juanmrq95/ee149_104/ASLsensing/longFlex/save_sensordata/test 1.1/testAashykLetterF.txt

ÿr_side 0   m_tip: 0   m_b: 0   m_side: 0   i_tip: 0   i_side: 0   p_side: 0thumb: 4   index: 0   middle: 2   ring: 1   pinky: 2 X: 359.86  Y: 1.56  Z: 359.08
r_side 0   m_tip: 0   m_b: 0   m_side: 0   i_tip: 0   i_side: 0   p_side: 0thumb: 4   index: 0   middle: 2   ring: 2   pinky: 2 X: 359.80  Y: 2.21  Z: 356.90
r_side 0   m_tip: 0   m_b: 0   m_side: 0   i_tip: 0   i_side: 0   p_side: 0thumb: 4   index: 1   middle: 1   ring: 1   pinky: 2 X: 359.91  Y: 2.89  Z: 354.72
r_side 0   m_tip: 0   m_b: 0   m_side: 0   i_tip: 0   i_side: 0   p_side: 0thumb: 4   index: 0   middle: 2   ring: 2   pinky: 2 X: 359.77  Y: 3.84  Z: 352.84
r_side 0   m_tip: 0   m_b: 0   m_side: 0   i_tip: 0   i_side: 0   p_side: 0thumb: 5   index: 0   middle: 2   ring: 2   pinky: 2 X: 359.57  Y: 4.64  Z: 351.21
r_side 0   m_tip: 0   m_b: 0   m_side: 0   i_tip: 0   i_side: 0   p_side: 0thumb: 4   index: 1   middle: 2   ring: 1   pinky: 2 X: 359.48  Y: 5.23  Z: 349.58
r_side 0   m_tip: 0   m_b: 0   m_side: 0   i_tip: 0   i_side: 0   p_side: 0thumb: 4   index: 0   middle: 2   ring: 1   pinky: 2 X: 359.42  Y: 5.63  Z: 347.90
r_side 0   m_tip: 0   m_b: 0   m_side: 0   i_tip: 0   i_side: 0   p_side: 0thumb: 4   index: 0   middle: 2   ring: 1   pinky: 2 X: 359.13  Y: 6.56  Z: 346.26
r_side 0   m_tip: 0   m_b: 0   m_side: 0   i_tip: 0   i_side: 0   p_side: 0thumb: 5   index: 1   middle: 1   ring: 2   pinky: 2 X: 358.89  Y: 7.36  Z: 345.13
r_side 0   m_tip: 0   m_b: 0   m_side: 0   i_tip: 0   i_side: 0   p_side: 0thumb: 4   index: 0   middle: 2   ring: 1   pinky: 2 X: 358.83  Y: 7.89  Z: 343.63
r_side 0   m_tip: 0   m_b: 0   m_side: 0   i_tip: 0   i_side: 0   p_side: 0thumb: 5   index: 1   middle: 2   ring: 2   pinky: 2 X: 358.70  Y: 8.17  Z: 342.31
r_side 0   m_tip: 0   m_b: 0   m_side: 0   i_tip: 0   i_side: 0   p_side: 0thumb: 5   index: 1   middle: 2   ring: 1   pinky: 2 X: 358.71  Y: 8.30  Z: 341.29
r_side 0   m_tip: 0   m_b: 0   m_side: 0   i_tip: 0   i_side: 0   p_side: 0thumb: 4   index: 0   middle: 2   ring: 2   pinky: 2 X: 358.53  Y: 8.83  Z: 340.26
r_side 0   m_tip: 0   m_b: 0   m_side: 0   i_tip: 0   i_side: 0   p_side: 0thumb: 4   index: 0   middle: 2   ring: 1   pinky: 2 X: 358.38  Y: 9.08  Z: 339.26
r_side 0   m_tip: 0   m_b: 0   m_side: 0   i_tip: 0   i_side: 0   p_side: 0thumb: 4   index: 0   middle: 2   ring: 1   pinky: 1 X: 358.16  Y: 9.81  Z: 338.84
r_side 0   m_tip: 0   m_b: 0   m_side: 0   i_tip: 0   i_side: 0   p_side: 0thumb: 4   index: 1   middle: 2   ring: 1   pinky: 2 X: 357.87  Y: 10.62  Z: 338.17
r_side 0   m_tip: 0   m_b: 0   m_side: 0   i_tip: 0   i_side: 0   p_side: 0thumb: 4   index: 1   middle: 2   ring: 2   pinky: 2 X: 357.73  Y: 10.57  Z: 337.49
r_side 0   m_tip: 0   m_b: 0   m_side: 0   i_tip: 0   i_side: 0   p_side: 0thumb: 4   index: 0   middle: 2   ring: 1   pinky: 2 X: 357.51  Y: 10.94  Z: 337.09
r_side 0   m_tip: 0   m_b: 0   m_side: 0   i_tip: 0   i_side: 0   p_side: 0thumb: 5   index: 0   middle: 2   ring: 2   pinky: 2 X: 357.28  Y: 11.17  Z: 336.52
r_side 0   m_tip: 0   m_b: 0   m_side: 0   i_tip: 0   i_side: 0   p_side: 0thumb: 4   index: 0   middle: 2   ring: 2   pinky: 2 X: 357.27  Y: 11.25  Z: 335.93
r_side 0   m_tip: 0   m_b: 0   m_side: 0   i_tip: 0   i_side: 0   p_side: 0thumb: 4   index: 1   middle: 2   ring: 2   pinky: 2 X: 356.90  Y: 11.51  Z: 328.52
r_side 0   m_tip: 0   m_b: 0   m_side: 0   i_tip: 0   i_side: 0   p_side: 0thumb: 5   index: 1   middle: 2   ring: 2   pinky: 2 X: 355.02  Y: 19.53  Z: 329.30
r_side 0   m_tip: 0   m_b: 0   m_side: 0   i_tip: 0   i_side: 0   p_side: 0thumb: 4   index: 11   middle: 2   ring: 3   pinky: 2 X: 349.70  Y: 37.47  Z: 325.18
r_side 0   m_tip: 0   m_b: 0   m_side: 0   i_tip: 0   i_side: 0   p_side: 0thumb: 4   index: 15   middle: 3   ring: 3   pinky: 2 X: 342.33  Y: 48.81  Z: 319.32
r_side 0   m_tip: 0   m_b: 0   m_side: 0   i_tip: 0   i_side: 0   p_side: 0thumb: 5   index: 17   middle: 5   ring: 3   pinky: 2 X: 330.57  Y: 53.66  Z: 309.83
r_side 0   m_tip: 0   m_b: 0   m_side: 0   i_tip: 0   i_side: 0   p_side: 0thumb: 9   index: 17   middle: 6   ring: 3   pinky: 2 X: 324.71  Y: 56.98  Z: 305.13
r_side 0   m_tip: 0   m_b: 0   m_side: 0   i_tip: 0   i_side: 0   p_side: 0thumb: 12   index: 17   middle: 5   ring: 3   pinky: 1 X: 307.50  Y: 58.89  Z: 292.51
r_side 0   m_tip: 0   m_b: 0   m_side: 0   i_tip: 0   i_side: 0   p_side: 0thumb: 13   index: 17   middle: 3   ring: 2   pinky: 2 X: 304.84  Y: 59.09  Z: 291.02
r_side 0   m_tip: 0   m_b: 0   m_side: 0   i_tip: 0   i_side: 0   p_side: 0thumb: 13   index: 17   middle: 3   ring: 2   pinky: 1 X: 300.77  Y: 59.29  Z: 287.74
r_side 0   m_tip: 0   m_b: 0   m_side: 0   i_tip: 0   i_side: 0   p_side: 0thumb: 13   index: 17   middle: 3   ring: 2   pinky: 1 X: 296.96  Y: 59.40  Z: 285.31
r_side 0   m_tip: 0   m_b: 0   m_side: 0   i_tip: 0   i_side: 0   p_side: 0thumb: 13   index: 16   middle: 3   ring: 2   pinky: 1 X: 294.84  Y: 59.29  Z: 284.20
r_side 0   m_tip: 0   m_b: 0   m_side: 0   i_tip: 0   i_side: 0   p_side: 0thumb: 13   index: 16   middle: 3   ring: 2   pinky: 1 X: 297.70  Y: 60.33  Z: 287.13
r_side 0   m_tip: 0   m_b: 0   m_side: 0   i_tip: 0   i_side: 0   p_side: 0thumb: 13   index: 16   middle: 3   ring: 2   pinky: 1 X: 296.87  Y: 60.51  Z: 286.03
r_side 0   m_tip: 0   m_b: 0   m_side: 0   i_tip: 0   i_side: 0   p_side: 0thumb: 14   index: 16   middle: 2   ring: 2   pinky: 1 X: 298.05  Y: 60.01  Z: 287.22
r_side 0   m_tip: 0   m_b: 0   m_side: 0   i_tip: 0   i_side: 0   p_side: 0thumb: 13   index: 16   middle: 2   ring: 2   pinky: 1 X: 299.49  Y: 59.68  Z: 289.05
r_side 0   m_tip: 0   m_b: 0   m_side: 0   i_tip: 0   i_side: 0   p_side: 0thumb: 13   index: 16   middle: 3   ring: 2   pinky: 1 X: 300.21  Y: 59.00  Z: 289.37
r_side 0   m_tip: 0   m_b: 0   m_side: 0   i_tip: 0   i_side: 0   p_side: 0thumb: 13   index: 17   middle: 2   ring: 2   pinky: 1 X: 299.08  Y: 58.88  Z: 288.23
r_side 0   m_tip: 0   m_b: 0   m_side: 0   i_tip: 0   i_side: 0   p_side: 0thumb: 12   index: 15   middle: 2   ring: 2   pinky: 1 X: 298.16  Y: 58.42  Z: 287.07
r_side 0   m_tip: 0   m_b: 0   m_side: 0   i_tip: 1   i_side: 0   p_side: 0thumb: 12   index: 15   middle: 2   ring: 2   pinky: 1 X: 299.49  Y: 58.04  Z: 288.58
r_side 0   m_tip: 0   m_b: 0   m_side: 1   i_tip: 1   i_side: 0   p_side: 0thumb: 12   index: 15   middle: 2   ring: 3   pinky: 1 X: 300.17  Y: 56.76  Z: 289.16
r_side 0   m_tip: 0   m_b: 0   m_side: 1   i_tip: 1   i_side: 0   p_side: 0thumb: 12   index: 15   middle: 2   ring: 2   pinky: 1 X: 301.12  Y: 56.71  Z: 290.41
r_side 0   m_tip: 0   m_b: 0   m_side: 1   i_tip: 1   i_side: 0   p_side: 0thumb: 12   index: 15   middle: 2   ring: 3   pinky: 1 X: 300.59  Y: 56.21  Z: 289.94
r_side 0   m_tip: 0   m_b: 0   m_side: 1   i_tip: 1   i_side: 0   p_side: 0thumb: 12   index: 15   middle: 2   ring: 2   pinky: 1 X: 299.94  Y: 55.90  Z: 289.20
r_side 0   m_tip: 0   m_b: 0   m_side: 1   i_tip: 1   i_side: 0   p_side: 0thumb: 12   index: 15   middle: 2   ring: 2   pinky: 1 X: 299.15  Y: 55.63  Z: 288.76
r_side 0   m_tip: 0   m_b: 0   m_side: 1   i_tip: 1   i_side: 0   p_side: 0thumb: 12   index: 15   middle: 2   ring: 2   pinky: 1 X: 297.92  Y: 55.63  Z: 287.64
r_side 0   m_tip: 0   m_b: 0   m_side: 1   i_tip: 1   i_side: 0   p_side: 0thumb: 11   index: 15   middle: 2   ring: 2   pinky: 1 X: 298.07  Y: 54.77  Z: 287.32
r_side 0   m_tip: 0   m_b: 0   m_side: 1   i_tip: 1   i_side: 0   p_side: 0thumb: 12   index: 15   middle: 2   ring: 2   pinky: 1 X: 298.51  Y: 53.80  Z: 287.42
r_side 0   m_tip: 0   m_b: 0   m_side: 1   i_tip: 1   i_side: 0   p_side: 0thumb: 11   index: 15   middle: 2   ring: 2   pinky: 2 X: 298.68  Y: 53.05  Z: 287.82
r_side 0   m_tip: 0   m_b: 0   m_side: 1   i_tip: 1   i_side: 0   p_side: 0thumb: 12   index: 15   middle: 2   ring: 2   pinky: 1 X: 299.35  Y: 52.70  Z: 288.68
r_side 0   m_tip: 0   m_b: 0   m_side: 1   i_tip: 1   i_side: 0   p_side: 0thumb: 11   index: 15   middle: 2   ring: 2   pinky: 1 X: 298.26  Y: 52.58  Z: 287.90
r_side 0   m_tip: 0   m_b: 0   m_side: 1   i_tip: 1   i_side: 0   p_side: 0thumb: 12   index: 15   middle: 2   ring: 2   pinky: 1 X: 298.87  Y: 51.74  Z: 288.30
r_side 0   m_tip: 0   m_b: 0   m_side: 1   i_tip: 1   i_side: 0   p_side: 0thumb: 12   index: 15   middle: 2   ring: 2   pinky: 1 X: 298.92  Y: 51.02  Z: 288.29
r_side 0   m_tip: 0   m_b: 0   m_side: 1   i_tip: 1   i_side: 0   p_side: 0thumb: 11   index: 15   middle: 2   ring: 2   pinky: 1 X: 300.51  Y: 50.00  Z: 289.78
r_side 0   m_tip: 0   m_b: 0   m_side: 1   i_tip: 1   i_side: 0   p_side: 0thumb: 11   index: 14   middle: 2   ring: 2   pinky: 1 X: 299.64  Y: 49.93  Z: 289.33
r_side 0   m_tip: 0   m_b: 0   m_side: 1   i_tip: 1   i_side: 0   p_side: 0thumb: 11   index: 14   middle: 2   ring: 2   pinky: 2 X: 299.54  Y: 49.94  Z: 289.10
r_side 0   m_tip: 0   m_b: 0   m_side: 1   i_tip: 1   i_side: 0   p_side: 0thumb: 11   index: 14   middle: 2   ring: 2   pinky: 1 X: 299.70  Y: 49.47  Z: 289.38
r_side 0   m_tip: 0   m_b: 0   m_side: 1   i_tip: 1   i_side: 0   p_side: 0thumb: 12   index: 14   middle: 2   ring: 2   pinky: 1 X: 299.32  Y: 48.52  Z: 288.76
r_side 0   m_tip: 0   m_b: 0   m_side: 1   i_tip: 1   i_side: 0   p_side: 0thumb: 11   index: 14   middle: 2   ring: 2   pinky: 1 X: 300.05  Y: 47.78  Z: 289.49
r_side 0   m_tip: 0   m_b: 0   m_side: 1   i_tip: 1   i_side: 0   p_side: 0thumb: 11   index: 15   middle: 2   ring: 2   pinky: 1 X: 299.90  Y: 47.40  Z: 289.54
r_side 0   m_tip: 0   m_b: 0   m_side: 1   i_tip: 1   i_side: 0   p_side: 0thumb: 11   index: 15   middle: 2   ring: 2   pinky: 1 X: 298.75  Y: 47.26  Z: 288.29
r_side 0   m_tip: 0   m_b: 0   m_side: 1   i_tip: 1   i_side: 0   p_side: 0thumb: 11   index: 14   middle: 2   ring: 2   pinky: 1 X: 297.88  Y: 46.88  Z: 287.56
r_side 0   m_tip: 0   m_b: 0   m_side: 1   i_tip: 1   i_side: 0   p_side: 0thumb: 11   index: 12   middle: 2   ring: 2   pinky: 1 X: 297.51  Y: 46.70  Z: 287.17
r_side 0   m_tip: 0   m_b: 0   m_side: 1   i_tip: 1   i_side: 0   p_side: 0thumb: 11   index: 14   middle: 2   ring: 2   pinky: 1 X: 296.88  Y: 46.60  Z: 286.61
r_side 0   m_tip: 0   m_b: 0   m_side: 1   i_tip: 1   i_side: 0   p_side: 0thumb: 11   index: 14   middle: 2   ring: 2   pinky: 1 X: 295.59  Y: 46.58  Z: 285.90
r_side 0   m_tip: 0   m_b: 0   m_side: 1   i_tip: 1   i_side: 0   p_side: 0thumb: 11   index: 14   middle: 2   ring: 2   pinky: 1 X: 296.79  Y: 46.54  Z: 286.98
r_side 0   m_tip: 0   m_b: 0   m_side: 1   i_tip: 1   i_side: 0   p_side: 0thumb: 11   index: 14   middle: 2   ring: 2   pinky: 1 X: 297.42  Y: 46.25  Z: 287.56
r_side 0   m_tip: 0   m_b: 0   m_side: 1   i_tip: 1   i_side: 0   p_side: 0thumb: 11   index: 14   middle: 2   ring: 2   pinky: 1 X: 297.86  Y: 45.92  Z: 287.97
r_side 0   m_tip: 0   m_b: 0   m_side: 1   i_tip: 1   i_side: 0   p_side: 0thumb: 11   index: 14   middle: 2   ring: 2   pinky: 1 X: 298.05  Y: 45.55  Z: 288.15
r_side 0   m_tip: 0   m_b: 0   m_side: 1   i_tip: 1   i_side: 0   p_side: 0thumb: 11   index: 14   middle: 2   ring: 2   pinky: 1 X: 298.62  Y: 44.94  Z: 288.62
