juanmrq95/ee149_104/ASLsensing/longFlex/save_sensordata/test 1.1/testAashykLetterG.txt

ôr_side 0   m_tip: 0   m_b: 0   m_side: 0   i_tip: 0   i_side: 0   p_side: 0thumb: 5   index: 1   middle: 2   ring: 2   pinky: 2 X: 359.86  Y: 1.04  Z: 359.47
r_side 0   m_tip: 0   m_b: 0   m_side: 0   i_tip: 0   i_side: 0   p_side: 0thumb: 4   index: 1   middle: 3   ring: 2   pinky: 2 X: 359.98  Y: 2.26  Z: 356.93
r_side 0   m_tip: 0   m_b: 0   m_side: 0   i_tip: 0   i_side: 0   p_side: 0thumb: 6   index: 1   middle: 2   ring: 2   pinky: 2 X: 359.90  Y: 3.79  Z: 354.77
r_side 0   m_tip: 0   m_b: 0   m_side: 0   i_tip: 0   i_side: 0   p_side: 0thumb: 5   index: 1   middle: 2   ring: 2   pinky: 2 X: 359.68  Y: 5.32  Z: 352.94
r_side 0   m_tip: 0   m_b: 0   m_side: 0   i_tip: 0   i_side: 0   p_side: 0thumb: 5   index: 1   middle: 2   ring: 2   pinky: 2 X: 359.40  Y: 6.60  Z: 351.04
r_side 0   m_tip: 0   m_b: 0   m_side: 0   i_tip: 0   i_side: 0   p_side: 0thumb: 5   index: 1   middle: 3   ring: 2   pinky: 2 X: 359.09  Y: 7.69  Z: 349.23
r_side 0   m_tip: 0   m_b: 0   m_side: 0   i_tip: 0   i_side: 0   p_side: 0thumb: 5   index: 1   middle: 2   ring: 2   pinky: 2 X: 358.81  Y: 9.04  Z: 347.66
r_side 0   m_tip: 0   m_b: 0   m_side: 0   i_tip: 0   i_side: 0   p_side: 0thumb: 5   index: 1   middle: 2   ring: 2   pinky: 2 X: 358.50  Y: 10.26  Z: 345.89
r_side 0   m_tip: 0   m_b: 0   m_side: 0   i_tip: 0   i_side: 0   p_side: 0thumb: 5   index: 1   middle: 2   ring: 2   pinky: 2 X: 358.17  Y: 11.07  Z: 344.23
r_side 0   m_tip: 0   m_b: 0   m_side: 0   i_tip: 0   i_side: 0   p_side: 0thumb: 5   index: 1   middle: 2   ring: 2   pinky: 2 X: 357.83  Y: 12.02  Z: 342.65
r_side 0   m_tip: 0   m_b: 0   m_side: 0   i_tip: 0   i_side: 0   p_side: 0thumb: 5   index: 1   middle: 3   ring: 2   pinky: 2 X: 357.34  Y: 12.48  Z: 341.30
r_side 0   m_tip: 0   m_b: 0   m_side: 0   i_tip: 0   i_side: 0   p_side: 0thumb: 4   index: 1   middle: 2   ring: 2   pinky: 2 X: 357.13  Y: 13.51  Z: 339.95
r_side 0   m_tip: 0   m_b: 0   m_side: 0   i_tip: 0   i_side: 0   p_side: 0thumb: 5   index: 1   middle: 2   ring: 2   pinky: 2 X: 356.93  Y: 13.75  Z: 338.81
r_side 0   m_tip: 0   m_b: 0   m_side: 0   i_tip: 0   i_side: 0   p_side: 0thumb: 5   index: 1   middle: 2   ring: 2   pinky: 2 X: 354.07  Y: 15.34  Z: 328.92
r_side 0   m_tip: 0   m_b: 0   m_side: 0   i_tip: 0   i_side: 0   p_side: 0thumb: 5   index: 1   middle: 3   ring: 3   pinky: 2 X: 340.19  Y: 18.18  Z: 311.25
r_side 0   m_tip: 0   m_b: 0   m_side: 0   i_tip: 0   i_side: 0   p_side: 0thumb: 4   index: 2   middle: 10   ring: 10   pinky: 3 X: 324.12  Y: 7.15  Z: 287.70
r_side 0   m_tip: 0   m_b: 0   m_side: 0   i_tip: 0   i_side: 0   p_side: 0thumb: 4   index: 2   middle: 16   ring: 19   pinky: 10 X: 326.61  Y: 352.52  Z: 270.03
r_side 0   m_tip: 0   m_b: 0   m_side: 0   i_tip: 0   i_side: 0   p_side: 0thumb: 4   index: 3   middle: 21   ring: 23   pinky: 20 X: 334.37  Y: 346.06  Z: 267.57
r_side 0   m_tip: 0   m_b: 0   m_side: 0   i_tip: 0   i_side: 0   p_side: 0thumb: 4   index: 9   middle: 20   ring: 22   pinky: 20 X: 336.39  Y: 333.75  Z: 259.16
r_side 0   m_tip: 1   m_b: 0   m_side: 0   i_tip: 0   i_side: 0   p_side: 0thumb: 5   index: 4   middle: 20   ring: 22   pinky: 20 X: 340.89  Y: 325.34  Z: 253.91
r_side 0   m_tip: 1   m_b: 0   m_side: 0   i_tip: 0   i_side: 0   p_side: 0thumb: 5   index: 3   middle: 20   ring: 22   pinky: 19 X: 352.90  Y: 323.82  Z: 236.03
r_side 0   m_tip: 1   m_b: 0   m_side: 0   i_tip: 0   i_side: 0   p_side: 0thumb: 5   index: 2   middle: 20   ring: 21   pinky: 19 X: 353.22  Y: 323.20  Z: 239.87
r_side 0   m_tip: 1   m_b: 0   m_side: 0   i_tip: 0   i_side: 0   p_side: 0thumb: 5   index: 2   middle: 19   ring: 21   pinky: 19 X: 351.07  Y: 327.64  Z: 246.00
r_side 0   m_tip: 1   m_b: 0   m_side: 0   i_tip: 0   i_side: 0   p_side: 0thumb: 5   index: 2   middle: 19   ring: 21   pinky: 18 X: 349.36  Y: 330.85  Z: 250.28
r_side 0   m_tip: 1   m_b: 0   m_side: 0   i_tip: 0   i_side: 0   p_side: 0thumb: 5   index: 2   middle: 19   ring: 21   pinky: 18 X: 351.55  Y: 330.85  Z: 248.05
r_side 0   m_tip: 1   m_b: 0   m_side: 0   i_tip: 0   i_side: 0   p_side: 0thumb: 4   index: 1   middle: 19   ring: 21   pinky: 18 X: 352.31  Y: 329.45  Z: 247.53
r_side 0   m_tip: 1   m_b: 0   m_side: 0   i_tip: 0   i_side: 0   p_side: 0thumb: 4   index: 1   middle: 19   ring: 21   pinky: 18 X: 353.84  Y: 329.83  Z: 244.71
r_side 0   m_tip: 1   m_b: 0   m_side: 0   i_tip: 0   i_side: 0   p_side: 0thumb: 4   index: 1   middle: 18   ring: 21   pinky: 18 X: 353.63  Y: 328.74  Z: 246.48
r_side 0   m_tip: 1   m_b: 0   m_side: 0   i_tip: 0   i_side: 0   p_side: 0thumb: 4   index: 1   middle: 19   ring: 20   pinky: 18 X: 353.61  Y: 329.88  Z: 245.12
r_side 0   m_tip: 1   m_b: 0   m_side: 0   i_tip: 0   i_side: 0   p_side: 0thumb: 5   index: 0   middle: 18   ring: 20   pinky: 18 X: 353.72  Y: 329.08  Z: 246.32
r_side 0   m_tip: 1   m_b: 0   m_side: 0   i_tip: 0   i_side: 0   p_side: 0thumb: 4   index: 1   middle: 18   ring: 20   pinky: 18 X: 353.32  Y: 329.97  Z: 246.20
r_side 0   m_tip: 1   m_b: 0   m_side: 0   i_tip: 0   i_side: 0   p_side: 0thumb: 4   index: 1   middle: 18   ring: 20   pinky: 18 X: 353.13  Y: 328.50  Z: 247.85
r_side 0   m_tip: 1   m_b: 0   m_side: 0   i_tip: 0   i_side: 0   p_side: 0thumb: 4   index: 1   middle: 18   ring: 19   pinky: 18 X: 353.42  Y: 329.00  Z: 247.76
r_side 0   m_tip: 1   m_b: 0   m_side: 0   i_tip: 0   i_side: 0   p_side: 0thumb: 4   index: 1   middle: 18   ring: 20   pinky: 18 X: 353.89  Y: 328.97  Z: 247.76
r_side 0   m_tip: 1   m_b: 0   m_side: 0   i_tip: 0   i_side: 0   p_side: 0thumb: 4   index: 1   middle: 18   ring: 20   pinky: 18 X: 353.51  Y: 329.65  Z: 247.14
r_side 0   m_tip: 1   m_b: 0   m_side: 0   i_tip: 0   i_side: 0   p_side: 0thumb: 4   index: 1   middle: 18   ring: 20   pinky: 18 X: 353.29  Y: 328.72  Z: 248.12
r_side 0   m_tip: 1   m_b: 0   m_side: 0   i_tip: 0   i_side: 0   p_side: 0thumb: 4   index: 1   middle: 18   ring: 19   pinky: 18 X: 353.93  Y: 327.08  Z: 247.85
r_side 0   m_tip: 1   m_b: 0   m_side: 0   i_tip: 0   i_side: 0   p_side: 0thumb: 4   index: 1   middle: 18   ring: 20   pinky: 18 X: 353.44  Y: 326.59  Z: 249.26
r_side 0   m_tip: 1   m_b: 0   m_side: 0   i_tip: 0   i_side: 0   p_side: 0thumb: 4   index: 1   middle: 18   ring: 20   pinky: 18 X: 352.77  Y: 326.28  Z: 249.98
r_side 0   m_tip: 1   m_b: 0   m_side: 0   i_tip: 0   i_side: 0   p_side: 0thumb: 4   index: 1   middle: 18   ring: 20   pinky: 18 X: 352.56  Y: 326.93  Z: 249.52
r_side 0   m_tip: 1   m_b: 0   m_side: 0   i_tip: 0   i_side: 0   p_side: 0thumb: 3   index: 1   middle: 18   ring: 20   pinky: 18 X: 352.37  Y: 327.42  Z: 249.82
r_side 0   m_tip: 1   m_b: 0   m_side: 0   i_tip: 0   i_side: 0   p_side: 0thumb: 3   index: 1   middle: 18   ring: 20   pinky: 18 X: 352.23  Y: 327.50  Z: 250.27
r_side 0   m_tip: 1   m_b: 0   m_side: 0   i_tip: 0   i_side: 0   p_side: 0thumb: 3   index: 1   middle: 18   ring: 19   pinky: 18 X: 351.75  Y: 327.09  Z: 251.46
r_side 0   m_tip: 1   m_b: 0   m_side: 0   i_tip: 0   i_side: 0   p_side: 0thumb: 4   index: 1   middle: 18   ring: 20   pinky: 18 X: 351.92  Y: 327.97  Z: 250.81
r_side 0   m_tip: 1   m_b: 0   m_side: 0   i_tip: 0   i_side: 0   p_side: 0thumb: 3   index: 1   middle: 18   ring: 19   pinky: 17 X: 351.40  Y: 328.25  Z: 251.43
r_side 0   m_tip: 1   m_b: 0   m_side: 0   i_tip: 0   i_side: 0   p_side: 0thumb: 4   index: 1   middle: 18   ring: 20   pinky: 17 X: 351.45  Y: 327.87  Z: 251.77
r_side 0   m_tip: 1   m_b: 0   m_side: 0   i_tip: 0   i_side: 0   p_side: 0thumb: 4   index: 1   middle: 18   ring: 19   pinky: 17 X: 351.03  Y: 330.11  Z: 250.76
r_side 0   m_tip: 1   m_b: 0   m_side: 0   i_tip: 0   i_side: 0   p_side: 0thumb: 4   index: 1   middle: 18   ring: 19   pinky: 17 X: 351.12  Y: 325.59  Z: 252.97
r_side 0   m_tip: 1   m_b: 0   m_side: 0   i_tip: 0   i_side: 0   p_side: 0thumb: 3   index: 1   middle: 17   ring: 19   pinky: 17 X: 350.68  Y: 327.83  Z: 251.43
r_side 0   m_tip: 1   m_b: 0   m_side: 0   i_tip: 0   i_side: 0   p_side: 0thumb: 3   index: 1   middle: 18   ring: 19   pinky: 17 X: 350.75  Y: 326.18  Z: 252.53
r_side 0   m_tip: 1   m_b: 0   m_side: 0   i_tip: 0   i_side: 0   p_side: 0thumb: 3   index: 1   middle: 18   ring: 19   pinky: 18 X: 350.50  Y: 328.37  Z: 251.83
r_side 0   m_tip: 1   m_b: 0   m_side: 0   i_tip: 0   i_side: 0   p_side: 0thumb: 3   index: 1   middle: 18   ring: 19   pinky: 17 X: 350.89  Y: 327.90  Z: 252.03
r_side 0   m_tip: 1   m_b: 0   m_side: 0   i_tip: 0   i_side: 0   p_side: 0thumb: 4   index: 1   middle: 18   ring: 19   pinky: 17 X: 351.32  Y: 328.90  Z: 251.54
r_side 0   m_tip: 1   m_b: 0   m_side: 0   i_tip: 0   i_side: 0   p_side: 0thumb: 4   index: 2   middle: 18   ring: 19   pinky: 18 X: 350.45  Y: 329.97  Z: 251.80
r_side 0   m_tip: 1   m_b: 0   m_side: 0   i_tip: 0   i_side: 0   p_side: 0thumb: 3   index: 1   middle: 18   ring: 19   pinky: 17 X: 349.84  Y: 329.50  Z: 252.70
r_side 0   m_tip: 1   m_b: 0   m_side: 0   i_tip: 0   i_side: 0   p_side: 0thumb: 3   index: 1   middle: 18   ring: 19   pinky: 17 X: 349.80  Y: 329.93  Z: 252.40
r_side 0   m_tip: 1   m_b: 0   m_side: 0   i_tip: 0   i_side: 0   p_side: 0thumb: 3   index: 1   middle: 17   ring: 19   pinky: 17 X: 350.59  Y: 331.42  Z: 251.13
r_side 0   m_tip: 1   m_b: 0   m_side: 0   i_tip: 0   i_side: 0   p_side: 0thumb: 3   index: 1   middle: 18   ring: 19   pinky: 17 X: 350.34  Y: 331.67  Z: 251.18
r_side 0   m_tip: 1   m_b: 0   m_side: 0   i_tip: 0   i_side: 0   p_side: 0thumb: 3   index: 1   middle: 17   ring: 19   pinky: 17 X: 350.53  Y: 331.07  Z: 251.28
r_side 0   m_tip: 1   m_b: 0   m_side: 0   i_tip: 0   i_side: 0   p_side: 0thumb: 3   index: 1   middle: 17   ring: 19   pinky: 17 X: 349.86  Y: 331.18  Z: 251.82
r_side 0   m_tip: 1   m_b: 0   m_side: 0   i_tip: 0   i_side: 0   p_side: 0thumb: 3   index: 1   middle: 17   ring: 19   pinky: 17 X: 350.06  Y: 331.67  Z: 252.02
r_side 0   m_tip: 1   m_b: 0   m_side: 0   i_tip: 0   i_side: 0   p_side: 0thumb: 3   index: 1   middle: 17   ring: 19   pinky: 17 X: 350.19  Y: 331.96  Z: 252.10
