juanmrq95/ee149_104/ASLsensing/longFlex/save_sensordata/test 1.1/testAashykLetterH.txt

r_side 0   m_tip: 0   m_b: 0   m_side: 0   i_tip: 0   i_side: 0   p_side: 0thumb: 5   index: 1   middle: 2   ring: 2   pinky: 1 X: 359.61  Y: 0.91  Z: 359.87
r_side 0   m_tip: 0   m_b: 0   m_side: 0   i_tip: 0   i_side: 0   p_side: 0thumb: 5   index: 0   middle: 2   ring: 2   pinky: 1 X: 359.52  Y: 2.20  Z: 357.54
r_side 0   m_tip: 0   m_b: 0   m_side: 0   i_tip: 0   i_side: 0   p_side: 0thumb: 5   index: 0   middle: 2   ring: 2   pinky: 1 X: 359.45  Y: 3.42  Z: 355.15
r_side 0   m_tip: 0   m_b: 0   m_side: 0   i_tip: 0   i_side: 0   p_side: 0thumb: 5   index: 0   middle: 2   ring: 2   pinky: 1 X: 359.31  Y: 4.42  Z: 353.01
r_side 0   m_tip: 0   m_b: 0   m_side: 0   i_tip: 0   i_side: 0   p_side: 0thumb: 5   index: 0   middle: 2   ring: 2   pinky: 1 X: 359.24  Y: 5.20  Z: 350.74
r_side 0   m_tip: 0   m_b: 0   m_side: 0   i_tip: 0   i_side: 0   p_side: 0thumb: 5   index: 0   middle: 2   ring: 2   pinky: 1 X: 359.08  Y: 5.83  Z: 348.63
r_side 0   m_tip: 0   m_b: 0   m_side: 0   i_tip: 0   i_side: 0   p_side: 0thumb: 5   index: 0   middle: 1   ring: 2   pinky: 1 X: 358.90  Y: 6.77  Z: 346.83
r_side 0   m_tip: 0   m_b: 0   m_side: 0   i_tip: 0   i_side: 0   p_side: 0thumb: 5   index: 0   middle: 2   ring: 2   pinky: 2 X: 358.75  Y: 7.52  Z: 345.24
r_side 0   m_tip: 0   m_b: 0   m_side: 0   i_tip: 0   i_side: 0   p_side: 0thumb: 5   index: 0   middle: 2   ring: 2   pinky: 1 X: 358.59  Y: 8.00  Z: 343.64
r_side 0   m_tip: 0   m_b: 0   m_side: 0   i_tip: 0   i_side: 0   p_side: 0thumb: 5   index: 0   middle: 1   ring: 2   pinky: 1 X: 358.32  Y: 8.89  Z: 342.03
r_side 0   m_tip: 0   m_b: 0   m_side: 0   i_tip: 0   i_side: 0   p_side: 0thumb: 5   index: 0   middle: 2   ring: 2   pinky: 1 X: 358.12  Y: 9.58  Z: 340.49
r_side 0   m_tip: 0   m_b: 0   m_side: 0   i_tip: 0   i_side: 0   p_side: 0thumb: 5   index: 0   middle: 2   ring: 2   pinky: 1 X: 357.85  Y: 10.39  Z: 339.44
r_side 0   m_tip: 0   m_b: 0   m_side: 0   i_tip: 0   i_side: 0   p_side: 0thumb: 5   index: 0   middle: 2   ring: 2   pinky: 1 X: 357.70  Y: 10.68  Z: 338.24
r_side 0   m_tip: 0   m_b: 0   m_side: 0   i_tip: 0   i_side: 0   p_side: 0thumb: 5   index: 0   middle: 2   ring: 2   pinky: 1 X: 357.42  Y: 11.09  Z: 336.91
r_side 0   m_tip: 0   m_b: 0   m_side: 0   i_tip: 0   i_side: 0   p_side: 0thumb: 5   index: 0   middle: 2   ring: 2   pinky: 1 X: 357.15  Y: 11.62  Z: 335.82
r_side 0   m_tip: 0   m_b: 0   m_side: 0   i_tip: 0   i_side: 0   p_side: 0thumb: 5   index: 1   middle: 2   ring: 2   pinky: 1 X: 356.95  Y: 12.16  Z: 335.06
r_side 0   m_tip: 0   m_b: 0   m_side: 0   i_tip: 0   i_side: 0   p_side: 0thumb: 6   index: 0   middle: 2   ring: 3   pinky: 1 X: 356.69  Y: 12.51  Z: 334.23
r_side 0   m_tip: 0   m_b: 0   m_side: 0   i_tip: 0   i_side: 0   p_side: 0thumb: 5   index: 0   middle: 2   ring: 2   pinky: 1 X: 356.33  Y: 12.72  Z: 333.30
r_side 0   m_tip: 0   m_b: 0   m_side: 0   i_tip: 0   i_side: 0   p_side: 0thumb: 5   index: 0   middle: 2   ring: 2   pinky: 1 X: 353.48  Y: 12.53  Z: 327.00
r_side 0   m_tip: 0   m_b: 0   m_side: 0   i_tip: 0   i_side: 0   p_side: 0thumb: 5   index: 0   middle: 2   ring: 2   pinky: 2 X: 351.48  Y: 16.66  Z: 324.09
r_side 0   m_tip: 0   m_b: 0   m_side: 0   i_tip: 0   i_side: 0   p_side: 0thumb: 5   index: 0   middle: 2   ring: 2   pinky: 2 X: 337.60  Y: 8.10  Z: 293.87
r_side 0   m_tip: 0   m_b: 0   m_side: 0   i_tip: 0   i_side: 0   p_side: 0thumb: 4   index: 0   middle: 2   ring: 19   pinky: 13 X: 330.20  Y: 358.47  Z: 283.63
r_side 0   m_tip: 0   m_b: 0   m_side: 0   i_tip: 0   i_side: 0   p_side: 0thumb: 6   index: 1   middle: 2   ring: 21   pinky: 17 X: 326.41  Y: 350.17  Z: 278.54
r_side 0   m_tip: 0   m_b: 0   m_side: 0   i_tip: 0   i_side: 0   p_side: 0thumb: 5   index: 1   middle: 2   ring: 20   pinky: 17 X: 331.76  Y: 335.70  Z: 258.45
r_side 1   m_tip: 0   m_b: 0   m_side: 0   i_tip: 0   i_side: 0   p_side: 0thumb: 11   index: 0   middle: 2   ring: 20   pinky: 17 X: 339.12  Y: 324.61  Z: 245.85
r_side 1   m_tip: 0   m_b: 0   m_side: 0   i_tip: 0   i_side: 0   p_side: 0thumb: 12   index: 0   middle: 2   ring: 20   pinky: 17 X: 351.06  Y: 316.14  Z: 234.50
r_side 1   m_tip: 0   m_b: 0   m_side: 0   i_tip: 0   i_side: 0   p_side: 0thumb: 13   index: 0   middle: 2   ring: 20   pinky: 16 X: 354.17  Y: 311.24  Z: 233.86
r_side 1   m_tip: 0   m_b: 0   m_side: 0   i_tip: 0   i_side: 0   p_side: 0thumb: 13   index: 0   middle: 2   ring: 19   pinky: 16 X: 357.57  Y: 309.67  Z: 229.68
r_side 1   m_tip: 0   m_b: 0   m_side: 0   i_tip: 0   i_side: 0   p_side: 0thumb: 12   index: 0   middle: 2   ring: 20   pinky: 16 X: 0.75  Y: 307.02  Z: 227.85
r_side 1   m_tip: 0   m_b: 0   m_side: 0   i_tip: 0   i_side: 0   p_side: 0thumb: 13   index: 0   middle: 2   ring: 19   pinky: 16 X: 3.27  Y: 304.75  Z: 224.75
r_side 1   m_tip: 0   m_b: 0   m_side: 0   i_tip: 0   i_side: 0   p_side: 0thumb: 13   index: 0   middle: 2   ring: 19   pinky: 16 X: 3.76  Y: 303.31  Z: 226.28
r_side 1   m_tip: 0   m_b: 0   m_side: 0   i_tip: 0   i_side: 0   p_side: 0thumb: 13   index: 0   middle: 2   ring: 19   pinky: 16 X: 4.95  Y: 302.52  Z: 227.68
r_side 1   m_tip: 0   m_b: 0   m_side: 0   i_tip: 0   i_side: 0   p_side: 0thumb: 13   index: 0   middle: 2   ring: 19   pinky: 15 X: 9.36  Y: 303.10  Z: 224.10
r_side 1   m_tip: 0   m_b: 0   m_side: 0   i_tip: 0   i_side: 0   p_side: 0thumb: 13   index: 0   middle: 2   ring: 18   pinky: 15 X: 9.58  Y: 302.12  Z: 226.31
r_side 1   m_tip: 0   m_b: 0   m_side: 0   i_tip: 0   i_side: 0   p_side: 0thumb: 13   index: 0   middle: 1   ring: 18   pinky: 15 X: 7.73  Y: 303.27  Z: 230.31
r_side 1   m_tip: 0   m_b: 0   m_side: 0   i_tip: 0   i_side: 0   p_side: 0thumb: 13   index: 0   middle: 2   ring: 18   pinky: 15 X: 8.31  Y: 303.31  Z: 230.46
r_side 1   m_tip: 0   m_b: 0   m_side: 0   i_tip: 0   i_side: 0   p_side: 0thumb: 13   index: 0   middle: 2   ring: 18   pinky: 15 X: 8.67  Y: 303.21  Z: 231.11
r_side 1   m_tip: 0   m_b: 0   m_side: 0   i_tip: 0   i_side: 0   p_side: 0thumb: 13   index: 0   middle: 2   ring: 18   pinky: 15 X: 8.46  Y: 303.59  Z: 231.74
r_side 1   m_tip: 0   m_b: 0   m_side: 0   i_tip: 0   i_side: 0   p_side: 0thumb: 13   index: 0   middle: 2   ring: 18   pinky: 15 X: 8.98  Y: 302.91  Z: 232.03
r_side 1   m_tip: 0   m_b: 0   m_side: 0   i_tip: 0   i_side: 0   p_side: 0thumb: 12   index: 0   middle: 2   ring: 18   pinky: 15 X: 8.52  Y: 303.66  Z: 232.65
r_side 1   m_tip: 0   m_b: 0   m_side: 0   i_tip: 0   i_side: 0   p_side: 0thumb: 13   index: 0   middle: 1   ring: 18   pinky: 15 X: 7.68  Y: 304.45  Z: 234.66
r_side 1   m_tip: 0   m_b: 0   m_side: 0   i_tip: 0   i_side: 0   p_side: 0thumb: 13   index: 0   middle: 2   ring: 18   pinky: 15 X: 8.40  Y: 304.49  Z: 234.31
r_side 1   m_tip: 0   m_b: 0   m_side: 0   i_tip: 0   i_side: 0   p_side: 0thumb: 13   index: 0   middle: 2   ring: 18   pinky: 15 X: 9.61  Y: 303.95  Z: 233.01
r_side 1   m_tip: 0   m_b: 0   m_side: 0   i_tip: 0   i_side: 0   p_side: 0thumb: 13   index: 0   middle: 2   ring: 19   pinky: 15 X: 10.67  Y: 303.90  Z: 232.21
r_side 1   m_tip: 0   m_b: 0   m_side: 0   i_tip: 0   i_side: 0   p_side: 0thumb: 13   index: 0   middle: 1   ring: 18   pinky: 15 X: 12.61  Y: 302.40  Z: 230.62
r_side 1   m_tip: 0   m_b: 0   m_side: 0   i_tip: 0   i_side: 0   p_side: 0thumb: 13   index: 0   middle: 1   ring: 18   pinky: 15 X: 13.66  Y: 302.94  Z: 229.32
r_side 1   m_tip: 0   m_b: 0   m_side: 0   i_tip: 0   i_side: 0   p_side: 0thumb: 12   index: 0   middle: 1   ring: 18   pinky: 15 X: 12.77  Y: 303.30  Z: 230.86
r_side 1   m_tip: 0   m_b: 0   m_side: 0   i_tip: 0   i_side: 0   p_side: 0thumb: 12   index: 0   middle: 1   ring: 18   pinky: 15 X: 12.94  Y: 303.14  Z: 231.32
r_side 1   m_tip: 0   m_b: 0   m_side: 0   i_tip: 0   i_side: 0   p_side: 0thumb: 13   index: 0   middle: 1   ring: 18   pinky: 15 X: 13.95  Y: 302.54  Z: 230.57
r_side 1   m_tip: 0   m_b: 0   m_side: 0   i_tip: 0   i_side: 0   p_side: 0thumb: 13   index: 0   middle: 2   ring: 17   pinky: 15 X: 17.71  Y: 301.47  Z: 227.56
r_side 1   m_tip: 0   m_b: 0   m_side: 0   i_tip: 0   i_side: 0   p_side: 0thumb: 13   index: 0   middle: 1   ring: 18   pinky: 15 X: 17.03  Y: 301.64  Z: 228.42
r_side 1   m_tip: 0   m_b: 0   m_side: 0   i_tip: 0   i_side: 0   p_side: 0thumb: 13   index: 0   middle: 1   ring: 18   pinky: 15 X: 16.25  Y: 302.06  Z: 229.40
r_side 1   m_tip: 0   m_b: 0   m_side: 0   i_tip: 0   i_side: 0   p_side: 0thumb: 13   index: 0   middle: 1   ring: 17   pinky: 15 X: 15.05  Y: 301.81  Z: 231.51
r_side 1   m_tip: 0   m_b: 0   m_side: 0   i_tip: 0   i_side: 0   p_side: 0thumb: 13   index: 0   middle: 2   ring: 18   pinky: 15 X: 15.76  Y: 301.42  Z: 231.24
r_side 1   m_tip: 0   m_b: 0   m_side: 0   i_tip: 0   i_side: 0   p_side: 0thumb: 12   index: 0   middle: 2   ring: 17   pinky: 15 X: 15.30  Y: 300.93  Z: 231.61
r_side 1   m_tip: 0   m_b: 0   m_side: 0   i_tip: 0   i_side: 0   p_side: 0thumb: 13   index: 0   middle: 1   ring: 17   pinky: 15 X: 15.30  Y: 301.40  Z: 231.43
r_side 1   m_tip: 0   m_b: 0   m_side: 0   i_tip: 0   i_side: 0   p_side: 0thumb: 12   index: 0   middle: 1   ring: 17   pinky: 14 X: 15.60  Y: 301.23  Z: 230.61
r_side 1   m_tip: 0   m_b: 0   m_side: 0   i_tip: 0   i_side: 0   p_side: 0thumb: 13   index: 0   middle: 1   ring: 17   pinky: 15 X: 14.36  Y: 301.95  Z: 231.98
r_side 1   m_tip: 0   m_b: 0   m_side: 0   i_tip: 0   i_side: 0   p_side: 0thumb: 12   index: 0   middle: 1   ring: 18   pinky: 14 X: 13.80  Y: 301.75  Z: 232.52
r_side 1   m_tip: 0   m_b: 0   m_side: 0   i_tip: 0   i_side: 0   p_side: 0thumb: 12   index: 0   middle: 1   ring: 17   pinky: 14 X: 14.27  Y: 300.83  Z: 232.10
r_side 1   m_tip: 0   m_b: 0   m_side: 0   i_tip: 0   i_side: 0   p_side: 0thumb: 12   index: 0   middle: 1   ring: 17   pinky: 14 X: 15.16  Y: 300.70  Z: 230.65
r_side 1   m_tip: 0   m_b: 0   m_side: 0   i_tip: 0   i_side: 0   p_side: 0thumb: 12   index: 0   middle: 1   ring: 17   pinky: 14 X: 14.61  Y: 300.47  Z: 231.02
r_side 1   m_tip: 0   m_b: 0   m_side: 0   i_tip: 0   i_side: 0   p_side: 0thumb: 12   index: 0   middle: 1   ring: 17   pinky: 15 X: 14.10  Y: 300.50  Z: 231.90
r_side 1   m_tip: 0   m_b: 0   m_side: 0   i_tip: 0   i_side: 0   p_side: 0thumb: 14   index: 0   middle: 2   ring: 17   pinky: 14 X: 13.44  Y: 300.11  Z: 232.69
r_side 1   m_tip: 0   m_b: 0   m_side: 0   i_tip: 0   i_side: 0   p_side: 0thumb: 12   index: 0   middle: 1   ring: 17   pinky: 14 X: 13.67  Y: 300.11  Z: 232.56
r_side 1   m_tip: 0   m_b: 0   m_side: 0   i_tip: 0   i_side: 0   p_side: 0thumb: 12   index: 0   middle: 2   ring: 17   pinky: 14 X: 13.13  Y: 299.86  Z: 233.42
r_side 1   m_tip: 0   m_b: 0   m_side: 0   i_tip: 0   i_side: 0   p_side: 0thumb: 12   index: 0   middle: 1   ring: 17   pinky: 14 X: 12.34  Y: 299.62  Z: 234.62
r_side 1   m_tip: 0   m_b: 0   m_side: 0   i_tip: 0   i_side: 0   p_side: 0thumb: 12   index: 0   middle: 1   ring: 17   pinky: 14 X: 12.23  Y: 299.42  Z: 234.83
r_side 1   m_tip: 0   m_b: 0   m_side: 0   i_tip: 0   i_side: 0   p_side: 0thumb: 13   index: 0   middle: 2   ring: 17   pinky: 15 X: 13.71  Y: 298.89  Z: 232.70
