juanmrq95/ee149_104/ASLsensing/longFlex/save_sensordata/test 1.1/testAashykLetterI.txt

 r_side 0   m_tip: 0   m_b: 0   m_side: 0   i_tip: 0   i_side: 0   p_side: 0thumb: 5   index: 1   middle: 2   ring: 2   pinky: 1 X: 359.87  Y: 358.57  Z: 359.74
r_side 0   m_tip: 0   m_b: 0   m_side: 0   i_tip: 0   i_side: 0   p_side: 0thumb: 5   index: 1   middle: 2   ring: 2   pinky: 1 X: 359.97  Y: 359.65  Z: 357.01
r_side 0   m_tip: 0   m_b: 0   m_side: 0   i_tip: 0   i_side: 0   p_side: 0thumb: 4   index: 0   middle: 2   ring: 2   pinky: 1 X: 359.83  Y: 0.85  Z: 354.82
r_side 0   m_tip: 0   m_b: 0   m_side: 0   i_tip: 0   i_side: 0   p_side: 0thumb: 5   index: 1   middle: 2   ring: 2   pinky: 1 X: 359.64  Y: 2.47  Z: 352.99
r_side 0   m_tip: 0   m_b: 0   m_side: 0   i_tip: 0   i_side: 0   p_side: 0thumb: 5   index: 1   middle: 2   ring: 2   pinky: 1 X: 359.37  Y: 3.76  Z: 350.93
r_side 0   m_tip: 0   m_b: 0   m_side: 0   i_tip: 0   i_side: 0   p_side: 0thumb: 4   index: 0   middle: 2   ring: 2   pinky: 1 X: 359.06  Y: 5.63  Z: 349.08
r_side 0   m_tip: 0   m_b: 0   m_side: 0   i_tip: 0   i_side: 0   p_side: 0thumb: 5   index: 1   middle: 2   ring: 2   pinky: 1 X: 358.68  Y: 6.72  Z: 347.60
r_side 0   m_tip: 0   m_b: 0   m_side: 0   i_tip: 0   i_side: 0   p_side: 0thumb: 5   index: 1   middle: 3   ring: 2   pinky: 1 X: 358.38  Y: 7.40  Z: 346.06
r_side 0   m_tip: 0   m_b: 0   m_side: 0   i_tip: 0   i_side: 0   p_side: 0thumb: 4   index: 1   middle: 2   ring: 2   pinky: 1 X: 358.29  Y: 7.53  Z: 344.35
r_side 0   m_tip: 0   m_b: 0   m_side: 0   i_tip: 0   i_side: 0   p_side: 0thumb: 5   index: 1   middle: 2   ring: 2   pinky: 1 X: 358.11  Y: 8.05  Z: 343.13
r_side 0   m_tip: 0   m_b: 0   m_side: 0   i_tip: 0   i_side: 0   p_side: 0thumb: 4   index: 1   middle: 2   ring: 2   pinky: 1 X: 357.81  Y: 8.55  Z: 341.35
r_side 0   m_tip: 0   m_b: 0   m_side: 0   i_tip: 0   i_side: 0   p_side: 0thumb: 5   index: 1   middle: 2   ring: 2   pinky: 1 X: 355.61  Y: 16.27  Z: 336.12
r_side 0   m_tip: 0   m_b: 0   m_side: 0   i_tip: 0   i_side: 0   p_side: 0thumb: 5   index: 5   middle: 3   ring: 8   pinky: 1 X: 347.47  Y: 34.33  Z: 329.03
r_side 0   m_tip: 0   m_b: 0   m_side: 0   i_tip: 0   i_side: 0   p_side: 0thumb: 5   index: 9   middle: 6   ring: 15   pinky: 1 X: 335.51  Y: 55.84  Z: 325.27
r_side 0   m_tip: 0   m_b: 0   m_side: 0   i_tip: 0   i_side: 1   p_side: 0thumb: 13   index: 14   middle: 12   ring: 16   pinky: 0 X: 308.25  Y: 60.52  Z: 304.12
r_side 0   m_tip: 0   m_b: 0   m_side: 0   i_tip: 0   i_side: 1   p_side: 0thumb: 13   index: 15   middle: 14   ring: 16   pinky: 0 X: 296.77  Y: 62.09  Z: 295.22
r_side 0   m_tip: 0   m_b: 0   m_side: 0   i_tip: 0   i_side: 1   p_side: 0thumb: 13   index: 16   middle: 15   ring: 16   pinky: 0 X: 301.46  Y: 60.48  Z: 297.87
r_side 0   m_tip: 0   m_b: 0   m_side: 0   i_tip: 0   i_side: 1   p_side: 0thumb: 13   index: 16   middle: 17   ring: 17   pinky: 1 X: 300.56  Y: 59.78  Z: 294.59
r_side 0   m_tip: 0   m_b: 0   m_side: 0   i_tip: 0   i_side: 1   p_side: 0thumb: 15   index: 18   middle: 18   ring: 17   pinky: 2 X: 299.14  Y: 61.80  Z: 292.79
r_side 0   m_tip: 0   m_b: 0   m_side: 0   i_tip: 0   i_side: 1   p_side: 0thumb: 15   index: 18   middle: 18   ring: 17   pinky: 2 X: 295.13  Y: 59.69  Z: 289.00
r_side 0   m_tip: 0   m_b: 0   m_side: 0   i_tip: 0   i_side: 1   p_side: 0thumb: 14   index: 18   middle: 17   ring: 17   pinky: 5 X: 294.79  Y: 60.66  Z: 287.51
r_side 0   m_tip: 0   m_b: 0   m_side: 0   i_tip: 0   i_side: 1   p_side: 0thumb: 14   index: 17   middle: 17   ring: 16   pinky: 2 X: 290.49  Y: 58.35  Z: 283.76
r_side 0   m_tip: 0   m_b: 0   m_side: 0   i_tip: 0   i_side: 1   p_side: 0thumb: 14   index: 17   middle: 17   ring: 16   pinky: 1 X: 282.49  Y: 56.06  Z: 276.75
r_side 0   m_tip: 0   m_b: 0   m_side: 0   i_tip: 0   i_side: 1   p_side: 0thumb: 14   index: 17   middle: 17   ring: 16   pinky: 1 X: 281.38  Y: 56.33  Z: 275.47
r_side 0   m_tip: 0   m_b: 0   m_side: 0   i_tip: 0   i_side: 1   p_side: 0thumb: 14   index: 17   middle: 16   ring: 16   pinky: 1 X: 278.08  Y: 56.39  Z: 272.84
r_side 0   m_tip: 0   m_b: 0   m_side: 0   i_tip: 0   i_side: 1   p_side: 0thumb: 14   index: 17   middle: 16   ring: 16   pinky: 1 X: 275.50  Y: 56.05  Z: 270.83
r_side 0   m_tip: 0   m_b: 0   m_side: 0   i_tip: 0   i_side: 1   p_side: 0thumb: 14   index: 17   middle: 16   ring: 16   pinky: 1 X: 276.15  Y: 56.69  Z: 271.89
r_side 0   m_tip: 0   m_b: 0   m_side: 0   i_tip: 0   i_side: 1   p_side: 0thumb: 14   index: 17   middle: 16   ring: 16   pinky: 0 X: 272.22  Y: 56.73  Z: 268.51
r_side 0   m_tip: 0   m_b: 0   m_side: 0   i_tip: 0   i_side: 1   p_side: 0thumb: 14   index: 17   middle: 16   ring: 16   pinky: 0 X: 273.82  Y: 55.85  Z: 269.80
r_side 0   m_tip: 0   m_b: 0   m_side: 0   i_tip: 0   i_side: 1   p_side: 0thumb: 14   index: 16   middle: 16   ring: 15   pinky: 0 X: 273.04  Y: 57.01  Z: 268.50
r_side 0   m_tip: 0   m_b: 0   m_side: 0   i_tip: 0   i_side: 1   p_side: 0thumb: 14   index: 17   middle: 16   ring: 16   pinky: 0 X: 273.60  Y: 56.60  Z: 267.58
r_side 0   m_tip: 0   m_b: 0   m_side: 0   i_tip: 0   i_side: 1   p_side: 0thumb: 14   index: 16   middle: 16   ring: 15   pinky: 0 X: 273.71  Y: 58.24  Z: 266.44
r_side 0   m_tip: 0   m_b: 0   m_side: 0   i_tip: 0   i_side: 1   p_side: 0thumb: 14   index: 17   middle: 15   ring: 15   pinky: 1 X: 272.60  Y: 57.73  Z: 264.86
r_side 0   m_tip: 0   m_b: 0   m_side: 0   i_tip: 0   i_side: 1   p_side: 0thumb: 14   index: 17   middle: 15   ring: 15   pinky: 1 X: 269.40  Y: 55.70  Z: 262.81
r_side 0   m_tip: 0   m_b: 0   m_side: 0   i_tip: 0   i_side: 1   p_side: 0thumb: 14   index: 17   middle: 16   ring: 15   pinky: 0 X: 269.95  Y: 54.78  Z: 263.46
r_side 0   m_tip: 0   m_b: 0   m_side: 0   i_tip: 0   i_side: 1   p_side: 0thumb: 14   index: 17   middle: 16   ring: 15   pinky: 0 X: 269.41  Y: 55.10  Z: 263.12
r_side 0   m_tip: 0   m_b: 0   m_side: 0   i_tip: 0   i_side: 1   p_side: 0thumb: 14   index: 17   middle: 15   ring: 16   pinky: 1 X: 271.31  Y: 54.36  Z: 263.59
r_side 0   m_tip: 0   m_b: 0   m_side: 0   i_tip: 0   i_side: 1   p_side: 0thumb: 14   index: 16   middle: 15   ring: 15   pinky: 1 X: 270.47  Y: 53.84  Z: 262.47
r_side 0   m_tip: 0   m_b: 0   m_side: 0   i_tip: 0   i_side: 1   p_side: 0thumb: 14   index: 17   middle: 15   ring: 15   pinky: 1 X: 271.52  Y: 52.44  Z: 263.88
r_side 0   m_tip: 0   m_b: 0   m_side: 0   i_tip: 0   i_side: 1   p_side: 0thumb: 14   index: 17   middle: 15   ring: 15   pinky: 1 X: 273.24  Y: 49.90  Z: 264.94
r_side 0   m_tip: 0   m_b: 0   m_side: 0   i_tip: 0   i_side: 1   p_side: 0thumb: 14   index: 17   middle: 15   ring: 15   pinky: 0 X: 274.06  Y: 49.06  Z: 265.23
r_side 0   m_tip: 0   m_b: 0   m_side: 0   i_tip: 0   i_side: 1   p_side: 0thumb: 14   index: 16   middle: 15   ring: 15   pinky: 0 X: 274.81  Y: 48.63  Z: 265.46
r_side 0   m_tip: 0   m_b: 0   m_side: 0   i_tip: 0   i_side: 1   p_side: 0thumb: 14   index: 17   middle: 15   ring: 15   pinky: 0 X: 274.48  Y: 48.06  Z: 265.20
r_side 0   m_tip: 0   m_b: 0   m_side: 0   i_tip: 0   i_side: 1   p_side: 0thumb: 14   index: 16   middle: 15   ring: 14   pinky: 0 X: 274.62  Y: 47.34  Z: 265.15
r_side 0   m_tip: 0   m_b: 0   m_side: 0   i_tip: 0   i_side: 1   p_side: 0thumb: 14   index: 16   middle: 15   ring: 15   pinky: 0 X: 275.21  Y: 47.68  Z: 265.44
r_side 0   m_tip: 0   m_b: 0   m_side: 0   i_tip: 0   i_side: 1   p_side: 0thumb: 13   index: 16   middle: 15   ring: 15   pinky: 0 X: 275.13  Y: 47.22  Z: 265.49
r_side 0   m_tip: 0   m_b: 0   m_side: 0   i_tip: 0   i_side: 1   p_side: 0thumb: 14   index: 16   middle: 15   ring: 14   pinky: 0 X: 275.40  Y: 47.29  Z: 265.76
r_side 0   m_tip: 0   m_b: 0   m_side: 0   i_tip: 0   i_side: 1   p_side: 0thumb: 14   index: 16   middle: 15   ring: 15   pinky: 0 X: 275.79  Y: 46.80  Z: 265.88
r_side 0   m_tip: 0   m_b: 0   m_side: 0   i_tip: 0   i_side: 1   p_side: 0thumb: 14   index: 16   middle: 15   ring: 14   pinky: 0 X: 276.84  Y: 47.04  Z: 266.01
r_side 0   m_tip: 0   m_b: 0   m_side: 0   i_tip: 0   i_side: 1   p_side: 0thumb: 14   index: 16   middle: 15   ring: 14   pinky: 0 X: 276.25  Y: 46.58  Z: 265.84
r_side 0   m_tip: 0   m_b: 0   m_side: 0   i_tip: 0   i_side: 1   p_side: 0thumb: 14   index: 16   middle: 15   ring: 14   pinky: 0 X: 276.50  Y: 46.44  Z: 266.38
r_side 0   m_tip: 0   m_b: 0   m_side: 0   i_tip: 0   i_side: 1   p_side: 0thumb: 14   index: 16   middle: 15   ring: 14   pinky: 0 X: 276.33  Y: 46.10  Z: 266.02
r_side 0   m_tip: 0   m_b: 0   m_side: 0   i_tip: 0   i_side: 1   p_side: 0thumb: 14   index: 16   middle: 15   ring: 14   pinky: 0 X: 276.03  Y: 46.22  Z: 265.67
r_side 0   m_tip: 0   m_b: 0   m_side: 0   i_tip: 0   i_side: 1   p_side: 0thumb: 13   index: 16   middle: 15   ring: 14   pinky: 0 X: 276.41  Y: 46.06  Z: 265.94
r_side 0   m_tip: 0   m_b: 0   m_side: 0   i_tip: 0   i_side: 1   p_side: 0thumb: 14   index: 16   middle: 14   ring: 14   pinky: 0 X: 277.08  Y: 44.83  Z: 266.56
r_side 0   m_tip: 0   m_b: 0   m_side: 0   i_tip: 0   i_side: 1   p_side: 0thumb: 13   index: 16   middle: 15   ring: 14   pinky: 0 X: 276.82  Y: 44.23  Z: 267.00
r_side 0   m_tip: 0   m_b: 0   m_side: 0   i_tip: 0   i_side: 1   p_side: 0thumb: 13   index: 16   middle: 15   ring: 14   pinky: 0 X: 277.17  Y: 43.95  Z: 266.78
r_side 0   m_tip: 0   m_b: 0   m_side: 0   i_tip: 0   i_side: 1   p_side: 0thumb: 14   index: 16   middle: 14   ring: 14   pinky: 0 X: 277.70  Y: 42.95  Z: 267.58
r_side 0   m_tip: 0   m_b: 0   m_side: 0   i_tip: 0   i_side: 1   p_side: 0thumb: 14   index: 16   middle: 15   ring: 14   pinky: 0 X: 279.62  Y: 42.04  Z: 269.39
r_side 0   m_tip: 0   m_b: 0   m_side: 0   i_tip: 0   i_side: 1   p_side: 0thumb: 14   index: 16   middle: 15   ring: 14   pinky: 0 X: 279.54  Y: 40.60  Z: 269.19
