juanmrq95/ee149_104/ASLsensing/longFlex/save_sensordata/test 1.1/testAashykLetterK.txt

´r_side 0   m_tip: 0   m_b: 0   m_side: 0   i_tip: 0   i_side: 0   p_side: 0thumb: 7   index: 0   middle: 2   ring: 2   pinky: 1 X: 0.52  Y: 1.56  Z: 359.75
r_side 0   m_tip: 0   m_b: 0   m_side: 0   i_tip: 0   i_side: 0   p_side: 0thumb: 5   index: 0   middle: 2   ring: 2   pinky: 1 X: 0.51  Y: 2.62  Z: 357.81
r_side 0   m_tip: 0   m_b: 0   m_side: 0   i_tip: 0   i_side: 0   p_side: 0thumb: 7   index: 0   middle: 2   ring: 2   pinky: 1 X: 0.46  Y: 3.53  Z: 355.84
r_side 0   m_tip: 0   m_b: 0   m_side: 0   i_tip: 0   i_side: 0   p_side: 0thumb: 7   index: 0   middle: 2   ring: 2   pinky: 1 X: 0.34  Y: 4.62  Z: 354.00
r_side 0   m_tip: 0   m_b: 0   m_side: 0   i_tip: 0   i_side: 0   p_side: 0thumb: 6   index: 0   middle: 2   ring: 2   pinky: 1 X: 0.17  Y: 5.64  Z: 352.40
r_side 0   m_tip: 0   m_b: 0   m_side: 0   i_tip: 0   i_side: 0   p_side: 0thumb: 7   index: 0   middle: 2   ring: 2   pinky: 1 X: 0.26  Y: 6.88  Z: 350.46
r_side 0   m_tip: 0   m_b: 0   m_side: 0   i_tip: 0   i_side: 0   p_side: 0thumb: 7   index: 0   middle: 2   ring: 2   pinky: 1 X: 0.23  Y: 7.88  Z: 348.85
r_side 0   m_tip: 0   m_b: 0   m_side: 0   i_tip: 0   i_side: 0   p_side: 0thumb: 7   index: 0   middle: 2   ring: 2   pinky: 1 X: 0.16  Y: 8.82  Z: 347.55
r_side 0   m_tip: 0   m_b: 0   m_side: 0   i_tip: 0   i_side: 0   p_side: 0thumb: 6   index: 0   middle: 2   ring: 2   pinky: 1 X: 0.05  Y: 9.50  Z: 346.20
r_side 0   m_tip: 0   m_b: 0   m_side: 0   i_tip: 0   i_side: 0   p_side: 0thumb: 7   index: 0   middle: 2   ring: 2   pinky: 0 X: 359.52  Y: 12.76  Z: 339.95
r_side 0   m_tip: 0   m_b: 0   m_side: 0   i_tip: 0   i_side: 0   p_side: 0thumb: 7   index: 0   middle: 2   ring: 2   pinky: 1 X: 355.49  Y: 20.88  Z: 337.42
r_side 0   m_tip: 0   m_b: 0   m_side: 0   i_tip: 0   i_side: 0   p_side: 0thumb: 8   index: 0   middle: 4   ring: 9   pinky: 2 X: 347.63  Y: 31.74  Z: 333.30
r_side 0   m_tip: 0   m_b: 0   m_side: 0   i_tip: 0   i_side: 0   p_side: 0thumb: 6   index: 0   middle: 7   ring: 14   pinky: 8 X: 341.03  Y: 35.92  Z: 329.47
r_side 0   m_tip: 0   m_b: 0   m_side: 0   i_tip: 0   i_side: 0   p_side: 0thumb: 7   index: 0   middle: 12   ring: 17   pinky: 12 X: 335.41  Y: 39.57  Z: 325.27
r_side 0   m_tip: 0   m_b: 0   m_side: 1   i_tip: 1   i_side: 0   p_side: 0thumb: 6   index: 0   middle: 12   ring: 15   pinky: 9 X: 326.13  Y: 49.80  Z: 317.80
r_side 0   m_tip: 0   m_b: 0   m_side: 1   i_tip: 0   i_side: 0   p_side: 0thumb: 6   index: 0   middle: 12   ring: 14   pinky: 8 X: 326.36  Y: 49.95  Z: 318.47
r_side 0   m_tip: 0   m_b: 0   m_side: 1   i_tip: 1   i_side: 0   p_side: 0thumb: 6   index: 0   middle: 14   ring: 14   pinky: 12 X: 321.48  Y: 53.16  Z: 314.37
r_side 0   m_tip: 0   m_b: 0   m_side: 1   i_tip: 1   i_side: 0   p_side: 0thumb: 6   index: 0   middle: 14   ring: 16   pinky: 17 X: 319.31  Y: 57.65  Z: 315.14
r_side 0   m_tip: 0   m_b: 0   m_side: 1   i_tip: 1   i_side: 0   p_side: 0thumb: 6   index: 0   middle: 16   ring: 19   pinky: 19 X: 317.18  Y: 55.20  Z: 312.15
r_side 0   m_tip: 0   m_b: 0   m_side: 1   i_tip: 0   i_side: 0   p_side: 0thumb: 6   index: 0   middle: 19   ring: 19   pinky: 18 X: 313.07  Y: 56.50  Z: 309.77
r_side 0   m_tip: 0   m_b: 0   m_side: 1   i_tip: 1   i_side: 0   p_side: 0thumb: 6   index: 0   middle: 16   ring: 18   pinky: 18 X: 312.95  Y: 54.82  Z: 307.91
r_side 0   m_tip: 0   m_b: 0   m_side: 1   i_tip: 1   i_side: 0   p_side: 0thumb: 6   index: 1   middle: 12   ring: 18   pinky: 18 X: 310.36  Y: 56.59  Z: 305.95
r_side 0   m_tip: 0   m_b: 0   m_side: 1   i_tip: 1   i_side: 0   p_side: 0thumb: 6   index: 0   middle: 10   ring: 17   pinky: 17 X: 307.64  Y: 57.97  Z: 303.22
r_side 0   m_tip: 0   m_b: 0   m_side: 1   i_tip: 1   i_side: 0   p_side: 0thumb: 6   index: 0   middle: 8   ring: 17   pinky: 17 X: 309.66  Y: 56.63  Z: 304.54
r_side 0   m_tip: 0   m_b: 0   m_side: 1   i_tip: 1   i_side: 0   p_side: 0thumb: 6   index: 0   middle: 7   ring: 17   pinky: 17 X: 309.35  Y: 55.81  Z: 303.88
r_side 0   m_tip: 0   m_b: 0   m_side: 1   i_tip: 1   i_side: 0   p_side: 0thumb: 5   index: 0   middle: 7   ring: 17   pinky: 17 X: 306.71  Y: 55.31  Z: 302.07
r_side 0   m_tip: 0   m_b: 0   m_side: 0   i_tip: 0   i_side: 0   p_side: 0thumb: 8   index: 0   middle: 6   ring: 17   pinky: 17 X: 308.47  Y: 54.13  Z: 303.62
r_side 0   m_tip: 0   m_b: 1   m_side: 1   i_tip: 1   i_side: 0   p_side: 0thumb: 9   index: 0   middle: 6   ring: 17   pinky: 17 X: 311.06  Y: 53.11  Z: 305.85
r_side 0   m_tip: 0   m_b: 0   m_side: 1   i_tip: 1   i_side: 0   p_side: 0thumb: 9   index: 0   middle: 6   ring: 17   pinky: 17 X: 312.89  Y: 52.28  Z: 306.44
r_side 0   m_tip: 0   m_b: 1   m_side: 1   i_tip: 1   i_side: 0   p_side: 0thumb: 9   index: 0   middle: 6   ring: 17   pinky: 17 X: 312.00  Y: 52.57  Z: 305.94
r_side 0   m_tip: 0   m_b: 0   m_side: 1   i_tip: 1   i_side: 0   p_side: 0thumb: 9   index: 0   middle: 6   ring: 17   pinky: 17 X: 311.88  Y: 51.59  Z: 305.07
r_side 0   m_tip: 0   m_b: 1   m_side: 1   i_tip: 1   i_side: 0   p_side: 0thumb: 9   index: 0   middle: 6   ring: 16   pinky: 17 X: 311.83  Y: 51.32  Z: 304.80
r_side 0   m_tip: 0   m_b: 0   m_side: 1   i_tip: 1   i_side: 0   p_side: 0thumb: 9   index: 0   middle: 5   ring: 16   pinky: 17 X: 310.64  Y: 51.50  Z: 303.82
r_side 0   m_tip: 0   m_b: 0   m_side: 1   i_tip: 1   i_side: 0   p_side: 0thumb: 9   index: 0   middle: 6   ring: 16   pinky: 17 X: 311.71  Y: 50.99  Z: 305.18
r_side 0   m_tip: 0   m_b: 0   m_side: 1   i_tip: 1   i_side: 0   p_side: 0thumb: 9   index: 0   middle: 6   ring: 16   pinky: 17 X: 311.29  Y: 50.30  Z: 304.24
r_side 0   m_tip: 0   m_b: 0   m_side: 1   i_tip: 1   i_side: 0   p_side: 0thumb: 9   index: 0   middle: 6   ring: 16   pinky: 17 X: 311.59  Y: 50.26  Z: 305.08
r_side 0   m_tip: 0   m_b: 0   m_side: 1   i_tip: 1   i_side: 0   p_side: 0thumb: 9   index: 0   middle: 6   ring: 16   pinky: 17 X: 311.47  Y: 49.20  Z: 305.07
r_side 0   m_tip: 0   m_b: 0   m_side: 1   i_tip: 1   i_side: 0   p_side: 0thumb: 9   index: 0   middle: 6   ring: 16   pinky: 17 X: 311.85  Y: 48.53  Z: 305.40
r_side 0   m_tip: 0   m_b: 0   m_side: 1   i_tip: 1   i_side: 0   p_side: 0thumb: 9   index: 0   middle: 5   ring: 16   pinky: 17 X: 311.98  Y: 47.20  Z: 305.65
r_side 0   m_tip: 0   m_b: 0   m_side: 1   i_tip: 1   i_side: 0   p_side: 0thumb: 9   index: 0   middle: 6   ring: 16   pinky: 17 X: 311.45  Y: 46.82  Z: 304.95
r_side 0   m_tip: 0   m_b: 0   m_side: 1   i_tip: 1   i_side: 0   p_side: 0thumb: 9   index: 0   middle: 6   ring: 16   pinky: 16 X: 311.30  Y: 46.19  Z: 304.49
r_side 0   m_tip: 0   m_b: 0   m_side: 1   i_tip: 1   i_side: 0   p_side: 0thumb: 9   index: 0   middle: 6   ring: 16   pinky: 16 X: 312.98  Y: 45.11  Z: 305.73
r_side 0   m_tip: 0   m_b: 0   m_side: 1   i_tip: 1   i_side: 0   p_side: 0thumb: 9   index: 0   middle: 5   ring: 16   pinky: 16 X: 312.30  Y: 44.72  Z: 304.90
r_side 0   m_tip: 0   m_b: 0   m_side: 1   i_tip: 1   i_side: 0   p_side: 0thumb: 9   index: 0   middle: 6   ring: 16   pinky: 16 X: 311.60  Y: 44.21  Z: 304.15
r_side 0   m_tip: 0   m_b: 0   m_side: 1   i_tip: 1   i_side: 0   p_side: 0thumb: 9   index: 0   middle: 5   ring: 16   pinky: 16 X: 311.91  Y: 44.36  Z: 304.19
r_side 0   m_tip: 0   m_b: 0   m_side: 1   i_tip: 1   i_side: 0   p_side: 0thumb: 9   index: 0   middle: 5   ring: 16   pinky: 16 X: 312.31  Y: 44.33  Z: 304.59
r_side 0   m_tip: 0   m_b: 1   m_side: 1   i_tip: 1   i_side: 0   p_side: 0thumb: 9   index: 0   middle: 5   ring: 15   pinky: 16 X: 312.39  Y: 43.88  Z: 304.51
r_side 0   m_tip: 0   m_b: 0   m_side: 1   i_tip: 1   i_side: 0   p_side: 0thumb: 9   index: 0   middle: 5   ring: 16   pinky: 16 X: 311.85  Y: 43.55  Z: 303.87
r_side 0   m_tip: 0   m_b: 0   m_side: 1   i_tip: 1   i_side: 0   p_side: 0thumb: 9   index: 0   middle: 5   ring: 16   pinky: 16 X: 312.23  Y: 43.69  Z: 303.89
r_side 0   m_tip: 0   m_b: 0   m_side: 1   i_tip: 1   i_side: 0   p_side: 0thumb: 10   index: 0   middle: 5   ring: 16   pinky: 16 X: 312.57  Y: 42.80  Z: 304.56
r_side 0   m_tip: 0   m_b: 0   m_side: 1   i_tip: 1   i_side: 0   p_side: 0thumb: 9   index: 0   middle: 6   ring: 16   pinky: 16 X: 311.81  Y: 42.50  Z: 303.77
r_side 0   m_tip: 0   m_b: 0   m_side: 1   i_tip: 1   i_side: 0   p_side: 0thumb: 9   index: 0   middle: 5   ring: 16   pinky: 16 X: 311.05  Y: 42.43  Z: 303.36
r_side 0   m_tip: 0   m_b: 0   m_side: 1   i_tip: 1   i_side: 0   p_side: 0thumb: 9   index: 0   middle: 6   ring: 15   pinky: 16 X: 309.64  Y: 42.42  Z: 302.69
r_side 0   m_tip: 0   m_b: 0   m_side: 1   i_tip: 1   i_side: 0   p_side: 0thumb: 9   index: 0   middle: 5   ring: 16   pinky: 16 X: 309.29  Y: 41.77  Z: 302.00
r_side 0   m_tip: 0   m_b: 0   m_side: 1   i_tip: 1   i_side: 0   p_side: 0thumb: 9   index: 0   middle: 6   ring: 15   pinky: 16 X: 309.50  Y: 41.23  Z: 302.02
r_side 0   m_tip: 0   m_b: 0   m_side: 1   i_tip: 1   i_side: 0   p_side: 0thumb: 9   index: 0   middle: 5   ring: 16   pinky: 16 X: 307.03  Y: 39.53  Z: 298.67
r_side 0   m_tip: 0   m_b: 0   m_side: 1   i_tip: 1   i_side: 0   p_side: 0thumb: 10   index: 0   middle: 5   ring: 16   pinky: 16 X: 307.47  Y: 39.31  Z: 300.03
r_side 0   m_tip: 0   m_b: 1   m_side: 1   i_tip: 1   i_side: 0   p_side: 0thumb: 9   index: 0   middle: 5   ring: 16   pinky: 16 X: 307.64  Y: 36.00  Z: 298.34
r_side 0   m_tip: 0   m_b: 0   m_side: 1   i_tip: 1   i_side: 0   p_side: 0thumb: 10   index: 0   middle: 5   ring: 15   pinky: 16 X: 307.38  Y: 35.45  Z: 298.57
r_side 0   m_tip: 0   m_b: 0   m_side: 0   i_tip: 0   i_side: 0   p_side: 0thumb: 11   index: 0   middle: 5   ring: 15   pinky: 16 X: 310.07  Y: 33.37  Z: 302.75
r_side 0   m_tip: 0   m_b: 0   m_side: 0   i_tip: 0   i_side: 0   p_side: 0thumb: 10   index: 0   middle: 5   ring: 15   pinky: 14 X: 311.16  Y: 32.99  Z: 306.65
