juanmrq95/ee149_104/ASLsensing/longFlex/save_sensordata/test 1.1/testAashykLetterL.txt

r_side 0   m_tip: 0   m_b: 0   m_side: 0   i_tip: 0   i_side: 0   p_side: 0thumb: 5   index: 1   middle: 2   ring: 2   pinky: 1 X: 0.79  Y: 0.52  Z: 0.53
r_side 0   m_tip: 0   m_b: 0   m_side: 0   i_tip: 0   i_side: 0   p_side: 0thumb: 5   index: 1   middle: 2   ring: 2   pinky: 1 X: 0.68  Y: 1.51  Z: 357.72
r_side 0   m_tip: 0   m_b: 0   m_side: 0   i_tip: 0   i_side: 0   p_side: 0thumb: 5   index: 1   middle: 2   ring: 2   pinky: 1 X: 0.63  Y: 2.88  Z: 355.24
r_side 0   m_tip: 0   m_b: 0   m_side: 0   i_tip: 0   i_side: 0   p_side: 0thumb: 5   index: 0   middle: 2   ring: 1   pinky: 1 X: 0.68  Y: 3.57  Z: 352.79
r_side 0   m_tip: 0   m_b: 0   m_side: 0   i_tip: 0   i_side: 0   p_side: 0thumb: 5   index: 1   middle: 2   ring: 1   pinky: 1 X: 0.65  Y: 4.41  Z: 350.60
r_side 0   m_tip: 0   m_b: 0   m_side: 0   i_tip: 0   i_side: 0   p_side: 0thumb: 5   index: 1   middle: 2   ring: 2   pinky: 1 X: 0.31  Y: 5.44  Z: 348.23
r_side 0   m_tip: 0   m_b: 0   m_side: 0   i_tip: 0   i_side: 0   p_side: 0thumb: 5   index: 1   middle: 2   ring: 2   pinky: 1 X: 0.14  Y: 6.27  Z: 346.11
r_side 0   m_tip: 0   m_b: 0   m_side: 0   i_tip: 0   i_side: 0   p_side: 0thumb: 5   index: 1   middle: 2   ring: 1   pinky: 1 X: 359.96  Y: 6.97  Z: 344.31
r_side 0   m_tip: 0   m_b: 0   m_side: 0   i_tip: 0   i_side: 0   p_side: 0thumb: 5   index: 1   middle: 2   ring: 1   pinky: 1 X: 359.85  Y: 7.64  Z: 342.80
r_side 0   m_tip: 0   m_b: 0   m_side: 0   i_tip: 0   i_side: 0   p_side: 0thumb: 5   index: 1   middle: 2   ring: 2   pinky: 1 X: 359.60  Y: 8.17  Z: 341.13
r_side 0   m_tip: 0   m_b: 0   m_side: 0   i_tip: 0   i_side: 0   p_side: 0thumb: 5   index: 2   middle: 2   ring: 2   pinky: 1 X: 358.96  Y: 8.06  Z: 339.39
r_side 0   m_tip: 0   m_b: 0   m_side: 0   i_tip: 0   i_side: 0   p_side: 0thumb: 5   index: 1   middle: 2   ring: 2   pinky: 1 X: 353.79  Y: 18.77  Z: 340.59
r_side 0   m_tip: 0   m_b: 0   m_side: 0   i_tip: 0   i_side: 0   p_side: 0thumb: 5   index: 1   middle: 10   ring: 13   pinky: 2 X: 346.16  Y: 31.28  Z: 336.61
r_side 0   m_tip: 0   m_b: 0   m_side: 0   i_tip: 0   i_side: 0   p_side: 0thumb: 5   index: 1   middle: 21   ring: 22   pinky: 18 X: 339.14  Y: 40.89  Z: 336.51
r_side 0   m_tip: 0   m_b: 0   m_side: 0   i_tip: 0   i_side: 0   p_side: 0thumb: 5   index: 7   middle: 22   ring: 24   pinky: 20 X: 331.40  Y: 50.76  Z: 335.02
r_side 0   m_tip: 1   m_b: 0   m_side: 0   i_tip: 0   i_side: 0   p_side: 0thumb: 4   index: 9   middle: 20   ring: 22   pinky: 20 X: 319.25  Y: 53.24  Z: 321.77
r_side 0   m_tip: 0   m_b: 0   m_side: 0   i_tip: 0   i_side: 0   p_side: 0thumb: 4   index: 4   middle: 20   ring: 21   pinky: 19 X: 305.85  Y: 54.37  Z: 312.66
r_side 0   m_tip: 0   m_b: 0   m_side: 0   i_tip: 0   i_side: 0   p_side: 0thumb: 4   index: 4   middle: 19   ring: 21   pinky: 19 X: 301.48  Y: 55.15  Z: 312.35
r_side 0   m_tip: 0   m_b: 0   m_side: 0   i_tip: 0   i_side: 0   p_side: 0thumb: 4   index: 3   middle: 20   ring: 21   pinky: 18 X: 299.85  Y: 54.50  Z: 309.86
r_side 0   m_tip: 0   m_b: 0   m_side: 0   i_tip: 0   i_side: 0   p_side: 0thumb: 4   index: 3   middle: 19   ring: 20   pinky: 18 X: 303.14  Y: 58.23  Z: 310.65
r_side 0   m_tip: 0   m_b: 0   m_side: 0   i_tip: 0   i_side: 0   p_side: 0thumb: 4   index: 3   middle: 19   ring: 20   pinky: 18 X: 302.18  Y: 56.03  Z: 306.99
r_side 0   m_tip: 0   m_b: 0   m_side: 0   i_tip: 0   i_side: 0   p_side: 0thumb: 3   index: 4   middle: 19   ring: 20   pinky: 17 X: 301.52  Y: 55.77  Z: 306.18
r_side 0   m_tip: 0   m_b: 0   m_side: 0   i_tip: 0   i_side: 0   p_side: 0thumb: 3   index: 2   middle: 19   ring: 20   pinky: 18 X: 302.83  Y: 55.48  Z: 306.52
r_side 0   m_tip: 0   m_b: 0   m_side: 0   i_tip: 0   i_side: 0   p_side: 0thumb: 3   index: 2   middle: 19   ring: 20   pinky: 17 X: 303.08  Y: 55.30  Z: 306.00
r_side 0   m_tip: 0   m_b: 0   m_side: 0   i_tip: 0   i_side: 0   p_side: 0thumb: 3   index: 2   middle: 19   ring: 20   pinky: 17 X: 301.65  Y: 54.13  Z: 304.11
r_side 0   m_tip: 0   m_b: 0   m_side: 0   i_tip: 0   i_side: 0   p_side: 0thumb: 3   index: 2   middle: 19   ring: 20   pinky: 17 X: 300.85  Y: 54.82  Z: 303.93
r_side 0   m_tip: 0   m_b: 0   m_side: 0   i_tip: 0   i_side: 0   p_side: 0thumb: 3   index: 2   middle: 19   ring: 19   pinky: 17 X: 296.73  Y: 54.61  Z: 300.09
r_side 0   m_tip: 0   m_b: 0   m_side: 0   i_tip: 0   i_side: 0   p_side: 0thumb: 3   index: 2   middle: 19   ring: 20   pinky: 17 X: 298.65  Y: 52.59  Z: 300.93
r_side 0   m_tip: 0   m_b: 0   m_side: 0   i_tip: 0   i_side: 0   p_side: 0thumb: 3   index: 1   middle: 19   ring: 19   pinky: 17 X: 299.34  Y: 51.01  Z: 301.30
r_side 0   m_tip: 0   m_b: 0   m_side: 0   i_tip: 0   i_side: 0   p_side: 0thumb: 3   index: 2   middle: 19   ring: 19   pinky: 17 X: 300.09  Y: 51.38  Z: 301.80
r_side 0   m_tip: 0   m_b: 0   m_side: 0   i_tip: 0   i_side: 0   p_side: 0thumb: 3   index: 1   middle: 18   ring: 19   pinky: 17 X: 299.21  Y: 50.48  Z: 300.28
r_side 0   m_tip: 0   m_b: 0   m_side: 0   i_tip: 0   i_side: 0   p_side: 0thumb: 3   index: 1   middle: 18   ring: 19   pinky: 17 X: 299.45  Y: 49.43  Z: 300.28
r_side 0   m_tip: 0   m_b: 0   m_side: 0   i_tip: 0   i_side: 0   p_side: 0thumb: 3   index: 1   middle: 18   ring: 19   pinky: 17 X: 300.52  Y: 48.42  Z: 300.75
r_side 0   m_tip: 0   m_b: 0   m_side: 0   i_tip: 0   i_side: 0   p_side: 0thumb: 2   index: 1   middle: 18   ring: 19   pinky: 17 X: 299.38  Y: 47.32  Z: 299.46
r_side 0   m_tip: 0   m_b: 0   m_side: 0   i_tip: 0   i_side: 0   p_side: 0thumb: 3   index: 1   middle: 18   ring: 19   pinky: 17 X: 297.30  Y: 45.62  Z: 297.20
r_side 0   m_tip: 0   m_b: 0   m_side: 0   i_tip: 0   i_side: 0   p_side: 0thumb: 2   index: 1   middle: 18   ring: 19   pinky: 17 X: 298.02  Y: 44.33  Z: 297.70
r_side 0   m_tip: 0   m_b: 0   m_side: 0   i_tip: 0   i_side: 0   p_side: 0thumb: 3   index: 1   middle: 18   ring: 19   pinky: 17 X: 298.30  Y: 43.76  Z: 297.88
r_side 0   m_tip: 0   m_b: 0   m_side: 0   i_tip: 0   i_side: 0   p_side: 0thumb: 3   index: 1   middle: 18   ring: 19   pinky: 17 X: 297.19  Y: 43.28  Z: 296.70
r_side 0   m_tip: 0   m_b: 0   m_side: 0   i_tip: 0   i_side: 0   p_side: 0thumb: 3   index: 2   middle: 18   ring: 19   pinky: 17 X: 297.25  Y: 42.86  Z: 296.98
r_side 0   m_tip: 0   m_b: 0   m_side: 0   i_tip: 0   i_side: 0   p_side: 0thumb: 2   index: 1   middle: 18   ring: 19   pinky: 17 X: 296.81  Y: 42.11  Z: 296.48
r_side 0   m_tip: 0   m_b: 0   m_side: 0   i_tip: 0   i_side: 0   p_side: 0thumb: 2   index: 1   middle: 18   ring: 19   pinky: 17 X: 295.18  Y: 41.51  Z: 295.33
r_side 0   m_tip: 0   m_b: 0   m_side: 0   i_tip: 0   i_side: 0   p_side: 0thumb: 3   index: 1   middle: 18   ring: 19   pinky: 17 X: 296.33  Y: 40.73  Z: 295.98
r_side 0   m_tip: 1   m_b: 0   m_side: 0   i_tip: 0   i_side: 0   p_side: 0thumb: 2   index: 1   middle: 18   ring: 19   pinky: 17 X: 297.46  Y: 39.66  Z: 296.53
r_side 0   m_tip: 0   m_b: 0   m_side: 0   i_tip: 0   i_side: 0   p_side: 0thumb: 2   index: 1   middle: 18   ring: 19   pinky: 17 X: 295.15  Y: 41.07  Z: 295.03
r_side 0   m_tip: 1   m_b: 0   m_side: 0   i_tip: 0   i_side: 0   p_side: 0thumb: 3   index: 1   middle: 18   ring: 19   pinky: 16 X: 296.75  Y: 40.95  Z: 296.63
r_side 0   m_tip: 1   m_b: 0   m_side: 0   i_tip: 0   i_side: 0   p_side: 0thumb: 2   index: 1   middle: 18   ring: 18   pinky: 16 X: 294.87  Y: 39.36  Z: 294.84
r_side 0   m_tip: 1   m_b: 0   m_side: 0   i_tip: 0   i_side: 0   p_side: 0thumb: 2   index: 1   middle: 18   ring: 19   pinky: 16 X: 294.24  Y: 39.08  Z: 294.90
r_side 0   m_tip: 1   m_b: 0   m_side: 0   i_tip: 0   i_side: 0   p_side: 0thumb: 2   index: 1   middle: 18   ring: 19   pinky: 16 X: 293.25  Y: 39.67  Z: 294.96
r_side 0   m_tip: 0   m_b: 0   m_side: 0   i_tip: 0   i_side: 0   p_side: 0thumb: 3   index: 1   middle: 18   ring: 19   pinky: 16 X: 295.20  Y: 39.49  Z: 296.33
r_side 0   m_tip: 0   m_b: 0   m_side: 0   i_tip: 0   i_side: 0   p_side: 0thumb: 2   index: 1   middle: 18   ring: 18   pinky: 16 X: 295.26  Y: 36.58  Z: 296.15
r_side 0   m_tip: 0   m_b: 0   m_side: 0   i_tip: 0   i_side: 0   p_side: 0thumb: 2   index: 1   middle: 18   ring: 18   pinky: 16 X: 294.08  Y: 36.31  Z: 295.21
r_side 0   m_tip: 0   m_b: 0   m_side: 0   i_tip: 0   i_side: 0   p_side: 0thumb: 2   index: 1   middle: 18   ring: 18   pinky: 16 X: 293.23  Y: 36.42  Z: 294.83
r_side 0   m_tip: 0   m_b: 0   m_side: 0   i_tip: 0   i_side: 0   p_side: 0thumb: 2   index: 1   middle: 18   ring: 18   pinky: 16 X: 293.65  Y: 35.54  Z: 295.14
r_side 0   m_tip: 0   m_b: 0   m_side: 0   i_tip: 0   i_side: 0   p_side: 0thumb: 2   index: 1   middle: 18   ring: 18   pinky: 16 X: 294.45  Y: 34.61  Z: 295.86
r_side 0   m_tip: 0   m_b: 0   m_side: 0   i_tip: 0   i_side: 0   p_side: 0thumb: 2   index: 1   middle: 18   ring: 18   pinky: 16 X: 294.51  Y: 33.77  Z: 295.87
r_side 0   m_tip: 0   m_b: 0   m_side: 0   i_tip: 0   i_side: 0   p_side: 0thumb: 2   index: 1   middle: 17   ring: 19   pinky: 16 X: 292.60  Y: 33.07  Z: 294.46
r_side 0   m_tip: 0   m_b: 0   m_side: 0   i_tip: 0   i_side: 0   p_side: 0thumb: 3   index: 0   middle: 17   ring: 18   pinky: 16 X: 291.83  Y: 33.52  Z: 294.14
r_side 0   m_tip: 0   m_b: 0   m_side: 0   i_tip: 0   i_side: 0   p_side: 0thumb: 2   index: 1   middle: 18   ring: 18   pinky: 16 X: 291.43  Y: 32.60  Z: 293.73
