juanmrq95/ee149_104/ASLsensing/longFlex/save_sensordata/test 1.1/testAashykLetterM.txt

_r_side 0   m_tip: 0   m_b: 0   m_side: 0   i_tip: 0   i_side: 0   p_side: 0thumb: 5   index: 1   middle: 2   ring: 2   pinky: 1 X: 358.96  Y: 0.92  Z: 1.30
r_side 0   m_tip: 0   m_b: 0   m_side: 0   i_tip: 0   i_side: 0   p_side: 0thumb: 6   index: 0   middle: 2   ring: 2   pinky: 1 X: 358.92  Y: 1.58  Z: 358.79
r_side 0   m_tip: 0   m_b: 0   m_side: 0   i_tip: 0   i_side: 0   p_side: 0thumb: 7   index: 1   middle: 2   ring: 2   pinky: 1 X: 358.92  Y: 2.36  Z: 356.43
r_side 0   m_tip: 0   m_b: 0   m_side: 0   i_tip: 0   i_side: 0   p_side: 0thumb: 7   index: 1   middle: 2   ring: 2   pinky: 1 X: 358.84  Y: 2.95  Z: 354.21
r_side 0   m_tip: 0   m_b: 0   m_side: 0   i_tip: 0   i_side: 0   p_side: 0thumb: 6   index: 0   middle: 2   ring: 2   pinky: 1 X: 358.61  Y: 3.92  Z: 352.42
r_side 0   m_tip: 0   m_b: 0   m_side: 0   i_tip: 0   i_side: 0   p_side: 0thumb: 6   index: 0   middle: 2   ring: 2   pinky: 2 X: 358.46  Y: 4.40  Z: 350.61
r_side 0   m_tip: 0   m_b: 0   m_side: 0   i_tip: 0   i_side: 0   p_side: 0thumb: 6   index: 0   middle: 2   ring: 2   pinky: 1 X: 358.37  Y: 5.03  Z: 348.86
r_side 0   m_tip: 0   m_b: 0   m_side: 0   i_tip: 0   i_side: 0   p_side: 0thumb: 7   index: 1   middle: 2   ring: 2   pinky: 1 X: 358.13  Y: 5.83  Z: 347.43
r_side 0   m_tip: 0   m_b: 0   m_side: 0   i_tip: 0   i_side: 0   p_side: 0thumb: 6   index: 0   middle: 2   ring: 2   pinky: 1 X: 358.13  Y: 6.20  Z: 346.11
r_side 0   m_tip: 0   m_b: 0   m_side: 0   i_tip: 0   i_side: 0   p_side: 0thumb: 7   index: 0   middle: 2   ring: 2   pinky: 1 X: 358.13  Y: 6.61  Z: 344.63
r_side 0   m_tip: 0   m_b: 0   m_side: 0   i_tip: 0   i_side: 0   p_side: 0thumb: 6   index: 0   middle: 2   ring: 2   pinky: 1 X: 358.21  Y: 7.05  Z: 343.43
r_side 0   m_tip: 0   m_b: 0   m_side: 0   i_tip: 0   i_side: 0   p_side: 0thumb: 6   index: 0   middle: 2   ring: 2   pinky: 0 X: 358.06  Y: 7.47  Z: 342.20
r_side 0   m_tip: 0   m_b: 0   m_side: 0   i_tip: 0   i_side: 0   p_side: 0thumb: 6   index: 0   middle: 2   ring: 2   pinky: 1 X: 357.89  Y: 8.02  Z: 341.12
r_side 0   m_tip: 0   m_b: 0   m_side: 0   i_tip: 0   i_side: 0   p_side: 0thumb: 7   index: 0   middle: 2   ring: 2   pinky: 1 X: 357.66  Y: 8.24  Z: 340.20
r_side 0   m_tip: 0   m_b: 0   m_side: 0   i_tip: 0   i_side: 0   p_side: 0thumb: 6   index: 0   middle: 2   ring: 2   pinky: 2 X: 357.60  Y: 8.40  Z: 339.25
r_side 0   m_tip: 0   m_b: 0   m_side: 0   i_tip: 0   i_side: 0   p_side: 0thumb: 6   index: 0   middle: 2   ring: 2   pinky: 1 X: 357.56  Y: 8.39  Z: 338.30
r_side 0   m_tip: 0   m_b: 0   m_side: 0   i_tip: 0   i_side: 0   p_side: 0thumb: 6   index: 0   middle: 2   ring: 2   pinky: 1 X: 357.61  Y: 8.64  Z: 337.01
r_side 0   m_tip: 0   m_b: 0   m_side: 0   i_tip: 0   i_side: 0   p_side: 0thumb: 6   index: 0   middle: 2   ring: 2   pinky: 1 X: 357.47  Y: 11.92  Z: 334.19
r_side 0   m_tip: 0   m_b: 0   m_side: 0   i_tip: 0   i_side: 0   p_side: 0thumb: 6   index: 1   middle: 2   ring: 2   pinky: 1 X: 352.07  Y: 21.47  Z: 330.58
r_side 0   m_tip: 0   m_b: 0   m_side: 0   i_tip: 0   i_side: 0   p_side: 0thumb: 7   index: 1   middle: 3   ring: 2   pinky: 2 X: 342.26  Y: 35.78  Z: 321.11
r_side 0   m_tip: 0   m_b: 0   m_side: 0   i_tip: 0   i_side: 0   p_side: 0thumb: 11   index: 2   middle: 3   ring: 2   pinky: 3 X: 340.56  Y: 43.80  Z: 322.59
r_side 0   m_tip: 0   m_b: 0   m_side: 0   i_tip: 0   i_side: 0   p_side: 1thumb: 15   index: 1   middle: 3   ring: 2   pinky: 11 X: 338.81  Y: 51.76  Z: 326.54
r_side 0   m_tip: 0   m_b: 0   m_side: 0   i_tip: 0   i_side: 0   p_side: 1thumb: 16   index: 2   middle: 3   ring: 12   pinky: 14 X: 328.49  Y: 61.33  Z: 319.67
r_side 0   m_tip: 0   m_b: 0   m_side: 0   i_tip: 0   i_side: 0   p_side: 1thumb: 17   index: 16   middle: 17   ring: 20   pinky: 17 X: 314.32  Y: 64.27  Z: 307.84
r_side 0   m_tip: 0   m_b: 0   m_side: 0   i_tip: 0   i_side: 0   p_side: 1thumb: 16   index: 17   middle: 18   ring: 21   pinky: 17 X: 305.15  Y: 66.01  Z: 300.18
r_side 0   m_tip: 0   m_b: 0   m_side: 0   i_tip: 0   i_side: 0   p_side: 1thumb: 17   index: 17   middle: 18   ring: 20   pinky: 16 X: 300.44  Y: 65.44  Z: 297.27
r_side 0   m_tip: 0   m_b: 0   m_side: 0   i_tip: 0   i_side: 0   p_side: 1thumb: 16   index: 17   middle: 17   ring: 20   pinky: 16 X: 279.44  Y: 65.57  Z: 282.77
r_side 0   m_tip: 0   m_b: 0   m_side: 0   i_tip: 0   i_side: 0   p_side: 1thumb: 16   index: 17   middle: 18   ring: 20   pinky: 16 X: 283.11  Y: 66.56  Z: 286.07
r_side 0   m_tip: 0   m_b: 0   m_side: 0   i_tip: 0   i_side: 0   p_side: 1thumb: 16   index: 16   middle: 17   ring: 19   pinky: 15 X: 287.32  Y: 66.15  Z: 288.75
r_side 0   m_tip: 0   m_b: 0   m_side: 0   i_tip: 0   i_side: 0   p_side: 1thumb: 17   index: 16   middle: 17   ring: 19   pinky: 15 X: 290.55  Y: 65.83  Z: 290.88
r_side 0   m_tip: 0   m_b: 0   m_side: 0   i_tip: 0   i_side: 0   p_side: 1thumb: 18   index: 16   middle: 17   ring: 19   pinky: 15 X: 293.79  Y: 64.86  Z: 293.48
r_side 0   m_tip: 0   m_b: 0   m_side: 0   i_tip: 0   i_side: 0   p_side: 1thumb: 18   index: 17   middle: 17   ring: 19   pinky: 15 X: 293.42  Y: 64.51  Z: 292.55
r_side 0   m_tip: 0   m_b: 0   m_side: 0   i_tip: 0   i_side: 0   p_side: 1thumb: 16   index: 16   middle: 16   ring: 19   pinky: 15 X: 292.78  Y: 64.58  Z: 292.10
r_side 0   m_tip: 0   m_b: 0   m_side: 0   i_tip: 0   i_side: 0   p_side: 1thumb: 16   index: 16   middle: 16   ring: 19   pinky: 15 X: 291.16  Y: 63.69  Z: 290.33
r_side 0   m_tip: 0   m_b: 0   m_side: 0   i_tip: 0   i_side: 0   p_side: 1thumb: 16   index: 16   middle: 16   ring: 18   pinky: 15 X: 293.99  Y: 62.23  Z: 292.47
r_side 0   m_tip: 0   m_b: 0   m_side: 0   i_tip: 0   i_side: 0   p_side: 1thumb: 16   index: 16   middle: 16   ring: 19   pinky: 15 X: 293.47  Y: 61.49  Z: 291.71
r_side 0   m_tip: 0   m_b: 0   m_side: 0   i_tip: 0   i_side: 0   p_side: 1thumb: 16   index: 16   middle: 16   ring: 18   pinky: 14 X: 293.30  Y: 60.51  Z: 291.83
r_side 0   m_tip: 0   m_b: 0   m_side: 0   i_tip: 0   i_side: 0   p_side: 1thumb: 16   index: 16   middle: 16   ring: 18   pinky: 14 X: 294.86  Y: 60.20  Z: 293.50
r_side 0   m_tip: 0   m_b: 0   m_side: 0   i_tip: 0   i_side: 0   p_side: 1thumb: 16   index: 16   middle: 16   ring: 18   pinky: 14 X: 294.97  Y: 59.30  Z: 293.59
r_side 0   m_tip: 0   m_b: 0   m_side: 0   i_tip: 0   i_side: 0   p_side: 1thumb: 16   index: 16   middle: 16   ring: 18   pinky: 14 X: 295.15  Y: 58.51  Z: 293.75
r_side 0   m_tip: 0   m_b: 0   m_side: 0   i_tip: 0   i_side: 0   p_side: 1thumb: 16   index: 15   middle: 16   ring: 18   pinky: 15 X: 295.49  Y: 57.05  Z: 294.00
r_side 0   m_tip: 0   m_b: 0   m_side: 0   i_tip: 0   i_side: 0   p_side: 1thumb: 15   index: 16   middle: 16   ring: 18   pinky: 15 X: 294.95  Y: 56.25  Z: 294.09
r_side 0   m_tip: 0   m_b: 0   m_side: 0   i_tip: 0   i_side: 0   p_side: 1thumb: 15   index: 16   middle: 16   ring: 18   pinky: 15 X: 294.60  Y: 55.91  Z: 293.66
r_side 0   m_tip: 0   m_b: 0   m_side: 0   i_tip: 0   i_side: 0   p_side: 1thumb: 16   index: 16   middle: 16   ring: 18   pinky: 15 X: 292.70  Y: 55.39  Z: 291.86
r_side 0   m_tip: 0   m_b: 0   m_side: 0   i_tip: 0   i_side: 0   p_side: 1thumb: 15   index: 16   middle: 16   ring: 18   pinky: 15 X: 293.08  Y: 54.84  Z: 291.99
r_side 0   m_tip: 0   m_b: 0   m_side: 0   i_tip: 0   i_side: 0   p_side: 1thumb: 15   index: 15   middle: 16   ring: 18   pinky: 15 X: 293.27  Y: 54.33  Z: 292.00
r_side 0   m_tip: 0   m_b: 0   m_side: 0   i_tip: 0   i_side: 0   p_side: 1thumb: 15   index: 15   middle: 16   ring: 18   pinky: 15 X: 294.29  Y: 53.34  Z: 292.73
r_side 0   m_tip: 0   m_b: 0   m_side: 0   i_tip: 0   i_side: 0   p_side: 1thumb: 15   index: 15   middle: 16   ring: 18   pinky: 15 X: 293.25  Y: 52.73  Z: 291.81
r_side 0   m_tip: 0   m_b: 0   m_side: 0   i_tip: 0   i_side: 0   p_side: 1thumb: 15   index: 15   middle: 16   ring: 18   pinky: 15 X: 292.43  Y: 51.99  Z: 291.18
r_side 0   m_tip: 0   m_b: 0   m_side: 0   i_tip: 0   i_side: 0   p_side: 1thumb: 16   index: 16   middle: 16   ring: 18   pinky: 15 X: 292.17  Y: 51.77  Z: 290.92
r_side 0   m_tip: 0   m_b: 0   m_side: 0   i_tip: 0   i_side: 0   p_side: 1thumb: 15   index: 15   middle: 16   ring: 18   pinky: 15 X: 291.39  Y: 51.48  Z: 290.42
r_side 0   m_tip: 0   m_b: 0   m_side: 0   i_tip: 0   i_side: 0   p_side: 1thumb: 15   index: 15   middle: 15   ring: 18   pinky: 15 X: 291.76  Y: 50.86  Z: 290.80
r_side 0   m_tip: 0   m_b: 0   m_side: 0   i_tip: 0   i_side: 0   p_side: 1thumb: 15   index: 15   middle: 16   ring: 18   pinky: 15 X: 292.12  Y: 50.32  Z: 290.93
r_side 0   m_tip: 0   m_b: 0   m_side: 0   i_tip: 0   i_side: 0   p_side: 1thumb: 15   index: 15   middle: 15   ring: 17   pinky: 15 X: 292.00  Y: 49.75  Z: 290.63
r_side 0   m_tip: 0   m_b: 0   m_side: 0   i_tip: 0   i_side: 0   p_side: 1thumb: 16   index: 15   middle: 15   ring: 18   pinky: 15 X: 291.56  Y: 48.97  Z: 290.31
r_side 0   m_tip: 0   m_b: 0   m_side: 0   i_tip: 0   i_side: 0   p_side: 1thumb: 14   index: 15   middle: 15   ring: 17   pinky: 15 X: 291.82  Y: 48.27  Z: 290.42
r_side 0   m_tip: 0   m_b: 0   m_side: 0   i_tip: 0   i_side: 0   p_side: 1thumb: 15   index: 16   middle: 15   ring: 17   pinky: 15 X: 290.83  Y: 47.92  Z: 289.03
r_side 0   m_tip: 0   m_b: 0   m_side: 0   i_tip: 0   i_side: 0   p_side: 1thumb: 15   index: 15   middle: 15   ring: 17   pinky: 15 X: 290.27  Y: 47.25  Z: 288.72
r_side 0   m_tip: 0   m_b: 0   m_side: 0   i_tip: 0   i_side: 0   p_side: 1thumb: 15   index: 15   middle: 15   ring: 17   pinky: 15 X: 289.86  Y: 46.60  Z: 288.30
r_side 0   m_tip: 0   m_b: 0   m_side: 0   i_tip: 0   i_side: 0   p_side: 1thumb: 15   index: 15   middle: 15   ring: 17   pinky: 15 X: 290.27  Y: 46.22  Z: 288.87
r_side 0   m_tip: 0   m_b: 0   m_side: 0   i_tip: 0   i_side: 0   p_side: 1thumb: 15   index: 15   middle: 15   ring: 17   pinky: 15 X: 290.45  Y: 45.23  Z: 289.17
