juanmrq95/ee149_104/ASLsensing/longFlex/save_sensordata/test 1.1/testAashykLetterN.txt

5ÿr_side 0   m_tip: 0   m_b: 0   m_side: 0   i_tip: 0   i_side: 0   p_side: 0thumb: 5   index: 0   middle: 2   ring: 2   pinky: 1 X: 0.79  Y: 0.91  Z: 359.88
r_side 0   m_tip: 0   m_b: 0   m_side: 0   i_tip: 0   i_side: 0   p_side: 0thumb: 5   index: 0   middle: 2   ring: 2   pinky: 1 X: 0.76  Y: 1.59  Z: 357.85
r_side 0   m_tip: 0   m_b: 0   m_side: 0   i_tip: 0   i_side: 0   p_side: 0thumb: 4   index: 0   middle: 2   ring: 1   pinky: 1 X: 0.67  Y: 3.24  Z: 356.02
r_side 0   m_tip: 0   m_b: 0   m_side: 0   i_tip: 0   i_side: 0   p_side: 0thumb: 5   index: 2   middle: 2   ring: 2   pinky: 1 X: 0.45  Y: 4.31  Z: 354.34
r_side 0   m_tip: 0   m_b: 0   m_side: 0   i_tip: 0   i_side: 0   p_side: 0thumb: 4   index: 0   middle: 2   ring: 2   pinky: 1 X: 0.59  Y: 4.89  Z: 352.50
r_side 0   m_tip: 0   m_b: 0   m_side: 0   i_tip: 0   i_side: 0   p_side: 0thumb: 4   index: 0   middle: 1   ring: 2   pinky: 1 X: 0.50  Y: 5.70  Z: 350.78
r_side 0   m_tip: 0   m_b: 0   m_side: 0   i_tip: 0   i_side: 0   p_side: 0thumb: 5   index: 0   middle: 3   ring: 1   pinky: 1 X: 0.42  Y: 6.77  Z: 349.05
r_side 0   m_tip: 0   m_b: 0   m_side: 0   i_tip: 0   i_side: 0   p_side: 0thumb: 4   index: 0   middle: 2   ring: 2   pinky: 1 X: 0.36  Y: 7.57  Z: 347.72
r_side 0   m_tip: 0   m_b: 0   m_side: 0   i_tip: 0   i_side: 0   p_side: 0thumb: 5   index: 0   middle: 2   ring: 2   pinky: 0 X: 0.42  Y: 8.08  Z: 346.45
r_side 0   m_tip: 0   m_b: 0   m_side: 0   i_tip: 0   i_side: 0   p_side: 0thumb: 5   index: 0   middle: 2   ring: 1   pinky: 1 X: 0.30  Y: 9.07  Z: 345.44
r_side 0   m_tip: 0   m_b: 0   m_side: 0   i_tip: 0   i_side: 0   p_side: 0thumb: 4   index: 0   middle: 2   ring: 2   pinky: 1 X: 0.27  Y: 9.42  Z: 344.27
r_side 0   m_tip: 0   m_b: 0   m_side: 0   i_tip: 0   i_side: 0   p_side: 0thumb: 5   index: 0   middle: 2   ring: 2   pinky: 1 X: 0.13  Y: 8.90  Z: 341.43
r_side 0   m_tip: 0   m_b: 0   m_side: 0   i_tip: 0   i_side: 0   p_side: 0thumb: 5   index: 0   middle: 2   ring: 2   pinky: 1 X: 355.17  Y: 23.34  Z: 340.96
r_side 0   m_tip: 0   m_b: 0   m_side: 0   i_tip: 0   i_side: 0   p_side: 0thumb: 5   index: 1   middle: 2   ring: 2   pinky: 1 X: 352.37  Y: 31.99  Z: 341.73
r_side 0   m_tip: 0   m_b: 0   m_side: 0   i_tip: 0   i_side: 0   p_side: 0thumb: 5   index: 1   middle: 2   ring: 3   pinky: 2 X: 350.65  Y: 40.71  Z: 346.23
r_side 0   m_tip: 0   m_b: 0   m_side: 0   i_tip: 0   i_side: 0   p_side: 0thumb: 10   index: 1   middle: 2   ring: 7   pinky: 10 X: 347.94  Y: 49.04  Z: 345.13
r_side 1   m_tip: 0   m_b: 0   m_side: 0   i_tip: 0   i_side: 0   p_side: 0thumb: 15   index: 1   middle: 3   ring: 15   pinky: 16 X: 342.62  Y: 54.29  Z: 339.28
r_side 1   m_tip: 0   m_b: 0   m_side: 0   i_tip: 0   i_side: 0   p_side: 0thumb: 16   index: 7   middle: 14   ring: 18   pinky: 16 X: 340.81  Y: 57.94  Z: 336.55
r_side 1   m_tip: 0   m_b: 0   m_side: 0   i_tip: 0   i_side: 0   p_side: 0thumb: 16   index: 17   middle: 20   ring: 20   pinky: 19 X: 335.72  Y: 66.57  Z: 331.83
r_side 1   m_tip: 0   m_b: 0   m_side: 0   i_tip: 0   i_side: 0   p_side: 0thumb: 17   index: 19   middle: 19   ring: 20   pinky: 20 X: 306.07  Y: 69.04  Z: 302.55
r_side 1   m_tip: 0   m_b: 0   m_side: 0   i_tip: 0   i_side: 0   p_side: 0thumb: 16   index: 18   middle: 19   ring: 20   pinky: 19 X: 279.29  Y: 67.34  Z: 277.38
r_side 1   m_tip: 0   m_b: 0   m_side: 0   i_tip: 0   i_side: 0   p_side: 0thumb: 16   index: 18   middle: 19   ring: 20   pinky: 18 X: 280.93  Y: 65.77  Z: 279.57
r_side 1   m_tip: 0   m_b: 0   m_side: 0   i_tip: 0   i_side: 0   p_side: 0thumb: 15   index: 18   middle: 18   ring: 19   pinky: 18 X: 279.52  Y: 65.09  Z: 277.80
r_side 1   m_tip: 0   m_b: 0   m_side: 0   i_tip: 0   i_side: 0   p_side: 0thumb: 15   index: 17   middle: 18   ring: 19   pinky: 18 X: 283.88  Y: 65.85  Z: 280.75
r_side 1   m_tip: 0   m_b: 0   m_side: 0   i_tip: 0   i_side: 0   p_side: 0thumb: 15   index: 17   middle: 18   ring: 19   pinky: 18 X: 283.31  Y: 67.79  Z: 279.66
r_side 1   m_tip: 0   m_b: 0   m_side: 0   i_tip: 0   i_side: 0   p_side: 0thumb: 15   index: 17   middle: 18   ring: 19   pinky: 18 X: 284.13  Y: 67.54  Z: 279.77
r_side 1   m_tip: 0   m_b: 0   m_side: 0   i_tip: 0   i_side: 0   p_side: 0thumb: 15   index: 17   middle: 18   ring: 19   pinky: 18 X: 282.59  Y: 68.37  Z: 278.52
r_side 1   m_tip: 0   m_b: 0   m_side: 0   i_tip: 0   i_side: 0   p_side: 0thumb: 14   index: 17   middle: 17   ring: 19   pinky: 18 X: 286.22  Y: 67.79  Z: 281.87
r_side 1   m_tip: 0   m_b: 0   m_side: 0   i_tip: 0   i_side: 0   p_side: 0thumb: 14   index: 17   middle: 17   ring: 19   pinky: 18 X: 286.86  Y: 67.65  Z: 282.54
r_side 1   m_tip: 0   m_b: 0   m_side: 0   i_tip: 0   i_side: 0   p_side: 0thumb: 14   index: 17   middle: 17   ring: 19   pinky: 18 X: 288.35  Y: 67.69  Z: 283.85
r_side 1   m_tip: 0   m_b: 0   m_side: 0   i_tip: 0   i_side: 0   p_side: 0thumb: 14   index: 17   middle: 17   ring: 19   pinky: 17 X: 289.32  Y: 67.08  Z: 284.41
r_side 1   m_tip: 0   m_b: 0   m_side: 0   i_tip: 0   i_side: 0   p_side: 0thumb: 14   index: 17   middle: 17   ring: 19   pinky: 17 X: 287.75  Y: 67.57  Z: 283.38
r_side 1   m_tip: 0   m_b: 0   m_side: 0   i_tip: 0   i_side: 0   p_side: 0thumb: 14   index: 17   middle: 17   ring: 19   pinky: 17 X: 286.12  Y: 67.64  Z: 282.09
r_side 1   m_tip: 0   m_b: 0   m_side: 0   i_tip: 0   i_side: 0   p_side: 0thumb: 14   index: 16   middle: 17   ring: 18   pinky: 17 X: 287.20  Y: 67.40  Z: 283.07
r_side 1   m_tip: 0   m_b: 0   m_side: 0   i_tip: 0   i_side: 0   p_side: 0thumb: 14   index: 16   middle: 17   ring: 18   pinky: 17 X: 285.78  Y: 66.56  Z: 281.50
r_side 1   m_tip: 0   m_b: 0   m_side: 0   i_tip: 0   i_side: 0   p_side: 0thumb: 14   index: 16   middle: 17   ring: 19   pinky: 17 X: 285.49  Y: 65.58  Z: 280.82
r_side 1   m_tip: 0   m_b: 0   m_side: 0   i_tip: 0   i_side: 0   p_side: 0thumb: 14   index: 16   middle: 17   ring: 18   pinky: 17 X: 285.13  Y: 64.80  Z: 280.21
r_side 1   m_tip: 0   m_b: 0   m_side: 0   i_tip: 0   i_side: 0   p_side: 0thumb: 14   index: 16   middle: 17   ring: 18   pinky: 17 X: 284.84  Y: 64.45  Z: 279.66
r_side 1   m_tip: 0   m_b: 0   m_side: 0   i_tip: 0   i_side: 0   p_side: 0thumb: 14   index: 16   middle: 17   ring: 18   pinky: 17 X: 284.76  Y: 63.31  Z: 279.49
r_side 1   m_tip: 0   m_b: 0   m_side: 0   i_tip: 0   i_side: 0   p_side: 0thumb: 14   index: 16   middle: 17   ring: 18   pinky: 17 X: 285.56  Y: 62.24  Z: 280.51
r_side 1   m_tip: 0   m_b: 0   m_side: 0   i_tip: 0   i_side: 0   p_side: 0thumb: 14   index: 16   middle: 17   ring: 18   pinky: 17 X: 285.75  Y: 61.27  Z: 280.64
r_side 1   m_tip: 0   m_b: 0   m_side: 0   i_tip: 0   i_side: 0   p_side: 0thumb: 14   index: 16   middle: 17   ring: 18   pinky: 17 X: 285.79  Y: 60.90  Z: 280.69
r_side 1   m_tip: 0   m_b: 0   m_side: 0   i_tip: 0   i_side: 0   p_side: 0thumb: 15   index: 16   middle: 17   ring: 18   pinky: 17 X: 285.68  Y: 60.37  Z: 280.61
r_side 1   m_tip: 0   m_b: 0   m_side: 0   i_tip: 0   i_side: 0   p_side: 0thumb: 14   index: 16   middle: 17   ring: 18   pinky: 17 X: 285.71  Y: 59.90  Z: 280.30
r_side 1   m_tip: 0   m_b: 0   m_side: 0   i_tip: 0   i_side: 0   p_side: 0thumb: 14   index: 16   middle: 17   ring: 18   pinky: 17 X: 286.34  Y: 59.16  Z: 280.77
r_side 1   m_tip: 0   m_b: 0   m_side: 0   i_tip: 0   i_side: 0   p_side: 0thumb: 14   index: 16   middle: 16   ring: 18   pinky: 17 X: 286.13  Y: 58.55  Z: 280.38
r_side 1   m_tip: 0   m_b: 0   m_side: 0   i_tip: 0   i_side: 0   p_side: 0thumb: 13   index: 16   middle: 17   ring: 18   pinky: 17 X: 287.76  Y: 58.21  Z: 281.75
r_side 1   m_tip: 0   m_b: 0   m_side: 0   i_tip: 0   i_side: 0   p_side: 0thumb: 14   index: 16   middle: 17   ring: 18   pinky: 17 X: 287.33  Y: 57.95  Z: 281.62
r_side 1   m_tip: 0   m_b: 0   m_side: 0   i_tip: 0   i_side: 0   p_side: 0thumb: 13   index: 16   middle: 16   ring: 18   pinky: 17 X: 287.19  Y: 57.39  Z: 281.35
r_side 1   m_tip: 0   m_b: 0   m_side: 0   i_tip: 0   i_side: 0   p_side: 0thumb: 13   index: 16   middle: 16   ring: 18   pinky: 17 X: 288.02  Y: 56.79  Z: 282.17
r_side 1   m_tip: 0   m_b: 0   m_side: 0   i_tip: 0   i_side: 0   p_side: 0thumb: 13   index: 16   middle: 16   ring: 18   pinky: 17 X: 287.98  Y: 56.25  Z: 282.03
r_side 1   m_tip: 0   m_b: 0   m_side: 0   i_tip: 0   i_side: 0   p_side: 0thumb: 13   index: 16   middle: 17   ring: 18   pinky: 17 X: 287.45  Y: 55.64  Z: 281.24
r_side 1   m_tip: 0   m_b: 0   m_side: 0   i_tip: 0   i_side: 0   p_side: 0thumb: 13   index: 16   middle: 16   ring: 18   pinky: 17 X: 287.41  Y: 54.27  Z: 281.32
r_side 1   m_tip: 0   m_b: 0   m_side: 0   i_tip: 0   i_side: 0   p_side: 0thumb: 14   index: 16   middle: 16   ring: 18   pinky: 17 X: 287.58  Y: 53.20  Z: 281.61
r_side 1   m_tip: 0   m_b: 0   m_side: 0   i_tip: 0   i_side: 0   p_side: 0thumb: 13   index: 16   middle: 16   ring: 18   pinky: 17 X: 288.57  Y: 52.50  Z: 282.68
r_side 1   m_tip: 0   m_b: 0   m_side: 0   i_tip: 0   i_side: 0   p_side: 0thumb: 13   index: 16   middle: 16   ring: 17   pinky: 17 X: 287.87  Y: 51.78  Z: 282.32
r_side 1   m_tip: 0   m_b: 0   m_side: 0   i_tip: 0   i_side: 0   p_side: 0thumb: 13   index: 16   middle: 16   ring: 18   pinky: 17 X: 287.78  Y: 52.04  Z: 282.34
r_side 1   m_tip: 0   m_b: 0   m_side: 0   i_tip: 0   i_side: 0   p_side: 0thumb: 13   index: 16   middle: 16   ring: 18   pinky: 17 X: 287.49  Y: 51.68  Z: 282.28
r_side 1   m_tip: 0   m_b: 0   m_side: 0   i_tip: 0   i_side: 0   p_side: 0thumb: 14   index: 15   middle: 16   ring: 17   pinky: 17 X: 287.41  Y: 51.06  Z: 281.83
r_side 1   m_tip: 0   m_b: 0   m_side: 0   i_tip: 0   i_side: 0   p_side: 0thumb: 13   index: 15   middle: 16   ring: 18   pinky: 17 X: 286.96  Y: 50.23  Z: 281.60
