juanmrq95/ee149_104/ASLsensing/longFlex/save_sensordata/test 1.1/testAashykLetterO.txt

r_side 0   m_tip: 0   m_b: 0   m_side: 0   i_tip: 0   i_side: 0   p_side: 0thumb: 5   index: 0   middle: 2   ring: 2   pinky: 1 X: 358.37  Y: 354.73  Z: 4.13
r_side 0   m_tip: 0   m_b: 0   m_side: 0   i_tip: 0   i_side: 0   p_side: 0thumb: 5   index: 0   middle: 2   ring: 2   pinky: 1 X: 358.22  Y: 356.32  Z: 1.32
r_side 0   m_tip: 0   m_b: 0   m_side: 0   i_tip: 0   i_side: 0   p_side: 0thumb: 6   index: 0   middle: 2   ring: 2   pinky: 1 X: 358.17  Y: 356.91  Z: 358.93
r_side 0   m_tip: 0   m_b: 0   m_side: 0   i_tip: 0   i_side: 0   p_side: 0thumb: 5   index: 0   middle: 2   ring: 2   pinky: 1 X: 358.15  Y: 357.43  Z: 356.18
r_side 0   m_tip: 0   m_b: 0   m_side: 0   i_tip: 0   i_side: 0   p_side: 0thumb: 5   index: 0   middle: 2   ring: 2   pinky: 1 X: 358.03  Y: 358.26  Z: 353.85
r_side 0   m_tip: 0   m_b: 0   m_side: 0   i_tip: 0   i_side: 0   p_side: 0thumb: 5   index: 0   middle: 2   ring: 1   pinky: 1 X: 357.98  Y: 358.96  Z: 351.74
r_side 0   m_tip: 0   m_b: 0   m_side: 0   i_tip: 0   i_side: 0   p_side: 0thumb: 5   index: 0   middle: 2   ring: 2   pinky: 1 X: 357.82  Y: 359.73  Z: 349.49
r_side 0   m_tip: 0   m_b: 0   m_side: 0   i_tip: 0   i_side: 0   p_side: 0thumb: 6   index: 0   middle: 2   ring: 2   pinky: 1 X: 357.63  Y: 0.59  Z: 347.62
r_side 0   m_tip: 0   m_b: 0   m_side: 0   i_tip: 0   i_side: 0   p_side: 0thumb: 6   index: 0   middle: 2   ring: 1   pinky: 1 X: 357.41  Y: 1.55  Z: 345.77
r_side 0   m_tip: 0   m_b: 0   m_side: 0   i_tip: 0   i_side: 0   p_side: 0thumb: 5   index: 0   middle: 2   ring: 1   pinky: 1 X: 357.17  Y: 2.06  Z: 344.24
r_side 0   m_tip: 0   m_b: 0   m_side: 0   i_tip: 0   i_side: 0   p_side: 0thumb: 4   index: 0   middle: 2   ring: 2   pinky: 1 X: 357.03  Y: 2.58  Z: 342.57
r_side 0   m_tip: 0   m_b: 0   m_side: 0   i_tip: 0   i_side: 0   p_side: 0thumb: 5   index: 0   middle: 2   ring: 2   pinky: 1 X: 356.74  Y: 3.26  Z: 341.23
r_side 0   m_tip: 0   m_b: 0   m_side: 0   i_tip: 0   i_side: 0   p_side: 0thumb: 6   index: 0   middle: 2   ring: 2   pinky: 1 X: 356.54  Y: 3.65  Z: 339.77
r_side 0   m_tip: 0   m_b: 0   m_side: 0   i_tip: 0   i_side: 0   p_side: 0thumb: 5   index: 0   middle: 2   ring: 2   pinky: 1 X: 356.64  Y: 4.43  Z: 338.68
r_side 0   m_tip: 0   m_b: 0   m_side: 0   i_tip: 0   i_side: 0   p_side: 0thumb: 5   index: 0   middle: 2   ring: 2   pinky: 1 X: 356.55  Y: 6.35  Z: 334.67
r_side 0   m_tip: 0   m_b: 0   m_side: 0   i_tip: 0   i_side: 0   p_side: 0thumb: 5   index: 1   middle: 2   ring: 2   pinky: 1 X: 353.89  Y: 12.54  Z: 332.03
r_side 0   m_tip: 0   m_b: 0   m_side: 0   i_tip: 0   i_side: 0   p_side: 0thumb: 6   index: 7   middle: 5   ring: 8   pinky: 1 X: 345.54  Y: 29.14  Z: 324.59
r_side 0   m_tip: 0   m_b: 0   m_side: 0   i_tip: 0   i_side: 0   p_side: 0thumb: 7   index: 11   middle: 10   ring: 12   pinky: 2 X: 335.37  Y: 42.04  Z: 317.01
r_side 0   m_tip: 0   m_b: 0   m_side: 0   i_tip: 0   i_side: 0   p_side: 0thumb: 10   index: 14   middle: 13   ring: 14   pinky: 3 X: 332.21  Y: 48.13  Z: 313.82
r_side 0   m_tip: 0   m_b: 0   m_side: 0   i_tip: 0   i_side: 0   p_side: 0thumb: 12   index: 15   middle: 12   ring: 12   pinky: 2 X: 327.06  Y: 51.29  Z: 310.14
r_side 0   m_tip: 0   m_b: 0   m_side: 0   i_tip: 1   i_side: 0   p_side: 0thumb: 13   index: 14   middle: 11   ring: 12   pinky: 3 X: 325.11  Y: 50.45  Z: 308.52
r_side 0   m_tip: 0   m_b: 0   m_side: 0   i_tip: 1   i_side: 0   p_side: 0thumb: 13   index: 14   middle: 10   ring: 12   pinky: 2 X: 323.51  Y: 50.28  Z: 307.55
r_side 0   m_tip: 0   m_b: 0   m_side: 0   i_tip: 1   i_side: 0   p_side: 0thumb: 12   index: 14   middle: 11   ring: 12   pinky: 3 X: 325.61  Y: 47.95  Z: 309.39
r_side 0   m_tip: 0   m_b: 0   m_side: 0   i_tip: 1   i_side: 0   p_side: 0thumb: 11   index: 14   middle: 13   ring: 15   pinky: 4 X: 324.87  Y: 46.98  Z: 309.72
r_side 0   m_tip: 0   m_b: 0   m_side: 0   i_tip: 1   i_side: 0   p_side: 0thumb: 11   index: 14   middle: 15   ring: 17   pinky: 5 X: 322.87  Y: 47.00  Z: 308.45
r_side 0   m_tip: 0   m_b: 0   m_side: 0   i_tip: 1   i_side: 0   p_side: 0thumb: 11   index: 13   middle: 15   ring: 16   pinky: 5 X: 319.01  Y: 48.52  Z: 305.40
r_side 0   m_tip: 0   m_b: 0   m_side: 0   i_tip: 1   i_side: 0   p_side: 0thumb: 11   index: 13   middle: 14   ring: 16   pinky: 8 X: 317.82  Y: 47.78  Z: 304.12
r_side 0   m_tip: 0   m_b: 0   m_side: 0   i_tip: 1   i_side: 0   p_side: 0thumb: 11   index: 13   middle: 14   ring: 16   pinky: 8 X: 314.57  Y: 48.06  Z: 301.43
r_side 0   m_tip: 0   m_b: 0   m_side: 0   i_tip: 1   i_side: 0   p_side: 0thumb: 11   index: 13   middle: 14   ring: 16   pinky: 8 X: 313.44  Y: 48.57  Z: 300.91
r_side 0   m_tip: 0   m_b: 0   m_side: 1   i_tip: 1   i_side: 0   p_side: 0thumb: 11   index: 13   middle: 14   ring: 15   pinky: 8 X: 308.93  Y: 50.25  Z: 296.65
r_side 0   m_tip: 0   m_b: 0   m_side: 0   i_tip: 1   i_side: 0   p_side: 0thumb: 12   index: 13   middle: 14   ring: 15   pinky: 8 X: 304.20  Y: 51.37  Z: 292.80
r_side 0   m_tip: 0   m_b: 0   m_side: 0   i_tip: 1   i_side: 0   p_side: 0thumb: 12   index: 13   middle: 14   ring: 15   pinky: 8 X: 303.46  Y: 50.97  Z: 292.54
r_side 0   m_tip: 0   m_b: 0   m_side: 0   i_tip: 1   i_side: 0   p_side: 0thumb: 12   index: 12   middle: 13   ring: 15   pinky: 7 X: 303.40  Y: 51.24  Z: 293.17
r_side 0   m_tip: 0   m_b: 0   m_side: 0   i_tip: 1   i_side: 0   p_side: 0thumb: 12   index: 12   middle: 13   ring: 15   pinky: 8 X: 302.51  Y: 50.42  Z: 291.94
r_side 0   m_tip: 0   m_b: 0   m_side: 0   i_tip: 1   i_side: 0   p_side: 0thumb: 12   index: 12   middle: 13   ring: 15   pinky: 8 X: 302.06  Y: 50.18  Z: 291.79
r_side 0   m_tip: 0   m_b: 0   m_side: 0   i_tip: 1   i_side: 0   p_side: 0thumb: 12   index: 12   middle: 13   ring: 15   pinky: 8 X: 301.53  Y: 49.73  Z: 291.63
r_side 0   m_tip: 0   m_b: 0   m_side: 0   i_tip: 1   i_side: 0   p_side: 0thumb: 12   index: 12   middle: 13   ring: 15   pinky: 8 X: 301.33  Y: 48.95  Z: 291.64
r_side 0   m_tip: 0   m_b: 0   m_side: 0   i_tip: 1   i_side: 0   p_side: 0thumb: 12   index: 12   middle: 13   ring: 14   pinky: 8 X: 300.84  Y: 47.75  Z: 290.91
r_side 0   m_tip: 0   m_b: 0   m_side: 0   i_tip: 1   i_side: 0   p_side: 0thumb: 12   index: 12   middle: 13   ring: 15   pinky: 7 X: 300.09  Y: 46.92  Z: 290.49
r_side 0   m_tip: 0   m_b: 0   m_side: 0   i_tip: 1   i_side: 0   p_side: 0thumb: 12   index: 12   middle: 13   ring: 15   pinky: 7 X: 299.58  Y: 46.12  Z: 290.12
r_side 0   m_tip: 0   m_b: 0   m_side: 0   i_tip: 1   i_side: 0   p_side: 0thumb: 12   index: 12   middle: 13   ring: 14   pinky: 7 X: 299.13  Y: 45.67  Z: 289.96
r_side 0   m_tip: 0   m_b: 0   m_side: 0   i_tip: 1   i_side: 0   p_side: 0thumb: 11   index: 12   middle: 13   ring: 14   pinky: 7 X: 298.77  Y: 44.82  Z: 289.80
r_side 0   m_tip: 0   m_b: 0   m_side: 1   i_tip: 1   i_side: 0   p_side: 0thumb: 12   index: 12   middle: 12   ring: 15   pinky: 7 X: 298.87  Y: 43.89  Z: 289.95
r_side 0   m_tip: 0   m_b: 0   m_side: 1   i_tip: 1   i_side: 0   p_side: 0thumb: 12   index: 12   middle: 13   ring: 15   pinky: 7 X: 298.65  Y: 42.94  Z: 289.87
r_side 0   m_tip: 0   m_b: 0   m_side: 1   i_tip: 1   i_side: 0   p_side: 0thumb: 12   index: 12   middle: 13   ring: 14   pinky: 7 X: 298.85  Y: 42.19  Z: 290.18
r_side 0   m_tip: 0   m_b: 0   m_side: 1   i_tip: 1   i_side: 0   p_side: 0thumb: 12   index: 12   middle: 13   ring: 14   pinky: 7 X: 298.61  Y: 41.30  Z: 289.89
r_side 0   m_tip: 0   m_b: 0   m_side: 1   i_tip: 1   i_side: 0   p_side: 0thumb: 12   index: 12   middle: 13   ring: 14   pinky: 7 X: 298.56  Y: 40.61  Z: 289.73
r_side 0   m_tip: 0   m_b: 0   m_side: 1   i_tip: 1   i_side: 0   p_side: 0thumb: 11   index: 12   middle: 13   ring: 14   pinky: 7 X: 298.47  Y: 39.94  Z: 289.58
r_side 0   m_tip: 0   m_b: 0   m_side: 1   i_tip: 1   i_side: 0   p_side: 0thumb: 11   index: 12   middle: 13   ring: 14   pinky: 7 X: 298.60  Y: 39.28  Z: 289.73
r_side 0   m_tip: 0   m_b: 0   m_side: 1   i_tip: 1   i_side: 0   p_side: 0thumb: 11   index: 12   middle: 13   ring: 14   pinky: 7 X: 298.22  Y: 38.78  Z: 289.41
r_side 0   m_tip: 0   m_b: 0   m_side: 1   i_tip: 1   i_side: 0   p_side: 0thumb: 11   index: 12   middle: 13   ring: 14   pinky: 7 X: 297.89  Y: 38.46  Z: 289.36
r_side 0   m_tip: 0   m_b: 0   m_side: 1   i_tip: 1   i_side: 0   p_side: 0thumb: 11   index: 12   middle: 13   ring: 14   pinky: 7 X: 297.83  Y: 37.42  Z: 289.01
r_side 0   m_tip: 0   m_b: 0   m_side: 1   i_tip: 1   i_side: 0   p_side: 0thumb: 11   index: 12   middle: 13   ring: 14   pinky: 7 X: 297.67  Y: 37.06  Z: 289.21
r_side 0   m_tip: 0   m_b: 0   m_side: 1   i_tip: 1   i_side: 0   p_side: 0thumb: 12   index: 12   middle: 13   ring: 14   pinky: 7 X: 297.15  Y: 36.64  Z: 289.07
r_side 0   m_tip: 0   m_b: 0   m_side: 1   i_tip: 1   i_side: 0   p_side: 0thumb: 11   index: 12   middle: 13   ring: 14   pinky: 7 X: 297.30  Y: 36.08  Z: 289.27
r_side 0   m_tip: 0   m_b: 0   m_side: 1   i_tip: 1   i_side: 0   p_side: 0thumb: 11   index: 12   middle: 13   ring: 14   pinky: 7 X: 297.13  Y: 35.49  Z: 289.28
r_side 0   m_tip: 0   m_b: 0   m_side: 1   i_tip: 1   i_side: 0   p_side: 0thumb: 11   index: 12   middle: 13   ring: 14   pinky: 7 X: 297.12  Y: 34.82  Z: 289.17
r_side 0   m_tip: 0   m_b: 0   m_side: 1   i_tip: 1   i_side: 0   p_side: 0thumb: 11   index: 12   middle: 13   ring: 14   pinky: 7 X: 297.16  Y: 33.76  Z: 289.04
r_side 0   m_tip: 0   m_b: 0   m_side: 0   i_tip: 1   i_side: 0   p_side: 0thumb: 11   index: 12   middle: 12   ring: 14   pinky: 7 X: 297.15  Y: 32.69  Z: 288.79
r_side 0   m_tip: 0   m_b: 0   m_side: 0   i_tip: 1   i_side: 0   p_side: 0thumb: 11   index: 11   middle: 12   ring: 14   pinky: 7 X: 297.56  Y: 32.18  Z: 289.48
