juanmrq95/ee149_104/ASLsensing/longFlex/save_sensordata/test 1.1/testAashykLetterP.txt

ûr_side 0   m_tip: 0   m_b: 0   m_side: 0   i_tip: 0   i_side: 0   p_side: 0thumb: 7   index: 0   middle: 2   ring: 2   pinky: 1 X: 0.65  Y: 0.65  Z: 359.74
r_side 0   m_tip: 0   m_b: 0   m_side: 0   i_tip: 0   i_side: 0   p_side: 0thumb: 7   index: 0   middle: 2   ring: 1   pinky: 1 X: 0.55  Y: 2.01  Z: 357.64
r_side 0   m_tip: 0   m_b: 0   m_side: 0   i_tip: 0   i_side: 0   p_side: 0thumb: 7   index: 0   middle: 2   ring: 2   pinky: 1 X: 0.50  Y: 2.96  Z: 355.39
r_side 0   m_tip: 0   m_b: 0   m_side: 0   i_tip: 0   i_side: 0   p_side: 0thumb: 7   index: 0   middle: 2   ring: 1   pinky: 1 X: 0.33  Y: 4.02  Z: 353.53
r_side 0   m_tip: 0   m_b: 0   m_side: 0   i_tip: 0   i_side: 0   p_side: 0thumb: 7   index: 0   middle: 2   ring: 2   pinky: 1 X: 0.31  Y: 4.66  Z: 351.70
r_side 0   m_tip: 0   m_b: 0   m_side: 0   i_tip: 0   i_side: 0   p_side: 0thumb: 7   index: 0   middle: 2   ring: 2   pinky: 1 X: 0.18  Y: 5.22  Z: 350.06
r_side 0   m_tip: 0   m_b: 0   m_side: 0   i_tip: 0   i_side: 0   p_side: 0thumb: 7   index: 0   middle: 2   ring: 1   pinky: 1 X: 0.10  Y: 5.90  Z: 348.29
r_side 0   m_tip: 0   m_b: 0   m_side: 0   i_tip: 0   i_side: 0   p_side: 0thumb: 7   index: 0   middle: 2   ring: 2   pinky: 1 X: 357.46  Y: 10.12  Z: 339.59
r_side 0   m_tip: 0   m_b: 0   m_side: 0   i_tip: 0   i_side: 0   p_side: 0thumb: 7   index: 0   middle: 2   ring: 12   pinky: 4 X: 354.44  Y: 12.18  Z: 342.25
r_side 0   m_tip: 0   m_b: 0   m_side: 0   i_tip: 0   i_side: 0   p_side: 0thumb: 6   index: 0   middle: 3   ring: 20   pinky: 18 X: 357.02  Y: 13.68  Z: 343.95
r_side 0   m_tip: 0   m_b: 0   m_side: 0   i_tip: 0   i_side: 0   p_side: 0thumb: 7   index: 0   middle: 2   ring: 19   pinky: 17 X: 358.00  Y: 3.86  Z: 348.91
r_side 0   m_tip: 0   m_b: 0   m_side: 0   i_tip: 0   i_side: 0   p_side: 0thumb: 6   index: 0   middle: 15   ring: 19   pinky: 15 X: 355.44  Y: 6.78  Z: 345.39
r_side 0   m_tip: 0   m_b: 0   m_side: 0   i_tip: 0   i_side: 0   p_side: 0thumb: 6   index: 0   middle: 13   ring: 18   pinky: 15 X: 349.48  Y: 8.03  Z: 341.57
r_side 0   m_tip: 0   m_b: 0   m_side: 0   i_tip: 0   i_side: 0   p_side: 0thumb: 9   index: 0   middle: 12   ring: 18   pinky: 15 X: 348.08  Y: 9.14  Z: 341.62
r_side 0   m_tip: 0   m_b: 0   m_side: 0   i_tip: 0   i_side: 0   p_side: 0thumb: 10   index: 0   middle: 13   ring: 18   pinky: 14 X: 345.49  Y: 8.92  Z: 339.39
r_side 0   m_tip: 0   m_b: 0   m_side: 0   i_tip: 0   i_side: 0   p_side: 0thumb: 11   index: 0   middle: 12   ring: 17   pinky: 13 X: 345.37  Y: 10.17  Z: 337.26
r_side 0   m_tip: 0   m_b: 0   m_side: 0   i_tip: 0   i_side: 0   p_side: 0thumb: 12   index: 0   middle: 14   ring: 17   pinky: 14 X: 346.93  Y: 10.48  Z: 340.77
r_side 0   m_tip: 0   m_b: 0   m_side: 1   i_tip: 1   i_side: 0   p_side: 0thumb: 15   index: 0   middle: 15   ring: 17   pinky: 14 X: 345.52  Y: 10.17  Z: 341.21
r_side 0   m_tip: 0   m_b: 0   m_side: 1   i_tip: 1   i_side: 0   p_side: 0thumb: 14   index: 0   middle: 15   ring: 17   pinky: 14 X: 345.57  Y: 5.84  Z: 340.85
r_side 0   m_tip: 0   m_b: 0   m_side: 1   i_tip: 1   i_side: 0   p_side: 0thumb: 11   index: 0   middle: 15   ring: 18   pinky: 14 X: 345.17  Y: 7.81  Z: 339.95
r_side 0   m_tip: 0   m_b: 0   m_side: 1   i_tip: 1   i_side: 0   p_side: 0thumb: 11   index: 0   middle: 15   ring: 17   pinky: 14 X: 345.34  Y: 7.31  Z: 339.98
r_side 0   m_tip: 0   m_b: 0   m_side: 1   i_tip: 1   i_side: 0   p_side: 0thumb: 10   index: 0   middle: 15   ring: 17   pinky: 14 X: 345.14  Y: 7.77  Z: 339.49
r_side 0   m_tip: 0   m_b: 0   m_side: 1   i_tip: 1   i_side: 0   p_side: 0thumb: 10   index: 0   middle: 15   ring: 17   pinky: 14 X: 345.37  Y: 7.48  Z: 339.33
r_side 0   m_tip: 0   m_b: 0   m_side: 1   i_tip: 1   i_side: 0   p_side: 0thumb: 10   index: 0   middle: 15   ring: 17   pinky: 14 X: 345.33  Y: 7.19  Z: 338.47
r_side 0   m_tip: 0   m_b: 0   m_side: 1   i_tip: 1   i_side: 0   p_side: 0thumb: 10   index: 0   middle: 14   ring: 17   pinky: 14 X: 345.02  Y: 7.83  Z: 337.66
r_side 0   m_tip: 0   m_b: 1   m_side: 1   i_tip: 1   i_side: 0   p_side: 0thumb: 10   index: 0   middle: 9   ring: 17   pinky: 14 X: 345.28  Y: 8.05  Z: 338.18
r_side 0   m_tip: 0   m_b: 1   m_side: 1   i_tip: 1   i_side: 0   p_side: 0thumb: 9   index: 0   middle: 8   ring: 17   pinky: 14 X: 344.86  Y: 10.72  Z: 337.66
r_side 0   m_tip: 0   m_b: 1   m_side: 1   i_tip: 1   i_side: 0   p_side: 0thumb: 9   index: 0   middle: 7   ring: 17   pinky: 14 X: 344.81  Y: 9.95  Z: 338.17
r_side 0   m_tip: 0   m_b: 1   m_side: 1   i_tip: 1   i_side: 0   p_side: 0thumb: 9   index: 0   middle: 8   ring: 16   pinky: 14 X: 345.20  Y: 8.73  Z: 337.72
r_side 0   m_tip: 0   m_b: 1   m_side: 1   i_tip: 1   i_side: 0   p_side: 0thumb: 9   index: 0   middle: 7   ring: 16   pinky: 14 X: 343.81  Y: 12.01  Z: 336.42
r_side 0   m_tip: 0   m_b: 1   m_side: 1   i_tip: 1   i_side: 0   p_side: 0thumb: 9   index: 0   middle: 7   ring: 16   pinky: 14 X: 345.03  Y: 10.11  Z: 337.07
r_side 0   m_tip: 0   m_b: 1   m_side: 1   i_tip: 1   i_side: 0   p_side: 0thumb: 9   index: 0   middle: 7   ring: 16   pinky: 14 X: 345.11  Y: 12.03  Z: 336.96
r_side 0   m_tip: 0   m_b: 1   m_side: 1   i_tip: 1   i_side: 0   p_side: 0thumb: 9   index: 0   middle: 7   ring: 16   pinky: 14 X: 345.77  Y: 8.90  Z: 337.79
r_side 0   m_tip: 0   m_b: 1   m_side: 1   i_tip: 1   i_side: 0   p_side: 0thumb: 9   index: 0   middle: 7   ring: 16   pinky: 14 X: 345.12  Y: 10.12  Z: 337.03
r_side 0   m_tip: 0   m_b: 1   m_side: 1   i_tip: 1   i_side: 0   p_side: 0thumb: 9   index: 0   middle: 7   ring: 16   pinky: 14 X: 345.71  Y: 9.34  Z: 337.75
r_side 0   m_tip: 0   m_b: 1   m_side: 1   i_tip: 1   i_side: 0   p_side: 0thumb: 8   index: 0   middle: 7   ring: 16   pinky: 14 X: 346.03  Y: 9.06  Z: 337.99
r_side 0   m_tip: 0   m_b: 1   m_side: 1   i_tip: 1   i_side: 0   p_side: 0thumb: 9   index: 0   middle: 7   ring: 16   pinky: 14 X: 345.37  Y: 9.48  Z: 336.90
r_side 0   m_tip: 0   m_b: 1   m_side: 1   i_tip: 1   i_side: 0   p_side: 0thumb: 9   index: 0   middle: 7   ring: 16   pinky: 14 X: 345.16  Y: 10.15  Z: 336.56
r_side 0   m_tip: 0   m_b: 1   m_side: 1   i_tip: 1   i_side: 0   p_side: 0thumb: 9   index: 0   middle: 7   ring: 16   pinky: 14 X: 345.95  Y: 9.15  Z: 337.87
r_side 0   m_tip: 0   m_b: 1   m_side: 1   i_tip: 1   i_side: 0   p_side: 0thumb: 9   index: 0   middle: 7   ring: 16   pinky: 14 X: 344.92  Y: 10.27  Z: 336.69
r_side 0   m_tip: 0   m_b: 1   m_side: 1   i_tip: 1   i_side: 0   p_side: 0thumb: 9   index: 0   middle: 7   ring: 16   pinky: 14 X: 344.92  Y: 10.34  Z: 336.22
r_side 0   m_tip: 0   m_b: 1   m_side: 1   i_tip: 1   i_side: 0   p_side: 0thumb: 9   index: 0   middle: 7   ring: 16   pinky: 13 X: 345.66  Y: 9.42  Z: 337.11
r_side 0   m_tip: 0   m_b: 1   m_side: 1   i_tip: 1   i_side: 0   p_side: 0thumb: 9   index: 0   middle: 7   ring: 16   pinky: 14 X: 345.55  Y: 9.66  Z: 337.65
r_side 0   m_tip: 0   m_b: 1   m_side: 1   i_tip: 1   i_side: 0   p_side: 0thumb: 9   index: 0   middle: 7   ring: 16   pinky: 14 X: 344.94  Y: 10.20  Z: 336.39
r_side 0   m_tip: 0   m_b: 1   m_side: 1   i_tip: 1   i_side: 0   p_side: 0thumb: 8   index: 0   middle: 7   ring: 16   pinky: 14 X: 345.38  Y: 8.46  Z: 336.75
r_side 0   m_tip: 0   m_b: 1   m_side: 1   i_tip: 1   i_side: 0   p_side: 0thumb: 8   index: 0   middle: 7   ring: 16   pinky: 14 X: 345.52  Y: 8.65  Z: 337.22
r_side 0   m_tip: 0   m_b: 1   m_side: 1   i_tip: 1   i_side: 0   p_side: 0thumb: 8   index: 0   middle: 7   ring: 16   pinky: 14 X: 345.17  Y: 10.16  Z: 336.93
r_side 0   m_tip: 0   m_b: 1   m_side: 1   i_tip: 1   i_side: 0   p_side: 0thumb: 8   index: 0   middle: 7   ring: 16   pinky: 14 X: 345.38  Y: 10.12  Z: 337.01
r_side 0   m_tip: 0   m_b: 1   m_side: 1   i_tip: 1   i_side: 0   p_side: 0thumb: 8   index: 0   middle: 7   ring: 16   pinky: 14 X: 345.30  Y: 9.60  Z: 336.91
r_side 0   m_tip: 0   m_b: 1   m_side: 1   i_tip: 1   i_side: 0   p_side: 0thumb: 8   index: 0   middle: 7   ring: 16   pinky: 14 X: 345.42  Y: 9.74  Z: 336.98
r_side 0   m_tip: 0   m_b: 1   m_side: 1   i_tip: 1   i_side: 0   p_side: 0thumb: 8   index: 0   middle: 7   ring: 16   pinky: 14 X: 345.37  Y: 10.39  Z: 336.82
r_side 0   m_tip: 0   m_b: 1   m_side: 1   i_tip: 1   i_side: 0   p_side: 0thumb: 8   index: 0   middle: 7   ring: 16   pinky: 14 X: 345.53  Y: 10.21  Z: 336.84
r_side 0   m_tip: 0   m_b: 1   m_side: 1   i_tip: 1   i_side: 0   p_side: 0thumb: 8   index: 0   middle: 7   ring: 16   pinky: 14 X: 345.63  Y: 9.77  Z: 336.81
r_side 0   m_tip: 0   m_b: 1   m_side: 1   i_tip: 1   i_side: 0   p_side: 0thumb: 8   index: 0   middle: 7   ring: 16   pinky: 14 X: 345.39  Y: 8.67  Z: 337.22
r_side 0   m_tip: 0   m_b: 1   m_side: 1   i_tip: 1   i_side: 0   p_side: 0thumb: 8   index: 0   middle: 7   ring: 16   pinky: 14 X: 345.94  Y: 7.02  Z: 336.93
r_side 0   m_tip: 0   m_b: 1   m_side: 1   i_tip: 1   i_side: 0   p_side: 0thumb: 8   index: 0   middle: 7   ring: 16   pinky: 14 X: 346.23  Y: 5.49  Z: 336.57
r_side 0   m_tip: 0   m_b: 1   m_side: 1   i_tip: 1   i_side: 0   p_side: 0thumb: 9   index: 0   middle: 7   ring: 16   pinky: 14 X: 346.00  Y: 6.48  Z: 336.51
r_side 0   m_tip: 0   m_b: 1   m_side: 1   i_tip: 1   i_side: 0   p_side: 0thumb: 8   index: 0   middle: 7   ring: 16   pinky: 14 X: 345.82  Y: 6.95  Z: 336.94
r_side 0   m_tip: 0   m_b: 1   m_side: 1   i_tip: 1   i_side: 0   p_side: 0thumb: 8   index: 0   middle: 7   ring: 16   pinky: 14 X: 346.13  Y: 6.60  Z: 337.70
r_side 0   m_tip: 0   m_b: 1   m_side: 1   i_tip: 1   i_side: 0   p_side: 0thumb: 8   index: 0   middle: 7   ring: 16   pinky: 14 X: 345.87  Y: 7.78  Z: 337.92
r_side 0   m_tip: 0   m_b: 1   m_side: 1   i_tip: 1   i_side: 0   p_side: 0thumb: 8   index: 0   middle: 7   ring: 16   pinky: 14 X: 345.89  Y: 7.78  Z: 338.03
r_side 0   m_tip: 0   m_b: 1   m_side: 1   i_tip: 1   i_side: 0   p_side: 0thumb: 8   index: 0   middle: 7   ring: 15   pinky: 13 X: 345.49  Y: 7.74  Z: 337.51
r_side 0   m_tip: 0   m_b: 1   m_side: 1   i_tip: 1   i_side: 0   p_side: 0thumb: 8   index: 0   middle: 7   ring: 15   pinky: 13 X: 345.91  Y: 6.68  Z: 337.45
r_side 0   m_tip: 0   m_b: 1   m_side: 1   i_tip: 1   i_side: 0   p_side: 0thumb: 8   index: 0   middle: 7   ring: 16   pinky: 13 X: 346.42  Y: 5.32  Z: 337.50
r_side 0   m_tip: 0   m_b: 1   m_side: 1   i_tip: 1   i_side: 0   p_side: 0thumb: 8   index: 0   middle: 7   ring: 15   pinky: 13 X: 346.76  Y: 4.12  Z: 338.30
r_side 0   m_tip: 0   m_b: 1   m_side: 1   i_tip: 1   i_side: 0   p_side: 0thumb: 8   index: 0   middle: 7   ring: 15   pinky: 13 X: 346.49  Y: 4.05  Z: 339.11
r_side 0   m_tip: 0   m_b: 1   m_side: 1   i_tip: 1   i_side: 0   p_side: 0thumb: 8   index: 0   middle: 7   ring: 15   pinky: 13 X: 346.90  Y: 3.69  Z: 339.29
r_side 0   m_tip: 0   m_b: 1   m_side: 1   i_tip: 1   i_side: 0   p_side: 0thumb: 8   index: 0   middle: 7   ring: 15   pinky: 13 X: 346.46  Y: 3.23  Z: 339.70
r_side 0   m_tip: 0   m_b: 1   m_side: 1   i_tip: 1   i_side: 0   p_side: 0thumb: 8   index: 0   middle: 7   ring: 16   pinky: 14 X: 346.13  Y: 2.92  Z: 339.27
r_side 0   m_tip: 0   m_b: 1   m_side: 1   i_tip: 1   i_side: 0   p_side: 0thumb: 8   index: 0   middle: 7   ring: 15   pinky: 14 X: 346.37  Y: 3.50  Z: 339.72
