juanmrq95/ee149_104/ASLsensing/longFlex/save_sensordata/test 1.1/testAashykLetterQ.txt

r_side 0   m_tip: 0   m_b: 0   m_side: 0   i_tip: 0   i_side: 0   p_side: 0thumb: 3   index: 1   middle: 2   ring: 2   pinky: 2 X: 359.74  Y: 0.00  Z: 0.13
r_side 0   m_tip: 0   m_b: 0   m_side: 0   i_tip: 0   i_side: 0   p_side: 0thumb: 3   index: 0   middle: 3   ring: 2   pinky: 2 X: 359.69  Y: 1.03  Z: 357.97
r_side 0   m_tip: 0   m_b: 0   m_side: 0   i_tip: 0   i_side: 0   p_side: 0thumb: 3   index: 0   middle: 3   ring: 2   pinky: 2 X: 359.62  Y: 2.52  Z: 355.83
r_side 0   m_tip: 0   m_b: 0   m_side: 0   i_tip: 0   i_side: 0   p_side: 0thumb: 3   index: 0   middle: 2   ring: 2   pinky: 2 X: 359.49  Y: 3.46  Z: 353.88
r_side 0   m_tip: 0   m_b: 0   m_side: 0   i_tip: 0   i_side: 0   p_side: 0thumb: 3   index: 0   middle: 2   ring: 2   pinky: 2 X: 359.29  Y: 4.55  Z: 352.02
r_side 0   m_tip: 0   m_b: 0   m_side: 0   i_tip: 0   i_side: 0   p_side: 0thumb: 3   index: 0   middle: 3   ring: 2   pinky: 2 X: 359.16  Y: 5.26  Z: 349.86
r_side 0   m_tip: 0   m_b: 0   m_side: 0   i_tip: 0   i_side: 0   p_side: 0thumb: 3   index: 0   middle: 2   ring: 2   pinky: 2 X: 359.01  Y: 6.23  Z: 347.87
r_side 0   m_tip: 0   m_b: 0   m_side: 0   i_tip: 0   i_side: 0   p_side: 0thumb: 3   index: 0   middle: 3   ring: 2   pinky: 2 X: 358.77  Y: 7.37  Z: 346.41
r_side 0   m_tip: 0   m_b: 0   m_side: 0   i_tip: 0   i_side: 0   p_side: 0thumb: 5   index: 0   middle: 2   ring: 2   pinky: 2 X: 358.61  Y: 8.15  Z: 344.89
r_side 0   m_tip: 0   m_b: 0   m_side: 0   i_tip: 0   i_side: 0   p_side: 0thumb: 2   index: 0   middle: 2   ring: 2   pinky: 2 X: 358.76  Y: 8.95  Z: 340.35
r_side 0   m_tip: 0   m_b: 0   m_side: 0   i_tip: 0   i_side: 0   p_side: 0thumb: 3   index: 0   middle: 2   ring: 2   pinky: 2 X: 358.33  Y: 11.00  Z: 339.72
r_side 0   m_tip: 0   m_b: 0   m_side: 0   i_tip: 0   i_side: 0   p_side: 0thumb: 3   index: 0   middle: 3   ring: 2   pinky: 2 X: 355.98  Y: 10.39  Z: 331.30
r_side 0   m_tip: 0   m_b: 0   m_side: 0   i_tip: 0   i_side: 0   p_side: 0thumb: 3   index: 0   middle: 9   ring: 12   pinky: 3 X: 352.13  Y: 17.41  Z: 337.98
r_side 0   m_tip: 0   m_b: 0   m_side: 0   i_tip: 0   i_side: 0   p_side: 0thumb: 3   index: 1   middle: 22   ring: 24   pinky: 20 X: 351.25  Y: 15.17  Z: 336.71
r_side 0   m_tip: 0   m_b: 0   m_side: 0   i_tip: 0   i_side: 0   p_side: 0thumb: 3   index: 19   middle: 22   ring: 24   pinky: 21 X: 347.34  Y: 9.83  Z: 336.66
r_side 0   m_tip: 0   m_b: 0   m_side: 0   i_tip: 0   i_side: 0   p_side: 0thumb: 4   index: 13   middle: 21   ring: 23   pinky: 21 X: 345.87  Y: 355.01  Z: 340.09
r_side 0   m_tip: 0   m_b: 0   m_side: 0   i_tip: 0   i_side: 0   p_side: 0thumb: 4   index: 3   middle: 20   ring: 23   pinky: 20 X: 348.96  Y: 347.93  Z: 345.95
r_side 0   m_tip: 0   m_b: 0   m_side: 0   i_tip: 0   i_side: 0   p_side: 0thumb: 4   index: 3   middle: 20   ring: 23   pinky: 20 X: 355.54  Y: 340.32  Z: 347.96
r_side 0   m_tip: 0   m_b: 0   m_side: 0   i_tip: 0   i_side: 0   p_side: 0thumb: 4   index: 3   middle: 20   ring: 22   pinky: 20 X: 360.00  Y: 339.18  Z: 346.70
r_side 0   m_tip: 0   m_b: 0   m_side: 0   i_tip: 0   i_side: 0   p_side: 0thumb: 4   index: 3   middle: 20   ring: 22   pinky: 20 X: 0.97  Y: 337.61  Z: 344.46
r_side 0   m_tip: 0   m_b: 0   m_side: 0   i_tip: 0   i_side: 0   p_side: 0thumb: 4   index: 3   middle: 19   ring: 22   pinky: 20 X: 2.25  Y: 337.94  Z: 344.18
r_side 0   m_tip: 0   m_b: 0   m_side: 0   i_tip: 0   i_side: 0   p_side: 0thumb: 4   index: 3   middle: 19   ring: 22   pinky: 20 X: 2.43  Y: 338.19  Z: 344.29
r_side 0   m_tip: 0   m_b: 0   m_side: 0   i_tip: 0   i_side: 0   p_side: 0thumb: 4   index: 2   middle: 19   ring: 22   pinky: 19 X: 2.62  Y: 338.21  Z: 344.53
r_side 0   m_tip: 0   m_b: 0   m_side: 0   i_tip: 0   i_side: 0   p_side: 0thumb: 4   index: 3   middle: 19   ring: 22   pinky: 19 X: 3.12  Y: 338.13  Z: 343.98
r_side 0   m_tip: 0   m_b: 0   m_side: 0   i_tip: 0   i_side: 0   p_side: 0thumb: 4   index: 3   middle: 19   ring: 21   pinky: 19 X: 3.13  Y: 338.11  Z: 343.23
r_side 0   m_tip: 0   m_b: 0   m_side: 0   i_tip: 0   i_side: 0   p_side: 0thumb: 4   index: 3   middle: 19   ring: 21   pinky: 19 X: 3.54  Y: 339.52  Z: 342.92
r_side 0   m_tip: 0   m_b: 0   m_side: 0   i_tip: 0   i_side: 0   p_side: 0thumb: 4   index: 2   middle: 19   ring: 21   pinky: 19 X: 3.78  Y: 339.37  Z: 341.93
r_side 0   m_tip: 0   m_b: 0   m_side: 0   i_tip: 0   i_side: 0   p_side: 0thumb: 4   index: 3   middle: 19   ring: 21   pinky: 19 X: 4.09  Y: 340.47  Z: 341.24
r_side 0   m_tip: 0   m_b: 0   m_side: 0   i_tip: 0   i_side: 0   p_side: 0thumb: 4   index: 2   middle: 19   ring: 21   pinky: 19 X: 4.65  Y: 341.22  Z: 340.58
r_side 0   m_tip: 0   m_b: 0   m_side: 0   i_tip: 0   i_side: 0   p_side: 0thumb: 4   index: 2   middle: 19   ring: 21   pinky: 19 X: 5.13  Y: 341.61  Z: 340.84
r_side 0   m_tip: 0   m_b: 0   m_side: 0   i_tip: 0   i_side: 0   p_side: 0thumb: 4   index: 2   middle: 19   ring: 21   pinky: 19 X: 5.57  Y: 342.82  Z: 341.51
r_side 0   m_tip: 0   m_b: 0   m_side: 0   i_tip: 0   i_side: 0   p_side: 0thumb: 4   index: 2   middle: 19   ring: 21   pinky: 19 X: 6.04  Y: 343.02  Z: 341.43
r_side 0   m_tip: 0   m_b: 0   m_side: 0   i_tip: 0   i_side: 0   p_side: 0thumb: 4   index: 2   middle: 19   ring: 21   pinky: 19 X: 6.28  Y: 343.30  Z: 340.55
r_side 0   m_tip: 0   m_b: 0   m_side: 0   i_tip: 0   i_side: 0   p_side: 0thumb: 4   index: 2   middle: 19   ring: 21   pinky: 19 X: 6.59  Y: 343.03  Z: 340.61
r_side 0   m_tip: 0   m_b: 0   m_side: 0   i_tip: 0   i_side: 0   p_side: 0thumb: 3   index: 2   middle: 19   ring: 21   pinky: 19 X: 6.46  Y: 343.49  Z: 340.44
r_side 0   m_tip: 0   m_b: 0   m_side: 0   i_tip: 0   i_side: 0   p_side: 0thumb: 4   index: 2   middle: 19   ring: 21   pinky: 19 X: 6.64  Y: 343.86  Z: 340.55
r_side 0   m_tip: 0   m_b: 0   m_side: 0   i_tip: 0   i_side: 0   p_side: 0thumb: 4   index: 2   middle: 18   ring: 21   pinky: 19 X: 6.76  Y: 344.02  Z: 340.55
r_side 0   m_tip: 0   m_b: 0   m_side: 0   i_tip: 0   i_side: 0   p_side: 0thumb: 4   index: 2   middle: 18   ring: 20   pinky: 19 X: 7.19  Y: 343.73  Z: 340.81
r_side 0   m_tip: 0   m_b: 0   m_side: 0   i_tip: 0   i_side: 0   p_side: 0thumb: 4   index: 2   middle: 18   ring: 20   pinky: 19 X: 7.65  Y: 343.74  Z: 341.00
r_side 0   m_tip: 0   m_b: 0   m_side: 0   i_tip: 0   i_side: 0   p_side: 0thumb: 4   index: 2   middle: 18   ring: 20   pinky: 18 X: 8.11  Y: 344.15  Z: 341.73
r_side 0   m_tip: 0   m_b: 0   m_side: 0   i_tip: 0   i_side: 0   p_side: 0thumb: 3   index: 2   middle: 18   ring: 20   pinky: 19 X: 8.35  Y: 344.00  Z: 341.54
r_side 0   m_tip: 0   m_b: 0   m_side: 0   i_tip: 0   i_side: 0   p_side: 0thumb: 4   index: 2   middle: 18   ring: 21   pinky: 19 X: 8.26  Y: 344.19  Z: 341.34
r_side 0   m_tip: 0   m_b: 0   m_side: 0   i_tip: 0   i_side: 0   p_side: 0thumb: 3   index: 2   middle: 18   ring: 20   pinky: 18 X: 8.59  Y: 344.03  Z: 340.79
r_side 0   m_tip: 0   m_b: 0   m_side: 0   i_tip: 0   i_side: 0   p_side: 0thumb: 4   index: 2   middle: 18   ring: 20   pinky: 18 X: 9.28  Y: 344.30  Z: 339.92
r_side 0   m_tip: 0   m_b: 0   m_side: 0   i_tip: 0   i_side: 0   p_side: 0thumb: 4   index: 2   middle: 18   ring: 20   pinky: 18 X: 10.11  Y: 344.50  Z: 339.60
r_side 0   m_tip: 0   m_b: 0   m_side: 0   i_tip: 0   i_side: 0   p_side: 0thumb: 4   index: 2   middle: 18   ring: 20   pinky: 19 X: 10.29  Y: 344.65  Z: 339.75
r_side 0   m_tip: 0   m_b: 0   m_side: 0   i_tip: 0   i_side: 0   p_side: 0thumb: 4   index: 2   middle: 18   ring: 20   pinky: 18 X: 10.45  Y: 344.93  Z: 339.70
r_side 0   m_tip: 0   m_b: 0   m_side: 0   i_tip: 0   i_side: 0   p_side: 0thumb: 4   index: 2   middle: 18   ring: 20   pinky: 18 X: 11.03  Y: 344.55  Z: 339.99
r_side 0   m_tip: 0   m_b: 0   m_side: 0   i_tip: 0   i_side: 0   p_side: 0thumb: 4   index: 2   middle: 18   ring: 20   pinky: 18 X: 11.76  Y: 344.30  Z: 340.09
r_side 0   m_tip: 0   m_b: 0   m_side: 0   i_tip: 0   i_side: 0   p_side: 0thumb: 3   index: 2   middle: 18   ring: 20   pinky: 18 X: 11.96  Y: 344.35  Z: 340.40
r_side 0   m_tip: 0   m_b: 0   m_side: 0   i_tip: 0   i_side: 0   p_side: 0thumb: 3   index: 2   middle: 18   ring: 20   pinky: 18 X: 12.27  Y: 344.37  Z: 341.08
r_side 0   m_tip: 0   m_b: 0   m_side: 0   i_tip: 0   i_side: 0   p_side: 0thumb: 3   index: 2   middle: 18   ring: 20   pinky: 18 X: 12.78  Y: 344.12  Z: 340.96
r_side 0   m_tip: 0   m_b: 0   m_side: 0   i_tip: 0   i_side: 0   p_side: 0thumb: 4   index: 2   middle: 18   ring: 20   pinky: 18 X: 13.41  Y: 343.77  Z: 341.42
r_side 0   m_tip: 0   m_b: 0   m_side: 0   i_tip: 0   i_side: 0   p_side: 0thumb: 4   index: 2   middle: 18   ring: 20   pinky: 18 X: 13.58  Y: 343.63  Z: 341.54
r_side 0   m_tip: 0   m_b: 0   m_side: 0   i_tip: 0   i_side: 0   p_side: 0thumb: 4   index: 2   middle: 18   ring: 20   pinky: 18 X: 13.30  Y: 344.15  Z: 341.18
r_side 0   m_tip: 0   m_b: 0   m_side: 0   i_tip: 0   i_side: 0   p_side: 0thumb: 4   index: 2   middle: 18   ring: 20   pinky: 18 X: 13.29  Y: 344.59  Z: 341.32
r_side 0   m_tip: 0   m_b: 0   m_side: 0   i_tip: 0   i_side: 0   p_side: 0thumb: 4   index: 2   middle: 18   ring: 20   pinky: 18 X: 13.15  Y: 344.88  Z: 341.74
r_side 0   m_tip: 0   m_b: 0   m_side: 0   i_tip: 0   i_side: 0   p_side: 0thumb: 4   index: 2   middle: 18   ring: 20   pinky: 18 X: 13.37  Y: 345.21  Z: 342.08
r_side 0   m_tip: 0   m_b: 0   m_side: 0   i_tip: 0   i_side: 0   p_side: 0thumb: 4   index: 2   middle: 18   ring: 20   pinky: 18 X: 13.51  Y: 345.47  Z: 342.30
r_side 0   m_tip: 0   m_b: 0   m_side: 0   i_tip: 0   i_side: 0   p_side: 0thumb: 3   index: 2   middle: 18   ring: 20   pinky: 18 X: 13.88  Y: 345.34  Z: 342.09
r_side 0   m_tip: 0   m_b: 0   m_side: 0   i_tip: 0   i_side: 0   p_side: 0thumb: 4   index: 2   middle: 18   ring: 19   pinky: 18 X: 13.89  Y: 345.39  Z: 342.39
