juanmrq95/ee149_104/ASLsensing/longFlex/save_sensordata/test 1.1/testAashykLetterR.txt

1r_side 0   m_tip: 0   m_b: 0   m_side: 0   i_tip: 0   i_side: 0   p_side: 0thumb: 6   index: 0   middle: 2   ring: 2   pinky: 2 X: 358.73  Y: 3.65  Z: 1.14
r_side 0   m_tip: 0   m_b: 0   m_side: 0   i_tip: 0   i_side: 0   p_side: 0thumb: 6   index: 0   middle: 2   ring: 2   pinky: 2 X: 358.79  Y: 4.54  Z: 358.61
r_side 0   m_tip: 0   m_b: 0   m_side: 0   i_tip: 0   i_side: 0   p_side: 0thumb: 6   index: 0   middle: 2   ring: 2   pinky: 3 X: 358.85  Y: 5.29  Z: 355.98
r_side 0   m_tip: 0   m_b: 0   m_side: 0   i_tip: 0   i_side: 0   p_side: 0thumb: 6   index: 0   middle: 2   ring: 2   pinky: 2 X: 358.89  Y: 5.94  Z: 353.57
r_side 0   m_tip: 0   m_b: 0   m_side: 0   i_tip: 0   i_side: 0   p_side: 0thumb: 6   index: 0   middle: 2   ring: 2   pinky: 2 X: 358.72  Y: 6.65  Z: 351.91
r_side 0   m_tip: 0   m_b: 0   m_side: 0   i_tip: 0   i_side: 0   p_side: 0thumb: 6   index: 0   middle: 2   ring: 2   pinky: 2 X: 358.79  Y: 7.12  Z: 349.76
r_side 0   m_tip: 0   m_b: 0   m_side: 0   i_tip: 0   i_side: 0   p_side: 0thumb: 6   index: 0   middle: 2   ring: 2   pinky: 2 X: 358.73  Y: 7.81  Z: 347.96
r_side 0   m_tip: 0   m_b: 0   m_side: 0   i_tip: 0   i_side: 0   p_side: 0thumb: 6   index: 0   middle: 2   ring: 2   pinky: 2 X: 358.60  Y: 8.08  Z: 345.92
r_side 0   m_tip: 0   m_b: 0   m_side: 0   i_tip: 0   i_side: 0   p_side: 0thumb: 6   index: 0   middle: 2   ring: 2   pinky: 2 X: 358.43  Y: 8.54  Z: 344.31
r_side 0   m_tip: 0   m_b: 0   m_side: 0   i_tip: 0   i_side: 0   p_side: 0thumb: 6   index: 0   middle: 2   ring: 2   pinky: 2 X: 358.37  Y: 8.95  Z: 342.73
r_side 0   m_tip: 0   m_b: 0   m_side: 0   i_tip: 0   i_side: 0   p_side: 0thumb: 6   index: 0   middle: 2   ring: 2   pinky: 2 X: 358.28  Y: 9.03  Z: 341.23
r_side 0   m_tip: 0   m_b: 0   m_side: 0   i_tip: 0   i_side: 0   p_side: 0thumb: 5   index: 0   middle: 2   ring: 2   pinky: 1 X: 358.29  Y: 8.99  Z: 339.89
r_side 0   m_tip: 0   m_b: 0   m_side: 0   i_tip: 0   i_side: 0   p_side: 0thumb: 6   index: 0   middle: 2   ring: 2   pinky: 2 X: 358.19  Y: 9.45  Z: 338.74
r_side 0   m_tip: 0   m_b: 0   m_side: 0   i_tip: 0   i_side: 0   p_side: 0thumb: 6   index: 0   middle: 2   ring: 2   pinky: 2 X: 358.12  Y: 9.44  Z: 337.74
r_side 0   m_tip: 0   m_b: 0   m_side: 0   i_tip: 0   i_side: 0   p_side: 0thumb: 6   index: 0   middle: 2   ring: 2   pinky: 2 X: 358.43  Y: 8.37  Z: 336.27
r_side 0   m_tip: 0   m_b: 0   m_side: 0   i_tip: 0   i_side: 0   p_side: 0thumb: 6   index: 0   middle: 2   ring: 2   pinky: 3 X: 356.54  Y: 13.18  Z: 330.45
r_side 0   m_tip: 0   m_b: 0   m_side: 0   i_tip: 0   i_side: 0   p_side: 0thumb: 6   index: 0   middle: 3   ring: 5   pinky: 2 X: 351.63  Y: 26.08  Z: 329.34
r_side 0   m_tip: 0   m_b: 0   m_side: 0   i_tip: 0   i_side: 0   p_side: 0thumb: 6   index: 0   middle: 8   ring: 19   pinky: 10 X: 341.24  Y: 37.45  Z: 324.75
r_side 0   m_tip: 0   m_b: 0   m_side: 0   i_tip: 0   i_side: 0   p_side: 0thumb: 6   index: 1   middle: 8   ring: 20   pinky: 15 X: 332.97  Y: 48.88  Z: 321.10
r_side 0   m_tip: 0   m_b: 0   m_side: 0   i_tip: 0   i_side: 0   p_side: 0thumb: 17   index: 0   middle: 4   ring: 19   pinky: 15 X: 329.45  Y: 50.32  Z: 316.72
r_side 0   m_tip: 0   m_b: 0   m_side: 0   i_tip: 0   i_side: 0   p_side: 0thumb: 18   index: 0   middle: 3   ring: 20   pinky: 17 X: 328.49  Y: 49.00  Z: 322.83
r_side 0   m_tip: 0   m_b: 0   m_side: 0   i_tip: 0   i_side: 0   p_side: 0thumb: 21   index: 0   middle: 3   ring: 20   pinky: 16 X: 323.21  Y: 51.15  Z: 316.80
r_side 0   m_tip: 0   m_b: 0   m_side: 0   i_tip: 0   i_side: 0   p_side: 0thumb: 21   index: 0   middle: 3   ring: 20   pinky: 16 X: 319.76  Y: 55.27  Z: 313.06
r_side 0   m_tip: 0   m_b: 0   m_side: 0   i_tip: 0   i_side: 0   p_side: 0thumb: 20   index: 0   middle: 3   ring: 20   pinky: 15 X: 318.69  Y: 57.05  Z: 310.40
r_side 0   m_tip: 0   m_b: 0   m_side: 0   i_tip: 0   i_side: 0   p_side: 0thumb: 20   index: 0   middle: 3   ring: 19   pinky: 15 X: 318.13  Y: 58.87  Z: 309.46
r_side 0   m_tip: 0   m_b: 0   m_side: 0   i_tip: 0   i_side: 0   p_side: 0thumb: 20   index: 0   middle: 3   ring: 19   pinky: 15 X: 312.49  Y: 61.33  Z: 304.17
r_side 0   m_tip: 0   m_b: 0   m_side: 0   i_tip: 0   i_side: 0   p_side: 0thumb: 20   index: 0   middle: 3   ring: 19   pinky: 15 X: 316.68  Y: 60.37  Z: 308.84
r_side 0   m_tip: 0   m_b: 0   m_side: 0   i_tip: 0   i_side: 0   p_side: 0thumb: 20   index: 0   middle: 3   ring: 19   pinky: 15 X: 314.45  Y: 58.95  Z: 305.21
r_side 0   m_tip: 0   m_b: 0   m_side: 0   i_tip: 0   i_side: 0   p_side: 0thumb: 20   index: 0   middle: 3   ring: 19   pinky: 15 X: 312.20  Y: 59.68  Z: 304.31
r_side 0   m_tip: 0   m_b: 0   m_side: 0   i_tip: 0   i_side: 0   p_side: 0thumb: 20   index: 0   middle: 3   ring: 19   pinky: 15 X: 315.61  Y: 58.03  Z: 308.51
r_side 0   m_tip: 0   m_b: 0   m_side: 0   i_tip: 0   i_side: 0   p_side: 0thumb: 19   index: 0   middle: 3   ring: 19   pinky: 15 X: 312.91  Y: 57.94  Z: 305.80
r_side 0   m_tip: 0   m_b: 0   m_side: 0   i_tip: 0   i_side: 0   p_side: 0thumb: 19   index: 0   middle: 3   ring: 18   pinky: 15 X: 312.61  Y: 57.24  Z: 305.71
r_side 0   m_tip: 0   m_b: 0   m_side: 0   i_tip: 0   i_side: 0   p_side: 0thumb: 18   index: 0   middle: 3   ring: 18   pinky: 15 X: 312.46  Y: 56.33  Z: 305.90
r_side 0   m_tip: 0   m_b: 0   m_side: 0   i_tip: 0   i_side: 0   p_side: 0thumb: 18   index: 0   middle: 3   ring: 17   pinky: 15 X: 312.63  Y: 54.88  Z: 306.06
r_side 0   m_tip: 0   m_b: 0   m_side: 0   i_tip: 0   i_side: 0   p_side: 0thumb: 18   index: 0   middle: 3   ring: 18   pinky: 14 X: 311.70  Y: 53.86  Z: 305.14
r_side 0   m_tip: 0   m_b: 0   m_side: 0   i_tip: 0   i_side: 0   p_side: 0thumb: 17   index: 0   middle: 3   ring: 18   pinky: 14 X: 310.93  Y: 53.46  Z: 304.99
r_side 0   m_tip: 0   m_b: 0   m_side: 0   i_tip: 0   i_side: 0   p_side: 0thumb: 16   index: 0   middle: 3   ring: 18   pinky: 14 X: 311.79  Y: 52.72  Z: 305.75
r_side 0   m_tip: 0   m_b: 0   m_side: 0   i_tip: 0   i_side: 0   p_side: 0thumb: 16   index: 0   middle: 3   ring: 18   pinky: 14 X: 311.67  Y: 51.84  Z: 305.98
r_side 0   m_tip: 0   m_b: 0   m_side: 0   i_tip: 0   i_side: 0   p_side: 0thumb: 17   index: 0   middle: 3   ring: 18   pinky: 14 X: 310.92  Y: 51.31  Z: 305.42
r_side 0   m_tip: 0   m_b: 0   m_side: 0   i_tip: 0   i_side: 0   p_side: 0thumb: 16   index: 0   middle: 3   ring: 18   pinky: 14 X: 310.10  Y: 51.31  Z: 304.97
r_side 0   m_tip: 0   m_b: 0   m_side: 0   i_tip: 0   i_side: 0   p_side: 0thumb: 15   index: 0   middle: 3   ring: 17   pinky: 14 X: 311.75  Y: 50.32  Z: 307.32
r_side 0   m_tip: 0   m_b: 0   m_side: 0   i_tip: 0   i_side: 0   p_side: 0thumb: 15   index: 0   middle: 3   ring: 17   pinky: 14 X: 310.59  Y: 49.41  Z: 305.81
r_side 0   m_tip: 0   m_b: 0   m_side: 0   i_tip: 0   i_side: 0   p_side: 0thumb: 15   index: 0   middle: 3   ring: 17   pinky: 14 X: 310.68  Y: 49.13  Z: 306.42
r_side 0   m_tip: 0   m_b: 0   m_side: 0   i_tip: 0   i_side: 0   p_side: 0thumb: 15   index: 0   middle: 3   ring: 17   pinky: 14 X: 310.18  Y: 48.31  Z: 305.73
r_side 0   m_tip: 0   m_b: 0   m_side: 0   i_tip: 0   i_side: 0   p_side: 0thumb: 15   index: 0   middle: 3   ring: 17   pinky: 14 X: 309.01  Y: 48.40  Z: 304.62
r_side 0   m_tip: 0   m_b: 0   m_side: 0   i_tip: 0   i_side: 0   p_side: 0thumb: 15   index: 0   middle: 3   ring: 17   pinky: 14 X: 308.24  Y: 47.93  Z: 304.55
r_side 0   m_tip: 0   m_b: 0   m_side: 0   i_tip: 0   i_side: 0   p_side: 0thumb: 14   index: 0   middle: 3   ring: 17   pinky: 14 X: 307.94  Y: 47.34  Z: 303.99
r_side 0   m_tip: 0   m_b: 0   m_side: 0   i_tip: 0   i_side: 0   p_side: 0thumb: 14   index: 0   middle: 3   ring: 17   pinky: 14 X: 307.04  Y: 46.99  Z: 303.31
r_side 0   m_tip: 0   m_b: 0   m_side: 0   i_tip: 0   i_side: 0   p_side: 0thumb: 14   index: 0   middle: 3   ring: 17   pinky: 14 X: 307.26  Y: 46.34  Z: 303.80
r_side 0   m_tip: 0   m_b: 0   m_side: 0   i_tip: 0   i_side: 0   p_side: 0thumb: 14   index: 0   middle: 3   ring: 17   pinky: 14 X: 305.84  Y: 45.48  Z: 302.28
r_side 0   m_tip: 0   m_b: 0   m_side: 0   i_tip: 0   i_side: 0   p_side: 0thumb: 14   index: 0   middle: 2   ring: 17   pinky: 14 X: 304.85  Y: 45.80  Z: 301.69
r_side 0   m_tip: 0   m_b: 0   m_side: 0   i_tip: 0   i_side: 0   p_side: 0thumb: 14   index: 0   middle: 3   ring: 17   pinky: 14 X: 304.36  Y: 45.84  Z: 301.82
r_side 0   m_tip: 0   m_b: 0   m_side: 0   i_tip: 0   i_side: 0   p_side: 0thumb: 14   index: 0   middle: 3   ring: 17   pinky: 14 X: 305.28  Y: 44.68  Z: 302.88
r_side 0   m_tip: 0   m_b: 0   m_side: 0   i_tip: 0   i_side: 0   p_side: 0thumb: 14   index: 0   middle: 3   ring: 17   pinky: 13 X: 304.32  Y: 43.61  Z: 301.32
r_side 0   m_tip: 0   m_b: 0   m_side: 0   i_tip: 0   i_side: 0   p_side: 0thumb: 14   index: 0   middle: 3   ring: 17   pinky: 14 X: 303.70  Y: 42.90  Z: 300.73
r_side 0   m_tip: 0   m_b: 0   m_side: 0   i_tip: 0   i_side: 0   p_side: 0thumb: 14   index: 0   middle: 3   ring: 17   pinky: 13 X: 303.29  Y: 42.17  Z: 300.59
r_side 0   m_tip: 0   m_b: 0   m_side: 0   i_tip: 0   i_side: 0   p_side: 0thumb: 14   index: 0   middle: 3   ring: 17   pinky: 13 X: 302.85  Y: 42.02  Z: 300.43
r_side 0   m_tip: 0   m_b: 0   m_side: 0   i_tip: 0   i_side: 0   p_side: 0thumb: 14   index: 0   middle: 3   ring: 17   pinky: 14 X: 302.42  Y: 41.41  Z: 300.15
r_side 0   m_tip: 0   m_b: 0   m_side: 0   i_tip: 0   i_side: 0   p_side: 0thumb: 14   index: 0   middle: 3   ring: 17   pinky: 13 X: 302.56  Y: 40.83  Z: 300.50
