juanmrq95/ee149_104/ASLsensing/longFlex/save_sensordata/test 1.1/testAashykLetterS.txt

ér_side 0   m_tip: 0   m_b: 0   m_side: 0   i_tip: 0   i_side: 0   p_side: 0thumb: 7   index: 0   middle: 1   ring: 1   pinky: 1 X: 360.00  Y: 359.74  Z: 0.26
r_side 0   m_tip: 0   m_b: 0   m_side: 0   i_tip: 0   i_side: 0   p_side: 0thumb: 7   index: 0   middle: 2   ring: 1   pinky: 1 X: 359.98  Y: 1.11  Z: 358.02
r_side 0   m_tip: 0   m_b: 0   m_side: 0   i_tip: 0   i_side: 0   p_side: 0thumb: 7   index: 0   middle: 1   ring: 1   pinky: 1 X: 360.00  Y: 2.20  Z: 355.92
r_side 0   m_tip: 0   m_b: 0   m_side: 0   i_tip: 0   i_side: 0   p_side: 0thumb: 7   index: 0   middle: 1   ring: 1   pinky: 1 X: 359.90  Y: 3.16  Z: 353.71
r_side 0   m_tip: 0   m_b: 0   m_side: 0   i_tip: 0   i_side: 0   p_side: 0thumb: 8   index: 0   middle: 2   ring: 1   pinky: 1 X: 359.73  Y: 4.32  Z: 351.73
r_side 0   m_tip: 0   m_b: 0   m_side: 0   i_tip: 0   i_side: 0   p_side: 0thumb: 7   index: 0   middle: 1   ring: 1   pinky: 1 X: 359.48  Y: 6.22  Z: 350.11
r_side 0   m_tip: 0   m_b: 0   m_side: 0   i_tip: 0   i_side: 0   p_side: 0thumb: 7   index: 0   middle: 2   ring: 1   pinky: 1 X: 359.34  Y: 7.12  Z: 348.55
r_side 0   m_tip: 0   m_b: 0   m_side: 0   i_tip: 0   i_side: 0   p_side: 0thumb: 7   index: 0   middle: 1   ring: 1   pinky: 1 X: 359.15  Y: 7.92  Z: 347.10
r_side 0   m_tip: 0   m_b: 0   m_side: 0   i_tip: 0   i_side: 0   p_side: 0thumb: 7   index: 0   middle: 2   ring: 1   pinky: 1 X: 358.94  Y: 8.78  Z: 345.62
r_side 0   m_tip: 0   m_b: 0   m_side: 0   i_tip: 0   i_side: 0   p_side: 0thumb: 7   index: 0   middle: 2   ring: 1   pinky: 1 X: 358.82  Y: 9.44  Z: 344.36
r_side 0   m_tip: 0   m_b: 0   m_side: 0   i_tip: 0   i_side: 0   p_side: 0thumb: 7   index: 0   middle: 2   ring: 1   pinky: 1 X: 357.49  Y: 11.39  Z: 340.49
r_side 0   m_tip: 0   m_b: 0   m_side: 0   i_tip: 0   i_side: 0   p_side: 0thumb: 7   index: 4   middle: 6   ring: 8   pinky: 1 X: 349.78  Y: 32.46  Z: 336.48
r_side 0   m_tip: 0   m_b: 0   m_side: 0   i_tip: 0   i_side: 0   p_side: 0thumb: 7   index: 20   middle: 19   ring: 20   pinky: 16 X: 339.14  Y: 42.88  Z: 325.75
r_side 0   m_tip: 0   m_b: 0   m_side: 0   i_tip: 0   i_side: 0   p_side: 0thumb: 7   index: 23   middle: 22   ring: 23   pinky: 20 X: 331.53  Y: 48.49  Z: 318.71
r_side 0   m_tip: 0   m_b: 0   m_side: 0   i_tip: 1   i_side: 0   p_side: 0thumb: 12   index: 23   middle: 22   ring: 23   pinky: 20 X: 322.62  Y: 56.90  Z: 314.17
r_side 0   m_tip: 0   m_b: 0   m_side: 0   i_tip: 1   i_side: 0   p_side: 0thumb: 22   index: 22   middle: 22   ring: 22   pinky: 20 X: 318.83  Y: 68.12  Z: 311.46
r_side 0   m_tip: 0   m_b: 0   m_side: 1   i_tip: 1   i_side: 0   p_side: 0thumb: 24   index: 23   middle: 21   ring: 22   pinky: 20 X: 298.99  Y: 74.72  Z: 292.09
r_side 0   m_tip: 0   m_b: 0   m_side: 1   i_tip: 1   i_side: 0   p_side: 0thumb: 24   index: 22   middle: 21   ring: 22   pinky: 20 X: 265.46  Y: 76.07  Z: 261.00
r_side 0   m_tip: 0   m_b: 0   m_side: 1   i_tip: 1   i_side: 0   p_side: 0thumb: 23   index: 22   middle: 21   ring: 22   pinky: 20 X: 265.92  Y: 73.88  Z: 260.51
r_side 0   m_tip: 0   m_b: 0   m_side: 1   i_tip: 1   i_side: 0   p_side: 0thumb: 23   index: 22   middle: 21   ring: 21   pinky: 19 X: 266.19  Y: 74.17  Z: 260.98
r_side 0   m_tip: 0   m_b: 0   m_side: 1   i_tip: 1   i_side: 0   p_side: 0thumb: 23   index: 22   middle: 21   ring: 21   pinky: 19 X: 274.01  Y: 72.61  Z: 268.07
r_side 0   m_tip: 0   m_b: 0   m_side: 1   i_tip: 1   i_side: 0   p_side: 0thumb: 22   index: 22   middle: 21   ring: 21   pinky: 19 X: 278.78  Y: 71.78  Z: 272.08
r_side 0   m_tip: 0   m_b: 0   m_side: 1   i_tip: 1   i_side: 0   p_side: 0thumb: 22   index: 21   middle: 21   ring: 21   pinky: 19 X: 278.31  Y: 71.72  Z: 271.64
r_side 0   m_tip: 0   m_b: 0   m_side: 1   i_tip: 1   i_side: 0   p_side: 0thumb: 22   index: 21   middle: 21   ring: 21   pinky: 19 X: 278.64  Y: 71.27  Z: 271.79
r_side 0   m_tip: 0   m_b: 0   m_side: 1   i_tip: 1   i_side: 0   p_side: 0thumb: 22   index: 22   middle: 20   ring: 21   pinky: 19 X: 278.78  Y: 70.25  Z: 272.00
r_side 0   m_tip: 0   m_b: 0   m_side: 1   i_tip: 1   i_side: 0   p_side: 0thumb: 22   index: 22   middle: 20   ring: 21   pinky: 19 X: 279.60  Y: 69.51  Z: 272.39
r_side 0   m_tip: 0   m_b: 0   m_side: 1   i_tip: 1   i_side: 0   p_side: 0thumb: 22   index: 21   middle: 20   ring: 21   pinky: 19 X: 278.01  Y: 68.95  Z: 271.01
r_side 0   m_tip: 0   m_b: 0   m_side: 1   i_tip: 1   i_side: 0   p_side: 0thumb: 21   index: 21   middle: 20   ring: 21   pinky: 19 X: 277.72  Y: 67.58  Z: 271.08
r_side 0   m_tip: 0   m_b: 0   m_side: 1   i_tip: 1   i_side: 0   p_side: 0thumb: 22   index: 21   middle: 20   ring: 20   pinky: 19 X: 278.55  Y: 66.69  Z: 271.61
r_side 0   m_tip: 0   m_b: 0   m_side: 1   i_tip: 1   i_side: 0   p_side: 0thumb: 21   index: 21   middle: 20   ring: 20   pinky: 19 X: 279.18  Y: 65.83  Z: 272.42
r_side 0   m_tip: 0   m_b: 0   m_side: 1   i_tip: 1   i_side: 0   p_side: 0thumb: 21   index: 21   middle: 20   ring: 20   pinky: 19 X: 279.18  Y: 65.18  Z: 272.48
r_side 0   m_tip: 0   m_b: 0   m_side: 1   i_tip: 1   i_side: 0   p_side: 0thumb: 21   index: 21   middle: 20   ring: 20   pinky: 19 X: 279.58  Y: 64.11  Z: 273.02
r_side 0   m_tip: 0   m_b: 0   m_side: 1   i_tip: 1   i_side: 0   p_side: 0thumb: 21   index: 21   middle: 20   ring: 20   pinky: 19 X: 279.54  Y: 63.32  Z: 272.75
r_side 0   m_tip: 0   m_b: 0   m_side: 1   i_tip: 1   i_side: 0   p_side: 0thumb: 21   index: 21   middle: 20   ring: 20   pinky: 18 X: 280.21  Y: 62.84  Z: 273.58
r_side 0   m_tip: 0   m_b: 0   m_side: 1   i_tip: 1   i_side: 0   p_side: 0thumb: 21   index: 21   middle: 20   ring: 20   pinky: 19 X: 280.81  Y: 62.06  Z: 274.01
r_side 0   m_tip: 0   m_b: 0   m_side: 1   i_tip: 1   i_side: 0   p_side: 0thumb: 21   index: 21   middle: 20   ring: 20   pinky: 18 X: 281.32  Y: 61.47  Z: 274.76
r_side 0   m_tip: 0   m_b: 0   m_side: 1   i_tip: 1   i_side: 0   p_side: 0thumb: 22   index: 21   middle: 20   ring: 20   pinky: 18 X: 281.88  Y: 60.68  Z: 274.97
r_side 0   m_tip: 0   m_b: 0   m_side: 1   i_tip: 1   i_side: 0   p_side: 0thumb: 21   index: 21   middle: 20   ring: 20   pinky: 18 X: 281.75  Y: 59.78  Z: 274.88
r_side 0   m_tip: 0   m_b: 0   m_side: 1   i_tip: 1   i_side: 0   p_side: 0thumb: 21   index: 21   middle: 20   ring: 20   pinky: 18 X: 283.13  Y: 59.24  Z: 276.28
r_side 0   m_tip: 0   m_b: 0   m_side: 1   i_tip: 1   i_side: 0   p_side: 0thumb: 21   index: 21   middle: 20   ring: 20   pinky: 18 X: 283.10  Y: 59.03  Z: 276.41
r_side 0   m_tip: 0   m_b: 0   m_side: 1   i_tip: 1   i_side: 0   p_side: 0thumb: 21   index: 21   middle: 20   ring: 20   pinky: 18 X: 283.41  Y: 58.50  Z: 276.82
r_side 0   m_tip: 0   m_b: 0   m_side: 1   i_tip: 1   i_side: 0   p_side: 0thumb: 21   index: 20   middle: 20   ring: 20   pinky: 18 X: 283.80  Y: 57.69  Z: 276.79
r_side 0   m_tip: 0   m_b: 0   m_side: 1   i_tip: 1   i_side: 0   p_side: 0thumb: 21   index: 21   middle: 20   ring: 20   pinky: 18 X: 283.65  Y: 57.80  Z: 276.56
r_side 0   m_tip: 0   m_b: 0   m_side: 1   i_tip: 1   i_side: 0   p_side: 0thumb: 21   index: 21   middle: 20   ring: 20   pinky: 18 X: 284.13  Y: 57.16  Z: 276.96
r_side 0   m_tip: 0   m_b: 0   m_side: 1   i_tip: 1   i_side: 0   p_side: 0thumb: 20   index: 21   middle: 20   ring: 20   pinky: 18 X: 284.18  Y: 56.76  Z: 277.20
r_side 0   m_tip: 0   m_b: 0   m_side: 1   i_tip: 1   i_side: 0   p_side: 0thumb: 21   index: 20   middle: 20   ring: 20   pinky: 18 X: 284.37  Y: 56.13  Z: 277.25
r_side 0   m_tip: 0   m_b: 0   m_side: 1   i_tip: 1   i_side: 0   p_side: 0thumb: 21   index: 20   middle: 20   ring: 20   pinky: 18 X: 285.95  Y: 55.34  Z: 278.85
r_side 0   m_tip: 0   m_b: 0   m_side: 1   i_tip: 1   i_side: 0   p_side: 0thumb: 21   index: 20   middle: 20   ring: 20   pinky: 18 X: 285.63  Y: 54.32  Z: 278.37
r_side 0   m_tip: 0   m_b: 0   m_side: 1   i_tip: 1   i_side: 0   p_side: 0thumb: 20   index: 20   middle: 19   ring: 20   pinky: 18 X: 285.58  Y: 54.08  Z: 278.61
r_side 0   m_tip: 0   m_b: 0   m_side: 1   i_tip: 1   i_side: 0   p_side: 0thumb: 20   index: 20   middle: 20   ring: 20   pinky: 18 X: 285.16  Y: 53.83  Z: 278.55
r_side 0   m_tip: 0   m_b: 0   m_side: 1   i_tip: 1   i_side: 0   p_side: 0thumb: 20   index: 20   middle: 20   ring: 20   pinky: 18 X: 285.33  Y: 53.00  Z: 278.82
r_side 0   m_tip: 0   m_b: 0   m_side: 1   i_tip: 1   i_side: 0   p_side: 0thumb: 20   index: 20   middle: 20   ring: 20   pinky: 18 X: 286.06  Y: 52.20  Z: 279.22
r_side 0   m_tip: 0   m_b: 0   m_side: 1   i_tip: 1   i_side: 0   p_side: 0thumb: 20   index: 20   middle: 19   ring: 20   pinky: 18 X: 286.22  Y: 51.54  Z: 279.48
r_side 0   m_tip: 0   m_b: 0   m_side: 1   i_tip: 1   i_side: 0   p_side: 0thumb: 20   index: 20   middle: 19   ring: 20   pinky: 18 X: 285.80  Y: 50.98  Z: 279.08
r_side 0   m_tip: 0   m_b: 0   m_side: 1   i_tip: 1   i_side: 0   p_side: 0thumb: 20   index: 20   middle: 19   ring: 20   pinky: 18 X: 285.53  Y: 50.46  Z: 278.84
r_side 0   m_tip: 0   m_b: 0   m_side: 1   i_tip: 1   i_side: 0   p_side: 0thumb: 20   index: 20   middle: 19   ring: 20   pinky: 18 X: 286.82  Y: 49.45  Z: 280.76
r_side 0   m_tip: 0   m_b: 0   m_side: 1   i_tip: 1   i_side: 0   p_side: 0thumb: 20   index: 20   middle: 19   ring: 19   pinky: 18 X: 298.76  Y: 46.73  Z: 293.11
r_side 0   m_tip: 0   m_b: 0   m_side: 0   i_tip: 0   i_side: 0   p_side: 0thumb: 19   index: 20   middle: 19   ring: 19   pinky: 17 X: 308.19  Y: 40.75  Z: 303.23
r_side 0   m_tip: 0   m_b: 0   m_side: 0   i_tip: 0   i_side: 0   p_side: 0thumb: 17   index: 19   middle: 18   ring: 18   pinky: 16 X: 309.63  Y: 37.03  Z: 303.75
r_side 0   m_tip: 0   m_b: 0   m_side: 0   i_tip: 0   i_side: 0   p_side: 0thumb: 16   index: 19   middle: 17   ring: 18   pinky: 16 X: 309.67  Y: 33.13  Z: 302.89
r_side 0   m_tip: 0   m_b: 0   m_side: 0   i_tip: 0   i_side: 0   p_side: 0thumb: 15   index: 18   middle: 17   ring: 16   pinky: 15 X: 309.60  Y: 31.76  Z: 302.31
