juanmrq95/ee149_104/ASLsensing/longFlex/save_sensordata/test 1.1/testAashykLetterT.txt

:r_side 0   m_tip: 0   m_b: 0   m_side: 0   i_tip: 0   i_side: 0   p_side: 0thumb: 8   index: 1   middle: 2   ring: 1   pinky: 2 X: 4.05  Y: 311.62  Z: 1.44
r_side 0   m_tip: 0   m_b: 0   m_side: 0   i_tip: 0   i_side: 0   p_side: 0thumb: 8   index: 1   middle: 2   ring: 1   pinky: 1 X: 3.32  Y: 318.48  Z: 359.89
r_side 0   m_tip: 0   m_b: 0   m_side: 0   i_tip: 0   i_side: 0   p_side: 0thumb: 7   index: 1   middle: 2   ring: 2   pinky: 2 X: 3.51  Y: 323.69  Z: 357.61
r_side 0   m_tip: 0   m_b: 0   m_side: 0   i_tip: 0   i_side: 0   p_side: 0thumb: 7   index: 1   middle: 2   ring: 1   pinky: 2 X: 2.92  Y: 329.18  Z: 355.26
r_side 0   m_tip: 0   m_b: 0   m_side: 0   i_tip: 0   i_side: 0   p_side: 0thumb: 7   index: 0   middle: 2   ring: 1   pinky: 1 X: 1.72  Y: 335.64  Z: 353.78
r_side 0   m_tip: 0   m_b: 0   m_side: 0   i_tip: 0   i_side: 0   p_side: 0thumb: 7   index: 0   middle: 2   ring: 2   pinky: 1 X: 0.72  Y: 340.95  Z: 351.83
r_side 0   m_tip: 0   m_b: 0   m_side: 0   i_tip: 0   i_side: 0   p_side: 0thumb: 7   index: 1   middle: 2   ring: 1   pinky: 2 X: 359.30  Y: 347.72  Z: 350.47
r_side 0   m_tip: 0   m_b: 0   m_side: 0   i_tip: 0   i_side: 0   p_side: 0thumb: 6   index: 0   middle: 2   ring: 2   pinky: 2 X: 358.06  Y: 354.18  Z: 349.15
r_side 0   m_tip: 0   m_b: 0   m_side: 0   i_tip: 0   i_side: 0   p_side: 0thumb: 6   index: 0   middle: 2   ring: 1   pinky: 2 X: 356.85  Y: 359.18  Z: 347.46
r_side 0   m_tip: 0   m_b: 0   m_side: 0   i_tip: 0   i_side: 0   p_side: 0thumb: 7   index: 0   middle: 2   ring: 1   pinky: 1 X: 355.43  Y: 4.03  Z: 345.24
r_side 0   m_tip: 0   m_b: 0   m_side: 0   i_tip: 0   i_side: 0   p_side: 0thumb: 7   index: 0   middle: 2   ring: 1   pinky: 2 X: 354.51  Y: 6.53  Z: 344.02
r_side 0   m_tip: 0   m_b: 0   m_side: 0   i_tip: 0   i_side: 0   p_side: 0thumb: 6   index: 0   middle: 2   ring: 1   pinky: 1 X: 353.34  Y: 10.06  Z: 342.62
r_side 0   m_tip: 0   m_b: 0   m_side: 0   i_tip: 0   i_side: 0   p_side: 0thumb: 6   index: 0   middle: 2   ring: 1   pinky: 1 X: 352.56  Y: 13.12  Z: 341.06
r_side 0   m_tip: 0   m_b: 0   m_side: 0   i_tip: 0   i_side: 0   p_side: 0thumb: 7   index: 0   middle: 2   ring: 1   pinky: 1 X: 351.74  Y: 15.64  Z: 339.73
r_side 0   m_tip: 0   m_b: 0   m_side: 0   i_tip: 0   i_side: 0   p_side: 0thumb: 7   index: 0   middle: 2   ring: 1   pinky: 1 X: 350.54  Y: 19.82  Z: 338.14
r_side 0   m_tip: 0   m_b: 0   m_side: 0   i_tip: 0   i_side: 0   p_side: 0thumb: 6   index: 0   middle: 2   ring: 1   pinky: 1 X: 349.73  Y: 22.04  Z: 336.64
r_side 0   m_tip: 0   m_b: 0   m_side: 0   i_tip: 0   i_side: 0   p_side: 0thumb: 6   index: 0   middle: 2   ring: 1   pinky: 1 X: 348.28  Y: 26.50  Z: 333.40
r_side 0   m_tip: 0   m_b: 0   m_side: 0   i_tip: 0   i_side: 0   p_side: 0thumb: 7   index: 0   middle: 2   ring: 1   pinky: 1 X: 345.34  Y: 30.41  Z: 329.66
r_side 0   m_tip: 0   m_b: 0   m_side: 0   i_tip: 0   i_side: 0   p_side: 0thumb: 6   index: 1   middle: 3   ring: 5   pinky: 2 X: 339.44  Y: 46.78  Z: 328.16
r_side 0   m_tip: 0   m_b: 0   m_side: 0   i_tip: 0   i_side: 0   p_side: 0thumb: 7   index: 3   middle: 13   ring: 17   pinky: 8 X: 315.50  Y: 58.25  Z: 307.29
r_side 0   m_tip: 0   m_b: 0   m_side: 0   i_tip: 0   i_side: 0   p_side: 0thumb: 14   index: 13   middle: 16   ring: 18   pinky: 14 X: 300.66  Y: 61.38  Z: 291.78
r_side 0   m_tip: 0   m_b: 0   m_side: 1   i_tip: 1   i_side: 0   p_side: 0thumb: 13   index: 19   middle: 20   ring: 20   pinky: 18 X: 268.00  Y: 60.12  Z: 263.16
r_side 0   m_tip: 0   m_b: 1   m_side: 1   i_tip: 1   i_side: 0   p_side: 0thumb: 13   index: 20   middle: 19   ring: 19   pinky: 19 X: 248.70  Y: 55.75  Z: 246.84
r_side 0   m_tip: 0   m_b: 1   m_side: 1   i_tip: 1   i_side: 0   p_side: 0thumb: 13   index: 19   middle: 18   ring: 19   pinky: 19 X: 239.67  Y: 51.38  Z: 238.79
r_side 0   m_tip: 0   m_b: 1   m_side: 1   i_tip: 1   i_side: 0   p_side: 0thumb: 12   index: 19   middle: 18   ring: 18   pinky: 18 X: 238.99  Y: 51.05  Z: 238.98
r_side 0   m_tip: 0   m_b: 1   m_side: 1   i_tip: 1   i_side: 0   p_side: 0thumb: 12   index: 19   middle: 18   ring: 18   pinky: 18 X: 237.41  Y: 48.39  Z: 237.31
r_side 0   m_tip: 0   m_b: 1   m_side: 1   i_tip: 1   i_side: 0   p_side: 0thumb: 11   index: 19   middle: 18   ring: 19   pinky: 19 X: 240.64  Y: 50.31  Z: 239.14
r_side 0   m_tip: 0   m_b: 1   m_side: 1   i_tip: 1   i_side: 0   p_side: 0thumb: 11   index: 19   middle: 17   ring: 18   pinky: 19 X: 241.59  Y: 52.25  Z: 238.83
r_side 0   m_tip: 0   m_b: 1   m_side: 1   i_tip: 1   i_side: 0   p_side: 0thumb: 11   index: 19   middle: 17   ring: 18   pinky: 19 X: 240.58  Y: 53.05  Z: 237.99
r_side 0   m_tip: 0   m_b: 1   m_side: 1   i_tip: 1   i_side: 0   p_side: 0thumb: 11   index: 19   middle: 17   ring: 18   pinky: 19 X: 239.95  Y: 53.49  Z: 237.48
r_side 0   m_tip: 0   m_b: 1   m_side: 1   i_tip: 1   i_side: 0   p_side: 0thumb: 11   index: 19   middle: 17   ring: 18   pinky: 18 X: 240.48  Y: 53.37  Z: 238.11
r_side 0   m_tip: 0   m_b: 1   m_side: 1   i_tip: 1   i_side: 0   p_side: 0thumb: 11   index: 19   middle: 17   ring: 18   pinky: 18 X: 241.10  Y: 52.76  Z: 238.65
r_side 0   m_tip: 0   m_b: 1   m_side: 1   i_tip: 1   i_side: 0   p_side: 0thumb: 11   index: 19   middle: 17   ring: 18   pinky: 18 X: 241.08  Y: 52.42  Z: 238.82
r_side 0   m_tip: 0   m_b: 1   m_side: 1   i_tip: 1   i_side: 0   p_side: 0thumb: 11   index: 19   middle: 17   ring: 18   pinky: 18 X: 242.85  Y: 52.06  Z: 240.45
r_side 0   m_tip: 0   m_b: 1   m_side: 1   i_tip: 1   i_side: 0   p_side: 0thumb: 11   index: 19   middle: 17   ring: 18   pinky: 18 X: 245.06  Y: 51.99  Z: 242.39
r_side 0   m_tip: 0   m_b: 1   m_side: 1   i_tip: 1   i_side: 0   p_side: 0thumb: 10   index: 18   middle: 17   ring: 17   pinky: 18 X: 246.28  Y: 51.55  Z: 243.70
r_side 0   m_tip: 0   m_b: 1   m_side: 1   i_tip: 1   i_side: 0   p_side: 0thumb: 11   index: 18   middle: 17   ring: 17   pinky: 18 X: 247.04  Y: 51.15  Z: 244.77
r_side 0   m_tip: 0   m_b: 1   m_side: 1   i_tip: 1   i_side: 0   p_side: 0thumb: 10   index: 18   middle: 17   ring: 17   pinky: 18 X: 248.36  Y: 50.46  Z: 245.98
r_side 0   m_tip: 0   m_b: 1   m_side: 1   i_tip: 1   i_side: 0   p_side: 0thumb: 10   index: 18   middle: 17   ring: 17   pinky: 18 X: 249.85  Y: 49.79  Z: 247.63
r_side 0   m_tip: 0   m_b: 1   m_side: 1   i_tip: 1   i_side: 0   p_side: 0thumb: 10   index: 18   middle: 17   ring: 17   pinky: 18 X: 250.94  Y: 49.76  Z: 248.73
r_side 0   m_tip: 0   m_b: 1   m_side: 1   i_tip: 1   i_side: 0   p_side: 0thumb: 10   index: 18   middle: 17   ring: 17   pinky: 18 X: 251.86  Y: 49.70  Z: 249.69
r_side 0   m_tip: 0   m_b: 1   m_side: 1   i_tip: 1   i_side: 0   p_side: 0thumb: 10   index: 19   middle: 17   ring: 17   pinky: 18 X: 253.10  Y: 49.39  Z: 250.84
r_side 0   m_tip: 0   m_b: 1   m_side: 1   i_tip: 1   i_side: 0   p_side: 0thumb: 11   index: 18   middle: 17   ring: 17   pinky: 18 X: 254.13  Y: 49.22  Z: 252.09
r_side 0   m_tip: 0   m_b: 1   m_side: 1   i_tip: 1   i_side: 0   p_side: 0thumb: 10   index: 18   middle: 17   ring: 17   pinky: 18 X: 255.38  Y: 48.80  Z: 253.20
r_side 0   m_tip: 0   m_b: 1   m_side: 1   i_tip: 0   i_side: 0   p_side: 0thumb: 10   index: 18   middle: 16   ring: 17   pinky: 18 X: 256.74  Y: 48.78  Z: 254.48
r_side 0   m_tip: 0   m_b: 1   m_side: 1   i_tip: 0   i_side: 0   p_side: 0thumb: 10   index: 18   middle: 17   ring: 17   pinky: 18 X: 258.56  Y: 48.35  Z: 256.02
r_side 0   m_tip: 0   m_b: 1   m_side: 1   i_tip: 1   i_side: 0   p_side: 0thumb: 10   index: 18   middle: 16   ring: 17   pinky: 18 X: 259.60  Y: 47.72  Z: 256.98
r_side 0   m_tip: 0   m_b: 1   m_side: 1   i_tip: 1   i_side: 0   p_side: 0thumb: 10   index: 18   middle: 16   ring: 17   pinky: 18 X: 260.16  Y: 47.90  Z: 257.88
r_side 0   m_tip: 0   m_b: 1   m_side: 1   i_tip: 1   i_side: 0   p_side: 0thumb: 10   index: 18   middle: 16   ring: 17   pinky: 18 X: 261.29  Y: 47.31  Z: 259.03
r_side 0   m_tip: 0   m_b: 1   m_side: 1   i_tip: 1   i_side: 0   p_side: 0thumb: 10   index: 18   middle: 16   ring: 17   pinky: 18 X: 262.08  Y: 46.62  Z: 259.80
r_side 0   m_tip: 0   m_b: 1   m_side: 1   i_tip: 1   i_side: 0   p_side: 0thumb: 10   index: 18   middle: 16   ring: 17   pinky: 17 X: 263.23  Y: 46.44  Z: 261.33
r_side 0   m_tip: 0   m_b: 0   m_side: 1   i_tip: 1   i_side: 0   p_side: 0thumb: 10   index: 18   middle: 16   ring: 17   pinky: 18 X: 264.42  Y: 45.67  Z: 262.77
r_side 0   m_tip: 0   m_b: 1   m_side: 1   i_tip: 1   i_side: 0   p_side: 0thumb: 10   index: 18   middle: 16   ring: 17   pinky: 18 X: 265.13  Y: 44.73  Z: 263.36
r_side 0   m_tip: 0   m_b: 1   m_side: 1   i_tip: 1   i_side: 0   p_side: 0thumb: 10   index: 18   middle: 16   ring: 16   pinky: 17 X: 264.93  Y: 44.13  Z: 263.62
r_side 0   m_tip: 0   m_b: 0   m_side: 1   i_tip: 1   i_side: 0   p_side: 0thumb: 10   index: 18   middle: 17   ring: 16   pinky: 17 X: 266.00  Y: 43.23  Z: 264.70
r_side 0   m_tip: 0   m_b: 0   m_side: 1   i_tip: 1   i_side: 0   p_side: 0thumb: 10   index: 18   middle: 16   ring: 16   pinky: 17 X: 267.02  Y: 43.40  Z: 265.50
r_side 0   m_tip: 0   m_b: 1   m_side: 1   i_tip: 1   i_side: 0   p_side: 0thumb: 10   index: 18   middle: 16   ring: 16   pinky: 17 X: 267.54  Y: 43.07  Z: 265.24
r_side 0   m_tip: 0   m_b: 1   m_side: 1   i_tip: 1   i_side: 0   p_side: 0thumb: 10   index: 18   middle: 16   ring: 16   pinky: 17 X: 268.88  Y: 42.52  Z: 266.39
r_side 0   m_tip: 0   m_b: 1   m_side: 1   i_tip: 1   i_side: 0   p_side: 0thumb: 10   index: 18   middle: 16   ring: 16   pinky: 17 X: 269.37  Y: 42.12  Z: 266.53
r_side 0   m_tip: 0   m_b: 1   m_side: 1   i_tip: 1   i_side: 0   p_side: 0thumb: 10   index: 18   middle: 16   ring: 16   pinky: 17 X: 269.53  Y: 41.32  Z: 266.25
r_side 0   m_tip: 0   m_b: 1   m_side: 1   i_tip: 1   i_side: 0   p_side: 0thumb: 10   index: 18   middle: 16   ring: 16   pinky: 17 X: 269.49  Y: 40.87  Z: 266.46
r_side 0   m_tip: 0   m_b: 1   m_side: 1   i_tip: 1   i_side: 0   p_side: 0thumb: 10   index: 18   middle: 16   ring: 16   pinky: 17 X: 270.14  Y: 40.10  Z: 266.86
r_side 0   m_tip: 0   m_b: 1   m_side: 1   i_tip: 1   i_side: 0   p_side: 0thumb: 10   index: 18   middle: 16   ring: 16   pinky: 17 X: 270.31  Y: 39.60  Z: 267.11
r_side 0   m_tip: 0   m_b: 1   m_side: 1   i_tip: 1   i_side: 0   p_side: 0thumb: 10   index: 17   middle: 16   ring: 16   pinky: 17 X: 271.32  Y: 38.30  Z: 267.86
r_side 0   m_tip: 0   m_b: 0   m_side: 1   i_tip: 1   i_side: 0   p_side: 0thumb: 10   index: 17   middle: 16   ring: 16   pinky: 17 X: 271.54  Y: 37.46  Z: 268.31
r_side 0   m_tip: 0   m_b: 0   m_side: 1   i_tip: 1   i_side: 0   p_side: 0thumb: 9   index: 17   middle: 16   ring: 16   pinky: 17 X: 271.76  Y: 37.11  Z: 268.47
