juanmrq95/ee149_104/ASLsensing/longFlex/save_sensordata/test 1.1/testAashykLetterU.txt

ÿr_side 0   m_tip: 0   m_b: 0   m_side: 0   i_tip: 0   i_side: 0   p_side: 0thumb: 7   index: 0   middle: 1   ring: 1   pinky: 1 X: 0.13  Y: 358.31  Z: 360.00
r_side 0   m_tip: 0   m_b: 0   m_side: 0   i_tip: 0   i_side: 0   p_side: 0thumb: 7   index: 0   middle: 1   ring: 1   pinky: 1 X: 359.89  Y: 0.21  Z: 358.12
r_side 0   m_tip: 0   m_b: 0   m_side: 0   i_tip: 0   i_side: 0   p_side: 0thumb: 7   index: 0   middle: 1   ring: 2   pinky: 1 X: 359.80  Y: 1.77  Z: 356.18
r_side 0   m_tip: 0   m_b: 0   m_side: 0   i_tip: 0   i_side: 0   p_side: 0thumb: 7   index: 0   middle: 1   ring: 1   pinky: 1 X: 359.67  Y: 3.72  Z: 354.51
r_side 0   m_tip: 0   m_b: 0   m_side: 0   i_tip: 0   i_side: 0   p_side: 0thumb: 7   index: 0   middle: 1   ring: 1   pinky: 1 X: 359.42  Y: 5.23  Z: 352.75
r_side 0   m_tip: 0   m_b: 0   m_side: 0   i_tip: 0   i_side: 0   p_side: 0thumb: 8   index: 0   middle: 1   ring: 2   pinky: 1 X: 359.27  Y: 6.81  Z: 351.19
r_side 0   m_tip: 0   m_b: 0   m_side: 0   i_tip: 0   i_side: 0   p_side: 0thumb: 7   index: 0   middle: 1   ring: 1   pinky: 1 X: 359.02  Y: 7.80  Z: 349.61
r_side 0   m_tip: 0   m_b: 0   m_side: 0   i_tip: 0   i_side: 0   p_side: 0thumb: 7   index: 0   middle: 1   ring: 1   pinky: 1 X: 358.82  Y: 8.97  Z: 348.11
r_side 0   m_tip: 0   m_b: 0   m_side: 0   i_tip: 0   i_side: 0   p_side: 0thumb: 7   index: 0   middle: 1   ring: 1   pinky: 1 X: 358.55  Y: 10.07  Z: 346.89
r_side 0   m_tip: 0   m_b: 0   m_side: 0   i_tip: 0   i_side: 0   p_side: 0thumb: 7   index: 0   middle: 1   ring: 1   pinky: 1 X: 358.41  Y: 11.04  Z: 345.81
r_side 0   m_tip: 0   m_b: 0   m_side: 0   i_tip: 0   i_side: 0   p_side: 0thumb: 7   index: 0   middle: 1   ring: 1   pinky: 1 X: 358.21  Y: 12.15  Z: 344.52
r_side 0   m_tip: 0   m_b: 0   m_side: 0   i_tip: 0   i_side: 0   p_side: 0thumb: 7   index: 0   middle: 1   ring: 1   pinky: 1 X: 357.83  Y: 13.34  Z: 343.65
r_side 0   m_tip: 0   m_b: 0   m_side: 0   i_tip: 0   i_side: 0   p_side: 0thumb: 7   index: 0   middle: 1   ring: 2   pinky: 1 X: 357.62  Y: 13.97  Z: 342.52
r_side 0   m_tip: 0   m_b: 0   m_side: 0   i_tip: 0   i_side: 0   p_side: 0thumb: 7   index: 0   middle: 1   ring: 1   pinky: 1 X: 355.07  Y: 16.21  Z: 334.29
r_side 0   m_tip: 0   m_b: 0   m_side: 0   i_tip: 0   i_side: 0   p_side: 0thumb: 7   index: 3   middle: 7   ring: 11   pinky: 2 X: 345.95  Y: 34.39  Z: 330.74
r_side 0   m_tip: 0   m_b: 0   m_side: 0   i_tip: 0   i_side: 0   p_side: 0thumb: 7   index: 4   middle: 9   ring: 20   pinky: 16 X: 347.82  Y: 47.15  Z: 342.50
r_side 0   m_tip: 0   m_b: 0   m_side: 0   i_tip: 0   i_side: 0   p_side: 0thumb: 13   index: 2   middle: 3   ring: 21   pinky: 16 X: 342.65  Y: 47.67  Z: 341.03
r_side 0   m_tip: 0   m_b: 0   m_side: 0   i_tip: 0   i_side: 0   p_side: 0thumb: 12   index: 1   middle: 3   ring: 20   pinky: 15 X: 344.18  Y: 47.97  Z: 344.13
r_side 0   m_tip: 0   m_b: 0   m_side: 0   i_tip: 0   i_side: 0   p_side: 0thumb: 13   index: 1   middle: 2   ring: 20   pinky: 16 X: 345.43  Y: 49.88  Z: 346.95
r_side 0   m_tip: 0   m_b: 1   m_side: 0   i_tip: 0   i_side: 0   p_side: 0thumb: 13   index: 1   middle: 2   ring: 19   pinky: 16 X: 338.84  Y: 55.84  Z: 340.28
r_side 0   m_tip: 0   m_b: 1   m_side: 0   i_tip: 0   i_side: 0   p_side: 0thumb: 13   index: 0   middle: 2   ring: 19   pinky: 15 X: 337.63  Y: 59.79  Z: 337.83
r_side 0   m_tip: 0   m_b: 1   m_side: 0   i_tip: 0   i_side: 0   p_side: 0thumb: 13   index: 0   middle: 2   ring: 19   pinky: 15 X: 329.32  Y: 64.29  Z: 329.93
r_side 0   m_tip: 0   m_b: 1   m_side: 0   i_tip: 0   i_side: 0   p_side: 0thumb: 13   index: 0   middle: 2   ring: 19   pinky: 15 X: 323.51  Y: 65.66  Z: 323.06
r_side 0   m_tip: 0   m_b: 1   m_side: 0   i_tip: 0   i_side: 0   p_side: 0thumb: 13   index: 0   middle: 2   ring: 18   pinky: 14 X: 326.92  Y: 65.14  Z: 323.56
r_side 0   m_tip: 0   m_b: 1   m_side: 0   i_tip: 0   i_side: 0   p_side: 0thumb: 13   index: 0   middle: 2   ring: 18   pinky: 14 X: 325.30  Y: 66.42  Z: 321.65
r_side 0   m_tip: 0   m_b: 1   m_side: 0   i_tip: 0   i_side: 0   p_side: 0thumb: 13   index: 0   middle: 2   ring: 18   pinky: 14 X: 322.97  Y: 67.20  Z: 319.02
r_side 0   m_tip: 0   m_b: 1   m_side: 0   i_tip: 0   i_side: 0   p_side: 0thumb: 13   index: 0   middle: 2   ring: 18   pinky: 14 X: 318.69  Y: 67.60  Z: 314.84
r_side 0   m_tip: 0   m_b: 1   m_side: 0   i_tip: 0   i_side: 0   p_side: 0thumb: 13   index: 0   middle: 2   ring: 18   pinky: 14 X: 316.06  Y: 68.46  Z: 311.82
r_side 0   m_tip: 0   m_b: 1   m_side: 0   i_tip: 0   i_side: 0   p_side: 0thumb: 13   index: 0   middle: 2   ring: 18   pinky: 14 X: 318.15  Y: 66.76  Z: 313.45
r_side 0   m_tip: 0   m_b: 1   m_side: 0   i_tip: 0   i_side: 0   p_side: 0thumb: 13   index: 0   middle: 2   ring: 18   pinky: 14 X: 313.87  Y: 66.38  Z: 308.58
r_side 0   m_tip: 0   m_b: 1   m_side: 0   i_tip: 0   i_side: 0   p_side: 0thumb: 13   index: 0   middle: 2   ring: 18   pinky: 14 X: 312.97  Y: 66.84  Z: 308.35
r_side 0   m_tip: 0   m_b: 1   m_side: 0   i_tip: 0   i_side: 0   p_side: 0thumb: 13   index: 0   middle: 2   ring: 18   pinky: 14 X: 313.64  Y: 66.83  Z: 309.17
r_side 0   m_tip: 0   m_b: 1   m_side: 0   i_tip: 0   i_side: 0   p_side: 0thumb: 13   index: 0   middle: 2   ring: 17   pinky: 14 X: 314.61  Y: 66.40  Z: 310.12
r_side 0   m_tip: 0   m_b: 1   m_side: 0   i_tip: 0   i_side: 0   p_side: 0thumb: 13   index: 0   middle: 2   ring: 18   pinky: 14 X: 314.65  Y: 64.51  Z: 309.63
r_side 0   m_tip: 0   m_b: 1   m_side: 0   i_tip: 0   i_side: 0   p_side: 0thumb: 13   index: 0   middle: 2   ring: 17   pinky: 14 X: 315.58  Y: 62.58  Z: 309.99
r_side 0   m_tip: 0   m_b: 1   m_side: 0   i_tip: 0   i_side: 0   p_side: 0thumb: 13   index: 0   middle: 2   ring: 17   pinky: 14 X: 315.66  Y: 61.82  Z: 309.82
r_side 0   m_tip: 0   m_b: 1   m_side: 0   i_tip: 0   i_side: 0   p_side: 0thumb: 13   index: 0   middle: 2   ring: 17   pinky: 14 X: 314.80  Y: 62.14  Z: 308.91
r_side 0   m_tip: 0   m_b: 1   m_side: 0   i_tip: 0   i_side: 0   p_side: 0thumb: 13   index: 0   middle: 2   ring: 17   pinky: 13 X: 313.72  Y: 61.25  Z: 307.69
r_side 0   m_tip: 0   m_b: 1   m_side: 0   i_tip: 0   i_side: 0   p_side: 0thumb: 13   index: 0   middle: 2   ring: 17   pinky: 14 X: 314.08  Y: 60.00  Z: 308.13
r_side 0   m_tip: 0   m_b: 1   m_side: 0   i_tip: 0   i_side: 0   p_side: 0thumb: 13   index: 0   middle: 2   ring: 17   pinky: 13 X: 311.96  Y: 59.50  Z: 305.61
r_side 0   m_tip: 0   m_b: 1   m_side: 0   i_tip: 0   i_side: 0   p_side: 0thumb: 13   index: 0   middle: 2   ring: 17   pinky: 13 X: 310.96  Y: 59.01  Z: 304.87
r_side 0   m_tip: 0   m_b: 1   m_side: 0   i_tip: 0   i_side: 0   p_side: 0thumb: 13   index: 0   middle: 2   ring: 17   pinky: 13 X: 312.13  Y: 57.71  Z: 305.44
r_side 0   m_tip: 0   m_b: 1   m_side: 0   i_tip: 0   i_side: 0   p_side: 0thumb: 13   index: 0   middle: 2   ring: 17   pinky: 13 X: 309.64  Y: 57.30  Z: 303.01
r_side 0   m_tip: 0   m_b: 1   m_side: 0   i_tip: 0   i_side: 0   p_side: 0thumb: 12   index: 0   middle: 2   ring: 17   pinky: 13 X: 308.17  Y: 56.87  Z: 301.74
r_side 0   m_tip: 0   m_b: 1   m_side: 0   i_tip: 0   i_side: 0   p_side: 0thumb: 12   index: 0   middle: 2   ring: 17   pinky: 13 X: 306.05  Y: 56.31  Z: 299.52
r_side 0   m_tip: 0   m_b: 1   m_side: 0   i_tip: 0   i_side: 0   p_side: 0thumb: 12   index: 0   middle: 2   ring: 17   pinky: 12 X: 304.54  Y: 56.71  Z: 297.72
r_side 0   m_tip: 0   m_b: 1   m_side: 0   i_tip: 0   i_side: 0   p_side: 0thumb: 12   index: 0   middle: 2   ring: 16   pinky: 13 X: 305.20  Y: 55.61  Z: 298.36
r_side 0   m_tip: 0   m_b: 1   m_side: 0   i_tip: 0   i_side: 0   p_side: 0thumb: 12   index: 0   middle: 2   ring: 17   pinky: 13 X: 304.90  Y: 54.94  Z: 298.32
r_side 0   m_tip: 0   m_b: 1   m_side: 0   i_tip: 0   i_side: 0   p_side: 0thumb: 12   index: 0   middle: 2   ring: 16   pinky: 13 X: 304.95  Y: 54.21  Z: 298.54
r_side 0   m_tip: 0   m_b: 1   m_side: 0   i_tip: 0   i_side: 0   p_side: 0thumb: 12   index: 0   middle: 2   ring: 16   pinky: 13 X: 305.45  Y: 53.78  Z: 299.44
r_side 0   m_tip: 0   m_b: 1   m_side: 0   i_tip: 0   i_side: 0   p_side: 0thumb: 12   index: 0   middle: 2   ring: 16   pinky: 13 X: 304.72  Y: 53.22  Z: 298.86
r_side 0   m_tip: 0   m_b: 1   m_side: 0   i_tip: 0   i_side: 0   p_side: 0thumb: 11   index: 0   middle: 2   ring: 16   pinky: 13 X: 302.65  Y: 52.54  Z: 296.55
r_side 0   m_tip: 0   m_b: 1   m_side: 0   i_tip: 0   i_side: 0   p_side: 0thumb: 12   index: 0   middle: 2   ring: 16   pinky: 13 X: 303.04  Y: 52.42  Z: 296.71
r_side 0   m_tip: 0   m_b: 1   m_side: 0   i_tip: 0   i_side: 0   p_side: 0thumb: 11   index: 0   middle: 2   ring: 16   pinky: 13 X: 301.79  Y: 51.74  Z: 295.89
r_side 0   m_tip: 0   m_b: 1   m_side: 0   i_tip: 0   i_side: 0   p_side: 0thumb: 12   index: 0   middle: 2   ring: 16   pinky: 13 X: 301.83  Y: 51.49  Z: 295.92
r_side 0   m_tip: 0   m_b: 1   m_side: 0   i_tip: 0   i_side: 0   p_side: 0thumb: 11   index: 0   middle: 2   ring: 16   pinky: 13 X: 301.51  Y: 50.74  Z: 296.31
r_side 0   m_tip: 0   m_b: 1   m_side: 0   i_tip: 0   i_side: 0   p_side: 0thumb: 12   index: 0   middle: 2   ring: 16   pinky: 12 X: 301.59  Y: 49.60  Z: 296.58
r_side 0   m_tip: 0   m_b: 1   m_side: 0   i_tip: 0   i_side: 0   p_side: 0thumb: 11   index: 0   middle: 2   ring: 16   pinky: 12 X: 300.56  Y: 49.84  Z: 295.64
r_side 0   m_tip: 0   m_b: 1   m_side: 0   i_tip: 0   i_side: 0   p_side: 0thumb: 11   index: 0   middle: 2   ring: 16   pinky: 13 X: 300.76  Y: 49.69  Z: 296.20
r_side 0   m_tip: 0   m_b: 1   m_side: 0   i_tip: 0   i_side: 0   p_side: 0thumb: 11   index: 0   middle: 2   ring: 16   pinky: 12 X: 300.74  Y: 48.98  Z: 296.00
r_side 0   m_tip: 0   m_b: 1   m_side: 0   i_tip: 0   i_side: 0   p_side: 0thumb: 12   index: 0   middle: 2   ring: 16   pinky: 12 X: 302.05  Y: 48.50  Z: 298.42
r_side 0   m_tip: 0   m_b: 1   m_side: 0   i_tip: 0   i_side: 0   p_side: 0thumb: 11   index: 0   middle: 2   ring: 16   pinky: 12 X: 302.12  Y: 47.53  Z: 298.51
r_side 0   m_tip: 0   m_b: 1   m_side: 0   i_tip: 0   i_side: 0   p_side: 0thumb: 12   index: 0   middle: 2   ring: 16   pinky: 13 X: 302.09  Y: 46.24  Z: 298.57
