juanmrq95/ee149_104/ASLsensing/longFlex/save_sensordata/test 1.1/testAashykLetterV.txt

r_side 0   m_tip: 0   m_b: 0   m_side: 0   i_tip: 0   i_side: 0   p_side: 0thumb: 5   index: 0   middle: 2   ring: 2   pinky: 1 X: 357.14  Y: 5.47  Z: 0.52
r_side 0   m_tip: 0   m_b: 0   m_side: 0   i_tip: 0   i_side: 0   p_side: 0thumb: 5   index: 0   middle: 1   ring: 2   pinky: 1 X: 357.02  Y: 6.64  Z: 358.17
r_side 0   m_tip: 0   m_b: 0   m_side: 0   i_tip: 0   i_side: 0   p_side: 0thumb: 6   index: 0   middle: 1   ring: 1   pinky: 1 X: 356.97  Y: 7.79  Z: 356.07
r_side 0   m_tip: 0   m_b: 0   m_side: 0   i_tip: 0   i_side: 0   p_side: 0thumb: 5   index: 0   middle: 1   ring: 1   pinky: 1 X: 356.68  Y: 9.19  Z: 354.07
r_side 0   m_tip: 0   m_b: 0   m_side: 0   i_tip: 0   i_side: 0   p_side: 0thumb: 5   index: 0   middle: 1   ring: 2   pinky: 1 X: 356.44  Y: 9.61  Z: 352.29
r_side 0   m_tip: 0   m_b: 0   m_side: 0   i_tip: 0   i_side: 0   p_side: 0thumb: 6   index: 0   middle: 1   ring: 1   pinky: 1 X: 356.33  Y: 10.05  Z: 350.71
r_side 0   m_tip: 0   m_b: 0   m_side: 0   i_tip: 0   i_side: 0   p_side: 0thumb: 5   index: 0   middle: 1   ring: 2   pinky: 1 X: 356.12  Y: 10.82  Z: 348.76
r_side 0   m_tip: 0   m_b: 0   m_side: 0   i_tip: 0   i_side: 0   p_side: 0thumb: 6   index: 0   middle: 1   ring: 1   pinky: 1 X: 355.77  Y: 11.60  Z: 347.02
r_side 0   m_tip: 0   m_b: 0   m_side: 0   i_tip: 0   i_side: 0   p_side: 0thumb: 6   index: 0   middle: 1   ring: 2   pinky: 1 X: 355.42  Y: 12.24  Z: 345.47
r_side 0   m_tip: 0   m_b: 0   m_side: 0   i_tip: 0   i_side: 0   p_side: 0thumb: 5   index: 0   middle: 1   ring: 2   pinky: 1 X: 355.24  Y: 12.48  Z: 343.73
r_side 0   m_tip: 0   m_b: 0   m_side: 0   i_tip: 0   i_side: 0   p_side: 0thumb: 6   index: 0   middle: 1   ring: 1   pinky: 1 X: 353.74  Y: 11.22  Z: 336.40
r_side 0   m_tip: 0   m_b: 0   m_side: 0   i_tip: 0   i_side: 0   p_side: 0thumb: 5   index: 0   middle: 2   ring: 7   pinky: 2 X: 349.61  Y: 24.71  Z: 338.35
r_side 0   m_tip: 0   m_b: 0   m_side: 0   i_tip: 0   i_side: 0   p_side: 0thumb: 6   index: 1   middle: 10   ring: 20   pinky: 15 X: 339.31  Y: 41.88  Z: 333.18
r_side 0   m_tip: 0   m_b: 0   m_side: 0   i_tip: 0   i_side: 0   p_side: 0thumb: 15   index: 1   middle: 5   ring: 20   pinky: 17 X: 338.77  Y: 47.05  Z: 335.27
r_side 0   m_tip: 0   m_b: 0   m_side: 0   i_tip: 0   i_side: 0   p_side: 0thumb: 17   index: 0   middle: 3   ring: 20   pinky: 16 X: 339.35  Y: 51.14  Z: 335.94
r_side 0   m_tip: 0   m_b: 0   m_side: 0   i_tip: 0   i_side: 0   p_side: 0thumb: 18   index: 0   middle: 2   ring: 20   pinky: 16 X: 332.35  Y: 54.18  Z: 329.25
r_side 0   m_tip: 0   m_b: 0   m_side: 0   i_tip: 0   i_side: 0   p_side: 0thumb: 18   index: 0   middle: 2   ring: 20   pinky: 16 X: 330.12  Y: 53.49  Z: 325.54
r_side 0   m_tip: 0   m_b: 0   m_side: 0   i_tip: 0   i_side: 0   p_side: 0thumb: 18   index: 0   middle: 2   ring: 19   pinky: 16 X: 328.33  Y: 56.99  Z: 323.32
r_side 0   m_tip: 0   m_b: 0   m_side: 0   i_tip: 0   i_side: 0   p_side: 0thumb: 18   index: 0   middle: 2   ring: 19   pinky: 15 X: 330.42  Y: 56.37  Z: 325.28
r_side 0   m_tip: 0   m_b: 0   m_side: 0   i_tip: 0   i_side: 0   p_side: 0thumb: 17   index: 0   middle: 2   ring: 19   pinky: 15 X: 326.94  Y: 55.12  Z: 320.59
r_side 0   m_tip: 0   m_b: 0   m_side: 0   i_tip: 0   i_side: 0   p_side: 0thumb: 17   index: 0   middle: 2   ring: 19   pinky: 15 X: 324.30  Y: 56.61  Z: 317.79
r_side 0   m_tip: 0   m_b: 0   m_side: 0   i_tip: 0   i_side: 0   p_side: 0thumb: 17   index: 1   middle: 2   ring: 19   pinky: 15 X: 325.24  Y: 57.26  Z: 318.96
r_side 0   m_tip: 0   m_b: 0   m_side: 0   i_tip: 0   i_side: 0   p_side: 0thumb: 17   index: 0   middle: 2   ring: 19   pinky: 15 X: 325.51  Y: 54.90  Z: 319.06
r_side 0   m_tip: 0   m_b: 0   m_side: 0   i_tip: 0   i_side: 0   p_side: 0thumb: 17   index: 0   middle: 2   ring: 19   pinky: 15 X: 324.45  Y: 54.88  Z: 318.08
r_side 0   m_tip: 0   m_b: 0   m_side: 0   i_tip: 0   i_side: 0   p_side: 0thumb: 16   index: 0   middle: 2   ring: 19   pinky: 14 X: 322.18  Y: 55.07  Z: 316.12
r_side 0   m_tip: 0   m_b: 0   m_side: 0   i_tip: 0   i_side: 0   p_side: 0thumb: 16   index: 0   middle: 2   ring: 18   pinky: 14 X: 321.24  Y: 54.67  Z: 314.78
r_side 0   m_tip: 0   m_b: 0   m_side: 0   i_tip: 0   i_side: 0   p_side: 0thumb: 17   index: 0   middle: 2   ring: 19   pinky: 14 X: 321.23  Y: 55.24  Z: 315.70
r_side 0   m_tip: 0   m_b: 0   m_side: 0   i_tip: 0   i_side: 0   p_side: 0thumb: 16   index: 0   middle: 2   ring: 18   pinky: 14 X: 322.72  Y: 54.15  Z: 318.01
r_side 0   m_tip: 0   m_b: 0   m_side: 0   i_tip: 0   i_side: 0   p_side: 0thumb: 16   index: 0   middle: 2   ring: 18   pinky: 14 X: 320.02  Y: 53.22  Z: 315.37
r_side 0   m_tip: 0   m_b: 0   m_side: 0   i_tip: 0   i_side: 0   p_side: 0thumb: 16   index: 0   middle: 2   ring: 18   pinky: 14 X: 317.95  Y: 52.75  Z: 312.97
r_side 0   m_tip: 0   m_b: 0   m_side: 0   i_tip: 0   i_side: 0   p_side: 0thumb: 16   index: 0   middle: 2   ring: 18   pinky: 14 X: 316.50  Y: 53.36  Z: 311.71
r_side 0   m_tip: 0   m_b: 0   m_side: 0   i_tip: 0   i_side: 0   p_side: 0thumb: 16   index: 0   middle: 2   ring: 18   pinky: 14 X: 315.86  Y: 52.81  Z: 311.93
r_side 0   m_tip: 0   m_b: 0   m_side: 0   i_tip: 0   i_side: 0   p_side: 0thumb: 16   index: 0   middle: 2   ring: 18   pinky: 14 X: 315.82  Y: 52.10  Z: 311.97
r_side 0   m_tip: 0   m_b: 0   m_side: 0   i_tip: 0   i_side: 0   p_side: 0thumb: 16   index: 0   middle: 2   ring: 18   pinky: 14 X: 315.11  Y: 51.08  Z: 311.21
r_side 0   m_tip: 0   m_b: 0   m_side: 0   i_tip: 0   i_side: 0   p_side: 0thumb: 16   index: 0   middle: 2   ring: 18   pinky: 14 X: 314.82  Y: 51.15  Z: 310.67
r_side 0   m_tip: 0   m_b: 0   m_side: 0   i_tip: 0   i_side: 0   p_side: 0thumb: 16   index: 0   middle: 2   ring: 17   pinky: 14 X: 314.61  Y: 49.90  Z: 310.35
r_side 0   m_tip: 0   m_b: 0   m_side: 0   i_tip: 0   i_side: 0   p_side: 0thumb: 16   index: 0   middle: 2   ring: 17   pinky: 14 X: 312.15  Y: 49.93  Z: 307.86
r_side 0   m_tip: 0   m_b: 0   m_side: 0   i_tip: 0   i_side: 0   p_side: 0thumb: 16   index: 0   middle: 2   ring: 17   pinky: 13 X: 310.97  Y: 49.69  Z: 306.29
r_side 0   m_tip: 0   m_b: 0   m_side: 0   i_tip: 0   i_side: 0   p_side: 0thumb: 15   index: 0   middle: 2   ring: 17   pinky: 14 X: 311.64  Y: 49.26  Z: 307.26
r_side 0   m_tip: 0   m_b: 0   m_side: 0   i_tip: 0   i_side: 0   p_side: 0thumb: 15   index: 0   middle: 2   ring: 17   pinky: 13 X: 310.84  Y: 48.44  Z: 306.67
r_side 0   m_tip: 0   m_b: 0   m_side: 0   i_tip: 0   i_side: 0   p_side: 0thumb: 15   index: 0   middle: 2   ring: 17   pinky: 14 X: 309.44  Y: 48.69  Z: 305.14
r_side 0   m_tip: 0   m_b: 0   m_side: 0   i_tip: 0   i_side: 0   p_side: 0thumb: 15   index: 0   middle: 2   ring: 17   pinky: 13 X: 308.57  Y: 49.60  Z: 304.84
r_side 0   m_tip: 0   m_b: 0   m_side: 0   i_tip: 0   i_side: 0   p_side: 0thumb: 15   index: 0   middle: 2   ring: 17   pinky: 13 X: 308.80  Y: 48.32  Z: 305.38
r_side 0   m_tip: 0   m_b: 0   m_side: 0   i_tip: 0   i_side: 0   p_side: 0thumb: 15   index: 0   middle: 2   ring: 17   pinky: 13 X: 309.26  Y: 47.62  Z: 306.06
r_side 0   m_tip: 0   m_b: 0   m_side: 0   i_tip: 0   i_side: 0   p_side: 0thumb: 15   index: 0   middle: 1   ring: 17   pinky: 13 X: 309.34  Y: 46.43  Z: 306.19
r_side 0   m_tip: 0   m_b: 0   m_side: 0   i_tip: 0   i_side: 0   p_side: 0thumb: 15   index: 0   middle: 2   ring: 17   pinky: 13 X: 308.47  Y: 46.57  Z: 305.27
r_side 0   m_tip: 0   m_b: 0   m_side: 0   i_tip: 0   i_side: 0   p_side: 0thumb: 15   index: 0   middle: 2   ring: 17   pinky: 13 X: 308.19  Y: 46.06  Z: 305.04
r_side 0   m_tip: 0   m_b: 0   m_side: 0   i_tip: 0   i_side: 0   p_side: 0thumb: 15   index: 0   middle: 2   ring: 17   pinky: 13 X: 306.81  Y: 46.43  Z: 303.12
r_side 0   m_tip: 0   m_b: 0   m_side: 0   i_tip: 0   i_side: 0   p_side: 0thumb: 15   index: 0   middle: 2   ring: 17   pinky: 13 X: 305.21  Y: 46.26  Z: 301.72
r_side 0   m_tip: 0   m_b: 0   m_side: 0   i_tip: 0   i_side: 0   p_side: 0thumb: 15   index: 0   middle: 2   ring: 17   pinky: 13 X: 306.08  Y: 46.65  Z: 303.47
r_side 0   m_tip: 0   m_b: 0   m_side: 0   i_tip: 0   i_side: 0   p_side: 0thumb: 15   index: 0   middle: 2   ring: 17   pinky: 13 X: 308.93  Y: 45.06  Z: 307.09
r_side 0   m_tip: 0   m_b: 0   m_side: 0   i_tip: 0   i_side: 0   p_side: 0thumb: 15   index: 0   middle: 2   ring: 17   pinky: 13 X: 308.90  Y: 42.10  Z: 306.08
r_side 0   m_tip: 0   m_b: 0   m_side: 0   i_tip: 0   i_side: 0   p_side: 0thumb: 15   index: 0   middle: 2   ring: 17   pinky: 13 X: 309.64  Y: 40.55  Z: 305.79
r_side 0   m_tip: 0   m_b: 0   m_side: 0   i_tip: 0   i_side: 0   p_side: 0thumb: 15   index: 0   middle: 2   ring: 17   pinky: 13 X: 309.14  Y: 41.48  Z: 304.85
r_side 0   m_tip: 0   m_b: 0   m_side: 0   i_tip: 0   i_side: 0   p_side: 0thumb: 15   index: 0   middle: 2   ring: 17   pinky: 13 X: 311.10  Y: 39.14  Z: 306.33
r_side 0   m_tip: 0   m_b: 0   m_side: 0   i_tip: 0   i_side: 0   p_side: 0thumb: 15   index: 0   middle: 2   ring: 17   pinky: 13 X: 308.49  Y: 38.26  Z: 304.08
