juanmrq95/ee149_104/ASLsensing/longFlex/save_sensordata/test 1.1/testAashykLetterW.txt

ør_side 0   m_tip: 0   m_b: 0   m_side: 0   i_tip: 0   i_side: 0   p_side: 0thumb: 5   index: 0   middle: 2   ring: 2   pinky: 1 X: 1.18  Y: 359.75  Z: 358.82
r_side 0   m_tip: 0   m_b: 0   m_side: 0   i_tip: 0   i_side: 0   p_side: 0thumb: 7   index: 0   middle: 2   ring: 2   pinky: 2 X: 1.09  Y: 1.65  Z: 356.93
r_side 0   m_tip: 0   m_b: 0   m_side: 0   i_tip: 0   i_side: 0   p_side: 0thumb: 6   index: 0   middle: 2   ring: 2   pinky: 1 X: 0.90  Y: 3.15  Z: 355.15
r_side 0   m_tip: 0   m_b: 0   m_side: 0   i_tip: 0   i_side: 0   p_side: 0thumb: 6   index: 0   middle: 1   ring: 2   pinky: 1 X: 0.59  Y: 4.97  Z: 353.78
r_side 0   m_tip: 0   m_b: 0   m_side: 0   i_tip: 0   i_side: 0   p_side: 0thumb: 6   index: 0   middle: 2   ring: 2   pinky: 1 X: 0.36  Y: 6.08  Z: 351.98
r_side 0   m_tip: 0   m_b: 0   m_side: 0   i_tip: 0   i_side: 0   p_side: 0thumb: 7   index: 0   middle: 1   ring: 2   pinky: 1 X: 0.04  Y: 6.86  Z: 350.44
r_side 0   m_tip: 0   m_b: 0   m_side: 0   i_tip: 0   i_side: 0   p_side: 0thumb: 6   index: 0   middle: 1   ring: 2   pinky: 1 X: 359.86  Y: 7.84  Z: 348.93
r_side 0   m_tip: 0   m_b: 0   m_side: 0   i_tip: 0   i_side: 0   p_side: 0thumb: 6   index: 0   middle: 1   ring: 2   pinky: 1 X: 359.69  Y: 8.56  Z: 347.64
r_side 0   m_tip: 0   m_b: 0   m_side: 0   i_tip: 0   i_side: 0   p_side: 0thumb: 6   index: 0   middle: 2   ring: 2   pinky: 1 X: 355.51  Y: 23.83  Z: 330.44
r_side 0   m_tip: 0   m_b: 0   m_side: 0   i_tip: 0   i_side: 0   p_side: 0thumb: 7   index: 0   middle: 2   ring: 6   pinky: 16 X: 349.72  Y: 53.23  Z: 330.55
r_side 0   m_tip: 0   m_b: 0   m_side: 0   i_tip: 0   i_side: 0   p_side: 0thumb: 14   index: 0   middle: 1   ring: 5   pinky: 17 X: 349.50  Y: 57.70  Z: 331.43
r_side 0   m_tip: 0   m_b: 0   m_side: 0   i_tip: 0   i_side: 0   p_side: 0thumb: 19   index: 0   middle: 1   ring: 2   pinky: 17 X: 355.62  Y: 63.08  Z: 341.10
r_side 0   m_tip: 0   m_b: 0   m_side: 0   i_tip: 0   i_side: 0   p_side: 0thumb: 19   index: 0   middle: 2   ring: 2   pinky: 17 X: 349.78  Y: 71.55  Z: 338.74
r_side 0   m_tip: 0   m_b: 0   m_side: 0   i_tip: 0   i_side: 0   p_side: 0thumb: 19   index: 0   middle: 1   ring: 2   pinky: 17 X: 354.75  Y: 73.18  Z: 344.39
r_side 0   m_tip: 0   m_b: 0   m_side: 0   i_tip: 0   i_side: 0   p_side: 0thumb: 19   index: 0   middle: 1   ring: 2   pinky: 17 X: 352.31  Y: 73.64  Z: 342.36
r_side 0   m_tip: 0   m_b: 0   m_side: 0   i_tip: 0   i_side: 0   p_side: 0thumb: 18   index: 0   middle: 1   ring: 1   pinky: 16 X: 345.94  Y: 73.39  Z: 336.16
r_side 0   m_tip: 0   m_b: 0   m_side: 0   i_tip: 0   i_side: 0   p_side: 0thumb: 19   index: 0   middle: 2   ring: 1   pinky: 16 X: 347.52  Y: 71.91  Z: 337.66
r_side 0   m_tip: 0   m_b: 0   m_side: 0   i_tip: 0   i_side: 0   p_side: 0thumb: 19   index: 0   middle: 1   ring: 2   pinky: 16 X: 343.59  Y: 72.04  Z: 334.06
r_side 0   m_tip: 0   m_b: 0   m_side: 0   i_tip: 0   i_side: 0   p_side: 0thumb: 19   index: 0   middle: 1   ring: 1   pinky: 15 X: 343.27  Y: 72.48  Z: 334.31
r_side 0   m_tip: 0   m_b: 0   m_side: 0   i_tip: 0   i_side: 0   p_side: 0thumb: 19   index: 0   middle: 1   ring: 1   pinky: 15 X: 341.72  Y: 71.82  Z: 332.39
r_side 0   m_tip: 0   m_b: 0   m_side: 0   i_tip: 0   i_side: 0   p_side: 0thumb: 19   index: 0   middle: 1   ring: 2   pinky: 15 X: 341.71  Y: 73.65  Z: 333.78
r_side 0   m_tip: 0   m_b: 0   m_side: 0   i_tip: 0   i_side: 0   p_side: 0thumb: 18   index: 0   middle: 1   ring: 1   pinky: 15 X: 331.54  Y: 76.05  Z: 323.59
r_side 0   m_tip: 0   m_b: 0   m_side: 0   i_tip: 0   i_side: 0   p_side: 0thumb: 18   index: 0   middle: 1   ring: 1   pinky: 15 X: 330.85  Y: 75.52  Z: 322.60
r_side 0   m_tip: 0   m_b: 0   m_side: 0   i_tip: 0   i_side: 0   p_side: 0thumb: 18   index: 0   middle: 1   ring: 1   pinky: 15 X: 326.46  Y: 77.05  Z: 319.35
r_side 0   m_tip: 0   m_b: 0   m_side: 0   i_tip: 0   i_side: 0   p_side: 0thumb: 18   index: 0   middle: 1   ring: 1   pinky: 14 X: 331.29  Y: 74.76  Z: 324.07
r_side 0   m_tip: 0   m_b: 0   m_side: 0   i_tip: 0   i_side: 0   p_side: 0thumb: 18   index: 0   middle: 1   ring: 1   pinky: 14 X: 329.27  Y: 74.09  Z: 321.88
r_side 0   m_tip: 0   m_b: 0   m_side: 0   i_tip: 0   i_side: 0   p_side: 0thumb: 17   index: 0   middle: 1   ring: 1   pinky: 14 X: 322.03  Y: 72.82  Z: 313.91
r_side 0   m_tip: 0   m_b: 0   m_side: 0   i_tip: 0   i_side: 0   p_side: 0thumb: 17   index: -1   middle: 1   ring: 1   pinky: 14 X: 321.83  Y: 72.92  Z: 314.05
r_side 0   m_tip: 0   m_b: 0   m_side: 0   i_tip: 0   i_side: 0   p_side: 0thumb: 17   index: 0   middle: 1   ring: 1   pinky: 14 X: 322.41  Y: 71.97  Z: 314.48
r_side 0   m_tip: 0   m_b: 0   m_side: 0   i_tip: 0   i_side: 0   p_side: 0thumb: 17   index: 0   middle: 1   ring: 1   pinky: 14 X: 321.67  Y: 70.80  Z: 313.02
r_side 0   m_tip: 0   m_b: 0   m_side: 0   i_tip: 0   i_side: 0   p_side: 0thumb: 17   index: 0   middle: 1   ring: 1   pinky: 14 X: 322.93  Y: 71.56  Z: 315.49
r_side 0   m_tip: 0   m_b: 0   m_side: 0   i_tip: 0   i_side: 0   p_side: 0thumb: 18   index: 0   middle: 1   ring: 1   pinky: 14 X: 321.73  Y: 69.65  Z: 315.41
r_side 0   m_tip: 0   m_b: 0   m_side: 0   i_tip: 0   i_side: 0   p_side: 0thumb: 17   index: 0   middle: 1   ring: 1   pinky: 14 X: 319.59  Y: 68.81  Z: 313.09
r_side 0   m_tip: 0   m_b: 0   m_side: 0   i_tip: 0   i_side: 0   p_side: 0thumb: 17   index: 0   middle: 1   ring: 1   pinky: 13 X: 319.18  Y: 68.60  Z: 313.48
r_side 0   m_tip: 0   m_b: 0   m_side: 0   i_tip: 0   i_side: 0   p_side: 0thumb: 16   index: 0   middle: 1   ring: 1   pinky: 14 X: 319.58  Y: 68.35  Z: 312.90
r_side 0   m_tip: 0   m_b: 0   m_side: 0   i_tip: 0   i_side: 0   p_side: 0thumb: 17   index: 0   middle: 1   ring: 1   pinky: 14 X: 319.46  Y: 68.20  Z: 312.14
r_side 0   m_tip: 0   m_b: 0   m_side: 0   i_tip: 0   i_side: 0   p_side: 0thumb: 17   index: 0   middle: 1   ring: 1   pinky: 14 X: 317.80  Y: 66.84  Z: 310.62
r_side 0   m_tip: 0   m_b: 0   m_side: 0   i_tip: 0   i_side: 0   p_side: 0thumb: 17   index: 0   middle: 1   ring: 1   pinky: 13 X: 314.28  Y: 66.02  Z: 306.85
r_side 0   m_tip: 0   m_b: 0   m_side: 0   i_tip: 0   i_side: 0   p_side: 0thumb: 17   index: 0   middle: 1   ring: 1   pinky: 13 X: 311.05  Y: 65.80  Z: 303.40
r_side 0   m_tip: 0   m_b: 0   m_side: 0   i_tip: 0   i_side: 0   p_side: 0thumb: 17   index: 0   middle: 1   ring: 1   pinky: 13 X: 313.30  Y: 65.35  Z: 306.17
r_side 0   m_tip: 0   m_b: 0   m_side: 0   i_tip: 0   i_side: 0   p_side: 0thumb: 17   index: 0   middle: 1   ring: 1   pinky: 13 X: 310.16  Y: 64.76  Z: 302.96
r_side 0   m_tip: 0   m_b: 0   m_side: 0   i_tip: 0   i_side: 0   p_side: 0thumb: 17   index: 0   middle: 2   ring: 1   pinky: 13 X: 307.15  Y: 65.32  Z: 299.66
r_side 0   m_tip: 0   m_b: 0   m_side: 0   i_tip: 0   i_side: 0   p_side: 0thumb: 17   index: 0   middle: 1   ring: 1   pinky: 13 X: 307.47  Y: 64.88  Z: 300.55
r_side 0   m_tip: 0   m_b: 0   m_side: 0   i_tip: 0   i_side: 0   p_side: 0thumb: 17   index: 0   middle: 1   ring: 1   pinky: 13 X: 307.70  Y: 63.42  Z: 300.60
r_side 0   m_tip: 0   m_b: 0   m_side: 0   i_tip: 0   i_side: 0   p_side: 0thumb: 17   index: 0   middle: 1   ring: 1   pinky: 13 X: 308.28  Y: 62.57  Z: 301.17
r_side 0   m_tip: 0   m_b: 0   m_side: 0   i_tip: 0   i_side: 0   p_side: 0thumb: 17   index: 0   middle: 1   ring: 1   pinky: 13 X: 306.44  Y: 62.37  Z: 299.68
r_side 0   m_tip: 0   m_b: 0   m_side: 0   i_tip: 0   i_side: 0   p_side: 0thumb: 18   index: 0   middle: 1   ring: 1   pinky: 13 X: 305.99  Y: 63.90  Z: 299.57
r_side 0   m_tip: 0   m_b: 0   m_side: 0   i_tip: 0   i_side: 0   p_side: 0thumb: 17   index: 0   middle: 1   ring: 1   pinky: 13 X: 305.04  Y: 64.98  Z: 299.03
r_side 0   m_tip: 0   m_b: 0   m_side: 0   i_tip: 0   i_side: 0   p_side: 0thumb: 17   index: 0   middle: 1   ring: 1   pinky: 13 X: 303.52  Y: 64.91  Z: 297.72
r_side 0   m_tip: 0   m_b: 0   m_side: 0   i_tip: 0   i_side: 0   p_side: 0thumb: 17   index: 0   middle: 1   ring: 1   pinky: 13 X: 304.00  Y: 63.84  Z: 298.33
r_side 0   m_tip: 0   m_b: 0   m_side: 0   i_tip: 0   i_side: 0   p_side: 0thumb: 17   index: 0   middle: 1   ring: 1   pinky: 13 X: 305.82  Y: 62.68  Z: 300.49
r_side 0   m_tip: 0   m_b: 0   m_side: 0   i_tip: 0   i_side: 0   p_side: 0thumb: 16   index: 0   middle: 1   ring: 1   pinky: 13 X: 304.83  Y: 61.81  Z: 299.35
r_side 0   m_tip: 0   m_b: 0   m_side: 0   i_tip: 0   i_side: 0   p_side: 0thumb: 17   index: 0   middle: 1   ring: 1   pinky: 13 X: 305.53  Y: 61.39  Z: 300.14
r_side 0   m_tip: 0   m_b: 0   m_side: 0   i_tip: 0   i_side: 0   p_side: 0thumb: 17   index: 0   middle: 1   ring: 1   pinky: 13 X: 306.04  Y: 60.10  Z: 300.61
r_side 0   m_tip: 0   m_b: 0   m_side: 0   i_tip: 0   i_side: 0   p_side: 0thumb: 18   index: 0   middle: 1   ring: 1   pinky: 13 X: 307.31  Y: 56.26  Z: 301.51
r_side 0   m_tip: 0   m_b: 0   m_side: 0   i_tip: 0   i_side: 0   p_side: 0thumb: 18   index: 0   middle: 1   ring: 1   pinky: 13 X: 314.93  Y: 50.28  Z: 308.72
r_side 0   m_tip: 0   m_b: 0   m_side: 0   i_tip: 0   i_side: 0   p_side: 0thumb: 17   index: 0   middle: 1   ring: 1   pinky: 13 X: 319.59  Y: 42.33  Z: 311.38
