juanmrq95/ee149_104/ASLsensing/longFlex/save_sensordata/test 1.1/testAashykLetterX.txt

ür_side 0   m_tip: 0   m_b: 0   m_side: 0   i_tip: 0   i_side: 0   p_side: 0thumb: 6   index: 1   middle: 2   ring: 3   pinky: 2 X: 1.04  Y: 359.73  Z: 1.57
r_side 0   m_tip: 0   m_b: 0   m_side: 0   i_tip: 0   i_side: 0   p_side: 0thumb: 5   index: 1   middle: 2   ring: 2   pinky: 2 X: 1.16  Y: 1.10  Z: 359.61
r_side 0   m_tip: 0   m_b: 0   m_side: 0   i_tip: 0   i_side: 0   p_side: 0thumb: 6   index: 1   middle: 2   ring: 2   pinky: 2 X: 1.25  Y: 2.27  Z: 357.66
r_side 0   m_tip: 0   m_b: 0   m_side: 0   i_tip: 0   i_side: 0   p_side: 0thumb: 5   index: 1   middle: 2   ring: 2   pinky: 2 X: 1.24  Y: 4.14  Z: 355.85
r_side 0   m_tip: 0   m_b: 0   m_side: 0   i_tip: 0   i_side: 0   p_side: 0thumb: 5   index: 1   middle: 2   ring: 2   pinky: 2 X: 1.18  Y: 5.38  Z: 354.05
r_side 0   m_tip: 0   m_b: 0   m_side: 0   i_tip: 0   i_side: 0   p_side: 0thumb: 6   index: 1   middle: 2   ring: 2   pinky: 2 X: 1.15  Y: 6.31  Z: 352.39
r_side 0   m_tip: 0   m_b: 0   m_side: 0   i_tip: 0   i_side: 0   p_side: 0thumb: 5   index: 1   middle: 2   ring: 2   pinky: 2 X: 1.08  Y: 7.64  Z: 350.84
r_side 0   m_tip: 0   m_b: 0   m_side: 0   i_tip: 0   i_side: 0   p_side: 0thumb: 5   index: 1   middle: 2   ring: 2   pinky: 2 X: 0.97  Y: 9.14  Z: 348.40
r_side 0   m_tip: 0   m_b: 0   m_side: 0   i_tip: 0   i_side: 0   p_side: 0thumb: 5   index: 1   middle: 2   ring: 2   pinky: 2 X: 1.20  Y: 8.25  Z: 346.69
r_side 0   m_tip: 0   m_b: 0   m_side: 0   i_tip: 0   i_side: 0   p_side: 0thumb: 5   index: 1   middle: 2   ring: 2   pinky: 2 X: 0.88  Y: 10.18  Z: 345.71
r_side 0   m_tip: 0   m_b: 0   m_side: 0   i_tip: 0   i_side: 0   p_side: 0thumb: 5   index: 1   middle: 2   ring: 2   pinky: 2 X: 1.02  Y: 9.76  Z: 343.56
r_side 0   m_tip: 0   m_b: 0   m_side: 0   i_tip: 0   i_side: 0   p_side: 0thumb: 5   index: 1   middle: 2   ring: 2   pinky: 2 X: 0.90  Y: 10.46  Z: 336.90
r_side 0   m_tip: 0   m_b: 0   m_side: 0   i_tip: 0   i_side: 0   p_side: 0thumb: 5   index: 2   middle: 3   ring: 3   pinky: 2 X: 355.36  Y: 22.81  Z: 335.66
r_side 0   m_tip: 0   m_b: 0   m_side: 0   i_tip: 0   i_side: 0   p_side: 0thumb: 5   index: 2   middle: 11   ring: 13   pinky: 4 X: 346.00  Y: 40.11  Z: 330.41
r_side 0   m_tip: 0   m_b: 0   m_side: 0   i_tip: 0   i_side: 0   p_side: 0thumb: 5   index: 2   middle: 20   ring: 21   pinky: 15 X: 338.50  Y: 46.60  Z: 325.47
r_side 0   m_tip: 1   m_b: 0   m_side: 0   i_tip: 0   i_side: 0   p_side: 0thumb: 5   index: 17   middle: 22   ring: 24   pinky: 20 X: 334.52  Y: 62.61  Z: 328.02
r_side 0   m_tip: 1   m_b: 0   m_side: 0   i_tip: 0   i_side: 0   p_side: 0thumb: 18   index: 18   middle: 21   ring: 23   pinky: 20 X: 323.17  Y: 65.41  Z: 317.99
r_side 0   m_tip: 1   m_b: 0   m_side: 0   i_tip: 0   i_side: 0   p_side: 0thumb: 21   index: 19   middle: 21   ring: 23   pinky: 20 X: 322.30  Y: 63.51  Z: 316.48
r_side 0   m_tip: 1   m_b: 0   m_side: 0   i_tip: 0   i_side: 0   p_side: 0thumb: 21   index: 21   middle: 21   ring: 22   pinky: 20 X: 323.56  Y: 60.27  Z: 316.80
r_side 0   m_tip: 1   m_b: 0   m_side: 0   i_tip: 0   i_side: 0   p_side: 0thumb: 20   index: 21   middle: 21   ring: 22   pinky: 19 X: 323.35  Y: 62.35  Z: 316.98
r_side 0   m_tip: 1   m_b: 0   m_side: 0   i_tip: 0   i_side: 0   p_side: 0thumb: 21   index: 20   middle: 21   ring: 22   pinky: 19 X: 322.97  Y: 64.04  Z: 315.53
r_side 0   m_tip: 1   m_b: 0   m_side: 0   i_tip: 0   i_side: 0   p_side: 0thumb: 21   index: 20   middle: 20   ring: 22   pinky: 19 X: 320.35  Y: 65.59  Z: 311.52
r_side 0   m_tip: 1   m_b: 0   m_side: 0   i_tip: 0   i_side: 0   p_side: 0thumb: 20   index: 20   middle: 20   ring: 22   pinky: 19 X: 325.86  Y: 64.47  Z: 316.19
r_side 0   m_tip: 1   m_b: 0   m_side: 0   i_tip: 0   i_side: 0   p_side: 0thumb: 20   index: 20   middle: 20   ring: 22   pinky: 19 X: 324.02  Y: 63.16  Z: 313.00
r_side 0   m_tip: 1   m_b: 0   m_side: 0   i_tip: 0   i_side: 0   p_side: 0thumb: 20   index: 19   middle: 20   ring: 22   pinky: 19 X: 329.58  Y: 65.19  Z: 319.23
r_side 0   m_tip: 1   m_b: 0   m_side: 0   i_tip: 0   i_side: 0   p_side: 0thumb: 20   index: 19   middle: 20   ring: 22   pinky: 19 X: 325.23  Y: 65.32  Z: 314.26
r_side 0   m_tip: 1   m_b: 0   m_side: 0   i_tip: 0   i_side: 0   p_side: 0thumb: 20   index: 19   middle: 20   ring: 21   pinky: 19 X: 326.09  Y: 64.50  Z: 315.04
r_side 0   m_tip: 1   m_b: 0   m_side: 0   i_tip: 0   i_side: 0   p_side: 0thumb: 20   index: 19   middle: 20   ring: 21   pinky: 19 X: 320.52  Y: 64.62  Z: 309.05
r_side 0   m_tip: 1   m_b: 0   m_side: 0   i_tip: 0   i_side: 0   p_side: 0thumb: 19   index: 19   middle: 20   ring: 21   pinky: 19 X: 319.45  Y: 64.93  Z: 308.18
r_side 0   m_tip: 1   m_b: 0   m_side: 0   i_tip: 0   i_side: 0   p_side: 0thumb: 19   index: 19   middle: 20   ring: 21   pinky: 19 X: 319.08  Y: 64.38  Z: 307.32
r_side 0   m_tip: 1   m_b: 0   m_side: 0   i_tip: 0   i_side: 0   p_side: 0thumb: 19   index: 19   middle: 20   ring: 21   pinky: 18 X: 320.47  Y: 64.05  Z: 308.67
r_side 0   m_tip: 1   m_b: 0   m_side: 0   i_tip: 0   i_side: 0   p_side: 0thumb: 19   index: 19   middle: 20   ring: 21   pinky: 18 X: 318.30  Y: 63.47  Z: 306.10
r_side 0   m_tip: 1   m_b: 0   m_side: 0   i_tip: 0   i_side: 0   p_side: 0thumb: 19   index: 19   middle: 20   ring: 21   pinky: 18 X: 317.87  Y: 63.14  Z: 305.38
r_side 0   m_tip: 1   m_b: 0   m_side: 0   i_tip: 0   i_side: 0   p_side: 0thumb: 19   index: 19   middle: 20   ring: 21   pinky: 18 X: 317.39  Y: 62.12  Z: 304.35
r_side 0   m_tip: 1   m_b: 0   m_side: 0   i_tip: 0   i_side: 0   p_side: 0thumb: 19   index: 19   middle: 20   ring: 21   pinky: 18 X: 315.66  Y: 62.27  Z: 302.46
r_side 0   m_tip: 1   m_b: 0   m_side: 0   i_tip: 0   i_side: 0   p_side: 0thumb: 19   index: 18   middle: 20   ring: 21   pinky: 18 X: 313.47  Y: 61.83  Z: 300.43
r_side 0   m_tip: 1   m_b: 0   m_side: 0   i_tip: 0   i_side: 0   p_side: 0thumb: 19   index: 19   middle: 20   ring: 21   pinky: 18 X: 315.22  Y: 61.32  Z: 302.03
r_side 0   m_tip: 1   m_b: 0   m_side: 0   i_tip: 0   i_side: 0   p_side: 0thumb: 19   index: 18   middle: 20   ring: 20   pinky: 18 X: 311.35  Y: 61.71  Z: 297.41
r_side 0   m_tip: 1   m_b: 0   m_side: 0   i_tip: 0   i_side: 0   p_side: 0thumb: 19   index: 18   middle: 20   ring: 21   pinky: 18 X: 312.56  Y: 62.39  Z: 299.56
r_side 0   m_tip: 1   m_b: 0   m_side: 0   i_tip: 0   i_side: 0   p_side: 0thumb: 19   index: 18   middle: 20   ring: 20   pinky: 17 X: 310.87  Y: 63.52  Z: 297.46
r_side 0   m_tip: 1   m_b: 0   m_side: 0   i_tip: 0   i_side: 0   p_side: 0thumb: 19   index: 18   middle: 20   ring: 21   pinky: 18 X: 311.16  Y: 63.68  Z: 297.60
r_side 0   m_tip: 1   m_b: 0   m_side: 0   i_tip: 0   i_side: 0   p_side: 0thumb: 19   index: 18   middle: 20   ring: 21   pinky: 18 X: 314.05  Y: 63.47  Z: 300.43
r_side 0   m_tip: 1   m_b: 0   m_side: 0   i_tip: 0   i_side: 0   p_side: 0thumb: 19   index: 18   middle: 20   ring: 20   pinky: 18 X: 313.26  Y: 62.27  Z: 299.64
r_side 0   m_tip: 1   m_b: 0   m_side: 0   i_tip: 0   i_side: 0   p_side: 0thumb: 19   index: 18   middle: 20   ring: 20   pinky: 18 X: 311.88  Y: 62.16  Z: 298.06
r_side 0   m_tip: 1   m_b: 0   m_side: 0   i_tip: 0   i_side: 0   p_side: 0thumb: 18   index: 18   middle: 19   ring: 20   pinky: 18 X: 311.56  Y: 61.79  Z: 297.71
r_side 0   m_tip: 1   m_b: 0   m_side: 0   i_tip: 0   i_side: 0   p_side: 0thumb: 18   index: 18   middle: 19   ring: 20   pinky: 18 X: 312.34  Y: 60.94  Z: 297.99
r_side 0   m_tip: 1   m_b: 0   m_side: 0   i_tip: 0   i_side: 0   p_side: 0thumb: 18   index: 18   middle: 19   ring: 20   pinky: 18 X: 312.14  Y: 59.61  Z: 297.42
r_side 0   m_tip: 1   m_b: 0   m_side: 0   i_tip: 0   i_side: 0   p_side: 0thumb: 18   index: 18   middle: 19   ring: 20   pinky: 18 X: 311.04  Y: 59.48  Z: 296.60
r_side 0   m_tip: 1   m_b: 0   m_side: 0   i_tip: 0   i_side: 0   p_side: 0thumb: 18   index: 18   middle: 19   ring: 20   pinky: 18 X: 314.98  Y: 58.08  Z: 300.40
r_side 0   m_tip: 1   m_b: 0   m_side: 0   i_tip: 0   i_side: 0   p_side: 0thumb: 18   index: 18   middle: 19   ring: 20   pinky: 18 X: 315.10  Y: 58.29  Z: 300.53
r_side 0   m_tip: 1   m_b: 0   m_side: 0   i_tip: 0   i_side: 0   p_side: 0thumb: 18   index: 18   middle: 19   ring: 20   pinky: 18 X: 316.97  Y: 57.96  Z: 302.50
r_side 0   m_tip: 1   m_b: 0   m_side: 0   i_tip: 0   i_side: 0   p_side: 0thumb: 18   index: 18   middle: 19   ring: 20   pinky: 18 X: 316.73  Y: 57.56  Z: 302.28
r_side 0   m_tip: 1   m_b: 0   m_side: 0   i_tip: 0   i_side: 0   p_side: 0thumb: 19   index: 18   middle: 19   ring: 20   pinky: 18 X: 315.85  Y: 57.49  Z: 301.44
