juanmrq95/ee149_104/ASLsensing/longFlex/save_sensordata/test 1.1/testAashykLetterY.txt

ºr_side 0   m_tip: 0   m_b: 0   m_side: 0   i_tip: 0   i_side: 0   p_side: 0thumb: 6   index: 1   middle: 2   ring: 1   pinky: 2 X: 359.72  Y: 358.83  Z: 1.71
r_side 0   m_tip: 0   m_b: 0   m_side: 0   i_tip: 0   i_side: 0   p_side: 0thumb: 5   index: 1   middle: 2   ring: 2   pinky: 2 X: 359.64  Y: 0.69  Z: 359.67
r_side 0   m_tip: 0   m_b: 0   m_side: 0   i_tip: 0   i_side: 0   p_side: 0thumb: 6   index: 1   middle: 2   ring: 2   pinky: 2 X: 359.43  Y: 2.59  Z: 357.79
r_side 0   m_tip: 0   m_b: 0   m_side: 0   i_tip: 0   i_side: 0   p_side: 0thumb: 5   index: 0   middle: 2   ring: 2   pinky: 2 X: 359.41  Y: 3.82  Z: 355.61
r_side 0   m_tip: 0   m_b: 0   m_side: 0   i_tip: 0   i_side: 0   p_side: 0thumb: 5   index: 1   middle: 2   ring: 2   pinky: 2 X: 359.24  Y: 5.05  Z: 353.76
r_side 0   m_tip: 0   m_b: 0   m_side: 0   i_tip: 0   i_side: 0   p_side: 0thumb: 5   index: 1   middle: 2   ring: 2   pinky: 2 X: 359.09  Y: 6.14  Z: 352.27
r_side 0   m_tip: 0   m_b: 0   m_side: 0   i_tip: 0   i_side: 0   p_side: 0thumb: 5   index: 1   middle: 2   ring: 2   pinky: 2 X: 359.06  Y: 7.65  Z: 350.67
r_side 0   m_tip: 0   m_b: 0   m_side: 0   i_tip: 0   i_side: 0   p_side: 0thumb: 5   index: 1   middle: 2   ring: 2   pinky: 2 X: 358.71  Y: 9.82  Z: 348.06
r_side 0   m_tip: 0   m_b: 0   m_side: 0   i_tip: 0   i_side: 0   p_side: 0thumb: 5   index: 1   middle: 2   ring: 2   pinky: 2 X: 357.52  Y: 16.78  Z: 343.66
r_side 0   m_tip: 0   m_b: 0   m_side: 0   i_tip: 0   i_side: 0   p_side: 0thumb: 5   index: 9   middle: 11   ring: 13   pinky: 2 X: 357.82  Y: 37.31  Z: 348.80
r_side 0   m_tip: 0   m_b: 0   m_side: 0   i_tip: 0   i_side: 0   p_side: 0thumb: 5   index: 23   middle: 22   ring: 23   pinky: 15 X: 0.39  Y: 47.12  Z: 347.34
r_side 0   m_tip: 0   m_b: 0   m_side: 0   i_tip: 0   i_side: 0   p_side: 0thumb: 5   index: 23   middle: 22   ring: 22   pinky: 11 X: 0.15  Y: 48.13  Z: 344.37
r_side 0   m_tip: 0   m_b: 0   m_side: 0   i_tip: 0   i_side: 0   p_side: 0thumb: 5   index: 22   middle: 21   ring: 21   pinky: 3 X: 357.92  Y: 45.35  Z: 339.68
r_side 0   m_tip: 0   m_b: 0   m_side: 0   i_tip: 0   i_side: 0   p_side: 0thumb: 5   index: 21   middle: 21   ring: 20   pinky: 3 X: 353.87  Y: 54.52  Z: 335.14
r_side 0   m_tip: 0   m_b: 0   m_side: 0   i_tip: 0   i_side: 0   p_side: 0thumb: 5   index: 21   middle: 20   ring: 20   pinky: 3 X: 343.80  Y: 58.53  Z: 325.15
r_side 0   m_tip: 0   m_b: 0   m_side: 0   i_tip: 0   i_side: 0   p_side: 0thumb: 5   index: 21   middle: 20   ring: 20   pinky: 3 X: 332.75  Y: 61.27  Z: 315.75
r_side 0   m_tip: 0   m_b: 0   m_side: 0   i_tip: 0   i_side: 0   p_side: 0thumb: 4   index: 20   middle: 20   ring: 20   pinky: 2 X: 321.07  Y: 60.95  Z: 304.87
r_side 0   m_tip: 0   m_b: 0   m_side: 0   i_tip: 0   i_side: 0   p_side: 0thumb: 4   index: 21   middle: 20   ring: 19   pinky: 2 X: 311.24  Y: 62.95  Z: 297.02
r_side 0   m_tip: 0   m_b: 0   m_side: 0   i_tip: 0   i_side: 0   p_side: 0thumb: 4   index: 20   middle: 20   ring: 19   pinky: 2 X: 311.46  Y: 63.22  Z: 296.07
r_side 0   m_tip: 0   m_b: 0   m_side: 0   i_tip: 0   i_side: 0   p_side: 0thumb: 4   index: 20   middle: 20   ring: 19   pinky: 2 X: 310.54  Y: 63.13  Z: 295.70
r_side 0   m_tip: 0   m_b: 0   m_side: 0   i_tip: 0   i_side: 0   p_side: 0thumb: 4   index: 20   middle: 20   ring: 19   pinky: 2 X: 308.61  Y: 63.00  Z: 294.41
r_side 0   m_tip: 0   m_b: 0   m_side: 0   i_tip: 0   i_side: 0   p_side: 0thumb: 4   index: 20   middle: 20   ring: 19   pinky: 2 X: 308.82  Y: 63.98  Z: 294.91
r_side 0   m_tip: 0   m_b: 0   m_side: 0   i_tip: 0   i_side: 0   p_side: 0thumb: 4   index: 20   middle: 20   ring: 18   pinky: 2 X: 308.87  Y: 64.61  Z: 293.09
r_side 0   m_tip: 0   m_b: 0   m_side: 0   i_tip: 0   i_side: 0   p_side: 0thumb: 4   index: 20   middle: 19   ring: 19   pinky: 2 X: 309.92  Y: 63.85  Z: 293.49
r_side 0   m_tip: 0   m_b: 0   m_side: 0   i_tip: 0   i_side: 0   p_side: 0thumb: 4   index: 20   middle: 19   ring: 18   pinky: 2 X: 306.29  Y: 64.64  Z: 290.17
r_side 0   m_tip: 0   m_b: 0   m_side: 0   i_tip: 0   i_side: 0   p_side: 0thumb: 4   index: 20   middle: 19   ring: 18   pinky: 2 X: 303.50  Y: 63.43  Z: 285.51
r_side 0   m_tip: 0   m_b: 0   m_side: 0   i_tip: 0   i_side: 0   p_side: 0thumb: 3   index: 20   middle: 19   ring: 18   pinky: 2 X: 305.61  Y: 64.72  Z: 287.52
r_side 0   m_tip: 0   m_b: 0   m_side: 0   i_tip: 0   i_side: 0   p_side: 0thumb: 4   index: 20   middle: 19   ring: 18   pinky: 2 X: 304.02  Y: 64.96  Z: 286.33
r_side 0   m_tip: 0   m_b: 0   m_side: 0   i_tip: 0   i_side: 0   p_side: 0thumb: 4   index: 20   middle: 19   ring: 18   pinky: 2 X: 306.46  Y: 64.47  Z: 288.07
r_side 0   m_tip: 0   m_b: 0   m_side: 0   i_tip: 0   i_side: 0   p_side: 0thumb: 4   index: 20   middle: 19   ring: 18   pinky: 2 X: 304.60  Y: 63.87  Z: 287.10
r_side 0   m_tip: 0   m_b: 0   m_side: 0   i_tip: 0   i_side: 0   p_side: 0thumb: 4   index: 20   middle: 19   ring: 18   pinky: 2 X: 304.01  Y: 62.20  Z: 286.02
r_side 0   m_tip: 0   m_b: 0   m_side: 0   i_tip: 0   i_side: 0   p_side: 0thumb: 4   index: 19   middle: 19   ring: 18   pinky: 2 X: 303.15  Y: 63.98  Z: 285.42
r_side 0   m_tip: 0   m_b: 0   m_side: 0   i_tip: 0   i_side: 0   p_side: 0thumb: 3   index: 19   middle: 19   ring: 18   pinky: 3 X: 299.61  Y: 64.05  Z: 282.11
r_side 0   m_tip: 0   m_b: 0   m_side: 0   i_tip: 0   i_side: 0   p_side: 0thumb: 4   index: 19   middle: 19   ring: 18   pinky: 2 X: 297.14  Y: 65.43  Z: 280.76
r_side 0   m_tip: 0   m_b: 0   m_side: 0   i_tip: 0   i_side: 0   p_side: 0thumb: 4   index: 19   middle: 19   ring: 18   pinky: 2 X: 296.12  Y: 65.81  Z: 280.08
r_side 0   m_tip: 0   m_b: 0   m_side: 0   i_tip: 0   i_side: 0   p_side: 0thumb: 4   index: 19   middle: 19   ring: 18   pinky: 2 X: 296.44  Y: 64.07  Z: 279.94
r_side 0   m_tip: 0   m_b: 0   m_side: 0   i_tip: 0   i_side: 0   p_side: 0thumb: 4   index: 20   middle: 19   ring: 18   pinky: 2 X: 294.55  Y: 63.07  Z: 278.25
r_side 0   m_tip: 0   m_b: 0   m_side: 0   i_tip: 0   i_side: 0   p_side: 0thumb: 4   index: 20   middle: 19   ring: 18   pinky: 3 X: 295.39  Y: 62.58  Z: 278.92
r_side 0   m_tip: 0   m_b: 0   m_side: 0   i_tip: 0   i_side: 0   p_side: 0thumb: 4   index: 19   middle: 18   ring: 18   pinky: 2 X: 294.08  Y: 62.11  Z: 277.89
r_side 0   m_tip: 0   m_b: 0   m_side: 0   i_tip: 0   i_side: 0   p_side: 0thumb: 4   index: 19   middle: 19   ring: 18   pinky: 2 X: 292.07  Y: 61.49  Z: 275.79
r_side 0   m_tip: 0   m_b: 0   m_side: 0   i_tip: 0   i_side: 0   p_side: 0thumb: 4   index: 19   middle: 19   ring: 18   pinky: 2 X: 291.21  Y: 60.90  Z: 274.81
r_side 0   m_tip: 0   m_b: 0   m_side: 0   i_tip: 0   i_side: 0   p_side: 0thumb: 3   index: 19   middle: 19   ring: 17   pinky: 2 X: 292.42  Y: 59.99  Z: 275.55
r_side 0   m_tip: 0   m_b: 0   m_side: 0   i_tip: 0   i_side: 0   p_side: 0thumb: 3   index: 19   middle: 19   ring: 18   pinky: 2 X: 294.60  Y: 59.12  Z: 276.82
r_side 0   m_tip: 0   m_b: 0   m_side: 0   i_tip: 0   i_side: 0   p_side: 0thumb: 4   index: 19   middle: 19   ring: 18   pinky: 2 X: 296.24  Y: 58.71  Z: 278.39
r_side 0   m_tip: 0   m_b: 0   m_side: 0   i_tip: 0   i_side: 0   p_side: 0thumb: 5   index: 20   middle: 19   ring: 18   pinky: 3 X: 295.12  Y: 57.52  Z: 277.75
r_side 0   m_tip: 0   m_b: 0   m_side: 0   i_tip: 0   i_side: 0   p_side: 0thumb: 4   index: 19   middle: 19   ring: 18   pinky: 2 X: 295.95  Y: 56.97  Z: 278.21
r_side 0   m_tip: 0   m_b: 0   m_side: 0   i_tip: 0   i_side: 0   p_side: 0thumb: 4   index: 19   middle: 19   ring: 18   pinky: 2 X: 297.19  Y: 57.28  Z: 279.29
r_side 0   m_tip: 0   m_b: 0   m_side: 0   i_tip: 0   i_side: 0   p_side: 0thumb: 4   index: 19   middle: 18   ring: 17   pinky: 2 X: 296.36  Y: 56.42  Z: 278.50
r_side 0   m_tip: 0   m_b: 0   m_side: 0   i_tip: 0   i_side: 0   p_side: 0thumb: 4   index: 19   middle: 18   ring: 18   pinky: 2 X: 296.86  Y: 56.37  Z: 278.86
r_side 0   m_tip: 0   m_b: 0   m_side: 0   i_tip: 0   i_side: 0   p_side: 0thumb: 4   index: 19   middle: 18   ring: 18   pinky: 2 X: 296.30  Y: 55.63  Z: 278.60
r_side 0   m_tip: 0   m_b: 0   m_side: 0   i_tip: 0   i_side: 0   p_side: 0thumb: 4   index: 19   middle: 18   ring: 17   pinky: 2 X: 296.04  Y: 55.79  Z: 278.68
r_side 0   m_tip: 0   m_b: 0   m_side: 0   i_tip: 0   i_side: 0   p_side: 0thumb: 4   index: 20   middle: 19   ring: 18   pinky: 2 X: 296.59  Y: 54.76  Z: 279.70
