juanmrq95/ee149_104/ASLsensing/longFlex/save_sensordata/test 1.1/testAashykLetterZ.txt

ór_side 0   m_tip: 0   m_b: 0   m_side: 0   i_tip: 0   i_side: 0   p_side: 0thumb: 6   index: -21   middle: 3   ring: 2   pinky: 1 X: 359.61  Y: 359.09  Z: 0.13
r_side 0   m_tip: 0   m_b: 0   m_side: 0   i_tip: 0   i_side: 0   p_side: 0thumb: 6   index: -22   middle: 3   ring: 2   pinky: 1 X: 359.61  Y: 0.94  Z: 358.27
r_side 0   m_tip: 0   m_b: 0   m_side: 0   i_tip: 0   i_side: 0   p_side: 0thumb: 6   index: -22   middle: 2   ring: 2   pinky: 1 X: 359.43  Y: 2.54  Z: 356.37
r_side 0   m_tip: 0   m_b: 0   m_side: 0   i_tip: 0   i_side: 0   p_side: 0thumb: 6   index: -22   middle: 3   ring: 2   pinky: 1 X: 359.32  Y: 3.94  Z: 354.60
r_side 0   m_tip: 0   m_b: 0   m_side: 0   i_tip: 0   i_side: 0   p_side: 0thumb: 8   index: -22   middle: 2   ring: 2   pinky: 1 X: 359.22  Y: 4.95  Z: 353.03
r_side 0   m_tip: 0   m_b: 0   m_side: 0   i_tip: 0   i_side: 0   p_side: 0thumb: 6   index: -22   middle: 2   ring: 2   pinky: 1 X: 358.95  Y: 6.33  Z: 351.73
r_side 0   m_tip: 0   m_b: 0   m_side: 0   i_tip: 0   i_side: 0   p_side: 0thumb: 6   index: -22   middle: 3   ring: 2   pinky: 1 X: 358.70  Y: 7.95  Z: 350.19
r_side 0   m_tip: 0   m_b: 0   m_side: 0   i_tip: 0   i_side: 0   p_side: 0thumb: 6   index: -22   middle: 2   ring: 2   pinky: 1 X: 358.46  Y: 8.38  Z: 348.58
r_side 0   m_tip: 0   m_b: 0   m_side: 0   i_tip: 0   i_side: 0   p_side: 0thumb: 6   index: -22   middle: 2   ring: 2   pinky: 2 X: 355.17  Y: 10.18  Z: 339.31
r_side 0   m_tip: 0   m_b: 0   m_side: 0   i_tip: 0   i_side: 0   p_side: 0thumb: 7   index: 1   middle: 6   ring: 7   pinky: 2 X: 344.10  Y: 24.31  Z: 331.16
r_side 0   m_tip: 0   m_b: 0   m_side: 0   i_tip: 0   i_side: 0   p_side: 0thumb: 7   index: 3   middle: 22   ring: 24   pinky: 19 X: 334.13  Y: 26.18  Z: 327.67
r_side 0   m_tip: 1   m_b: 0   m_side: 0   i_tip: 0   i_side: 0   p_side: 0thumb: 10   index: 7   middle: 21   ring: 23   pinky: 20 X: 319.86  Y: 25.10  Z: 316.06
r_side 0   m_tip: 1   m_b: 0   m_side: 0   i_tip: 0   i_side: 0   p_side: 0thumb: 13   index: 2   middle: 21   ring: 22   pinky: 19 X: 315.24  Y: 26.77  Z: 313.95
r_side 0   m_tip: 1   m_b: 0   m_side: 0   i_tip: 0   i_side: 0   p_side: 0thumb: 17   index: 1   middle: 20   ring: 22   pinky: 19 X: 313.69  Y: 22.44  Z: 313.90
r_side 0   m_tip: 1   m_b: 0   m_side: 0   i_tip: 0   i_side: 0   p_side: 0thumb: 18   index: 1   middle: 20   ring: 21   pinky: 19 X: 313.91  Y: 21.17  Z: 314.04
r_side 0   m_tip: 1   m_b: 0   m_side: 0   i_tip: 0   i_side: 0   p_side: 0thumb: 17   index: 1   middle: 20   ring: 21   pinky: 19 X: 312.73  Y: 22.08  Z: 312.84
r_side 0   m_tip: 1   m_b: 0   m_side: 0   i_tip: 0   i_side: 0   p_side: 0thumb: 17   index: 1   middle: 19   ring: 21   pinky: 19 X: 312.27  Y: 21.96  Z: 312.00
r_side 0   m_tip: 1   m_b: 0   m_side: 0   i_tip: 0   i_side: 0   p_side: 0thumb: 17   index: 1   middle: 19   ring: 21   pinky: 18 X: 310.25  Y: 22.84  Z: 310.73
r_side 0   m_tip: 1   m_b: 0   m_side: 0   i_tip: 0   i_side: 0   p_side: 0thumb: 17   index: 1   middle: 19   ring: 21   pinky: 18 X: 310.56  Y: 22.51  Z: 311.37
r_side 0   m_tip: 1   m_b: 0   m_side: 0   i_tip: 0   i_side: 0   p_side: 0thumb: 17   index: 1   middle: 19   ring: 21   pinky: 18 X: 309.81  Y: 22.53  Z: 310.72
r_side 0   m_tip: 1   m_b: 0   m_side: 0   i_tip: 0   i_side: 0   p_side: 0thumb: 17   index: 1   middle: 19   ring: 20   pinky: 18 X: 308.69  Y: 22.78  Z: 310.11
r_side 0   m_tip: 1   m_b: 0   m_side: 0   i_tip: 0   i_side: 0   p_side: 0thumb: 16   index: 1   middle: 19   ring: 20   pinky: 18 X: 310.33  Y: 21.83  Z: 311.92
r_side 0   m_tip: 1   m_b: 0   m_side: 0   i_tip: 0   i_side: 0   p_side: 0thumb: 16   index: 1   middle: 19   ring: 21   pinky: 18 X: 308.83  Y: 22.38  Z: 310.64
r_side 0   m_tip: 1   m_b: 0   m_side: 0   i_tip: 0   i_side: 0   p_side: 0thumb: 16   index: 1   middle: 19   ring: 20   pinky: 18 X: 308.98  Y: 21.96  Z: 311.16
r_side 0   m_tip: 1   m_b: 0   m_side: 0   i_tip: 0   i_side: 0   p_side: 0thumb: 16   index: 1   middle: 19   ring: 20   pinky: 18 X: 311.08  Y: 21.20  Z: 313.05
r_side 0   m_tip: 1   m_b: 0   m_side: 0   i_tip: 0   i_side: 0   p_side: 0thumb: 16   index: 1   middle: 19   ring: 20   pinky: 18 X: 309.97  Y: 21.58  Z: 312.38
r_side 0   m_tip: 1   m_b: 0   m_side: 0   i_tip: 0   i_side: 0   p_side: 0thumb: 16   index: 1   middle: 19   ring: 20   pinky: 18 X: 308.00  Y: 22.38  Z: 310.30
r_side 0   m_tip: 1   m_b: 0   m_side: 0   i_tip: 0   i_side: 0   p_side: 0thumb: 16   index: 1   middle: 18   ring: 20   pinky: 18 X: 308.98  Y: 21.67  Z: 311.53
r_side 0   m_tip: 1   m_b: 0   m_side: 0   i_tip: 0   i_side: 0   p_side: 0thumb: 16   index: 0   middle: 18   ring: 20   pinky: 18 X: 309.23  Y: 21.16  Z: 312.25
r_side 0   m_tip: 1   m_b: 0   m_side: 0   i_tip: 0   i_side: 0   p_side: 0thumb: 16   index: 1   middle: 18   ring: 20   pinky: 18 X: 308.01  Y: 21.59  Z: 311.48
r_side 0   m_tip: 1   m_b: 0   m_side: 0   i_tip: 0   i_side: 0   p_side: 0thumb: 16   index: 0   middle: 18   ring: 20   pinky: 18 X: 308.69  Y: 21.33  Z: 312.12
r_side 0   m_tip: 1   m_b: 0   m_side: 0   i_tip: 0   i_side: 0   p_side: 0thumb: 16   index: 0   middle: 18   ring: 20   pinky: 17 X: 308.68  Y: 21.25  Z: 312.22
r_side 0   m_tip: 1   m_b: 0   m_side: 0   i_tip: 0   i_side: 0   p_side: 0thumb: 15   index: 0   middle: 18   ring: 20   pinky: 18 X: 308.08  Y: 21.44  Z: 311.60
r_side 0   m_tip: 1   m_b: 0   m_side: 0   i_tip: 0   i_side: 0   p_side: 0thumb: 15   index: 0   middle: 18   ring: 19   pinky: 18 X: 306.87  Y: 21.55  Z: 310.56
r_side 0   m_tip: 1   m_b: 0   m_side: 0   i_tip: 0   i_side: 0   p_side: 0thumb: 15   index: 0   middle: 18   ring: 19   pinky: 17 X: 306.48  Y: 21.62  Z: 310.27
r_side 0   m_tip: 1   m_b: 0   m_side: 0   i_tip: 0   i_side: 0   p_side: 0thumb: 15   index: 0   middle: 18   ring: 19   pinky: 17 X: 306.87  Y: 21.21  Z: 310.75
r_side 0   m_tip: 1   m_b: 0   m_side: 0   i_tip: 0   i_side: 0   p_side: 0thumb: 15   index: 0   middle: 18   ring: 19   pinky: 17 X: 306.38  Y: 20.98  Z: 310.37
r_side 0   m_tip: 1   m_b: 0   m_side: 0   i_tip: 0   i_side: 0   p_side: 0thumb: 15   index: 1   middle: 18   ring: 19   pinky: 17 X: 305.80  Y: 20.91  Z: 310.06
r_side 0   m_tip: 1   m_b: 0   m_side: 0   i_tip: 0   i_side: 0   p_side: 0thumb: 15   index: 0   middle: 18   ring: 19   pinky: 17 X: 305.90  Y: 21.06  Z: 310.70
r_side 0   m_tip: 1   m_b: 0   m_side: 0   i_tip: 0   i_side: 0   p_side: 0thumb: 15   index: 0   middle: 18   ring: 19   pinky: 17 X: 305.74  Y: 20.91  Z: 311.06
r_side 0   m_tip: 1   m_b: 0   m_side: 0   i_tip: 0   i_side: 0   p_side: 0thumb: 15   index: 0   middle: 18   ring: 19   pinky: 17 X: 305.15  Y: 20.85  Z: 310.61
r_side 0   m_tip: 1   m_b: 0   m_side: 0   i_tip: 0   i_side: 0   p_side: 0thumb: 15   index: 0   middle: 18   ring: 19   pinky: 17 X: 305.33  Y: 20.83  Z: 311.24
r_side 0   m_tip: 1   m_b: 0   m_side: 0   i_tip: 0   i_side: 0   p_side: 0thumb: 15   index: 0   middle: 18   ring: 19   pinky: 17 X: 305.62  Y: 20.31  Z: 311.68
r_side 0   m_tip: 1   m_b: 0   m_side: 0   i_tip: 0   i_side: 0   p_side: 0thumb: 15   index: 0   middle: 18   ring: 19   pinky: 17 X: 306.04  Y: 19.55  Z: 311.78
r_side 0   m_tip: 1   m_b: 0   m_side: 0   i_tip: 0   i_side: 0   p_side: 0thumb: 15   index: 0   middle: 18   ring: 19   pinky: 17 X: 305.91  Y: 19.21  Z: 312.11
r_side 0   m_tip: 1   m_b: 0   m_side: 0   i_tip: 0   i_side: 0   p_side: 0thumb: 15   index: 0   middle: 18   ring: 19   pinky: 17 X: 305.70  Y: 18.95  Z: 311.95
r_side 0   m_tip: 1   m_b: 0   m_side: 0   i_tip: 0   i_side: 0   p_side: 0thumb: 15   index: 0   middle: 18   ring: 19   pinky: 17 X: 305.04  Y: 18.64  Z: 311.57
r_side 0   m_tip: 1   m_b: 0   m_side: 0   i_tip: 0   i_side: 0   p_side: 0thumb: 15   index: 0   middle: 18   ring: 19   pinky: 17 X: 304.31  Y: 18.93  Z: 311.23
r_side 0   m_tip: 1   m_b: 0   m_side: 0   i_tip: 0   i_side: 0   p_side: 0thumb: 14   index: 0   middle: 18   ring: 19   pinky: 17 X: 303.76  Y: 18.73  Z: 311.04
r_side 0   m_tip: 1   m_b: 0   m_side: 0   i_tip: 0   i_side: 0   p_side: 0thumb: 15   index: 0   middle: 18   ring: 19   pinky: 17 X: 303.53  Y: 18.68  Z: 310.95
r_side 0   m_tip: 1   m_b: 0   m_side: 0   i_tip: 0   i_side: 0   p_side: 0thumb: 15   index: 0   middle: 18   ring: 18   pinky: 17 X: 303.51  Y: 18.38  Z: 311.00
r_side 0   m_tip: 1   m_b: 0   m_side: 0   i_tip: 0   i_side: 0   p_side: 0thumb: 15   index: 0   middle: 18   ring: 19   pinky: 17 X: 303.71  Y: 17.92  Z: 311.00
r_side 0   m_tip: 1   m_b: 0   m_side: 0   i_tip: 0   i_side: 0   p_side: 0thumb: 15   index: 0   middle: 18   ring: 19   pinky: 17 X: 303.64  Y: 18.00  Z: 311.41
r_side 0   m_tip: 1   m_b: 0   m_side: 0   i_tip: 0   i_side: 0   p_side: 0thumb: 15   index: 0   middle: 18   ring: 19   pinky: 17 X: 303.39  Y: 17.72  Z: 311.28
