juanmrq95/ee149_104/ASLsensing/longFlex/save_sensordata/Test 2 Juan/testJuanLetterA.txt

r_side 0   m_tip: 0   m_b: 0   m_side: 0   i_tip: 0   i_side: 0   p_side: 0thumb: 2   index: 2   middle: 3   ring: 4   pinky: 1 X: 359.21  Y: 0.13  Z: 359.87
r_side 0   m_tip: 0   m_b: 0   m_side: 0   i_tip: 0   i_side: 0   p_side: 0thumb: 2   index: 2   middle: 3   ring: 4   pinky: 1 X: 359.30  Y: 2.66  Z: 357.60
r_side 0   m_tip: 0   m_b: 0   m_side: 0   i_tip: 0   i_side: 0   p_side: 0thumb: 3   index: 2   middle: 3   ring: 4   pinky: 1 X: 359.18  Y: 5.00  Z: 355.23
r_side 0   m_tip: 0   m_b: 0   m_side: 0   i_tip: 0   i_side: 0   p_side: 0thumb: 3   index: 2   middle: 3   ring: 4   pinky: 1 X: 358.97  Y: 7.56  Z: 352.98
r_side 0   m_tip: 0   m_b: 0   m_side: 0   i_tip: 0   i_side: 0   p_side: 0thumb: 3   index: 2   middle: 3   ring: 4   pinky: 1 X: 358.83  Y: 10.18  Z: 350.74
r_side 0   m_tip: 0   m_b: 0   m_side: 0   i_tip: 0   i_side: 0   p_side: 0thumb: 2   index: 2   middle: 3   ring: 4   pinky: 2 X: 358.56  Y: 13.07  Z: 348.42
r_side 0   m_tip: 0   m_b: 0   m_side: 0   i_tip: 0   i_side: 0   p_side: 0thumb: 3   index: 2   middle: 3   ring: 4   pinky: 30 X: 352.32  Y: 20.54  Z: 350.22
r_side 0   m_tip: 0   m_b: 0   m_side: 0   i_tip: 0   i_side: 0   p_side: 0thumb: 2   index: 2   middle: 3   ring: 4   pinky: 1 X: 343.67  Y: 27.38  Z: 342.10
r_side 0   m_tip: 0   m_b: 0   m_side: 0   i_tip: 0   i_side: 0   p_side: 0thumb: 2   index: 2   middle: 3   ring: 4   pinky: 2 X: 330.84  Y: 42.53  Z: 328.12
r_side 0   m_tip: 0   m_b: 0   m_side: 0   i_tip: 0   i_side: 0   p_side: 0thumb: 3   index: 9   middle: 13   ring: 14   pinky: 12 X: 315.91  Y: 48.39  Z: 314.56
r_side 0   m_tip: 0   m_b: 0   m_side: 0   i_tip: 0   i_side: 0   p_side: 0thumb: 5   index: 15   middle: 16   ring: 18   pinky: 16 X: 303.17  Y: 49.68  Z: 306.05
r_side 0   m_tip: 0   m_b: 0   m_side: 0   i_tip: 0   i_side: 0   p_side: 0thumb: 11   index: 17   middle: 17   ring: 19   pinky: 17 X: 292.96  Y: 51.49  Z: 298.77
r_side 0   m_tip: 0   m_b: 0   m_side: 0   i_tip: 0   i_side: 0   p_side: 0thumb: 13   index: 18   middle: 17   ring: 19   pinky: 17 X: 293.01  Y: 50.91  Z: 297.82
r_side 0   m_tip: 0   m_b: 0   m_side: 0   i_tip: 0   i_side: 0   p_side: 0thumb: 12   index: 17   middle: 17   ring: 18   pinky: 17 X: 291.33  Y: 50.85  Z: 295.22
r_side 0   m_tip: 0   m_b: 0   m_side: 0   i_tip: 0   i_side: 0   p_side: 0thumb: 12   index: 17   middle: 16   ring: 18   pinky: 17 X: 289.18  Y: 50.65  Z: 292.66
r_side 0   m_tip: 0   m_b: 0   m_side: 0   i_tip: 0   i_side: 0   p_side: 0thumb: 12   index: 17   middle: 16   ring: 18   pinky: 17 X: 287.58  Y: 50.29  Z: 290.20
r_side 0   m_tip: 0   m_b: 0   m_side: 0   i_tip: 0   i_side: 0   p_side: 0thumb: 12   index: 17   middle: 16   ring: 18   pinky: 16 X: 286.65  Y: 49.71  Z: 288.62
r_side 0   m_tip: 0   m_b: 0   m_side: 0   i_tip: 0   i_side: 0   p_side: 0thumb: 11   index: 17   middle: 16   ring: 18   pinky: 16 X: 286.51  Y: 49.20  Z: 287.54
r_side 0   m_tip: 0   m_b: 0   m_side: 0   i_tip: 0   i_side: 0   p_side: 0thumb: 12   index: 17   middle: 16   ring: 18   pinky: 16 X: 285.56  Y: 48.61  Z: 285.73
r_side 0   m_tip: 0   m_b: 0   m_side: 0   i_tip: 0   i_side: 0   p_side: 0thumb: 12   index: 17   middle: 16   ring: 18   pinky: 16 X: 285.09  Y: 48.30  Z: 284.78
r_side 0   m_tip: 0   m_b: 0   m_side: 0   i_tip: 0   i_side: 0   p_side: 0thumb: 12   index: 17   middle: 16   ring: 17   pinky: 16 X: 284.06  Y: 48.01  Z: 283.43
r_side 0   m_tip: 0   m_b: 0   m_side: 0   i_tip: 0   i_side: 0   p_side: 0thumb: 11   index: 17   middle: 16   ring: 17   pinky: 16 X: 283.54  Y: 47.54  Z: 282.71
r_side 0   m_tip: 0   m_b: 0   m_side: 0   i_tip: 0   i_side: 0   p_side: 0thumb: 11   index: 17   middle: 16   ring: 17   pinky: 16 X: 283.20  Y: 47.24  Z: 282.21
r_side 0   m_tip: 0   m_b: 0   m_side: 0   i_tip: 0   i_side: 0   p_side: 0thumb: 11   index: 16   middle: 16   ring: 17   pinky: 16 X: 282.27  Y: 46.47  Z: 281.18
r_side 0   m_tip: 0   m_b: 0   m_side: 0   i_tip: 0   i_side: 0   p_side: 0thumb: 11   index: 16   middle: 15   ring: 17   pinky: 16 X: 281.68  Y: 45.96  Z: 280.48
r_side 0   m_tip: 0   m_b: 0   m_side: 0   i_tip: 0   i_side: 0   p_side: 0thumb: 11   index: 16   middle: 15   ring: 17   pinky: 16 X: 281.56  Y: 45.44  Z: 279.60
r_side 0   m_tip: 0   m_b: 0   m_side: 0   i_tip: 0   i_side: 0   p_side: 0thumb: 11   index: 16   middle: 15   ring: 17   pinky: 16 X: 281.69  Y: 44.97  Z: 279.34
r_side 0   m_tip: 0   m_b: 0   m_side: 0   i_tip: 0   i_side: 0   p_side: 0thumb: 11   index: 17   middle: 15   ring: 15   pinky: 15 X: 281.35  Y: 44.27  Z: 279.10
r_side 0   m_tip: 0   m_b: 0   m_side: 0   i_tip: 0   i_side: 0   p_side: 0thumb: 11   index: 16   middle: 15   ring: 17   pinky: 16 X: 281.23  Y: 43.65  Z: 279.15
r_side 0   m_tip: 0   m_b: 0   m_side: 0   i_tip: 0   i_side: 0   p_side: 0thumb: 12   index: 17   middle: 15   ring: 17   pinky: 16 X: 281.06  Y: 43.05  Z: 279.06
r_side 0   m_tip: 0   m_b: 0   m_side: 0   i_tip: 0   i_side: 0   p_side: 0thumb: 12   index: 17   middle: 15   ring: 16   pinky: 16 X: 280.98  Y: 42.46  Z: 279.03
r_side 0   m_tip: 0   m_b: 0   m_side: 0   i_tip: 0   i_side: 0   p_side: 0thumb: 11   index: 16   middle: 15   ring: 17   pinky: 15 X: 281.32  Y: 41.68  Z: 279.41
r_side 0   m_tip: 0   m_b: 0   m_side: 0   i_tip: 0   i_side: 0   p_side: 0thumb: 11   index: 16   middle: 15   ring: 17   pinky: 15 X: 281.10  Y: 41.13  Z: 279.37
r_side 0   m_tip: 0   m_b: 0   m_side: 0   i_tip: 0   i_side: 0   p_side: 0thumb: 11   index: 16   middle: 15   ring: 17   pinky: 15 X: 281.91  Y: 40.32  Z: 279.77
r_side 0   m_tip: 0   m_b: 0   m_side: 0   i_tip: 0   i_side: 0   p_side: 0thumb: 11   index: 16   middle: 15   ring: 17   pinky: 15 X: 282.14  Y: 39.68  Z: 280.23
r_side 0   m_tip: 0   m_b: 0   m_side: 0   i_tip: 0   i_side: 0   p_side: 0thumb: 11   index: 16   middle: 15   ring: 17   pinky: 15 X: 281.96  Y: 39.09  Z: 280.38
r_side 0   m_tip: 0   m_b: 0   m_side: 0   i_tip: 0   i_side: 0   p_side: 0thumb: 11   index: 16   middle: 15   ring: 16   pinky: 15 X: 281.51  Y: 38.69  Z: 279.83
r_side 0   m_tip: 0   m_b: 0   m_side: 0   i_tip: 0   i_side: 0   p_side: 0thumb: 11   index: 16   middle: 15   ring: 16   pinky: 15 X: 281.26  Y: 38.25  Z: 279.48
r_side 0   m_tip: 0   m_b: 0   m_side: 0   i_tip: 0   i_side: 0   p_side: 0thumb: 11   index: 16   middle: 15   ring: 16   pinky: 15 X: 281.24  Y: 37.72  Z: 279.25
r_side 0   m_tip: 0   m_b: 0   m_side: 0   i_tip: 0   i_side: 0   p_side: 0thumb: 11   index: 16   middle: 15   ring: 16   pinky: 15 X: 281.66  Y: 37.06  Z: 279.49
r_side 0   m_tip: 0   m_b: 0   m_side: 0   i_tip: 0   i_side: 0   p_side: 0thumb: 11   index: 16   middle: 15   ring: 17   pinky: 15 X: 281.34  Y: 36.66  Z: 279.45
r_side 0   m_tip: 0   m_b: 0   m_side: 0   i_tip: 0   i_side: 0   p_side: 0thumb: 12   index: 16   middle: 15   ring: 16   pinky: 15 X: 281.30  Y: 36.05  Z: 279.16
r_side 0   m_tip: 0   m_b: 0   m_side: 0   i_tip: 0   i_side: 0   p_side: 0thumb: 11   index: 16   middle: 15   ring: 16   pinky: 15 X: 280.98  Y: 35.40  Z: 279.43
