juanmrq95/ee149_104/ASLsensing/longFlex/save_sensordata/Test 2 Juan/testJuanLetterB.txt

6r_side 0   m_tip: 0   m_b: 0   m_side: 0   i_tip: 0   i_side: 0   p_side: 0thumb: 2   index: -22   middle: 4   ring: 4   pinky: 2 X: 1.16  Y: 358.94  Z: 1.56
r_side 0   m_tip: 0   m_b: 0   m_side: 0   i_tip: 0   i_side: 0   p_side: 0thumb: 3   index: -22   middle: 4   ring: 4   pinky: 2 X: 1.03  Y: 1.33  Z: 359.00
r_side 0   m_tip: 0   m_b: 0   m_side: 0   i_tip: 0   i_side: 0   p_side: 0thumb: 3   index: -22   middle: 4   ring: 4   pinky: 2 X: 0.99  Y: 3.25  Z: 356.44
r_side 0   m_tip: 0   m_b: 0   m_side: 0   i_tip: 0   i_side: 0   p_side: 0thumb: 2   index: -22   middle: 4   ring: 4   pinky: 2 X: 0.91  Y: 5.04  Z: 353.91
r_side 0   m_tip: 0   m_b: 0   m_side: 0   i_tip: 0   i_side: 0   p_side: 0thumb: 2   index: -22   middle: 4   ring: 4   pinky: 2 X: 0.74  Y: 6.73  Z: 351.55
r_side 0   m_tip: 0   m_b: 0   m_side: 0   i_tip: 0   i_side: 0   p_side: 0thumb: 2   index: -22   middle: 4   ring: 4   pinky: 2 X: 0.38  Y: 8.59  Z: 349.65
r_side 0   m_tip: 0   m_b: 0   m_side: 0   i_tip: 0   i_side: 0   p_side: 0thumb: 3   index: -22   middle: 4   ring: 4   pinky: 2 X: 351.51  Y: 22.02  Z: 349.09
r_side 0   m_tip: 0   m_b: 0   m_side: 0   i_tip: 0   i_side: 0   p_side: 0thumb: 5   index: 3   middle: 4   ring: 4   pinky: 2 X: 344.52  Y: 31.59  Z: 351.23
r_side 0   m_tip: 0   m_b: 0   m_side: 0   i_tip: 0   i_side: 0   p_side: 0thumb: 17   index: 4   middle: 4   ring: 4   pinky: 2 X: 332.84  Y: 44.58  Z: 344.22
r_side 0   m_tip: 0   m_b: 0   m_side: 0   i_tip: 0   i_side: 0   p_side: 0thumb: 21   index: 3   middle: 4   ring: 4   pinky: 2 X: 311.62  Y: 56.56  Z: 324.88
r_side 0   m_tip: 0   m_b: 0   m_side: 0   i_tip: 0   i_side: 0   p_side: 0thumb: 23   index: 3   middle: 3   ring: 4   pinky: 2 X: 304.42  Y: 62.11  Z: 317.43
r_side 0   m_tip: 0   m_b: 0   m_side: 0   i_tip: 0   i_side: 0   p_side: 0thumb: 22   index: 3   middle: 3   ring: 3   pinky: 1 X: 302.42  Y: 63.57  Z: 314.64
r_side 0   m_tip: 0   m_b: 0   m_side: 0   i_tip: 0   i_side: 0   p_side: 0thumb: 22   index: 3   middle: 3   ring: 3   pinky: 2 X: 300.44  Y: 64.44  Z: 311.28
r_side 0   m_tip: 0   m_b: 0   m_side: 0   i_tip: 0   i_side: 0   p_side: 0thumb: 21   index: 3   middle: 3   ring: 3   pinky: 2 X: 299.21  Y: 63.97  Z: 308.45
r_side 0   m_tip: 0   m_b: 0   m_side: 0   i_tip: 0   i_side: 0   p_side: 0thumb: 21   index: 3   middle: 3   ring: 3   pinky: 1 X: 302.28  Y: 63.48  Z: 310.49
r_side 0   m_tip: 0   m_b: 0   m_side: 0   i_tip: 0   i_side: 0   p_side: 0thumb: 21   index: 3   middle: 3   ring: 3   pinky: 1 X: 301.13  Y: 63.62  Z: 308.45
r_side 0   m_tip: 0   m_b: 0   m_side: 0   i_tip: 0   i_side: 0   p_side: 0thumb: 21   index: 3   middle: 3   ring: 3   pinky: 1 X: 300.89  Y: 63.31  Z: 307.32
r_side 0   m_tip: 0   m_b: 0   m_side: 0   i_tip: 0   i_side: 0   p_side: 0thumb: 20   index: 3   middle: 3   ring: 4   pinky: 1 X: 300.02  Y: 62.98  Z: 305.55
r_side 0   m_tip: 0   m_b: 0   m_side: 0   i_tip: 0   i_side: 0   p_side: 0thumb: 21   index: 3   middle: 3   ring: 3   pinky: 1 X: 298.33  Y: 62.32  Z: 302.65
r_side 0   m_tip: 0   m_b: 0   m_side: 0   i_tip: 0   i_side: 0   p_side: 0thumb: 21   index: 2   middle: 3   ring: 3   pinky: 1 X: 296.59  Y: 61.94  Z: 300.41
r_side 0   m_tip: 0   m_b: 0   m_side: 0   i_tip: 0   i_side: 0   p_side: 0thumb: 20   index: 2   middle: 3   ring: 3   pinky: 1 X: 295.48  Y: 62.14  Z: 298.70
r_side 0   m_tip: 0   m_b: 0   m_side: 0   i_tip: 0   i_side: 0   p_side: 0thumb: 20   index: 2   middle: 3   ring: 3   pinky: 1 X: 292.58  Y: 61.91  Z: 295.50
r_side 0   m_tip: 0   m_b: 0   m_side: 0   i_tip: 0   i_side: 0   p_side: 0thumb: 20   index: 2   middle: 3   ring: 3   pinky: 1 X: 291.42  Y: 61.54  Z: 293.84
r_side 0   m_tip: 0   m_b: 0   m_side: 0   i_tip: 0   i_side: 0   p_side: 0thumb: 20   index: 3   middle: 3   ring: 3   pinky: 1 X: 291.00  Y: 61.42  Z: 292.86
r_side 0   m_tip: 0   m_b: 0   m_side: 0   i_tip: 0   i_side: 0   p_side: 0thumb: 19   index: 2   middle: 3   ring: 3   pinky: 1 X: 289.65  Y: 61.25  Z: 291.06
r_side 0   m_tip: 0   m_b: 0   m_side: 0   i_tip: 0   i_side: 0   p_side: 0thumb: 19   index: 2   middle: 3   ring: 3   pinky: 1 X: 289.41  Y: 60.81  Z: 290.56
r_side 0   m_tip: 0   m_b: 0   m_side: 0   i_tip: 0   i_side: 0   p_side: 0thumb: 19   index: 2   middle: 3   ring: 3   pinky: 1 X: 286.28  Y: 58.85  Z: 286.34
r_side 0   m_tip: 0   m_b: 0   m_side: 0   i_tip: 0   i_side: 0   p_side: 0thumb: 19   index: 2   middle: 3   ring: 3   pinky: 1 X: 286.48  Y: 58.26  Z: 286.45
r_side 0   m_tip: 0   m_b: 0   m_side: 0   i_tip: 0   i_side: 0   p_side: 0thumb: 19   index: 2   middle: 3   ring: 3   pinky: 1 X: 286.15  Y: 57.78  Z: 285.80
r_side 0   m_tip: 0   m_b: 0   m_side: 0   i_tip: 0   i_side: 0   p_side: 0thumb: 19   index: 2   middle: 3   ring: 3   pinky: 1 X: 286.82  Y: 57.50  Z: 286.21
r_side 0   m_tip: 0   m_b: 0   m_side: 0   i_tip: 0   i_side: 0   p_side: 0thumb: 19   index: 2   middle: 3   ring: 3   pinky: 1 X: 286.92  Y: 56.86  Z: 285.97
r_side 0   m_tip: 0   m_b: 0   m_side: 0   i_tip: 0   i_side: 0   p_side: 0thumb: 19   index: 2   middle: 3   ring: 2   pinky: 1 X: 287.03  Y: 56.40  Z: 285.92
r_side 0   m_tip: 0   m_b: 0   m_side: 0   i_tip: 0   i_side: 0   p_side: 0thumb: 19   index: 2   middle: 3   ring: 3   pinky: 1 X: 287.76  Y: 55.80  Z: 286.55
r_side 0   m_tip: 0   m_b: 0   m_side: 0   i_tip: 0   i_side: 0   p_side: 0thumb: 19   index: 2   middle: 3   ring: 3   pinky: 1 X: 288.06  Y: 55.23  Z: 286.68
r_side 0   m_tip: 0   m_b: 0   m_side: 0   i_tip: 0   i_side: 0   p_side: 0thumb: 19   index: 2   middle: 3   ring: 3   pinky: 1 X: 287.60  Y: 54.56  Z: 286.38
r_side 0   m_tip: 0   m_b: 0   m_side: 0   i_tip: 0   i_side: 0   p_side: 0thumb: 19   index: 2   middle: 3   ring: 3   pinky: 1 X: 287.68  Y: 53.97  Z: 286.37
r_side 0   m_tip: 0   m_b: 0   m_side: 0   i_tip: 0   i_side: 0   p_side: 0thumb: 18   index: 2   middle: 3   ring: 3   pinky: 1 X: 288.44  Y: 53.50  Z: 286.97
r_side 0   m_tip: 0   m_b: 0   m_side: 0   i_tip: 0   i_side: 0   p_side: 0thumb: 18   index: 2   middle: 3   ring: 3   pinky: 1 X: 288.17  Y: 53.67  Z: 287.20
r_side 0   m_tip: 0   m_b: 0   m_side: 0   i_tip: 0   i_side: 0   p_side: 0thumb: 18   index: 2   middle: 3   ring: 3   pinky: 1 X: 287.98  Y: 53.40  Z: 286.94
r_side 0   m_tip: 0   m_b: 0   m_side: 0   i_tip: 0   i_side: 0   p_side: 0thumb: 18   index: 2   middle: 3   ring: 2   pinky: 1 X: 287.28  Y: 52.70  Z: 286.11
r_side 0   m_tip: 0   m_b: 0   m_side: 0   i_tip: 0   i_side: 0   p_side: 0thumb: 18   index: 2   middle: 3   ring: 3   pinky: 1 X: 287.40  Y: 52.01  Z: 286.21
r_side 0   m_tip: 0   m_b: 0   m_side: 0   i_tip: 0   i_side: 0   p_side: 0thumb: 18   index: 2   middle: 3   ring: 3   pinky: 1 X: 287.37  Y: 51.78  Z: 286.05
r_side 0   m_tip: 0   m_b: 0   m_side: 0   i_tip: 0   i_side: 0   p_side: 0thumb: 18   index: 2   middle: 3   ring: 3   pinky: 1 X: 287.02  Y: 51.06  Z: 286.11
r_side 0   m_tip: 0   m_b: 0   m_side: 0   i_tip: 0   i_side: 0   p_side: 0thumb: 17   index: 2   middle: 3   ring: 3   pinky: 1 X: 286.60  Y: 50.87  Z: 286.21
