juanmrq95/ee149_104/ASLsensing/longFlex/save_sensordata/Test 2 Juan/testJuanLetterC.txt

òr_side 0   m_tip: 0   m_b: 0   m_side: 0   i_tip: 0   i_side: 0   p_side: 0thumb: 2   index: 3   middle: 4   ring: 4   pinky: 1 X: 359.62  Y: 359.08  Z: 358.69
r_side 0   m_tip: 0   m_b: 0   m_side: 0   i_tip: 0   i_side: 0   p_side: 0thumb: 2   index: 3   middle: 5   ring: 4   pinky: 1 X: 359.71  Y: 1.17  Z: 356.64
r_side 0   m_tip: 0   m_b: 0   m_side: 0   i_tip: 0   i_side: 0   p_side: 0thumb: 2   index: 1   middle: 4   ring: 4   pinky: 1 X: 359.57  Y: 3.08  Z: 354.72
r_side 0   m_tip: 0   m_b: 0   m_side: 0   i_tip: 0   i_side: 0   p_side: 0thumb: 2   index: 3   middle: 4   ring: 4   pinky: 1 X: 359.25  Y: 4.96  Z: 352.71
r_side 0   m_tip: 0   m_b: 0   m_side: 0   i_tip: 0   i_side: 0   p_side: 0thumb: 2   index: 3   middle: 4   ring: 4   pinky: 1 X: 358.82  Y: 6.63  Z: 352.38
r_side 0   m_tip: 0   m_b: 0   m_side: 0   i_tip: 0   i_side: 0   p_side: 0thumb: 3   index: 3   middle: 4   ring: 3   pinky: 1 X: 349.71  Y: 31.04  Z: 351.68
r_side 0   m_tip: 0   m_b: 0   m_side: 0   i_tip: 0   i_side: 0   p_side: 0thumb: 7   index: 8   middle: 11   ring: 11   pinky: 8 X: 341.45  Y: 45.37  Z: 344.85
r_side 0   m_tip: 0   m_b: 0   m_side: 0   i_tip: 0   i_side: 0   p_side: 0thumb: 14   index: 14   middle: 16   ring: 15   pinky: 14 X: 338.34  Y: 51.08  Z: 343.49
r_side 0   m_tip: 0   m_b: 0   m_side: 0   i_tip: 0   i_side: 0   p_side: 0thumb: 12   index: 15   middle: 16   ring: 15   pinky: 14 X: 335.83  Y: 53.54  Z: 341.00
r_side 0   m_tip: 0   m_b: 0   m_side: 0   i_tip: 0   i_side: 0   p_side: 0thumb: 13   index: 15   middle: 16   ring: 15   pinky: 13 X: 334.54  Y: 54.03  Z: 338.85
r_side 0   m_tip: 0   m_b: 0   m_side: 0   i_tip: 0   i_side: 0   p_side: 0thumb: 16   index: 15   middle: 16   ring: 15   pinky: 13 X: 333.13  Y: 54.66  Z: 335.93
r_side 0   m_tip: 0   m_b: 0   m_side: 0   i_tip: 0   i_side: 0   p_side: 0thumb: 16   index: 15   middle: 16   ring: 15   pinky: 13 X: 332.18  Y: 55.26  Z: 333.43
r_side 0   m_tip: 0   m_b: 0   m_side: 0   i_tip: 0   i_side: 0   p_side: 0thumb: 16   index: 15   middle: 16   ring: 15   pinky: 13 X: 331.06  Y: 55.77  Z: 331.29
r_side 0   m_tip: 0   m_b: 0   m_side: 0   i_tip: 0   i_side: 0   p_side: 0thumb: 15   index: 15   middle: 15   ring: 15   pinky: 13 X: 329.35  Y: 56.57  Z: 328.54
r_side 0   m_tip: 0   m_b: 0   m_side: 0   i_tip: 0   i_side: 0   p_side: 0thumb: 15   index: 15   middle: 15   ring: 14   pinky: 13 X: 327.75  Y: 57.25  Z: 326.27
r_side 0   m_tip: 0   m_b: 0   m_side: 0   i_tip: 0   i_side: 0   p_side: 0thumb: 16   index: 15   middle: 15   ring: 14   pinky: 13 X: 327.25  Y: 57.35  Z: 324.93
r_side 0   m_tip: 0   m_b: 0   m_side: 0   i_tip: 0   i_side: 0   p_side: 0thumb: 15   index: 15   middle: 15   ring: 14   pinky: 13 X: 326.23  Y: 57.71  Z: 323.00
r_side 0   m_tip: 0   m_b: 0   m_side: 0   i_tip: 0   i_side: 0   p_side: 0thumb: 15   index: 15   middle: 15   ring: 14   pinky: 13 X: 324.43  Y: 57.72  Z: 320.24
r_side 0   m_tip: 0   m_b: 0   m_side: 0   i_tip: 0   i_side: 0   p_side: 0thumb: 14   index: 14   middle: 15   ring: 14   pinky: 12 X: 322.73  Y: 57.82  Z: 317.67
r_side 0   m_tip: 0   m_b: 0   m_side: 0   i_tip: 0   i_side: 0   p_side: 0thumb: 15   index: 15   middle: 15   ring: 14   pinky: 13 X: 322.57  Y: 57.27  Z: 316.42
r_side 0   m_tip: 0   m_b: 0   m_side: 0   i_tip: 0   i_side: 0   p_side: 0thumb: 15   index: 15   middle: 15   ring: 14   pinky: 12 X: 321.58  Y: 56.90  Z: 314.21
r_side 0   m_tip: 0   m_b: 0   m_side: 0   i_tip: 0   i_side: 0   p_side: 0thumb: 15   index: 15   middle: 15   ring: 14   pinky: 12 X: 322.06  Y: 55.61  Z: 313.56
r_side 0   m_tip: 0   m_b: 0   m_side: 0   i_tip: 0   i_side: 0   p_side: 0thumb: 15   index: 14   middle: 15   ring: 14   pinky: 12 X: 320.91  Y: 55.91  Z: 312.03
r_side 0   m_tip: 0   m_b: 0   m_side: 0   i_tip: 0   i_side: 0   p_side: 0thumb: 15   index: 15   middle: 15   ring: 14   pinky: 12 X: 320.66  Y: 55.28  Z: 311.23
r_side 0   m_tip: 0   m_b: 0   m_side: 0   i_tip: 0   i_side: 0   p_side: 0thumb: 15   index: 15   middle: 15   ring: 14   pinky: 12 X: 319.76  Y: 55.38  Z: 310.30
r_side 0   m_tip: 0   m_b: 0   m_side: 0   i_tip: 0   i_side: 0   p_side: 0thumb: 15   index: 14   middle: 15   ring: 14   pinky: 12 X: 320.54  Y: 54.87  Z: 310.89
r_side 0   m_tip: 0   m_b: 0   m_side: 0   i_tip: 0   i_side: 0   p_side: 0thumb: 15   index: 14   middle: 15   ring: 14   pinky: 12 X: 320.23  Y: 54.52  Z: 310.75
r_side 0   m_tip: 0   m_b: 0   m_side: 0   i_tip: 0   i_side: 0   p_side: 0thumb: 15   index: 14   middle: 15   ring: 14   pinky: 12 X: 319.69  Y: 54.36  Z: 310.15
r_side 0   m_tip: 0   m_b: 0   m_side: 0   i_tip: 0   i_side: 0   p_side: 0thumb: 16   index: 14   middle: 15   ring: 14   pinky: 12 X: 318.99  Y: 54.53  Z: 309.57
r_side 0   m_tip: 0   m_b: 0   m_side: 0   i_tip: 0   i_side: 0   p_side: 0thumb: 16   index: 14   middle: 15   ring: 14   pinky: 12 X: 318.82  Y: 54.09  Z: 309.51
r_side 0   m_tip: 0   m_b: 0   m_side: 0   i_tip: 0   i_side: 0   p_side: 0thumb: 16   index: 14   middle: 15   ring: 14   pinky: 12 X: 317.69  Y: 54.22  Z: 308.63
r_side 0   m_tip: 0   m_b: 0   m_side: 0   i_tip: 0   i_side: 0   p_side: 0thumb: 15   index: 14   middle: 15   ring: 14   pinky: 12 X: 318.52  Y: 54.18  Z: 309.07
r_side 0   m_tip: 0   m_b: 0   m_side: 0   i_tip: 0   i_side: 0   p_side: 0thumb: 15   index: 15   middle: 15   ring: 14   pinky: 12 X: 316.99  Y: 54.32  Z: 307.69
r_side 0   m_tip: 0   m_b: 0   m_side: 0   i_tip: 0   i_side: 0   p_side: 0thumb: 15   index: 15   middle: 15   ring: 13   pinky: 12 X: 317.22  Y: 53.81  Z: 307.81
r_side 0   m_tip: 0   m_b: 0   m_side: 0   i_tip: 0   i_side: 0   p_side: 0thumb: 15   index: 14   middle: 14   ring: 13   pinky: 12 X: 316.60  Y: 53.50  Z: 307.14
r_side 0   m_tip: 0   m_b: 0   m_side: 0   i_tip: 0   i_side: 0   p_side: 0thumb: 15   index: 14   middle: 14   ring: 13   pinky: 12 X: 316.16  Y: 53.40  Z: 306.62
r_side 0   m_tip: 0   m_b: 0   m_side: 0   i_tip: 0   i_side: 0   p_side: 0thumb: 15   index: 14   middle: 15   ring: 13   pinky: 12 X: 316.94  Y: 52.99  Z: 307.14
r_side 0   m_tip: 0   m_b: 0   m_side: 0   i_tip: 0   i_side: 0   p_side: 0thumb: 15   index: 14   middle: 15   ring: 13   pinky: 11 X: 316.14  Y: 52.84  Z: 306.51
r_side 0   m_tip: 0   m_b: 0   m_side: 0   i_tip: 0   i_side: 0   p_side: 0thumb: 15   index: 14   middle: 15   ring: 13   pinky: 12 X: 317.20  Y: 52.44  Z: 307.39
r_side 0   m_tip: 0   m_b: 0   m_side: 0   i_tip: 0   i_side: 0   p_side: 0thumb: 15   index: 15   middle: 14   ring: 13   pinky: 12 X: 316.19  Y: 52.09  Z: 306.47
r_side 0   m_tip: 0   m_b: 0   m_side: 0   i_tip: 0   i_side: 0   p_side: 0thumb: 15   index: 14   middle: 15   ring: 14   pinky: 12 X: 318.99  Y: 51.31  Z: 308.75
r_side 0   m_tip: 0   m_b: 0   m_side: 0   i_tip: 0   i_side: 0   p_side: 0thumb: 15   index: 14   middle: 15   ring: 13   pinky: 12 X: 317.49  Y: 51.54  Z: 308.08
r_side 0   m_tip: 0   m_b: 0   m_side: 0   i_tip: 0   i_side: 0   p_side: 0thumb: 15   index: 14   middle: 14   ring: 13   pinky: 11 X: 319.14  Y: 50.34  Z: 309.20
