juanmrq95/ee149_104/ASLsensing/longFlex/save_sensordata/Test 2 Juan/testJuanLetterD.txt

 r_side 0   m_tip: 0   m_b: 0   m_side: 0   i_tip: 0   i_side: 0   p_side: 0thumb: 3   index: 2   middle: 4   ring: 3   pinky: 1 X: 359.87  Y: 359.87  Z: 0.00
r_side 0   m_tip: 0   m_b: 0   m_side: 0   i_tip: 0   i_side: 0   p_side: 0thumb: 2   index: 2   middle: 4   ring: 4   pinky: 1 X: 359.81  Y: 0.52  Z: 357.35
r_side 0   m_tip: 0   m_b: 0   m_side: 0   i_tip: 0   i_side: 0   p_side: 0thumb: 2   index: 2   middle: 4   ring: 3   pinky: 1 X: 359.78  Y: 1.42  Z: 354.88
r_side 0   m_tip: 0   m_b: 0   m_side: 0   i_tip: 0   i_side: 0   p_side: 0thumb: 2   index: 2   middle: 4   ring: 3   pinky: 1 X: 359.68  Y: 1.82  Z: 352.42
r_side 0   m_tip: 0   m_b: 0   m_side: 0   i_tip: 0   i_side: 0   p_side: 0thumb: 2   index: 3   middle: 4   ring: 3   pinky: 1 X: 359.58  Y: 2.59  Z: 350.26
r_side 0   m_tip: 0   m_b: 0   m_side: 0   i_tip: 0   i_side: 0   p_side: 0thumb: 2   index: 2   middle: 4   ring: 3   pinky: 1 X: 359.34  Y: 3.00  Z: 347.80
r_side 0   m_tip: 0   m_b: 0   m_side: 0   i_tip: 0   i_side: 0   p_side: 0thumb: 2   index: 2   middle: 4   ring: 3   pinky: 1 X: 345.61  Y: 17.32  Z: 329.00
r_side 0   m_tip: 0   m_b: 0   m_side: 0   i_tip: 0   i_side: 0   p_side: 0thumb: 3   index: 9   middle: 4   ring: 4   pinky: 2 X: 321.22  Y: 40.84  Z: 313.58
r_side 0   m_tip: 0   m_b: 0   m_side: 0   i_tip: 0   i_side: 0   p_side: 0thumb: 3   index: 10   middle: 12   ring: 15   pinky: 17 X: 305.58  Y: 47.69  Z: 299.52
r_side 0   m_tip: 1   m_b: 0   m_side: 0   i_tip: 0   i_side: 0   p_side: 0thumb: 4   index: 13   middle: 15   ring: 15   pinky: 15 X: 291.06  Y: 47.93  Z: 286.35
r_side 0   m_tip: 1   m_b: 0   m_side: 0   i_tip: 0   i_side: 0   p_side: 0thumb: 6   index: 5   middle: 15   ring: 15   pinky: 14 X: 289.07  Y: 47.76  Z: 286.43
r_side 0   m_tip: 1   m_b: 0   m_side: 0   i_tip: 0   i_side: 0   p_side: 0thumb: 7   index: 3   middle: 14   ring: 14   pinky: 13 X: 290.04  Y: 47.53  Z: 287.82
r_side 0   m_tip: 1   m_b: 0   m_side: 0   i_tip: 0   i_side: 0   p_side: 0thumb: 7   index: 3   middle: 13   ring: 14   pinky: 12 X: 290.05  Y: 47.08  Z: 288.30
r_side 0   m_tip: 1   m_b: 0   m_side: 0   i_tip: 0   i_side: 0   p_side: 0thumb: 7   index: 3   middle: 13   ring: 13   pinky: 11 X: 290.75  Y: 46.33  Z: 288.17
r_side 0   m_tip: 1   m_b: 0   m_side: 0   i_tip: 0   i_side: 0   p_side: 0thumb: 7   index: 3   middle: 13   ring: 13   pinky: 11 X: 290.43  Y: 45.34  Z: 287.04
r_side 0   m_tip: 1   m_b: 0   m_side: 0   i_tip: 0   i_side: 0   p_side: 0thumb: 7   index: 3   middle: 13   ring: 13   pinky: 11 X: 291.50  Y: 44.65  Z: 287.66
r_side 0   m_tip: 1   m_b: 0   m_side: 0   i_tip: 0   i_side: 0   p_side: 0thumb: 7   index: 2   middle: 13   ring: 13   pinky: 11 X: 292.69  Y: 43.98  Z: 288.61
r_side 0   m_tip: 1   m_b: 0   m_side: 0   i_tip: 0   i_side: 0   p_side: 0thumb: 7   index: 2   middle: 13   ring: 13   pinky: 11 X: 293.58  Y: 43.39  Z: 289.64
r_side 0   m_tip: 1   m_b: 0   m_side: 0   i_tip: 0   i_side: 0   p_side: 0thumb: 7   index: 2   middle: 13   ring: 13   pinky: 11 X: 293.72  Y: 42.55  Z: 289.69
r_side 0   m_tip: 1   m_b: 0   m_side: 0   i_tip: 0   i_side: 0   p_side: 0thumb: 7   index: 1   middle: 13   ring: 13   pinky: 11 X: 294.37  Y: 42.04  Z: 290.19
r_side 0   m_tip: 1   m_b: 0   m_side: 0   i_tip: 0   i_side: 0   p_side: 0thumb: 7   index: 2   middle: 13   ring: 12   pinky: 11 X: 294.89  Y: 41.37  Z: 290.69
r_side 0   m_tip: 1   m_b: 0   m_side: 0   i_tip: 0   i_side: 0   p_side: 0thumb: 7   index: 2   middle: 13   ring: 13   pinky: 11 X: 295.41  Y: 40.84  Z: 291.18
r_side 0   m_tip: 1   m_b: 0   m_side: 0   i_tip: 0   i_side: 0   p_side: 0thumb: 7   index: 2   middle: 13   ring: 13   pinky: 11 X: 295.79  Y: 40.38  Z: 291.31
r_side 0   m_tip: 1   m_b: 0   m_side: 0   i_tip: 0   i_side: 0   p_side: 0thumb: 7   index: 2   middle: 13   ring: 13   pinky: 11 X: 296.18  Y: 39.70  Z: 291.64
r_side 0   m_tip: 1   m_b: 0   m_side: 0   i_tip: 0   i_side: 0   p_side: 0thumb: 7   index: 2   middle: 13   ring: 13   pinky: 11 X: 296.94  Y: 38.91  Z: 292.34
r_side 0   m_tip: 1   m_b: 0   m_side: 0   i_tip: 0   i_side: 0   p_side: 0thumb: 7   index: 2   middle: 12   ring: 12   pinky: 11 X: 297.50  Y: 38.29  Z: 292.91
r_side 0   m_tip: 1   m_b: 0   m_side: 0   i_tip: 0   i_side: 0   p_side: 0thumb: 7   index: 2   middle: 12   ring: 12   pinky: 11 X: 298.12  Y: 37.57  Z: 293.70
r_side 0   m_tip: 1   m_b: 0   m_side: 0   i_tip: 0   i_side: 0   p_side: 0thumb: 7   index: 2   middle: 13   ring: 13   pinky: 11 X: 298.00  Y: 37.12  Z: 293.92
r_side 0   m_tip: 1   m_b: 0   m_side: 0   i_tip: 0   i_side: 0   p_side: 0thumb: 7   index: 2   middle: 13   ring: 12   pinky: 10 X: 297.96  Y: 36.63  Z: 294.09
r_side 0   m_tip: 1   m_b: 0   m_side: 0   i_tip: 0   i_side: 0   p_side: 0thumb: 7   index: 2   middle: 12   ring: 12   pinky: 10 X: 298.18  Y: 35.99  Z: 294.40
r_side 0   m_tip: 1   m_b: 0   m_side: 0   i_tip: 0   i_side: 0   p_side: 0thumb: 7   index: 2   middle: 12   ring: 12   pinky: 10 X: 298.45  Y: 35.35  Z: 294.92
r_side 0   m_tip: 1   m_b: 0   m_side: 0   i_tip: 0   i_side: 0   p_side: 0thumb: 7   index: 2   middle: 12   ring: 12   pinky: 10 X: 298.40  Y: 34.78  Z: 295.05
r_side 0   m_tip: 1   m_b: 0   m_side: 0   i_tip: 0   i_side: 0   p_side: 0thumb: 7   index: 2   middle: 12   ring: 12   pinky: 11 X: 298.46  Y: 34.17  Z: 295.21
r_side 0   m_tip: 1   m_b: 0   m_side: 0   i_tip: 0   i_side: 0   p_side: 0thumb: 7   index: 2   middle: 12   ring: 12   pinky: 11 X: 298.44  Y: 33.70  Z: 295.31
r_side 0   m_tip: 1   m_b: 0   m_side: 0   i_tip: 0   i_side: 0   p_side: 0thumb: 7   index: 2   middle: 12   ring: 12   pinky: 10 X: 298.70  Y: 33.05  Z: 295.35
r_side 0   m_tip: 1   m_b: 0   m_side: 0   i_tip: 0   i_side: 0   p_side: 0thumb: 7   index: 2   middle: 12   ring: 12   pinky: 10 X: 298.35  Y: 32.53  Z: 295.32
r_side 0   m_tip: 1   m_b: 0   m_side: 0   i_tip: 0   i_side: 0   p_side: 0thumb: 7   index: 2   middle: 12   ring: 12   pinky: 10 X: 298.33  Y: 31.97  Z: 295.39
r_side 0   m_tip: 1   m_b: 0   m_side: 0   i_tip: 0   i_side: 0   p_side: 0thumb: 7   index: 2   middle: 12   ring: 12   pinky: 10 X: 298.30  Y: 31.63  Z: 295.46
r_side 0   m_tip: 1   m_b: 0   m_side: 0   i_tip: 0   i_side: 0   p_side: 0thumb: 7   index: 2   middle: 12   ring: 12   pinky: 10 X: 298.20  Y: 31.17  Z: 295.65
r_side 0   m_tip: 1   m_b: 0   m_side: 0   i_tip: 0   i_side: 0   p_side: 0thumb: 8   index: 2   middle: 12   ring: 12   pinky: 10 X: 297.58  Y: 30.59  Z: 295.36
r_side 0   m_tip: 1   m_b: 0   m_side: 0   i_tip: 0   i_side: 0   p_side: 0thumb: 8   index: 2   middle: 12   ring: 12   pinky: 10 X: 297.33  Y: 30.04  Z: 295.21
r_side 0   m_tip: 1   m_b: 0   m_side: 0   i_tip: 0   i_side: 0   p_side: 0thumb: 8   index: 2   middle: 12   ring: 12   pinky: 10 X: 297.02  Y: 29.45  Z: 295.09
r_side 0   m_tip: 1   m_b: 0   m_side: 0   i_tip: 0   i_side: 0   p_side: 0thumb: 8   index: 1   middle: 12   ring: 12   pinky: 10 X: 296.60  Y: 29.08  Z: 294.91
r_side 0   m_tip: 1   m_b: 0   m_side: 0   i_tip: 0   i_side: 0   p_side: 0thumb: 8   index: 2   middle: 12   ring: 12   pinky: 10 X: 296.50  Y: 28.54  Z: 294.90
r_side 0   m_tip: 1   m_b: 0   m_side: 0   i_tip: 0   i_side: 0   p_side: 0thumb: 8   index: 1   middle: 12   ring: 12   pinky: 10 X: 296.09  Y: 28.02  Z: 294.81
r_side 0   m_tip: 1   m_b: 0   m_side: 0   i_tip: 0   i_side: 0   p_side: 0thumb: 6   index: 1   middle: 12   ring: 12   pinky: 10 X: 295.89  Y: 27.44  Z: 294.26
r_side 0   m_tip: 1   m_b: 0   m_side: 0   i_tip: 0   i_side: 0   p_side: 0thumb: 8   index: 2   middle: 12   ring: 12   pinky: 10 X: 295.23  Y: 26.83  Z: 293.50
