juanmrq95/ee149_104/ASLsensing/longFlex/save_sensordata/Test 2 Juan/testJuanLetterE.txt

2r_side 0   m_tip: 0   m_b: 0   m_side: 0   i_tip: 0   i_side: 0   p_side: 0thumb: 5   index: 1   middle: 4   ring: 4   pinky: 2 X: 0.24  Y: 358.44  Z: 1.70
r_side 0   m_tip: 0   m_b: 0   m_side: 0   i_tip: 0   i_side: 0   p_side: 0thumb: 4   index: 2   middle: 4   ring: 4   pinky: 2 X: 0.29  Y: 359.94  Z: 358.63
r_side 0   m_tip: 0   m_b: 0   m_side: 0   i_tip: 0   i_side: 0   p_side: 0thumb: 5   index: 2   middle: 4   ring: 4   pinky: 2 X: 0.16  Y: 1.25  Z: 355.84
r_side 0   m_tip: 0   m_b: 0   m_side: 0   i_tip: 0   i_side: 0   p_side: 0thumb: 4   index: 2   middle: 4   ring: 4   pinky: 2 X: 360.00  Y: 2.56  Z: 353.20
r_side 0   m_tip: 0   m_b: 0   m_side: 0   i_tip: 0   i_side: 0   p_side: 0thumb: 3   index: 2   middle: 4   ring: 4   pinky: 2 X: 359.79  Y: 3.75  Z: 350.60
r_side 0   m_tip: 0   m_b: 0   m_side: 0   i_tip: 0   i_side: 0   p_side: 0thumb: 5   index: 2   middle: 4   ring: 4   pinky: 2 X: 358.34  Y: 7.12  Z: 346.61
r_side 0   m_tip: 0   m_b: 0   m_side: 0   i_tip: 0   i_side: 0   p_side: 0thumb: 18   index: 8   middle: 10   ring: 10   pinky: 5 X: 352.55  Y: 24.54  Z: 347.94
r_side 0   m_tip: 0   m_b: 0   m_side: 0   i_tip: 0   i_side: 0   p_side: 0thumb: 24   index: 16   middle: 16   ring: 16   pinky: 12 X: 341.01  Y: 41.79  Z: 343.90
r_side 0   m_tip: 0   m_b: 0   m_side: 0   i_tip: 0   i_side: 0   p_side: 0thumb: 25   index: 17   middle: 17   ring: 17   pinky: 14 X: 331.26  Y: 49.09  Z: 336.50
r_side 0   m_tip: 0   m_b: 0   m_side: 0   i_tip: 0   i_side: 0   p_side: 0thumb: 25   index: 19   middle: 19   ring: 19   pinky: 17 X: 326.67  Y: 53.45  Z: 331.44
r_side 0   m_tip: 0   m_b: 0   m_side: 0   i_tip: 0   i_side: 0   p_side: 0thumb: 24   index: 19   middle: 19   ring: 19   pinky: 17 X: 326.00  Y: 54.00  Z: 329.85
r_side 0   m_tip: 0   m_b: 0   m_side: 0   i_tip: 0   i_side: 0   p_side: 0thumb: 24   index: 20   middle: 19   ring: 19   pinky: 17 X: 323.99  Y: 54.22  Z: 327.03
r_side 0   m_tip: 0   m_b: 0   m_side: 0   i_tip: 0   i_side: 0   p_side: 0thumb: 24   index: 19   middle: 19   ring: 19   pinky: 17 X: 323.08  Y: 54.05  Z: 325.15
r_side 0   m_tip: 0   m_b: 0   m_side: 0   i_tip: 0   i_side: 0   p_side: 0thumb: 24   index: 19   middle: 19   ring: 19   pinky: 17 X: 321.30  Y: 54.32  Z: 322.51
r_side 0   m_tip: 0   m_b: 0   m_side: 0   i_tip: 0   i_side: 0   p_side: 0thumb: 24   index: 19   middle: 18   ring: 19   pinky: 17 X: 320.79  Y: 54.38  Z: 321.03
r_side 0   m_tip: 0   m_b: 0   m_side: 0   i_tip: 0   i_side: 0   p_side: 0thumb: 24   index: 19   middle: 18   ring: 19   pinky: 16 X: 319.66  Y: 54.51  Z: 319.48
r_side 0   m_tip: 0   m_b: 0   m_side: 0   i_tip: 0   i_side: 0   p_side: 0thumb: 24   index: 19   middle: 18   ring: 18   pinky: 16 X: 317.76  Y: 54.57  Z: 316.92
r_side 0   m_tip: 0   m_b: 0   m_side: 0   i_tip: 0   i_side: 0   p_side: 0thumb: 23   index: 19   middle: 18   ring: 18   pinky: 16 X: 317.02  Y: 54.97  Z: 316.19
r_side 0   m_tip: 0   m_b: 0   m_side: 0   i_tip: 0   i_side: 0   p_side: 0thumb: 23   index: 19   middle: 18   ring: 18   pinky: 16 X: 315.36  Y: 55.75  Z: 314.47
r_side 0   m_tip: 0   m_b: 0   m_side: 0   i_tip: 0   i_side: 0   p_side: 0thumb: 23   index: 19   middle: 18   ring: 18   pinky: 16 X: 314.81  Y: 55.54  Z: 313.32
r_side 0   m_tip: 0   m_b: 0   m_side: 0   i_tip: 0   i_side: 0   p_side: 0thumb: 23   index: 19   middle: 18   ring: 18   pinky: 16 X: 314.93  Y: 55.19  Z: 312.96
r_side 0   m_tip: 0   m_b: 0   m_side: 0   i_tip: 0   i_side: 0   p_side: 0thumb: 23   index: 19   middle: 18   ring: 18   pinky: 16 X: 313.64  Y: 55.30  Z: 311.21
r_side 0   m_tip: 0   m_b: 0   m_side: 0   i_tip: 0   i_side: 0   p_side: 0thumb: 23   index: 19   middle: 18   ring: 18   pinky: 16 X: 312.88  Y: 55.12  Z: 310.25
r_side 0   m_tip: 0   m_b: 0   m_side: 0   i_tip: 0   i_side: 0   p_side: 0thumb: 23   index: 19   middle: 18   ring: 18   pinky: 16 X: 311.84  Y: 55.32  Z: 308.89
r_side 0   m_tip: 0   m_b: 0   m_side: 0   i_tip: 0   i_side: 0   p_side: 0thumb: 23   index: 18   middle: 18   ring: 18   pinky: 16 X: 311.39  Y: 54.96  Z: 308.11
r_side 0   m_tip: 0   m_b: 0   m_side: 0   i_tip: 0   i_side: 0   p_side: 0thumb: 22   index: 19   middle: 18   ring: 18   pinky: 16 X: 310.90  Y: 54.94  Z: 307.26
r_side 0   m_tip: 0   m_b: 0   m_side: 0   i_tip: 0   i_side: 0   p_side: 0thumb: 22   index: 19   middle: 18   ring: 18   pinky: 16 X: 309.81  Y: 54.73  Z: 306.12
r_side 0   m_tip: 0   m_b: 0   m_side: 0   i_tip: 0   i_side: 0   p_side: 0thumb: 23   index: 19   middle: 18   ring: 18   pinky: 15 X: 309.10  Y: 54.32  Z: 305.04
r_side 0   m_tip: 0   m_b: 0   m_side: 0   i_tip: 0   i_side: 0   p_side: 0thumb: 22   index: 19   middle: 18   ring: 18   pinky: 15 X: 308.00  Y: 54.15  Z: 303.88
r_side 0   m_tip: 0   m_b: 0   m_side: 0   i_tip: 0   i_side: 0   p_side: 0thumb: 23   index: 18   middle: 18   ring: 18   pinky: 15 X: 306.78  Y: 54.05  Z: 302.50
r_side 0   m_tip: 0   m_b: 0   m_side: 0   i_tip: 0   i_side: 0   p_side: 0thumb: 22   index: 18   middle: 17   ring: 18   pinky: 15 X: 306.49  Y: 53.53  Z: 302.04
r_side 0   m_tip: 0   m_b: 0   m_side: 0   i_tip: 0   i_side: 0   p_side: 0thumb: 22   index: 18   middle: 17   ring: 18   pinky: 15 X: 305.82  Y: 53.06  Z: 301.46
r_side 0   m_tip: 0   m_b: 0   m_side: 0   i_tip: 0   i_side: 0   p_side: 0thumb: 22   index: 19   middle: 17   ring: 18   pinky: 15 X: 305.89  Y: 52.15  Z: 301.61
r_side 0   m_tip: 0   m_b: 0   m_side: 0   i_tip: 0   i_side: 0   p_side: 0thumb: 22   index: 18   middle: 17   ring: 17   pinky: 15 X: 305.00  Y: 51.92  Z: 301.00
r_side 0   m_tip: 0   m_b: 0   m_side: 0   i_tip: 0   i_side: 0   p_side: 0thumb: 22   index: 18   middle: 17   ring: 17   pinky: 15 X: 304.48  Y: 51.23  Z: 300.77
r_side 0   m_tip: 0   m_b: 0   m_side: 0   i_tip: 0   i_side: 0   p_side: 0thumb: 22   index: 19   middle: 17   ring: 17   pinky: 15 X: 304.41  Y: 50.69  Z: 300.73
r_side 0   m_tip: 0   m_b: 0   m_side: 0   i_tip: 0   i_side: 0   p_side: 0thumb: 21   index: 18   middle: 17   ring: 18   pinky: 15 X: 305.33  Y: 49.55  Z: 301.89
r_side 0   m_tip: 0   m_b: 0   m_side: 0   i_tip: 0   i_side: 0   p_side: 0thumb: 22   index: 18   middle: 18   ring: 17   pinky: 15 X: 304.27  Y: 49.57  Z: 300.88
r_side 0   m_tip: 0   m_b: 0   m_side: 0   i_tip: 0   i_side: 0   p_side: 0thumb: 22   index: 18   middle: 17   ring: 18   pinky: 15 X: 304.37  Y: 48.96  Z: 300.80
r_side 0   m_tip: 0   m_b: 0   m_side: 0   i_tip: 0   i_side: 0   p_side: 0thumb: 22   index: 18   middle: 17   ring: 17   pinky: 15 X: 304.12  Y: 48.53  Z: 300.70
r_side 0   m_tip: 0   m_b: 0   m_side: 0   i_tip: 0   i_side: 0   p_side: 0thumb: 22   index: 18   middle: 17   ring: 17   pinky: 15 X: 303.44  Y: 48.30  Z: 300.02
