juanmrq95/ee149_104/ASLsensing/longFlex/save_sensordata/Test 2 Juan/testJuanLetterF.txt

hr_side 0   m_tip: 0   m_b: 0   m_side: 0   i_tip: 0   i_side: 0   p_side: 0thumb: 5   index: 4   middle: 4   ring: 5   pinky: 3 X: 357.26  Y: 5.20  Z: 354.51
r_side 0   m_tip: 0   m_b: 0   m_side: 0   i_tip: 0   i_side: 0   p_side: 0thumb: 5   index: 4   middle: 4   ring: 5   pinky: 3 X: 356.62  Y: 7.75  Z: 351.16
r_side 0   m_tip: 0   m_b: 0   m_side: 0   i_tip: 0   i_side: 0   p_side: 0thumb: 5   index: 4   middle: 4   ring: 5   pinky: 3 X: 355.81  Y: 9.94  Z: 347.82
r_side 0   m_tip: 0   m_b: 0   m_side: 0   i_tip: 0   i_side: 0   p_side: 0thumb: 5   index: 4   middle: 4   ring: 5   pinky: 3 X: 354.76  Y: 12.94  Z: 344.12
r_side 0   m_tip: 0   m_b: 0   m_side: 0   i_tip: 0   i_side: 0   p_side: 0thumb: 5   index: 7   middle: 4   ring: 5   pinky: 30 X: 348.12  Y: 25.68  Z: 330.50
r_side 0   m_tip: 0   m_b: 0   m_side: 1   i_tip: 1   i_side: 0   p_side: 0thumb: 7   index: 14   middle: 4   ring: 5   pinky: 3 X: 333.21  Y: 43.32  Z: 327.13
r_side 0   m_tip: 0   m_b: 0   m_side: 1   i_tip: 1   i_side: 0   p_side: 0thumb: 12   index: 13   middle: 4   ring: 5   pinky: 2 X: 322.91  Y: 48.62  Z: 322.25
r_side 0   m_tip: 0   m_b: 0   m_side: 1   i_tip: 1   i_side: 0   p_side: 0thumb: 12   index: 13   middle: 4   ring: 4   pinky: 2 X: 315.22  Y: 50.40  Z: 315.35
r_side 0   m_tip: 0   m_b: 0   m_side: 1   i_tip: 1   i_side: 0   p_side: 0thumb: 12   index: 12   middle: 4   ring: 4   pinky: 2 X: 312.24  Y: 50.31  Z: 311.13
r_side 0   m_tip: 0   m_b: 0   m_side: 1   i_tip: 1   i_side: 0   p_side: 0thumb: 12   index: 12   middle: 4   ring: 4   pinky: 2 X: 310.56  Y: 50.39  Z: 309.07
r_side 0   m_tip: 0   m_b: 0   m_side: 1   i_tip: 1   i_side: 0   p_side: 0thumb: 11   index: 12   middle: 3   ring: 4   pinky: 2 X: 307.90  Y: 50.90  Z: 305.37
r_side 0   m_tip: 0   m_b: 0   m_side: 1   i_tip: 1   i_side: 0   p_side: 0thumb: 11   index: 12   middle: 3   ring: 4   pinky: 2 X: 306.82  Y: 50.31  Z: 303.30
r_side 0   m_tip: 0   m_b: 0   m_side: 1   i_tip: 1   i_side: 0   p_side: 0thumb: 11   index: 12   middle: 3   ring: 4   pinky: 2 X: 304.54  Y: 49.70  Z: 300.39
r_side 0   m_tip: 0   m_b: 0   m_side: 1   i_tip: 1   i_side: 0   p_side: 0thumb: 11   index: 12   middle: 4   ring: 4   pinky: 2 X: 303.39  Y: 49.28  Z: 298.20
r_side 0   m_tip: 0   m_b: 0   m_side: 1   i_tip: 1   i_side: 0   p_side: 0thumb: 11   index: 12   middle: 3   ring: 4   pinky: 2 X: 301.49  Y: 48.88  Z: 296.18
r_side 0   m_tip: 0   m_b: 0   m_side: 1   i_tip: 1   i_side: 0   p_side: 0thumb: 11   index: 12   middle: 3   ring: 4   pinky: 2 X: 299.01  Y: 48.61  Z: 293.56
r_side 0   m_tip: 0   m_b: 0   m_side: 1   i_tip: 1   i_side: 0   p_side: 0thumb: 11   index: 12   middle: 3   ring: 4   pinky: 2 X: 297.48  Y: 48.10  Z: 291.74
r_side 0   m_tip: 0   m_b: 0   m_side: 1   i_tip: 1   i_side: 0   p_side: 0thumb: 11   index: 12   middle: 3   ring: 3   pinky: 1 X: 296.11  Y: 47.42  Z: 290.15
r_side 0   m_tip: 0   m_b: 0   m_side: 1   i_tip: 1   i_side: 0   p_side: 0thumb: 11   index: 12   middle: 3   ring: 3   pinky: 2 X: 295.10  Y: 47.05  Z: 289.01
r_side 0   m_tip: 0   m_b: 0   m_side: 1   i_tip: 1   i_side: 0   p_side: 0thumb: 11   index: 12   middle: 3   ring: 3   pinky: 1 X: 293.88  Y: 46.22  Z: 287.38
r_side 0   m_tip: 0   m_b: 0   m_side: 1   i_tip: 1   i_side: 0   p_side: 0thumb: 9   index: 12   middle: 3   ring: 4   pinky: 1 X: 292.74  Y: 46.11  Z: 286.56
r_side 0   m_tip: 0   m_b: 0   m_side: 1   i_tip: 1   i_side: 0   p_side: 0thumb: 11   index: 12   middle: 3   ring: 3   pinky: 1 X: 293.13  Y: 45.53  Z: 286.46
r_side 0   m_tip: 0   m_b: 0   m_side: 1   i_tip: 1   i_side: 0   p_side: 0thumb: 11   index: 12   middle: 3   ring: 3   pinky: 1 X: 292.32  Y: 44.91  Z: 285.73
r_side 0   m_tip: 0   m_b: 0   m_side: 1   i_tip: 1   i_side: 0   p_side: 0thumb: 11   index: 11   middle: 3   ring: 3   pinky: 1 X: 291.75  Y: 44.37  Z: 285.07
r_side 0   m_tip: 0   m_b: 0   m_side: 1   i_tip: 1   i_side: 0   p_side: 0thumb: 11   index: 12   middle: 3   ring: 4   pinky: 2 X: 291.23  Y: 43.59  Z: 284.50
r_side 0   m_tip: 0   m_b: 0   m_side: 1   i_tip: 1   i_side: 0   p_side: 0thumb: 11   index: 11   middle: 3   ring: 3   pinky: 2 X: 290.80  Y: 42.79  Z: 283.80
r_side 0   m_tip: 0   m_b: 0   m_side: 1   i_tip: 1   i_side: 0   p_side: 0thumb: 11   index: 11   middle: 3   ring: 3   pinky: 1 X: 290.76  Y: 41.73  Z: 283.60
r_side 0   m_tip: 0   m_b: 0   m_side: 1   i_tip: 1   i_side: 0   p_side: 0thumb: 11   index: 11   middle: 3   ring: 3   pinky: 2 X: 290.19  Y: 40.96  Z: 283.18
r_side 0   m_tip: 0   m_b: 0   m_side: 1   i_tip: 1   i_side: 0   p_side: 0thumb: 11   index: 11   middle: 3   ring: 3   pinky: 1 X: 290.00  Y: 40.31  Z: 283.10
r_side 0   m_tip: 0   m_b: 0   m_side: 1   i_tip: 1   i_side: 0   p_side: 0thumb: 11   index: 12   middle: 3   ring: 3   pinky: 1 X: 289.72  Y: 39.31  Z: 282.65
r_side 0   m_tip: 0   m_b: 0   m_side: 1   i_tip: 1   i_side: 0   p_side: 0thumb: 11   index: 11   middle: 4   ring: 3   pinky: 1 X: 289.41  Y: 38.64  Z: 282.67
r_side 0   m_tip: 0   m_b: 0   m_side: 1   i_tip: 1   i_side: 0   p_side: 0thumb: 11   index: 12   middle: 3   ring: 3   pinky: 1 X: 289.65  Y: 37.60  Z: 282.75
r_side 0   m_tip: 0   m_b: 0   m_side: 1   i_tip: 1   i_side: 0   p_side: 0thumb: 11   index: 11   middle: 3   ring: 3   pinky: 1 X: 289.97  Y: 36.78  Z: 283.07
r_side 0   m_tip: 0   m_b: 0   m_side: 1   i_tip: 1   i_side: 0   p_side: 0thumb: 11   index: 11   middle: 3   ring: 3   pinky: 1 X: 289.73  Y: 36.01  Z: 282.98
r_side 0   m_tip: 0   m_b: 0   m_side: 1   i_tip: 1   i_side: 0   p_side: 0thumb: 11   index: 12   middle: 3   ring: 3   pinky: 2 X: 289.98  Y: 35.05  Z: 283.11
r_side 0   m_tip: 0   m_b: 0   m_side: 1   i_tip: 1   i_side: 0   p_side: 0thumb: 11   index: 11   middle: 3   ring: 3   pinky: 1 X: 290.18  Y: 34.04  Z: 283.53
r_side 0   m_tip: 0   m_b: 0   m_side: 1   i_tip: 1   i_side: 0   p_side: 0thumb: 11   index: 11   middle: 3   ring: 3   pinky: 1 X: 290.68  Y: 33.01  Z: 283.95
r_side 0   m_tip: 0   m_b: 0   m_side: 1   i_tip: 1   i_side: 0   p_side: 0thumb: 11   index: 11   middle: 3   ring: 3   pinky: 1 X: 290.69  Y: 32.10  Z: 283.71
r_side 0   m_tip: 0   m_b: 0   m_side: 1   i_tip: 1   i_side: 0   p_side: 0thumb: 11   index: 11   middle: 3   ring: 4   pinky: 1 X: 290.70  Y: 31.32  Z: 283.97
r_side 0   m_tip: 0   m_b: 0   m_side: 1   i_tip: 1   i_side: 0   p_side: 0thumb: 11   index: 11   middle: 3   ring: 3   pinky: 1 X: 290.52  Y: 30.50  Z: 284.12
r_side 0   m_tip: 0   m_b: 0   m_side: 1   i_tip: 1   i_side: 0   p_side: 0thumb: 11   index: 11   middle: 3   ring: 3   pinky: 1 X: 290.88  Y: 29.27  Z: 284.48
