juanmrq95/ee149_104/ASLsensing/longFlex/save_sensordata/Test 2 Juan/testJuanLetterG.txt

r_side 0   m_tip: 0   m_b: 0   m_side: 0   i_tip: 0   i_side: 0   p_side: 0thumb: 1   index: 1   middle: 4   ring: 4   pinky: 2 X: 359.61  Y: 359.74  Z: 0.00
r_side 0   m_tip: 0   m_b: 0   m_side: 0   i_tip: 0   i_side: 0   p_side: 0thumb: 1   index: 1   middle: 4   ring: 4   pinky: 2 X: 359.61  Y: 0.69  Z: 357.15
r_side 0   m_tip: 0   m_b: 0   m_side: 0   i_tip: 0   i_side: 0   p_side: 0thumb: 2   index: 1   middle: 4   ring: 4   pinky: 2 X: 359.60  Y: 1.12  Z: 354.35
r_side 0   m_tip: 0   m_b: 0   m_side: 0   i_tip: 0   i_side: 0   p_side: 0thumb: 1   index: 1   middle: 4   ring: 4   pinky: 2 X: 359.37  Y: 2.01  Z: 351.73
r_side 0   m_tip: 0   m_b: 0   m_side: 0   i_tip: 0   i_side: 0   p_side: 0thumb: 1   index: 1   middle: 4   ring: 4   pinky: 1 X: 359.19  Y: 2.68  Z: 349.42
r_side 0   m_tip: 0   m_b: 0   m_side: 0   i_tip: 0   i_side: 0   p_side: 0thumb: 1   index: 1   middle: 4   ring: 4   pinky: 2 X: 358.43  Y: 3.67  Z: 346.82
r_side 0   m_tip: 0   m_b: 0   m_side: 0   i_tip: 0   i_side: 0   p_side: 0thumb: 2   index: 1   middle: 7   ring: 5   pinky: 2 X: 346.41  Y: 5.44  Z: 315.54
r_side 0   m_tip: 0   m_b: 0   m_side: 0   i_tip: 0   i_side: 0   p_side: 0thumb: 2   index: 2   middle: 19   ring: 19   pinky: 15 X: 338.21  Y: 348.42  Z: 304.85
r_side 0   m_tip: 0   m_b: 0   m_side: 0   i_tip: 0   i_side: 0   p_side: 0thumb: 2   index: 1   middle: 19   ring: 20   pinky: 17 X: 334.97  Y: 344.75  Z: 305.13
r_side 0   m_tip: 0   m_b: 0   m_side: 0   i_tip: 0   i_side: 0   p_side: 0thumb: 2   index: 2   middle: 19   ring: 19   pinky: 16 X: 334.00  Y: 343.18  Z: 304.58
r_side 0   m_tip: 0   m_b: 0   m_side: 0   i_tip: 0   i_side: 0   p_side: 0thumb: 2   index: 1   middle: 18   ring: 18   pinky: 15 X: 332.86  Y: 342.86  Z: 302.75
r_side 0   m_tip: 0   m_b: 0   m_side: 0   i_tip: 0   i_side: 0   p_side: 0thumb: 2   index: 1   middle: 19   ring: 19   pinky: 15 X: 333.14  Y: 341.59  Z: 300.16
r_side 0   m_tip: 0   m_b: 0   m_side: 0   i_tip: 0   i_side: 0   p_side: 0thumb: 3   index: 1   middle: 19   ring: 19   pinky: 15 X: 333.74  Y: 340.98  Z: 298.77
r_side 0   m_tip: 1   m_b: 0   m_side: 0   i_tip: 0   i_side: 0   p_side: 0thumb: 3   index: 1   middle: 19   ring: 19   pinky: 15 X: 334.22  Y: 340.67  Z: 297.44
r_side 0   m_tip: 1   m_b: 0   m_side: 0   i_tip: 0   i_side: 0   p_side: 0thumb: 3   index: 2   middle: 19   ring: 19   pinky: 15 X: 334.59  Y: 339.96  Z: 295.30
r_side 0   m_tip: 1   m_b: 0   m_side: 0   i_tip: 0   i_side: 0   p_side: 0thumb: 3   index: 2   middle: 19   ring: 19   pinky: 15 X: 334.40  Y: 340.24  Z: 294.55
r_side 0   m_tip: 1   m_b: 0   m_side: 0   i_tip: 0   i_side: 0   p_side: 0thumb: 3   index: 2   middle: 19   ring: 19   pinky: 15 X: 334.32  Y: 340.29  Z: 293.22
r_side 0   m_tip: 1   m_b: 0   m_side: 0   i_tip: 0   i_side: 0   p_side: 0thumb: 3   index: 2   middle: 19   ring: 19   pinky: 15 X: 334.41  Y: 340.29  Z: 292.14
r_side 0   m_tip: 1   m_b: 0   m_side: 0   i_tip: 0   i_side: 0   p_side: 0thumb: 3   index: 2   middle: 19   ring: 19   pinky: 15 X: 334.82  Y: 340.04  Z: 291.70
r_side 0   m_tip: 1   m_b: 0   m_side: 0   i_tip: 0   i_side: 0   p_side: 0thumb: 3   index: 2   middle: 19   ring: 18   pinky: 15 X: 335.21  Y: 340.15  Z: 291.57
r_side 0   m_tip: 1   m_b: 0   m_side: 0   i_tip: 0   i_side: 0   p_side: 0thumb: 3   index: 2   middle: 19   ring: 18   pinky: 15 X: 335.38  Y: 340.04  Z: 290.83
r_side 0   m_tip: 1   m_b: 0   m_side: 0   i_tip: 0   i_side: 0   p_side: 0thumb: 3   index: 1   middle: 19   ring: 18   pinky: 15 X: 335.44  Y: 340.29  Z: 290.32
r_side 0   m_tip: 1   m_b: 0   m_side: 0   i_tip: 0   i_side: 0   p_side: 0thumb: 3   index: 2   middle: 19   ring: 18   pinky: 15 X: 335.24  Y: 340.45  Z: 290.15
r_side 0   m_tip: 1   m_b: 0   m_side: 0   i_tip: 0   i_side: 0   p_side: 0thumb: 3   index: 2   middle: 19   ring: 18   pinky: 15 X: 335.27  Y: 340.37  Z: 290.29
r_side 0   m_tip: 1   m_b: 0   m_side: 0   i_tip: 0   i_side: 0   p_side: 0thumb: 3   index: 2   middle: 18   ring: 18   pinky: 14 X: 335.35  Y: 340.42  Z: 289.73
r_side 0   m_tip: 1   m_b: 0   m_side: 0   i_tip: 0   i_side: 0   p_side: 0thumb: 3   index: 2   middle: 18   ring: 18   pinky: 14 X: 335.19  Y: 340.62  Z: 289.45
r_side 0   m_tip: 1   m_b: 0   m_side: 0   i_tip: 0   i_side: 0   p_side: 0thumb: 3   index: 2   middle: 18   ring: 18   pinky: 14 X: 335.15  Y: 340.47  Z: 289.49
r_side 0   m_tip: 1   m_b: 0   m_side: 0   i_tip: 0   i_side: 0   p_side: 0thumb: 3   index: 2   middle: 19   ring: 18   pinky: 14 X: 335.13  Y: 340.25  Z: 289.72
r_side 0   m_tip: 1   m_b: 0   m_side: 0   i_tip: 0   i_side: 0   p_side: 0thumb: 3   index: 2   middle: 18   ring: 18   pinky: 14 X: 335.02  Y: 340.34  Z: 289.59
r_side 0   m_tip: 1   m_b: 0   m_side: 0   i_tip: 0   i_side: 0   p_side: 0thumb: 3   index: 1   middle: 18   ring: 18   pinky: 14 X: 335.11  Y: 340.07  Z: 289.73
r_side 0   m_tip: 1   m_b: 0   m_side: 0   i_tip: 0   i_side: 0   p_side: 0thumb: 3   index: 2   middle: 18   ring: 18   pinky: 14 X: 335.03  Y: 339.74  Z: 289.55
r_side 0   m_tip: 1   m_b: 0   m_side: 0   i_tip: 0   i_side: 0   p_side: 0thumb: 4   index: 2   middle: 18   ring: 18   pinky: 14 X: 334.78  Y: 339.81  Z: 289.82
r_side 0   m_tip: 1   m_b: 0   m_side: 0   i_tip: 0   i_side: 0   p_side: 0thumb: 3   index: 2   middle: 17   ring: 18   pinky: 14 X: 334.64  Y: 339.72  Z: 289.79
r_side 0   m_tip: 1   m_b: 0   m_side: 0   i_tip: 0   i_side: 0   p_side: 0thumb: 3   index: 2   middle: 18   ring: 17   pinky: 14 X: 334.51  Y: 339.86  Z: 290.05
r_side 0   m_tip: 1   m_b: 0   m_side: 0   i_tip: 0   i_side: 0   p_side: 0thumb: 3   index: 2   middle: 17   ring: 18   pinky: 13 X: 334.39  Y: 339.64  Z: 290.04
r_side 0   m_tip: 1   m_b: 0   m_side: 0   i_tip: 0   i_side: 0   p_side: 0thumb: 3   index: 2   middle: 18   ring: 18   pinky: 14 X: 334.54  Y: 339.48  Z: 290.16
r_side 0   m_tip: 1   m_b: 0   m_side: 0   i_tip: 0   i_side: 0   p_side: 0thumb: 2   index: 2   middle: 18   ring: 18   pinky: 14 X: 334.67  Y: 339.38  Z: 290.33
r_side 0   m_tip: 1   m_b: 0   m_side: 0   i_tip: 0   i_side: 0   p_side: 0thumb: 3   index: 1   middle: 18   ring: 17   pinky: 14 X: 334.57  Y: 339.26  Z: 290.79
r_side 0   m_tip: 1   m_b: 0   m_side: 0   i_tip: 0   i_side: 0   p_side: 0thumb: 3   index: 2   middle: 18   ring: 18   pinky: 14 X: 334.77  Y: 339.24  Z: 290.98
r_side 0   m_tip: 1   m_b: 0   m_side: 0   i_tip: 0   i_side: 0   p_side: 0thumb: 2   index: 2   middle: 17   ring: 18   pinky: 14 X: 334.29  Y: 339.35  Z: 291.56
r_side 0   m_tip: 1   m_b: 0   m_side: 0   i_tip: 0   i_side: 0   p_side: 0thumb: 2   index: 2   middle: 18   ring: 17   pinky: 14 X: 334.30  Y: 339.54  Z: 291.99
r_side 0   m_tip: 1   m_b: 0   m_side: 0   i_tip: 0   i_side: 0   p_side: 0thumb: 2   index: 2   middle: 18   ring: 17   pinky: 14 X: 334.01  Y: 339.55  Z: 292.17
