juanmrq95/ee149_104/ASLsensing/longFlex/save_sensordata/Test 2 Juan/testJuanLetterH.txt

ýr_side 0   m_tip: 0   m_b: 0   m_side: 0   i_tip: 0   i_side: 0   p_side: 0thumb: 2   index: 1   middle: 3   ring: 4   pinky: 2 X: 359.48  Y: 0.14  Z: 1.18
r_side 0   m_tip: 0   m_b: 0   m_side: 0   i_tip: 0   i_side: 0   p_side: 0thumb: 2   index: 1   middle: 3   ring: 4   pinky: 2 X: 359.20  Y: 0.62  Z: 359.21
r_side 0   m_tip: 0   m_b: 0   m_side: 0   i_tip: 0   i_side: 0   p_side: 0thumb: 1   index: 1   middle: 4   ring: 4   pinky: 2 X: 359.24  Y: 1.41  Z: 356.88
r_side 0   m_tip: 0   m_b: 0   m_side: 0   i_tip: 0   i_side: 0   p_side: 0thumb: 2   index: 1   middle: 4   ring: 4   pinky: 2 X: 359.18  Y: 1.68  Z: 355.05
r_side 0   m_tip: 0   m_b: 0   m_side: 0   i_tip: 0   i_side: 0   p_side: 0thumb: 2   index: 1   middle: 4   ring: 4   pinky: 2 X: 344.49  Y: 18.24  Z: 347.35
r_side 0   m_tip: 0   m_b: 0   m_side: 0   i_tip: 0   i_side: 0   p_side: 0thumb: 2   index: 1   middle: 4   ring: 17   pinky: 18 X: 333.64  Y: 10.56  Z: 320.87
r_side 0   m_tip: 0   m_b: 0   m_side: 0   i_tip: 0   i_side: 0   p_side: 0thumb: 5   index: 1   middle: 4   ring: 17   pinky: 17 X: 328.38  Y: 347.91  Z: 329.98
r_side 0   m_tip: 0   m_b: 0   m_side: 0   i_tip: 0   i_side: 0   p_side: 0thumb: 15   index: 1   middle: 4   ring: 18   pinky: 17 X: 324.26  Y: 332.24  Z: 328.62
r_side 0   m_tip: 0   m_b: 0   m_side: 0   i_tip: 0   i_side: 0   p_side: 0thumb: 18   index: 1   middle: 3   ring: 18   pinky: 17 X: 315.37  Y: 316.18  Z: 330.77
r_side 0   m_tip: 0   m_b: 0   m_side: 0   i_tip: 0   i_side: 0   p_side: 0thumb: 19   index: 1   middle: 3   ring: 19   pinky: 17 X: 309.82  Y: 310.32  Z: 332.26
r_side 0   m_tip: 0   m_b: 0   m_side: 0   i_tip: 0   i_side: 0   p_side: 0thumb: 20   index: 1   middle: 3   ring: 19   pinky: 17 X: 307.04  Y: 300.38  Z: 334.69
r_side 0   m_tip: 0   m_b: 0   m_side: 0   i_tip: 0   i_side: 0   p_side: 0thumb: 19   index: 1   middle: 3   ring: 18   pinky: 16 X: 302.99  Y: 304.69  Z: 340.39
r_side 0   m_tip: 0   m_b: 0   m_side: 0   i_tip: 0   i_side: 0   p_side: 0thumb: 18   index: 1   middle: 3   ring: 18   pinky: 16 X: 303.05  Y: 303.73  Z: 339.23
r_side 0   m_tip: 0   m_b: 0   m_side: 0   i_tip: 0   i_side: 0   p_side: 0thumb: 18   index: 1   middle: 3   ring: 17   pinky: 16 X: 304.01  Y: 302.88  Z: 336.65
r_side 0   m_tip: 0   m_b: 0   m_side: 0   i_tip: 0   i_side: 0   p_side: 0thumb: 18   index: 1   middle: 3   ring: 17   pinky: 16 X: 305.19  Y: 301.73  Z: 333.71
r_side 0   m_tip: 0   m_b: 0   m_side: 0   i_tip: 0   i_side: 0   p_side: 0thumb: 18   index: 1   middle: 3   ring: 17   pinky: 16 X: 306.69  Y: 301.22  Z: 330.71
r_side 0   m_tip: 0   m_b: 0   m_side: 0   i_tip: 0   i_side: 0   p_side: 0thumb: 18   index: 1   middle: 3   ring: 17   pinky: 16 X: 308.27  Y: 300.08  Z: 327.57
r_side 0   m_tip: 0   m_b: 0   m_side: 0   i_tip: 0   i_side: 0   p_side: 0thumb: 18   index: 1   middle: 3   ring: 17   pinky: 16 X: 310.09  Y: 299.55  Z: 324.65
r_side 0   m_tip: 0   m_b: 0   m_side: 0   i_tip: 0   i_side: 0   p_side: 0thumb: 18   index: 1   middle: 3   ring: 17   pinky: 16 X: 310.44  Y: 299.63  Z: 323.44
r_side 0   m_tip: 0   m_b: 0   m_side: 0   i_tip: 0   i_side: 0   p_side: 0thumb: 18   index: 1   middle: 3   ring: 17   pinky: 16 X: 311.43  Y: 300.29  Z: 321.40
r_side 0   m_tip: 0   m_b: 0   m_side: 0   i_tip: 0   i_side: 0   p_side: 0thumb: 18   index: 1   middle: 3   ring: 17   pinky: 16 X: 311.90  Y: 300.46  Z: 320.39
r_side 0   m_tip: 0   m_b: 0   m_side: 0   i_tip: 0   i_side: 0   p_side: 0thumb: 19   index: 1   middle: 3   ring: 17   pinky: 16 X: 312.50  Y: 300.24  Z: 318.90
r_side 0   m_tip: 0   m_b: 0   m_side: 0   i_tip: 0   i_side: 0   p_side: 0thumb: 18   index: 0   middle: 3   ring: 17   pinky: 16 X: 313.71  Y: 300.28  Z: 316.84
r_side 0   m_tip: 0   m_b: 0   m_side: 0   i_tip: 0   i_side: 0   p_side: 0thumb: 18   index: 1   middle: 3   ring: 17   pinky: 15 X: 314.45  Y: 300.34  Z: 315.51
r_side 0   m_tip: 0   m_b: 0   m_side: 0   i_tip: 0   i_side: 0   p_side: 0thumb: 18   index: 1   middle: 3   ring: 17   pinky: 15 X: 314.85  Y: 300.46  Z: 314.36
r_side 0   m_tip: 0   m_b: 0   m_side: 0   i_tip: 0   i_side: 0   p_side: 0thumb: 17   index: 1   middle: 3   ring: 18   pinky: 15 X: 315.61  Y: 300.60  Z: 312.98
r_side 0   m_tip: 0   m_b: 0   m_side: 0   i_tip: 0   i_side: 0   p_side: 0thumb: 17   index: 1   middle: 3   ring: 16   pinky: 16 X: 316.24  Y: 300.65  Z: 311.77
r_side 0   m_tip: 0   m_b: 0   m_side: 0   i_tip: 0   i_side: 0   p_side: 0thumb: 18   index: 1   middle: 2   ring: 16   pinky: 15 X: 316.99  Y: 300.63  Z: 310.84
r_side 0   m_tip: 0   m_b: 0   m_side: 0   i_tip: 0   i_side: 0   p_side: 0thumb: 17   index: 1   middle: 3   ring: 16   pinky: 15 X: 316.93  Y: 300.96  Z: 310.78
r_side 0   m_tip: 0   m_b: 0   m_side: 0   i_tip: 0   i_side: 0   p_side: 0thumb: 17   index: 1   middle: 3   ring: 16   pinky: 15 X: 318.31  Y: 300.66  Z: 309.26
r_side 0   m_tip: 0   m_b: 0   m_side: 0   i_tip: 0   i_side: 0   p_side: 0thumb: 17   index: 1   middle: 3   ring: 17   pinky: 15 X: 318.97  Y: 301.00  Z: 308.56
r_side 0   m_tip: 0   m_b: 0   m_side: 0   i_tip: 0   i_side: 0   p_side: 0thumb: 17   index: 1   middle: 3   ring: 16   pinky: 15 X: 319.09  Y: 301.10  Z: 307.88
r_side 0   m_tip: 0   m_b: 0   m_side: 0   i_tip: 0   i_side: 0   p_side: 0thumb: 18   index: 1   middle: 3   ring: 16   pinky: 15 X: 318.83  Y: 301.46  Z: 308.36
r_side 0   m_tip: 0   m_b: 0   m_side: 0   i_tip: 0   i_side: 0   p_side: 0thumb: 17   index: 1   middle: 3   ring: 16   pinky: 15 X: 319.26  Y: 301.28  Z: 307.80
r_side 0   m_tip: 0   m_b: 0   m_side: 0   i_tip: 0   i_side: 0   p_side: 0thumb: 17   index: 1   middle: 3   ring: 16   pinky: 15 X: 319.57  Y: 301.44  Z: 307.40
r_side 0   m_tip: 0   m_b: 0   m_side: 0   i_tip: 0   i_side: 0   p_side: 0thumb: 17   index: 0   middle: 3   ring: 16   pinky: 15 X: 319.70  Y: 301.83  Z: 307.08
r_side 0   m_tip: 0   m_b: 0   m_side: 0   i_tip: 0   i_side: 0   p_side: 0thumb: 17   index: 1   middle: 3   ring: 16   pinky: 15 X: 319.49  Y: 302.04  Z: 307.17
r_side 0   m_tip: 0   m_b: 0   m_side: 0   i_tip: 0   i_side: 0   p_side: 0thumb: 17   index: 1   middle: 3   ring: 16   pinky: 15 X: 319.40  Y: 302.40  Z: 306.90
r_side 0   m_tip: 0   m_b: 0   m_side: 0   i_tip: 0   i_side: 0   p_side: 0thumb: 17   index: 1   middle: 3   ring: 16   pinky: 15 X: 319.18  Y: 303.06  Z: 307.37
r_side 0   m_tip: 0   m_b: 0   m_side: 0   i_tip: 0   i_side: 0   p_side: 0thumb: 17   index: 1   middle: 3   ring: 16   pinky: 15 X: 319.11  Y: 303.26  Z: 307.47
r_side 0   m_tip: 0   m_b: 0   m_side: 0   i_tip: 0   i_side: 0   p_side: 0thumb: 17   index: 1   middle: 3   ring: 16   pinky: 15 X: 319.48  Y: 303.02  Z: 307.08
r_side 0   m_tip: 0   m_b: 0   m_side: 0   i_tip: 0   i_side: 0   p_side: 0thumb: 17   index: 1   middle: 3   ring: 16   pinky: 15 X: 319.51  Y: 303.36  Z: 306.77
