juanmrq95/ee149_104/ASLsensing/longFlex/save_sensordata/Test 2 Juan/testJuanLetterK.txt

àr_side 0   m_tip: 0   m_b: 0   m_side: 0   i_tip: 0   i_side: 0   p_side: 0thumb: 3   index: 0   middle: 3   ring: 4   pinky: 3 X: 358.38  Y: 2.04  Z: 357.35
r_side 0   m_tip: 0   m_b: 0   m_side: 0   i_tip: 0   i_side: 0   p_side: 0thumb: 3   index: 0   middle: 4   ring: 5   pinky: 3 X: 358.21  Y: 4.16  Z: 355.48
r_side 0   m_tip: 0   m_b: 0   m_side: 0   i_tip: 0   i_side: 0   p_side: 0thumb: 2   index: 0   middle: 4   ring: 5   pinky: 3 X: 357.95  Y: 6.03  Z: 352.69
r_side 0   m_tip: 0   m_b: 0   m_side: 0   i_tip: 0   i_side: 0   p_side: 0thumb: 2   index: 0   middle: 4   ring: 5   pinky: 3 X: 357.75  Y: 7.79  Z: 350.35
r_side 0   m_tip: 0   m_b: 0   m_side: 0   i_tip: 0   i_side: 0   p_side: 0thumb: 4   index: 0   middle: 4   ring: 5   pinky: 3 X: 357.38  Y: 9.62  Z: 348.10
r_side 0   m_tip: 0   m_b: 0   m_side: 0   i_tip: 0   i_side: 0   p_side: 0thumb: 2   index: 0   middle: 4   ring: 5   pinky: 3 X: 356.96  Y: 11.38  Z: 346.01
r_side 0   m_tip: 0   m_b: 0   m_side: 0   i_tip: 0   i_side: 0   p_side: 0thumb: 2   index: 0   middle: 4   ring: 5   pinky: 3 X: 350.30  Y: 19.71  Z: 338.56
r_side 0   m_tip: 0   m_b: 0   m_side: 0   i_tip: 0   i_side: 0   p_side: 0thumb: 2   index: 0   middle: 5   ring: 14   pinky: 16 X: 338.01  Y: 26.07  Z: 330.52
r_side 0   m_tip: 0   m_b: 0   m_side: 0   i_tip: 0   i_side: 0   p_side: 0thumb: 3   index: 0   middle: 7   ring: 18   pinky: 19 X: 331.57  Y: 30.08  Z: 332.37
r_side 0   m_tip: 0   m_b: 0   m_side: 0   i_tip: 0   i_side: 0   p_side: 0thumb: 3   index: 0   middle: 9   ring: 18   pinky: 19 X: 327.09  Y: 35.49  Z: 331.43
r_side 0   m_tip: 0   m_b: 0   m_side: 0   i_tip: 0   i_side: 0   p_side: 0thumb: 3   index: 0   middle: 9   ring: 18   pinky: 18 X: 324.24  Y: 36.82  Z: 327.66
r_side 0   m_tip: 0   m_b: 0   m_side: 0   i_tip: 0   i_side: 0   p_side: 0thumb: 3   index: 0   middle: 9   ring: 18   pinky: 18 X: 323.57  Y: 36.74  Z: 325.70
r_side 0   m_tip: 0   m_b: 0   m_side: 0   i_tip: 0   i_side: 0   p_side: 0thumb: 3   index: 0   middle: 8   ring: 18   pinky: 17 X: 321.99  Y: 37.75  Z: 323.30
r_side 0   m_tip: 0   m_b: 0   m_side: 0   i_tip: 0   i_side: 0   p_side: 0thumb: 4   index: 0   middle: 7   ring: 17   pinky: 18 X: 322.35  Y: 37.28  Z: 322.84
r_side 0   m_tip: 0   m_b: 0   m_side: 0   i_tip: 0   i_side: 0   p_side: 0thumb: 4   index: 0   middle: 7   ring: 17   pinky: 17 X: 322.87  Y: 36.75  Z: 322.43
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
