juanmrq95/ee149_104/final_versions/letters_SM_all_letters_and_macros/letters_SM_all_letters_and_macros.ino

#include <Wire.h>

#include <FreeSixIMU.h>
#include <FIMU_ADXL345.h>
#include <FIMU_ITG3200.h>

float angles[3]; // yaw pitch roll
int classify = 0;
String ltr = "Fhfgh";

//char[32] lcd_buffer;
//char *lcd_screen;



/////////////////////
// Glove constants //
/////////////////////

// Set the FreeSixIMU object
FreeSixIMU sixDOF = FreeSixIMU();


// Sensor Data
int ring_side = 8;
int middle_tip = 13;
int middle_b = 9;
int middle_side = 10;
int index_tip = 11;
int index_side = 17;
int pinky_side = 12;
const int thumb = A2;
const int index = A1;
const int middle = A0;
const int ring = A6;
const int pinky = A7;


int thumb_value = 0;
int index_value = 0;
int middle_value = 0;
int ring_value = 0;
int pinky_value = 0;


const int thumbBias = 260;
const int thumb_a = 8;

const int indexBias = 200;
const int index_a = 8;

const int middleBias = 200;
const int middle_a = 10.5;

const int ringBias = 200;
const int ring_a = 11.5;

const int pinkyBias = 410;
const int pinky_a = 10;

////////////////////////////////////
//Feedback variable initialization//
////////////////////////////////////

float data[12];
float prev_data[12];

//////////////////////////////
//Glove State Initialization//
//////////////////////////////
 
typedef enum{
  INITIAL,
  CLASSIFY_MOVING, 
  CLASSIFY,
  CLASSIFY_PRINT,
  CLASSIFY_WAIT,
  EDIT,  
  EDIT_MOVING,
  EDIT_CLASSIFY,
  EDIT_EXECUTE,
  EDIT_WAIT
  
} gloveState;

/////////////////////
//Feedback Function//
/////////////////////

void update_data(void)
{
  for(int i = 0; i < 12; i++)
  {
    prev_data[i] = data[i];
  }
}

////////////////////////////////////
//Flex sensor Calibration Function//
////////////////////////////////////

float getVoltage(int pin)
{
  // This function has one input parameter, the analog pin number
  // to read. You might notice that this function does not have
  // "void" in front of it; this is because it returns a floating-
  // point value, which is the true voltage on that pin (0 to 5V).

  // Here's the return statement for this function. We're doing
  // all the math we need to do within this statement:
  return (analogRead(pin));
 
}

void calibrate(void)
{
  update_data();

  thumb_value = (getVoltage(thumb) - thumbBias)/thumb_a;
  index_value = (getVoltage(index) - indexBias)/index_a;
  middle_value = (getVoltage(middle) - middleBias)/middle_a;
  ring_value = (getVoltage(ring) - ringBias)/ring_a;
  pinky_value = (getVoltage(pinky) - pinkyBias)/pinky_a;

  
/* *Note* getAngles function should not be in calibration but in classify state since state transition depends only on flex movement */
  sixDOF.getAngles(angles);


// Feedback array *Note* Not sure if this should have its own function; might be helpful
  data[0] = digitalRead(ring_side);
  data[1] = digitalRead(middle_tip);
  data[2] = digitalRead(middle_b);
  data[3] = digitalRead(middle_side);
  data[4] = digitalRead(index_tip);
  data[5] = digitalRead(index_side);
  data[6] = digitalRead(pinky_side);
  data[7] = thumb_value;
  data[8] = index_value;
  data[9] = middle_value;
  data[10] = ring_value;
  data[11] = pinky_value;
}



int array_equal(void)
{
  if((data[0] == prev_data[0])
  && (data[1] == prev_data[1])
  && (data[2] == prev_data[2])
  && (data[3] == prev_data[3])
  && (data[4] == prev_data[4])
  && (data[5] == prev_data[5])
  && (data[6] == prev_data[6])
  && (data[7] >= prev_data[7] - 2 && data[7] <= prev_data[7] + 2)
  && (data[8] >= prev_data[8] - 2 && data[8] <= prev_data[8] + 2)
  && (data[9] >= prev_data[9] - 2 && data[9] <= prev_data[9] + 2) 
  && (data[10] >= prev_data[10] - 2 && data[10] <= prev_data[10] + 2)
  && (data[11] >= prev_data[11] - 2 && data[11] <= prev_data[11] + 2))
  {
    return 1;
  }
  else
  {
    return 0;
  }
}


int check_movement(void)
{
  if (array_equal() == 1)
  {
    return 1;
  }
  else
  {
    return 0;
  }
}

void edit_classify()
{
if (
     data[0] == 1  // ring_side 
  && data[1] == 0  // middle_tip
  && data[2] == 0  // middle_b
  && data[3] == 0  // middle_side 
  && data[4] == 0  // index_tip
  && data[5] == 0  // index_side
  && data[6] == 0  // pinky_side
  && (11 <= data[7] && data[7] <= 18)  // thumb
  && (0 <= data[8] && data[8] <= 3)  // index
  && (0 <= data[9] && data[9] <= 3)  // middle
  && (14 <= data[10] && data[10] <= 19) // ring
  && (12 <= data[11] && data[11] <= 16) // pinky
  )
  {
    ltr = "22222222222222222222222222222";
    classify = 1;   
  } else if (
     data[0] == 0  // ring_side 
  && data[1] == 0  // middle_tip
  && data[2] == 0  // middle_b
  && data[3] == 0  // middle_side 
  && data[4] == 0  // index_tip
  && data[5] == 0  // index_side
  && data[6] == 0  // pinky_side
  && (11 <= data[7] && data[7] <= 18)  // thumb
  && (0 <= data[8] && data[8] <= 3)  // index
  && (0 <= data[9] && data[9] <= 3)  // middle
  && (0 <= data[10] && data[10] <= 5) // ring
  && (12 <= data[11] && data[11] <= 19) // pinky
  )
  {
    ltr = "33333333333333333333333333333";
    classify = 1;   
  } else if (
     data[0] == 0  // ring_side 
  && data[1] == 0  // middle_tip
  && data[3] == 0  // middle_side 
  && data[4] == 0  // index_tip
  && data[5] == 0  // index_side
  && data[6] == 0  // pinky_side
  && (11 <= data[7] && data[7] <= 18)  // thumb
  && (0 <= data[8] && data[8] <= 4)  // index
  && (15 <= data[9] && data[9] <= 25)  // middle
  && (15 <= data[10] && data[10] <= 25) // ring
  && (15 <= data[11] && data[11] <= 25) // pinky
  )
  {
    ltr = "1111111111111111111111111111";
    classify = 1;   
  }else if (
     data[0] == 0  // ring_side 
  && data[1] == 0  // middle_tip
  && data[3] == 0  // middle_side 
  && data[4] == 0  // index_tip
  && data[5] == 0  // index_side
  && data[6] == 0  // pinky_side
  && (15 <= data[7] && data[7] <= 25)  // thumb
  && (0 <= data[8] && data[8] <= 7)  // index
  && (0 <= data[9] && data[9] <= 7)  // middle
  && (0 <= data[10] && data[10] <= 7) // ring
  && (0 <= data[11] && data[11] <= 7) // pinky
  )
  {
    ltr = "4444444444444444444444444";
    classify = 1;   
  } else if (
     data[0] == 0  // ring_side 
  && data[1] == 0  // middle_tip
  && data[2] == 0  // middle_b
  && data[3] == 0  // middle_side 
  && data[4] == 0  // index_tip
  && data[5] == 0  // index_side
  && data[6] == 0  // pinky_side
  && (0 <= data[7] && data[7] <= 8)  // thumb
  && (0 <= data[8] && data[8] <= 5)  // index
  && (0 <= data[9] && data[9] <= 5)  // middle
  && (12 <= data[10] && data[10] <= 18) // ring
  && (0 <= data[11] && data[11] <= 5) // pinky
  )
  {
    ltr = "EXIT EDITTTTTTTTTTTTTTTTTTTTTTT";
    classify = 1;   
  }
  else
  {
   Serial.println("Edit CLassifier FAILED to match Gesture");
   ltr = "Failed to match letter";
   classify = 1;
  }
  //classify = 1;
  
}

void classifier()
{
   // A
  if (
     data[0] == 0  // ring_side 
  && data[1] == 0  // middle_tip
  //&& data[2] == 0  // middle_b
  && data[3] == 0  // middle_side 
  && data[4] == 0  // index_tip
  && data[5] == 1  // index_side
  && data[6] == 0  // pinky_side
  && (10 <= data[7] && data[7] <= 19)  // thumb
  && (15 <= data[8] && data[8] <= 25)  // index
  && (15 <= data[9] && data[9] <= 25)  // middle
  && (15 <= data[10] && data[10] <= 25) // ring
  && (13 <= data[11] && data[11] <= 25) // pinky
  )
  {
    ltr = "AAAAAAAAAAAAAAAAAAAAAAAA";
    classify = 1;   
  } else if (
     data[0] == 0  // ring_side 
  && data[1] == 0  // middle_tip
  && data[3] == 0  // middle_side 
  && data[4] == 0  // index_tip
  && data[5] == 0  // index_side
  && data[6] == 0  // pinky_side
  && (15 <= data[7] && data[7] <= 25)  // thumb
  && (0 <= data[8] && data[8] <= 7)  // index
  && (0 <= data[9] && data[9] <= 7)  // middle
  && (0 <= data[10] && data[10] <= 7) // ring
  && (0 <= data[11] && data[11] <= 7) // pinky
  )
  {
    ltr = "BBBBBBBBBBBBBBBBBBBBBBBB";
    classify = 1;   
  } else if (
     data[0] == 0  // ring_side 
  && data[1] == 0  // middle_tip
  && data[3] == 0  // middle_side 
  && data[4] == 0  // index_tip
  && data[5] == 0  // index_side
  && data[6] == 0  // pinky_side
  && (11 <= data[7] && data[7] <= 18)  // thumb
  && (15 <= data[8] && data[8] <= 18)  // index
  && (13 <= data[9] && data[9] <= 18)  // middle
  && (13 <= data[10] && data[10] <= 18) // ring
  && (7 <= data[11] && data[11] <= 13) // pinky
  )
  {
    ltr = "CCCCCCCCCCCCCCCCCCCCCCCC";
    classify = 1;   
 
  } else if (
     data[0] == 0  // ring_side 
  && data[1] == 1  // middle_tip
  && data[2] == 0  // middle_b
  && data[3] == 0  // middle_side 
  && data[4] == 0  // index_tip
  && data[5] == 0  // index_side
  && data[6] == 0  // pinky_side
  && (7 <= data[7] && data[7] <= 18)  // thumb
  && (0 <= data[8] && data[8] <= 5)  // index
  && (10 <= data[9] && data[9] <= 15)  // middle
  && (10 <= data[10] && data[10] <= 16) // ring
  && (7 <= data[11] && data[11] <= 15) // pinky
  )
  {
    ltr = "DDDDDDDDDDDDDDDDDDDDDD";
    classify = 1;   
  } else if (
     data[0] == 0  // ring_side 
  && data[1] == 0  // middle_tip
  && data[2] == 0  // middle_b
  && data[3] == 0  // middle_side 
  && data[4] == 0  // index_tip
  && data[5] == 0  // index_side
  && data[6] == 0  // pinky_side
  && (20 <= data[7] && data[7] <= 25)  // thumb
  && (16 <= data[8] && data[8] <= 25)  // index
  && (16 <= data[9] && data[9] <= 25)  // middle
  && (16 <= data[10] && data[10] <= 25) // ring
  && (16 <= data[11] && data[11] <= 25) // pinky
  )
  {
    ltr = "EEEEEEEEEEEEEEEEEEEEE";
    classify = 1;   
  
  } else if (
     data[0] == 0  // ring_side 
  && data[1] == 0  // middle_tip
  && data[2] == 0  // middle_b
  && data[4] == 1  // index_tip
  && data[5] == 0  // index_side
  && data[6] == 0  // pinky_side
  && (11 <= data[7] && data[7] <= 22)  // thumb
  && (13 <= data[8] && data[8] <= 17)  // index
  && (0 <= data[9] && data[9] <= 6)  // middle
  && (0 <= data[10] && data[10] <= 6) // ring
  && (0 <= data[11] && data[11] <= 6) // pinky
  )
  {
    ltr = "FFFFFFFFFFFFFFFFFFF";
    classify = 1;   
  } else if (
     data[0] == 0  // ring_side 
  && data[1] == 0  // middle_tip
  && data[3] == 0  // middle_side 
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
  && (0 <= data[8] && data[8] <= 5)  // index
  && (0 <= data[9] && data[9] <= 5)  // middle
  && (12 <= data[10] && data[10] <= 18) // ring
  && (0 <= data[11] && data[11] <= 5) // pinky
  )
  {
    ltr = "ENTER EDITTTTTTTTTTTTTTTTTTTTTTT";
    classify = 1;   
  }
  else
  {
   Serial.println("kjhkjhjkgjkgjkgkkjhgkj");
   ltr = "Failed to match letter";
   classify = 0;
  }
  //classify = 1;
  
}

void setup()
{
  //Serial USB setup
  
  Serial.begin(9600);

  //GPIO pin initialization
  pinMode(ring_side, INPUT);
  pinMode(middle_tip, INPUT);
  pinMode(middle_b, INPUT);
  pinMode(middle_side, INPUT);
  pinMode(index_tip, INPUT);
  pinMode(index_side, INPUT);
  pinMode(pinky_side, INPUT);
  //I2C pins setup
  
  Wire.begin();
  
  //Accelerometer and Gyroscope Setup
  
  delay(5);
  sixDOF.init(); //begin the IMU
  delay(5); 

}



void loop()
{

  //Code to check if check movement function and feedback works
  
  static gloveState state = INITIAL;
  static int edit = 0;

 if(state == INITIAL && check_movement()){
    state = INITIAL;
  }
   
 if(state == INITIAL && !check_movement()){
    state = CLASSIFY_MOVING;
  }

  else if(state == CLASSIFY_MOVING && check_movement()){
    state = CLASSIFY;
  }
  
  else if(state == CLASSIFY_MOVING && !check_movement()){
    state = CLASSIFY_MOVING;
  }
  
  else if(state == CLASSIFY && classify == 1 && check_movement()){
    state = CLASSIFY_PRINT;
  }
  
  else if(state == CLASSIFY && classify == 0 && check_movement()){
    state = CLASSIFY_MOVING;
  }
  
  else if(state == CLASSIFY && classify == 1 && !check_movement()){
    state = CLASSIFY_PRINT;
  }
  
  else if(state == CLASSIFY && classify == 0 && !check_movement()){
    state = CLASSIFY_MOVING;
  }

  else if(state == CLASSIFY && classify == 2 && check_movement()){
    state = EDIT;
  }

  else if(state == CLASSIFY && classify == 2 && !check_movement()){
    state = EDIT;
  }
  
  else if(state == CLASSIFY_PRINT){
    state = CLASSIFY_WAIT;
  }
  
  else if(state == CLASSIFY_WAIT && check_movement()){
    state = CLASSIFY_WAIT;
  }
  
  else if(state == CLASSIFY_WAIT && !check_movement()){
    state = CLASSIFY_MOVING;
  }

  else if(state == EDIT && check_movement()){
    state = EDIT_MOVING;
  }

  else if(state == EDIT && !check_movement()){
    state = EDIT_MOVING;
  }

  else if(state == EDIT_MOVING && check_movement()){
    state = EDIT_CLASSIFY;
  }

  else if(state == EDIT_CLASSIFY && edit == 1 && check_movement()){
    state = EDIT_EXECUTE;
  }
  
  else if(state == EDIT_CLASSIFY && edit == 0 && check_movement()){
    state = EDIT_MOVING;
  }

  else if(state == EDIT_CLASSIFY && edit == 2 && check_movement()){
    state = CLASSIFY_MOVING;
  }
  
  else if(state == EDIT_MOVING && !check_movement()){
    state = EDIT_MOVING;
  }  

  else if(state == EDIT_EXECUTE){
    state = EDIT_WAIT;
  }  

  else if(state == EDIT_WAIT && check_movement()){
    state = EDIT_WAIT;
  }

  else if(state == EDIT_WAIT && !check_movement()){
    state = EDIT_MOVING;
  }
  
  switch (state){
    case INITIAL:

      calibrate();
      break;


    case CLASSIFY_MOVING:
      Serial.print("moving:   ");
      Serial.print("ring: ");
      Serial.print(data[0]);
      Serial.print("  m_tip: ");
      Serial.print(data[1]);
      Serial.print("  m_b: ");
      Serial.print(data[2]);
      Serial.print("  m_side: ");
      Serial.print(data[3]);
      Serial.print("  i_tip: ");
      Serial.print(data[4]);
      Serial.print("  i_side: ");
      Serial.print(data[5]);
      Serial.print("  p_side: ");
      Serial.print(data[6]);
      Serial.print("  thumb: ");
      Serial.print(data[7]);
      Serial.print("  index: ");
      Serial.print(data[8]);
      Serial.print("  midd: ");
      Serial.print(data[9]);
      Serial.print("  ring: ");
      Serial.print(data[10]);
      Serial.print("  pink: ");
      Serial.println(data[11]);
      Serial.println(); 
      calibrate();    
      break;

    case CLASSIFY_WAIT:
      classify = 0;
      Serial.print("wait:   ");
      Serial.print("ring: ");
      Serial.print(data[0]);
      Serial.print("  m_tip: ");
      Serial.print(data[1]);
      Serial.print("  m_b: ");
      Serial.print(data[2]);
      Serial.print("  m_side: ");
      Serial.print(data[3]);
      Serial.print("  i_tip: ");
      Serial.print(data[4]);
      Serial.print("  i_side: ");
      Serial.print(data[5]);
      Serial.print("  p_side: ");
      Serial.print(data[6]);
      Serial.print("  thumb: ");
      Serial.print(data[7]);
      Serial.print("  index: ");
      Serial.print(data[8]);
      Serial.print("  midd: ");
      Serial.print(data[9]);
      Serial.print("  ring: ");
      Serial.print(data[10]);
      Serial.print("  pink: ");
      Serial.println(data[11]);
      Serial.println();
      calibrate();
      break;
            
    case EDIT_CLASSIFY: 
      break; 
    case CLASSIFY:
//     if(data[3] == 2){
//      classify = 2;
//      edit = 2;
//     }
//     else
//     {
      //classify = 1;
        //edit = 1;
//     }
      Serial.print("classify ");
      Serial.println(state);

      classifier();
      calibrate();
      break;

    case CLASSIFY_PRINT:
      Serial.println();
      Serial.print("classify print:    ");
      Serial.print("ring: ");
      Serial.print(data[0]);
      Serial.print("  m_tip: ");
      Serial.print(data[1]);
      Serial.print("  m_b: ");
      Serial.print(data[2]);
      Serial.print("  m_side: ");
      Serial.print(data[3]);
      Serial.print("  i_tip: ");
      Serial.print(data[4]);
      Serial.print("  i_side: ");
      Serial.print(data[5]);
      Serial.print("  p_side: ");
      Serial.print(data[6]);
      Serial.print("  thumb: ");
      Serial.print(data[7]);
      Serial.print("  index: ");
      Serial.print(data[8]);
      Serial.print("  midd: ");
      Serial.print(data[9]);
      Serial.print("  ring: ");
      Serial.print(data[10]);
      Serial.print("  pink: ");
      Serial.println(data[11]);

      
      Serial.print(" letter: ");
      Serial.println(ltr);
      Serial.print(" asdasdasd");
      Serial.println();
      Serial.println();
      Serial.println();

      break;

    case EDIT:
      break;
    case EDIT_MOVING:
      break;
  
    case EDIT_EXECUTE:
      break;
    case EDIT_WAIT:
      calibrate();
      Serial.print("edit wait: ");
      Serial.println(state);
      break;

    default:
      calibrate();
      break;
  }
  // To send data from the Arduino to the serial monitor window,
  // we use the Serial.print() function.


  // Note that the above statement uses "println", which will insert
  // a "carriage return" character at the end of whatever it prints,
  // moving down to the NEXT line.


  
  delay(250); // repeat once per second (change as you wish!)
}
