juanmrq95/ee149_104/ASLsensing/flexCalibration/flex/flex.ino

/*
/////////////////
/// ASL glove ///
/////////////////
  Use the "serial monitor" window to display ASL letters.
   
  This script will use the Arduino's serial port
  to send data back to your main computer. 
  
*/

// Global Declarations.

const int thumb_flex = 0;
const int index_flex = 1;
const int middle_flex = 2;
const int ring_flex = 3;
const int pinky_flex = 4;


const int thumbBias = 480;
const int thumb_a = 40;

const int indexBias = 480;
const int index_a = 40;

const int middleBias = 480;
const int middle_a = 40;

int thumb_value = 0;
int index_value = 0;
int middle_value = 0;
int ring_value = 0;
int pinky_value = 0;
int mid_touch = 0;
int index_touch = 0;

//int val = 0;

int inPin = 8;     // pushbutton connected to digital pin 7
int inPin_two = 2;
int inPin_three = 3;

//Defining State variables 
typedef enum{
  INITIAL,
  MOVING, 
  REST
} gloveState;

void setup()
{  
  // The speed is measured in bits per second, also known as
  // "baud rate". 9600 is a very commonly used baud rate,
  // and will transfer about 10 characters per second.
  
  Serial.begin(9600);
  pinMode(inPin, INPUT);
  pinMode(inPin_two, INPUT);
  pinMode(inPin_three, INPUT);
  
  thumb_value = 0;
  index_value = 0;
  middle_value = 0;
  ring_value = 0;
  pinky_value = 0;
  
  mid_touch = 0;
  index_touch = 0;
  
}


void loop()
{
  
  gloveState state;

  float thumb_flex_voltage;
  float index_flex_voltage;
  float middle_flex_voltage;
  float ring_flex_voltage;
  float pinky_flex_voltage;


  float thumb_flex_prev;
  float index_flex_prev;
  float middle_flex_prev;
  //float ring_flex_prev;
  //float pinky_flex_prev;

  float thumb_flex_roc;
  float index_flex_roc;
  float middle_flex_roc;
  //float ring_flex_roc;
  //float pinky_flex_roc;

  thumb_flex_prev = thumb_value ;
  index_flex_prev = index_value ;
  middle_flex_prev = middle_value ;
 //ring_flex_prev = ring_value ;
 //pinky_flex_prev = pinky_value ;

  thumb_flex_voltage = getVoltage(thumb_flex);
  index_flex_voltage = getVoltage(index_flex);
  middle_flex_voltage = getVoltage(middle_flex);
  
  
  mid_touch = digitalRead(inPin_three);//getVoltage(3);
  index_touch = digitalRead(inPin_two);//getVoltage(3)//getVoltage(4);
  /*
  if(mid_touch > 1000){
    mid_touch = 1;
  } else {
    mid_touch = 0;
  }
    if(index_touch > 1000){
    index_touch = 1;
  } else {
    index_touch = 0;
  } 
*/
  thumb_value = (thumb_flex_voltage - thumbBias)/thumb_a;
  index_value = (index_flex_voltage - indexBias)/index_a;
  middle_value = (middle_flex_voltage - middleBias)/middle_a;

  thumb_flex_roc = thumb_flex_prev - thumb_value;
  index_flex_roc = index_flex_prev - index_value;
  middle_flex_roc = middle_flex_prev - middle_value;

  // To send data from the Arduino to the serial monitor window,
  // we use the Serial.print() function. 

  //Serial.println(thumb_flex_voltage);
  Serial.print("thumb: ");
  Serial.print(thumb_value);
  Serial.print("    index: ");
  Serial.print(index_value);
  Serial.print("    midlle: ");
  Serial.print(middle_value);

  Serial.print("    mid_touch: ");
  Serial.print(mid_touch);


  Serial.print("    index_touch: ");
  Serial.println(index_touch);

  if(state == INITIAL){
    state = MOVING;
  }

  else if((state == MOVING) && (thumb_flex_roc == 0 && index_flex_roc == 0 
    && middle_flex_roc == 0 /*&& ring_flex_roc == 0 && pinky_flex_roc == 0*/)){
    state = REST;
  }

  else {
    state = MOVING;
  }


  switch (state){

    case INITIAL:
    case MOVING:
        thumb_flex_voltage = getVoltage(thumb_flex);
        index_flex_voltage = getVoltage(index_flex);
        middle_flex_voltage = getVoltage(middle_flex);
        mid_touch = digitalRead(inPin_three);//getVoltage(3);
        index_touch = digitalRead(inPin_two);//getVoltage(3)//getVoltage(4);
          
        thumb_value = (thumb_flex_voltage - thumbBias)/thumb_a;
        index_value = (index_flex_voltage - indexBias)/index_a;
        middle_value = (middle_flex_voltage - middleBias)/middle_a;

        thumb_flex_roc = thumb_flex_prev - thumb_value;
        index_flex_roc = index_flex_prev - index_value;
        middle_flex_roc = middle_flex_prev - middle_value;
        
        break;
            
     case REST: /// Classify
          if(middle_value == 0){
            if(index_value == 0-1) {
              if(thumb_value == 0){
                Serial.println("invalid");
              } else if (thumb_value >= 1){
                Serial.println("BBBBBBBB");
                while(middle_value == 0 && index_value == 0-1 && thumb_value >= 1)
                {
                    thumb_flex_voltage = getVoltage(thumb_flex);
                    index_flex_voltage = getVoltage(index_flex);
                    middle_flex_voltage = getVoltage(middle_flex);
                    mid_touch = digitalRead(inPin_three);//getVoltage(3);
                    index_touch = digitalRead(inPin_two);//getVoltage(3)//getVoltage(4);
                            
                    thumb_value = (thumb_flex_voltage - thumbBias)/thumb_a;
                    index_value = (index_flex_voltage - indexBias)/index_a;
                    middle_value = (middle_flex_voltage - middleBias)/middle_a;
                }
              }
            }
          } else if(middle_value == 1){
              if(index_value == 0-2){
                if(thumb_value == 2){
                  if(mid_touch == 1){
                    Serial.println("DDDDDD");
                    
                    while(middle_value == 1 
                    && index_value == 0-2 
                    && thumb_value == 2 
                    && mid_touch == 1)
                    {
                        thumb_flex_voltage = getVoltage(thumb_flex);
                        index_flex_voltage = getVoltage(index_flex);
                        middle_flex_voltage = getVoltage(middle_flex);
                        mid_touch = digitalRead(inPin_three);//getVoltage(3);
                        index_touch = digitalRead(inPin_two);//getVoltage(3)//getVoltage(4);
                      
                        thumb_value = (thumb_flex_voltage - thumbBias)/thumb_a;
                        index_value = (index_flex_voltage - indexBias)/index_a;
                        middle_value = (middle_flex_voltage - middleBias)/middle_a;
                    }
                  }
                }
              } else if(index_value == 2-1) {
                if(thumb_value == 0){
                  Serial.println("invalid");
              } else if (thumb_value >= 1){
                  Serial.println("CCCCC");
                    while(index_value == 2-1 
                    && thumb_value >= 1)
                    {
                      thumb_flex_voltage = getVoltage(thumb_flex);
                      index_flex_voltage = getVoltage(index_flex);
                      middle_flex_voltage = getVoltage(middle_flex);
                      mid_touch = digitalRead(inPin_three);//getVoltage(3);
                      index_touch = digitalRead(inPin_two);//getVoltage(3)//getVoltage(4);
                    
                      thumb_value = (thumb_flex_voltage - thumbBias)/thumb_a;
                      index_value = (index_flex_voltage - indexBias)/index_a;
                      middle_value = (middle_flex_voltage - middleBias)/middle_a;
                    }   
              }
            }
          } else if(middle_value >= 2){
              if(index_value == 3-1) {
                if(thumb_value == 0){
                  Serial.println("AAAA");
                  while(index_value == 3-1 
                  && thumb_value == 0
                  && middle_value >= 2)
                   {
                      thumb_flex_voltage = getVoltage(thumb_flex);
                      index_flex_voltage = getVoltage(index_flex);
                      middle_flex_voltage = getVoltage(middle_flex);
                      mid_touch = digitalRead(inPin_three);//getVoltage(3);
                      index_touch = digitalRead(inPin_two);//getVoltage(3)//getVoltage(4);
                      thumb_value = (thumb_flex_voltage - thumbBias)/thumb_a;
                      index_value = (index_flex_voltage - indexBias)/index_a;
                      middle_value = (middle_flex_voltage - middleBias)/middle_a;
                   }
        
                  
              } else if (thumb_value >= 1){
                  Serial.println("invalid");
              }
            }
          }
            break;
            
          default:
            break;
      
  // Note that the above statement uses "println", which will insert 
  // a "carriage return" character at the end of whatever it prints, 
  // moving down to the NEXT line.
   
 
  //delay(100); // repeat once per second (change as you wish!)
  }
  delay(1000);
}


float getVoltage(int pin)
{
  // Here's the return statement for this function. We're doing
  // all the math we need to do within this statement:
  return (analogRead(pin));
}
